benconnor1972/BODAQS/docs/analysis/contracts/BODAQS_Session_Filter_Contract_v0_draft.md

# BODAQS Session Filter Contract v0 Draft

**Status:** Draft  
**Scope:** Persisted reusable filters for selecting candidate sessions from a
BODAQS libraries root  
**Audience:** BODAQS web application, Library API service, notebook/library
adapter implementers

---

## 1. Purpose

A persisted session filter is a named reusable helper for finding candidate
sessions. It describes a predicate over session catalog fields, signal metadata,
and later derived summaries or API-backed indexes.

Persisted filters are **not** Study Set definitions. Applying a filter changes
which sessions are visible or selectable. Adding sessions to a Study Set still
writes explicit session references.

Persisted filters are also not `bodaqs.scenario` definitions. A Scenario finds
meaningful occurrences, called Episodes, within sessions using time- or
distance-domain criteria. A session filter may define the candidate scope for
a Scenario evaluation, but it does not carry Episode criteria or results.

Ad-hoc table filters are also outside this contract. They are transient UI state
owned by the Session Selector table headers. They may combine with persisted
filters during browsing, but they are not saved as `bodaqs.session_filter`
objects unless the user explicitly saves or copies them into a persisted filter.

---

## 2. Resource Scope

Persisted filters are root-level application objects.

Canonical location:

```text
<libraries_root>/
  session_filters/
    <filter_id>.json
```

Filters are scoped to the configured libraries root, not to an individual
processed library. A filter may optionally restrict its own applicability through
`scope`, but the file still lives at the root.

---

## 3. Filter Object

Example:

```json
{
  "schema": "bodaqs.session_filter",
  "version": 1,
  "filter_id": "ben-rides-with-usable-gps",
  "revision": 2,
  "display_name": "Ben rides with usable GPS",
  "description": "Reusable helper for GPS comparison sessions.",
  "category": "gps",
  "scope": {
    "library_ids": ["default-library"]
  },
  "predicate": {
    "op": "and",
    "children": [
      {
        "field": "rider",
        "op": "contains",
        "value": "ben"
      },
      {
        "field": "gps.quality",
        "op": "eq",
        "value": "usable"
      }
    ]
  },
  "provenance": {
    "created_at": "2026-06-02T00:00:00Z",
    "created_by": "user",
    "updated_at": "2026-06-02T00:12:00Z"
  },
  "display_state": {
    "bodaqs_web_v1": {}
  }
}
```

Validation notes:

- `schema` must be `bodaqs.session_filter`.
- `version` must be supported by the service.
- `filter_id` must be filename-safe and unique within the libraries root.
- `revision` is assigned by the service and must increment on successful write.
- `display_name` should be short enough for chips and filter-list rows.
- `category` is optional display grouping metadata for UIs. Missing category
  means `custom`.
- `predicate` is required.
- `scope` is optional. Missing scope means the filter can be evaluated against
  all libraries under the active libraries root.
- `display_state` is optional and non-authoritative.

---

## 4. Predicate Model

Predicates are recursive. Group predicates combine child predicates. Leaf
predicates compare one field against one value or set of values.

Group predicate:

```json
{
  "op": "and",
  "children": []
}
```

Recommended group operators:

```text
and | or
```

Leaf predicate:

```json
{
  "field": "gps.quality",
  "op": "eq",
  "value": "usable"
}
```

Recommended leaf operators:

```text
eq | in | contains | present
```

Operator semantics:

- `eq`: field value equals `value` after normalisation appropriate to the field.
- `in`: field value equals any item in `value`.
- `contains`: text or list field contains `value`.
- `present`: field has a non-empty value, or equals the boolean `value` if one
  is supplied.

The service and browser should treat unknown fields/operators as invalid for
saved objects. Future versions may add numeric comparison, date/time comparison,
trackpoint-match predicates, and signal-content predicates.

---

## 5. Initial Field Names

Initial catalog-backed fields:

```text
bike
event.schema
firmware
gps.present
gps.quality
gps.source
note.status
preprocessing.profile
qc.level
rider
signals
source.archive
```

Field notes:

- `note.status` uses `missing | draft | edited`.
- `qc.level` uses `ok | warning | alert`.
- `gps.quality` uses `absent | limited | usable | invalid`.
- `gps.source` may match the preferred GPS source, any source kind, or source
  stream names exposed by the catalog.
- `signals` evaluates over available signal names and semantic labels.

Signal-summary predicates that classify a whole session are not part of the
initial catalog-only implementation. Conditions intended to identify
occurrences within a session belong to the Scenario and Episode contract rather
than becoming session-filter predicates.

---

## 6. API-Backed Trackpoint Predicates

Trackpoint predicates are planned API-backed filter predicates. They should not
be evaluated directly from the session catalog because they depend on a track,
track revision, geospatial policy, tolerance, GPS source identity, and matching
algorithm version.

Recommended predicate shape:

```json
{
  "field": "trackpoint.crossing",
  "op": "matches",
  "value": {
    "track_id": "munda-biddi-test-loop",
    "trackpoint_ids": ["start-gate", "rock-garden-entry"],
    "match_mode": "all",
    "tolerance_m": 5.0,
    "policy_ref": {
      "policy_id": "default-geospatial-policy"
    }
  }
}
```

Recommended `match_mode` values:

```text
any | all | min_count
```

If `match_mode` is `min_count`, `value.min_count` is required.

The browser should evaluate this predicate by creating or resuming a
`TrackpointMatchQuery` through the Library API. The API may use the filter's
own `scope`, the active selected-library scope, and/or other already-applied
catalog-backed filters to reduce candidate sessions before starting broad
geospatial matching.

The result of a trackpoint predicate is a set of matched session references. It
then participates in the active filter stack like any other saved filter. A
Study Set created from the result still stores explicit session membership; the
trackpoint predicate may appear only in Study Set provenance unless a future
explicit refresh action is added.

---

## 7. Applying Filters

The default filter stack behavior is:

```text
selected libraries
-> persisted saved-filter stack
-> ad-hoc table filters
-> search text
-> sort
```

Multiple applied persisted filters are combined with `AND` by default. Each
persisted filter may contain its own internal `and`/`or` predicate tree.

Example active stack:

```json
{
  "applied_filters": [
    { "filter_id": "ben-rides" },
    { "filter_id": "has-accelerometer" },
    { "filter_id": "has-usable-gps" }
  ],
  "combine": "and"
}
```

The active stack is UI/session state. It is not a Study Set definition. If the
user creates a Study Set after applying filters, the Study Set stores explicit
session membership. The filter stack may be recorded in Study Set provenance,
but refreshing membership from filters must be an explicit user action.

---

## 7. API Endpoints

Root-scoped session-filter CRUD:

```text
GET    /api/v1/session-filters
POST   /api/v1/session-filters
GET    /api/v1/session-filters/{filter_id}
PUT    /api/v1/session-filters/{filter_id}
DELETE /api/v1/session-filters/{filter_id}
```

Filter writes should use revision checks:

```json
{
  "expected_revision": 2,
  "session_filter": {
    "schema": "bodaqs.session_filter",
    "version": 1,
    "filter_id": "ben-rides",
    "revision": 2,
    "display_name": "Ben's rides",
    "predicate": {
      "field": "rider",
      "op": "contains",
      "value": "ben"
    }
  }
}
```

The browser may evaluate catalog-backed filters locally after loading filter
objects. API-backed evaluation can be added later for predicates requiring data
that is not present in the session catalog.

---

## 8. Implementation Sequence For Trackpoint Filters

Recommended first implementation sequence:

1. Extend the frontend filter model to recognise `trackpoint.crossing` /
   `matches` predicates.
2. Add a simple filter-builder UI for choosing track, trackpoints, `match_mode`,
   and tolerance.
3. When a trackpoint filter is applied, ask the Library API to create or resume
   a `TrackpointMatchQuery`.
4. Poll query status and apply the paged matched session refs to the visible
   session set as results arrive.
5. Cache the query id and progress in browser state so the UI can show
   "building index", "partially available", and "complete" states.
6. Keep authoring/persistence of the filter separate from execution/progress of
   any particular query job.

---

## 9. Deferred Work

Deferred beyond the first persisted-filter contract:

- full visual predicate builder
- ad-hoc table-header filtering
- saving an ad-hoc table filter as a persisted filter
- API-backed whole-session signal-summary predicates
- richer API-backed geospatial-section predicates beyond trackpoint crossings
- importing/exporting filters across libraries roots
- hosted/shared filter permissions
