benconnor1972/BODAQS/docs/analysis/contracts/BODAQS_Minimum_Signal_Registry_Semantics_v0_1_1.md

# BODAQS — Minimum Signal Registry Semantics (v0.12 draft)

This document defines the **minimum required semantics** for `session["meta"]["signals"]` so that downstream code (event detection, segment extraction, metrics, and visualization) can resolve schema “signals/roles” (e.g. `disp`, `vel`, `acc`) to concrete dataframe columns **without relying on column-name string hacks**.

It is intentionally **minimal**: it does not require full provenance graphs or transform metadata, but it *does* require enough structure to make resolution deterministic and contract-valid.

---

## 1) Scope

Applies to any analysis `Session` object that carries a `pandas.DataFrame` in `session["df"]`.

Downstream components that assume this registry:

- `detect_events_from_schema(..., meta=session["meta"])`
- `extract_segments(..., meta=session["meta"])`
- metrics and viz tooling that use SegmentBundle outputs

---

## 2) Registry shape

`session["meta"]["signals"]` MUST be a mapping:

```text
{ <df_column_name: str> : <SignalInfo: dict> }
```

Where `<df_column_name>` **must be exactly the column name** present in `session["df"].columns`.

### 2.1 Stream scope

The primary registry above has an implicit stream scope of `"primary"`.
Each materialised secondary stream has an independent registry at
`session["meta"]["secondary_streams"][<stream_name>]["signals"]`, keyed by
columns in that stream's dataframe. A selectable signal reference is therefore
the pair:

```json
{ "stream_name": "inertial_frame_imu", "column": "yaw_enu_rad" }
```

`column` alone is not a session-global identity. Consumers that cross a stream
boundary MUST retain the stream name, and MUST resolve semantics only within
the referenced stream registry.

`stream_name` describes materialisation, timebase, and product boundary. It
does **not** express whether a signal is the preferred analysis candidate.
In particular, a `primary_analysis` signal may live in any stream, including a
fused or native-rate secondary stream. Conversely, a primary-stream signal is
not automatically a primary analysis signal.

---

## 3) Required coverage

### 3.1 One entry per numeric column

For every **numeric** column in `session["df"]` (excluding timebase columns like `time_s` and other explicitly non-signal fields), there MUST be a corresponding entry in `session["meta"]["signals"]`.

### 3.2 No extraneous entries (recommended)

It is strongly recommended that the registry does not include keys that are not present in `session["df"].columns`.

---

## 4) SignalInfo minimum fields

Each `SignalInfo` MUST contain the following keys:

- `kind`: `"" | "raw" | "qc"`
  - `""` means engineered/derived default signals.
  - `"raw"` means raw sensor/ADC domain.
  - `"qc"` means quality-control / flags.

- `unit`: `str | None`
  - For `kind == ""`, **unit MUST be non-empty** (e.g. `"mm"`, `"mm/s"`, `"V"`).
  - For `kind == "raw"`, unit SHOULD be `"counts"` (or another documented raw unit).
  - For `kind == "qc"`, unit SHOULD be `None`.
  - Dimensionless derived signals (e.g. normalised displacement) MUST use unit `"1"`.

- `domain`: `str | None`
  - Optional, but **highly recommended** when the same physical quantity can describe different physical or analysis subjects.
  - It identifies what part or system the signal characterises; it does **not** identify the coordinate basis of vector components.
  - Examples: `"suspension"`, `"wheel"`, `"unsprung"`, `"frame"`, `"steering"`, `"world"`.

- `end`: `"front" | "rear" | None`
  - Optional, but **highly recommended** for front/rear bike signals.
  - Use this to distinguish front and rear suspension or wheel signals without
    relying on logger-specific sensor identifiers.

- `op_chain`: `list[str]`
  - List of analysis-side operation tokens applied to produce this column (possibly empty).
  - Examples: `["zeroed"]`, `["zeroed", "norm"]`, `["zeroed", "Butterworth_3Hz_4Order"]`, `["zeroed", "diff"]`.
  - Primary analysis motion channels should keep full provenance here rather
    than in their dataframe column names.

Residual naming note:
- Columns ending with `_op_Butterworth_<x>Hz_<y>Order_resid` are interpreted as residual outputs.
- Their registry `op_chain` should include `diff` and should not include `Butterworth_<x>Hz_<y>Order`.

### Optional but recommended keys

- `source`: `list[str]`
  - Parent column name(s) this column derives from (especially for `_op_*` or derived velocity/acceleration channels).

- `source_columns`: `list[str]`
  - Alias used by some generators for parent column names. Consumers should
    prefer `source` when both are present, but may accept either.

- `processing_role`: `str`
  - Selection intent assigned by preprocessing; it is independent of
    `stream_name`, `sensor`, and `kind`.
  - Controlled values are defined in **4.1 Analysis role and inspection
    visibility** below.
  - Use this when a session contains multiple valid semantic matches for the
    same physical quantity, such as a forward estimate and a fixed-interval
    smoothed estimate of world yaw.

- `motion_source_id`: `str`
  - Identifier of the `motion_derivation.sources[]` entry that produced this
    signal.

- `motion_profile_id`: `str`
  - Identifier of the motion-derivation profile that produced this signal.
  - The primary profile should use `"primary"`; secondary profiles should use
    their configured `id`.

- `derivation`: `dict`
  - Structured provenance describing how the signal was generated. For
    motion-derived channels this should include the source column, displacement
    low-pass settings, S-G materialized window settings, and final derivative
    low-pass settings.

- `origin`: `str`
  - Broad producer of the signal metadata or values. Current values include
    `"logger"` for signals supplied by log metadata and `"analysis"` for
    analysis-generated signals.

- `semantic_selection_excluded`: `bool`
  - When true, semantic selectors should ignore this signal even though it
    remains in the dataframe and registry for inspection.
  - This is used when `prefer_postprocessing_transformations` allows an
    analysis-generated signal to supersede a logger-originated signal with
    equivalent semantics.

- `semantic_selection_exclusion_reason`: `str`
  - Human-readable/provenance reason explaining why a signal was excluded from
    semantic selector matching.

- `inspection_visibility`: `"standard" | "advanced" | "diagnostic"`
  - Controls default interactive discovery only; it MUST NOT change semantic
    resolution or the availability of a signal explicitly requested by its
    concrete `{stream_name, column}` reference.
  - `"standard"` is intended for an ordinary Signal Inspector signal set.
    `"advanced"` is an inspectable alternative or specialist product.
    `"diagnostic"` requires an explicit user opt-in, such as a raw-evidence or
    diagnostics signal set.
  - In the absence of an explicit value, consumers SHOULD derive the default
    tier as defined in 4.1.

- `analysis_variant`: `str | None`
  - Stable, machine-readable distinction between otherwise equivalent analysis
    products. Examples include `"forward_estimate"`,
    `"fixed_interval_smoothed"`, `"filtered"`, and
    `"bias_compensated"`.
  - When two inspectable signals share the same sensor and core semantic
    fields, they SHOULD supply a distinct `analysis_variant` and/or
    `display_name`.

- `display_name`: `str | None`
  - Human-readable name for discovery and visualisation. It should distinguish
    simultaneously inspectable variants; for example, `"World yaw — smoothed"`
    and `"World yaw — forward estimate"`.

  - A vector-component name SHOULD include a frame-appropriate direction while
    retaining `quantity` and `component` as separate machine semantics:
    `sensor_native` uses `Sensor X/Y/Z`; a main-frame `body_local` or
    `bike_body` vector uses `Forward/Left/Up`; and `world_enu` uses
    `East/North/Up`. An articulated assembly's `body_local` vector uses
    `Local X/Y/Z` unless a more specific frame convention is documented.

- `sensor`: `str | None`
  - Logger/source sensor identifier, if supplied by log metadata.
  - This is not an analysis selector field. For front/rear bike-location
    matching, use `end` plus `domain`, `quantity`, and `unit`.

- `component`: `str | None`
  - Vector component represented by the column, normally `"x"`, `"y"`, or `"z"`.
  - Vector consumers should use this field rather than infer axes from column names.

- `coordinate_frame`: `str | None`
  - Coordinate basis in which a vector component is currently expressed.
  - Canonical IMU values are `"sensor_native"`, `"body_local"`, `"bike_body"`, and `"world_enu"`.
  - This describes the stored or derived values; it does not instruct firmware to perform a transform.

- `vector_group`: `str | None`
  - Sensor-local identifier tying components of one vector quantity together, such as `"accel_raw"` or `"gyro_raw"`.
  - The complete group identity is `sensor` plus `vector_group`.

- `mount_point`: `str | None`
  - Optional descriptive sensor-installation detail such as `"brake_caliper"`.
  - It is not a primary semantic selector unless a future contract explicitly promotes a controlled vocabulary.

- `notes`: `str`
  - Free text diagnostics or hints.

### 4.1 Analysis role and inspection visibility

`processing_role` ranks otherwise valid semantic candidates. It does not
describe dataframe placement, sensor priority, or whether a signal is raw.
New writers SHOULD use one of these controlled values:

| processing_role | Meaning | Default inspection tier |
|---|---|---|
| `primary_analysis` | The recommended standard analysis series for its selector context. There SHOULD be no more than one preferred candidate for a deterministic selector context. | `standard` |
| `secondary_analysis` | A valid alternative analysis series: another method, smoothing treatment, source, or interpretation that is not the normal default. | `advanced` |
| `diagnostic` | An inspectable intermediate engineering product that is not intended for ordinary semantic binding. | `diagnostic` |
| `qc_metric` | Quality/status/evidence used to assess data or processing confidence, not an ordinary engineering input. | `diagnostic` |

`kind` retains its independent meaning:

- `kind="raw"` and `kind="qc"` MUST default to `inspection_visibility="diagnostic"`
  unless a future contract explicitly establishes a justified exception.
- Raw and QC signals remain available for explicit inspection. They are not
  deleted, and their diagnostic visibility does not imply
  `semantic_selection_excluded`.
- Engineered signals without a recognised `processing_role` SHOULD default to
  `advanced`, not `standard`, so that unclassified products do not silently
  expand the normal user-facing list.

`semantic_selection_excluded` is a semantic resolver safety flag, not a UI
visibility flag. An explicitly configured engineering or diagnostic view MAY
show such a signal; automatic semantic resolution MUST continue to exclude it
unless the requesting workflow explicitly requires it.

---

## 5) Compatibility with naming spec (v0.2)

This minimum registry is compatible with the column grammar in **Signal naming & units spec (v0.2)**:

- `kind`, `domain`, `unit`, and `op_chain` should be directly parseable from the column name when the name is canonical.
- Primary motion-derived column names may intentionally omit operation tokens,
  for example `rear_wheel_disp_dom_wheel [mm]`; the registry remains the source
  of filter provenance via `op_chain` and `derivation`.
- The registry is still required even if names are canonical, because the registry is the **API surface** used by resolution logic.

---

## 6) Resolution expectations (for Option 1)

When resolving schema roles (e.g. `disp`, `vel`, `acc`) to columns, downstream code SHOULD use the registry to:

1. Filter candidates by `kind` (usually engineered `""`),
2. Filter by `unit`, `domain`, and `end` as required by the schema,
3. For vector roles, filter by `coordinate_frame`, `vector_group`, and `component` rather than parsing column names,
4. Prefer a requested `processing_role` when supplied, especially
   `"primary_analysis"` for standard metrics/event detection,
5. Prefer “cleaner” stages using `op_chain` when no explicit role is supplied
   (policy-defined ranking),
6. Fall back deterministically and emit actionable diagnostics if no match exists.

Stream scope MUST NOT be used as an implicit preference in this process. A
workflow that needs a particular stream must request it explicitly; otherwise
candidate preference comes from semantic fields, `processing_role`, and its
declared resolution policy. `inspection_visibility` affects discovery UI only
and MUST NOT alter semantic resolution.

### IMU mounting-domain convention

For bike-mounted IMUs, use these signal-level `domain` and `end` combinations:

| domain | permitted end | meaning |
|---|---|---|
| `unsprung` | `front`, `rear` | Assembly moving predominantly with the corresponding axle |
| `frame` | `front`, `rear`, `None` | Main sprung frame; end is a coarse mounting region |
| `steering` | `front` | Sprung assembly rotating about the steering axis |

Firmware raw accelerometer and gyroscope columns use `coordinate_frame=sensor_native`. The static installation transform is recorded separately as `sensor_native -> body_local`. Post-processing may materialise `body_local`, `bike_body`, or `world_enu` signals and must record that derivation without replacing the raw evidence.

This document does **not** define the ranking policy; it defines the minimum metadata required for any reasonable policy to operate.

---

## 7) Logger GPS semantics

Logger GPS route construction resolves `meta["signals"]` only. It must not
infer signal meaning from dataframe column names: `speed` and
`speed_accuracy`, or `course_over_ground` and `course_accuracy`, are distinct
registry quantities even when their logger labels are similar.

For one coherent logger GPS source, register at least:

- `position_latitude` and `position_longitude` with `domain="world"`;
- `speed` with `unit="m/s"`;
- `course_over_ground` with `unit="deg"`; and
- when yaw correction is required, QC `speed_accuracy` and `course_accuracy`
  fields with their respective units.

Use `sensor` plus a stable source-group identifier when available to keep the
position, motion, and QC fields from one receiver together. `source` remains
parent/provenance metadata and must not be used as the source-group identity.
GPS QC fields may be marked `semantic_selection_excluded` for generic signal
selection, but route construction may explicitly resolve them as required QC
evidence. Earlier BODAQS registries using `quantity="heading"` for a logger
GPS course are accepted as a migration alias only; new firmware emits
`course_over_ground`.

---

## 8) Validation checklist

A session is compliant with this minimum registry if:

- `session["meta"]["signals"]` exists and is a dict
- Every numeric df column has a registry entry keyed by the exact column name
- Every entry has keys: `kind`, `unit`, `domain`, `op_chain`
- `kind == ""` entries have a non-empty `unit`
- `op_chain` is a list (possibly empty)
- where present, `processing_role` uses a controlled value from 4.1 or a
  documented extension
- `kind="raw"` and `kind="qc"` default to diagnostic inspection visibility
  when no explicit policy is recorded
- every selectable secondary stream has a stream-local registry keyed by its
  exact dataframe columns; and
- cross-stream consumers identify a selected signal by `stream_name` and
  `column`.

---

## 9) Implementation notes

- If you have both (a) a canonical naming parser and (b) legacy “best effort” heuristics, you may build the registry in **permissive mode** early, then run a later **standardization** pass that renames legacy columns and rebuilds/validates the registry in strict mode.
- Avoid overwriting a high-fidelity registry with a “minimal” one late in the pipeline; that can silently discard semantics needed by event/segment resolution.
