benconnor1972/BODAQS/bodocs/src/assets/pics/buy-pcb-or-kit/coming-soon.png

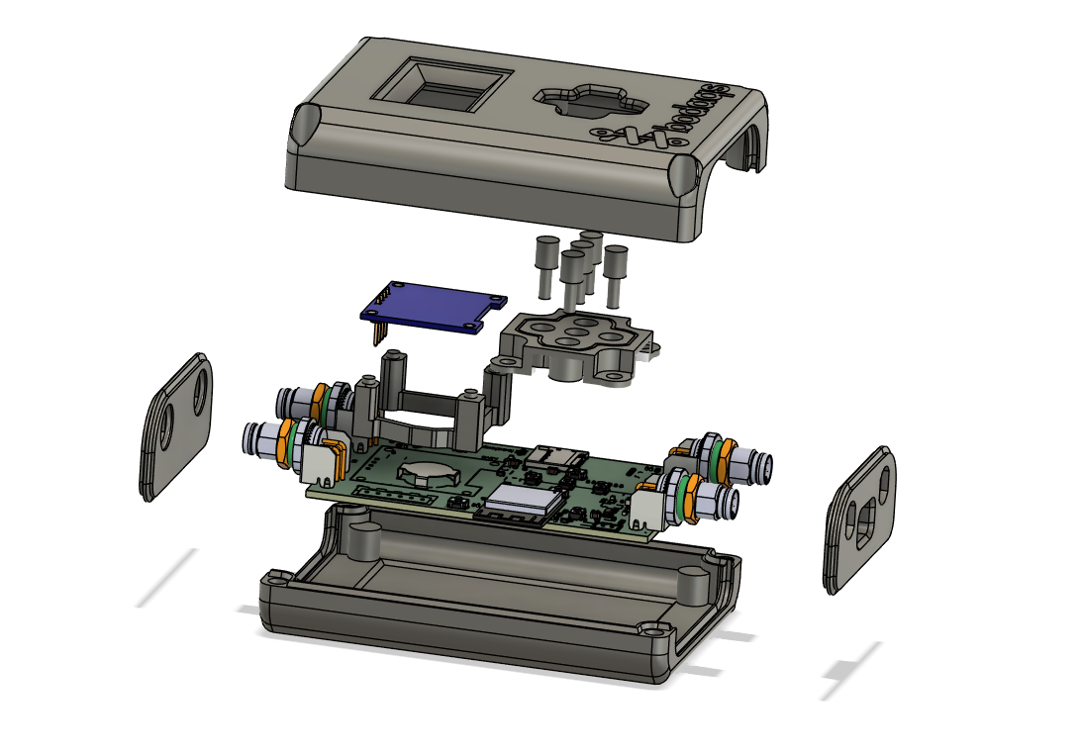
bodocs/src/assets/pics/buy-pcb-or-kit/coming-soon.png
