benconnor1972/BODAQS/bodocs/src/assets/pics/buy-pcb-or-kit/full-kit.png

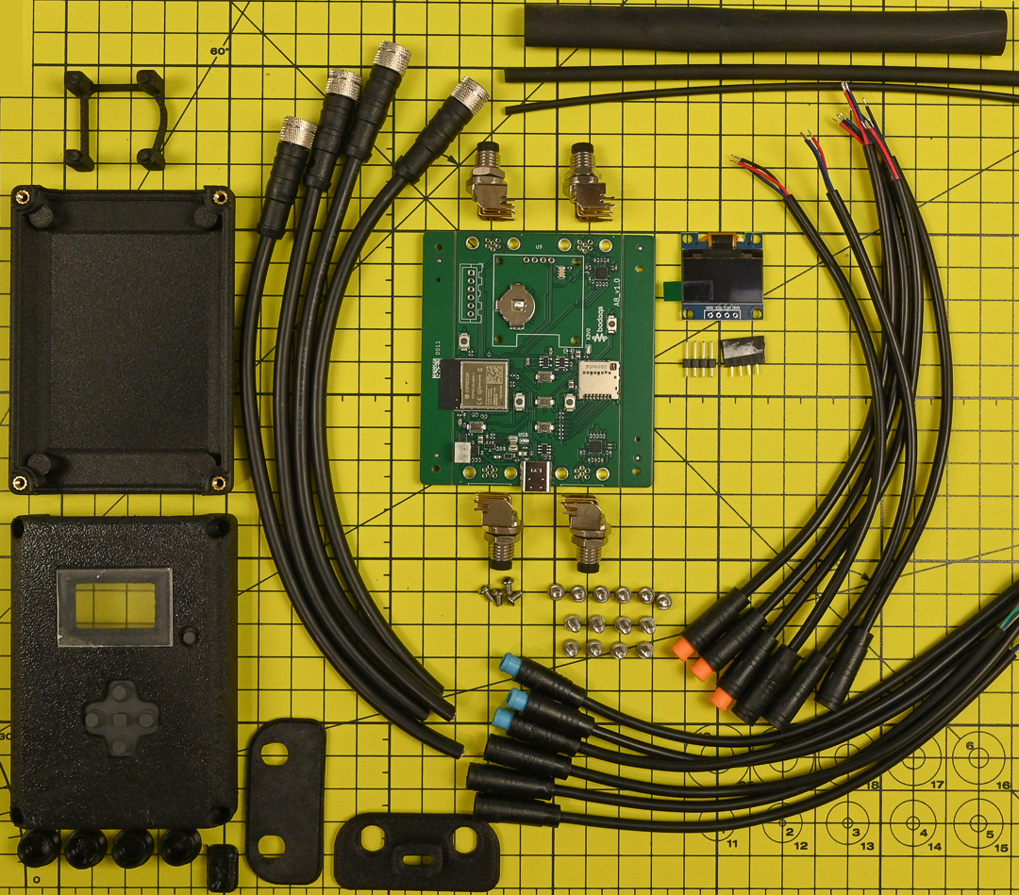
bodocs/src/assets/pics/buy-pcb-or-kit/full-kit.png
