benconnor1972/BODAQS/bodocs/src/assets/pics/Connector-overview.png

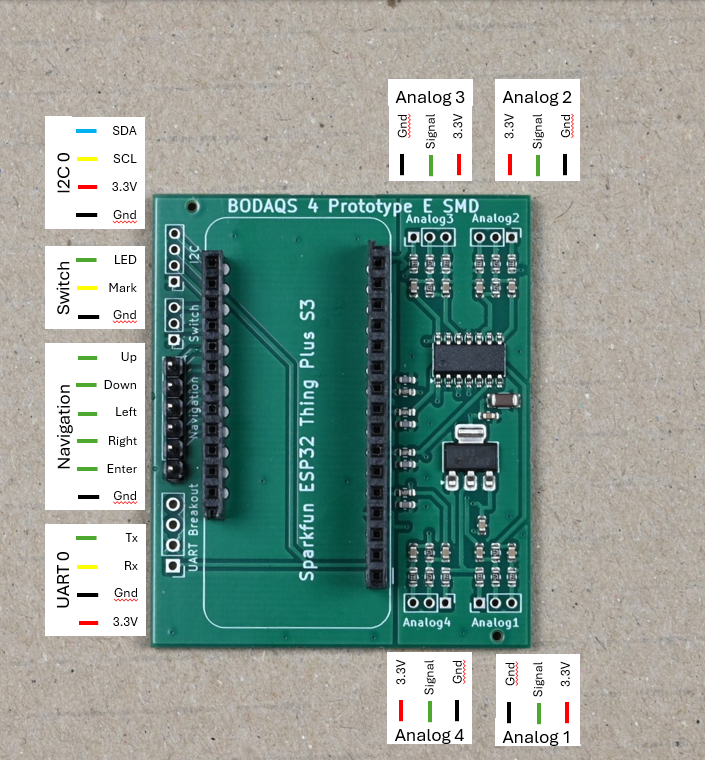
bodocs/src/assets/pics/Connector-overview.png
