benconnor1972/BODAQS/bodocs/src/assets/pics/Idle.png

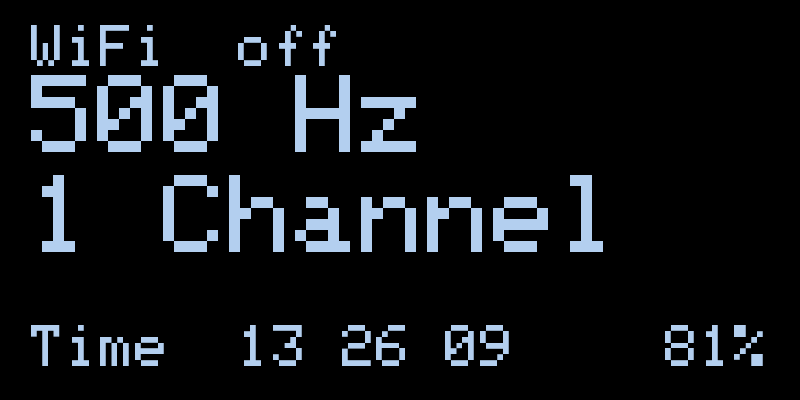
bodocs/src/assets/pics/Idle.png
