benconnor1972/BODAQS/bodocs/src/assets/pics/logger-build-guide/connector-overview-F.png

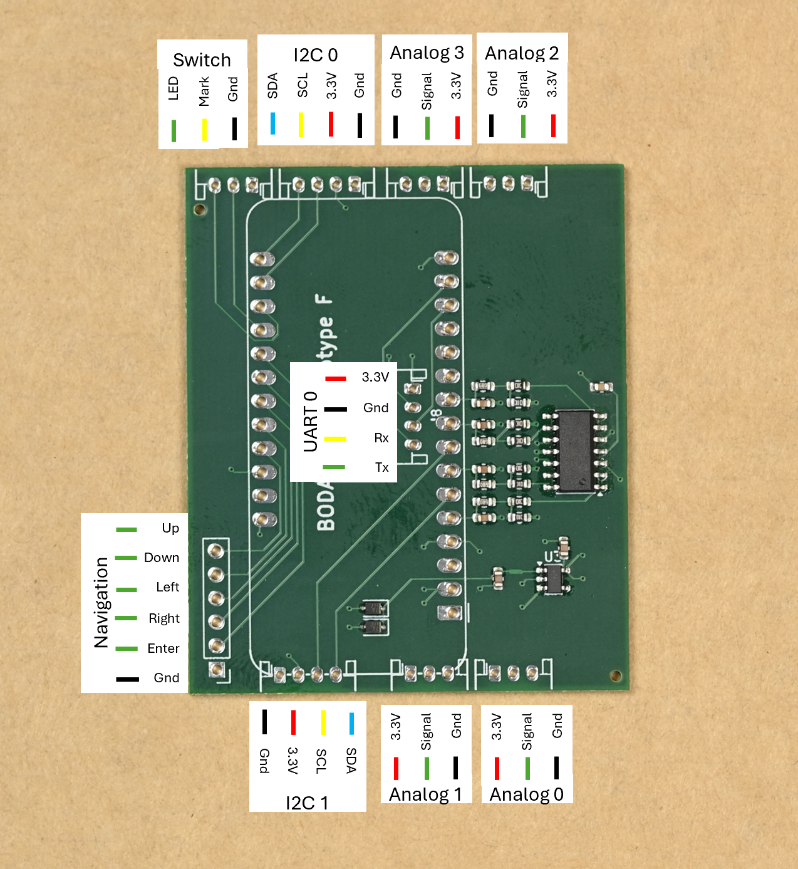
bodocs/src/assets/pics/logger-build-guide/connector-overview-F.png
