benconnor1972/BODAQS/bodocs/src/assets/pics/logger-build-guide/hardware_2a_a8.png

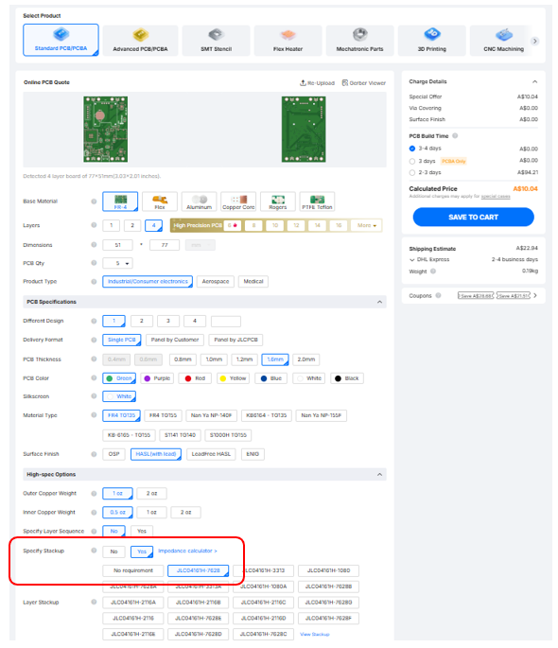
bodocs/src/assets/pics/logger-build-guide/hardware_2a_a8.png
