benconnor1972/BODAQS/bodocs/src/assets/pics/logger-build-guide/hardware_5.png

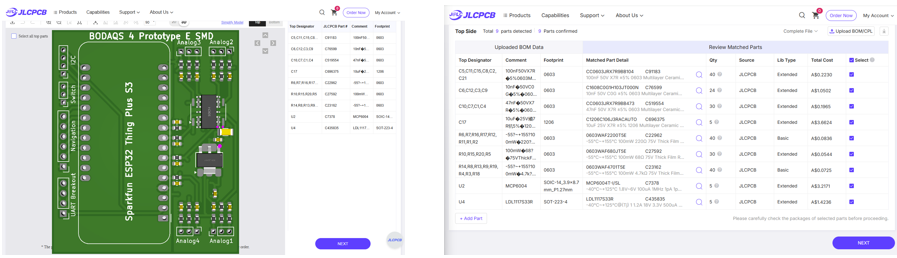
bodocs/src/assets/pics/logger-build-guide/hardware_5.png
