benconnor1972/BODAQS/bodocs/src/assets/pics/meet-the-logger/a8-logger-specs.png

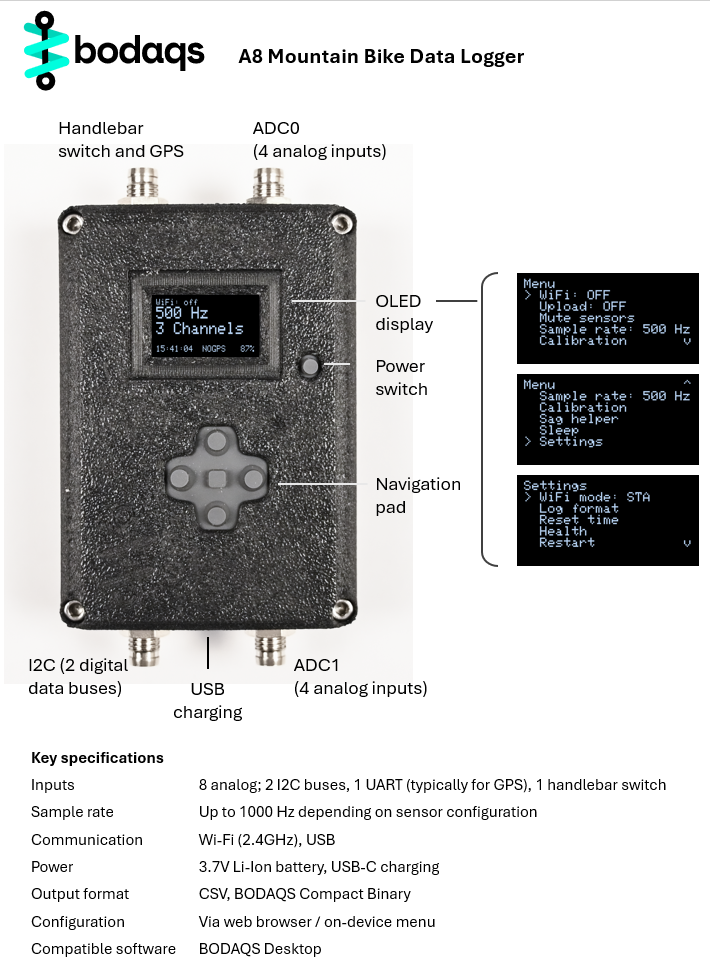
bodocs/src/assets/pics/meet-the-logger/a8-logger-specs.png
