benconnor1972/BODAQS/bodocs/src/assets/pics/mute.png

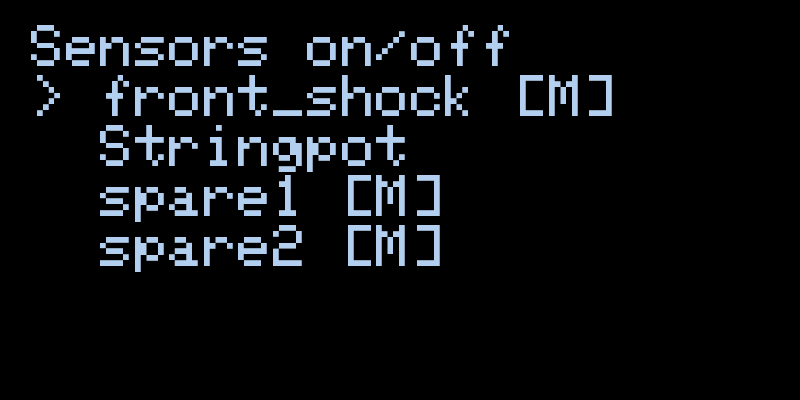
bodocs/src/assets/pics/mute.png
