benconnor1972/BODAQS/bodocs/src/assets/pics/OLED-1.jpg

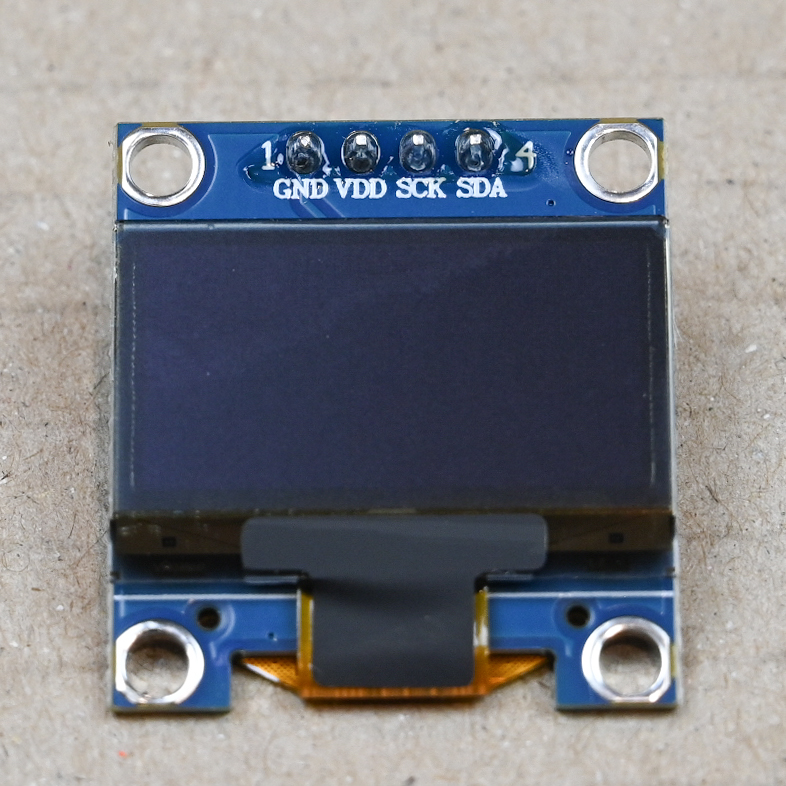
bodocs/src/assets/pics/OLED-1.jpg
