benconnor1972/BODAQS/bodocs/src/assets/pics/OLED-3.jpg

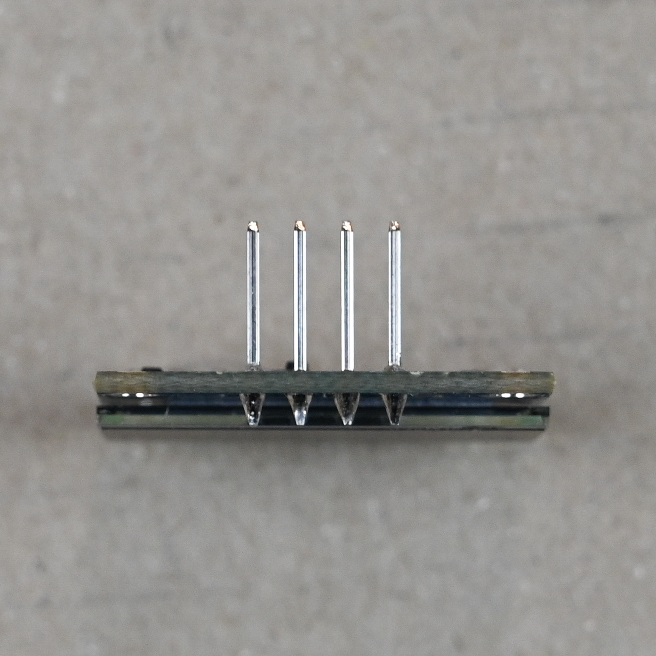
bodocs/src/assets/pics/OLED-3.jpg
