benconnor1972/BODAQS/bodocs/src/assets/pics/wifiip.png

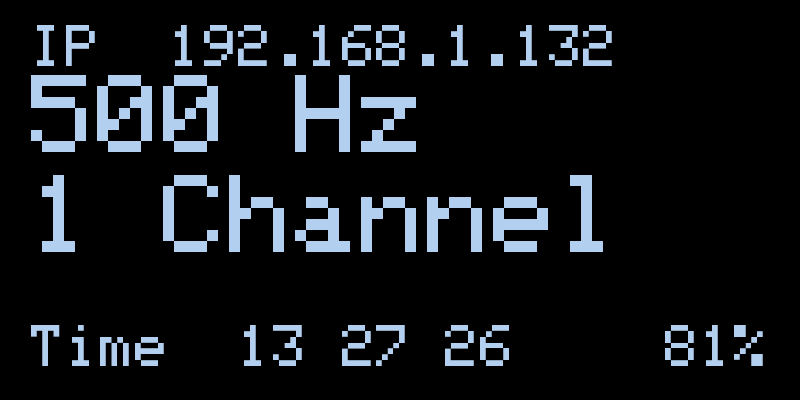
bodocs/src/assets/pics/wifiip.png
