benconnor1972/BODAQS/bodocs/src/content/docs/logger-build-guide/bodaqs-a8/sourcing-hardware.mdx

---
title: Sourcing hardware
description: Full parts list for building the BODAQS A8 v1.0 logger.
sidebar:
  order: 1
---

import {Aside, Badge} from '@astrojs/starlight/components';
import Lede from '@components/Lede.astro';
import Lightbox from '@components/Lightbox.astro';
import Flag from '@components/Flag.astro';

<Lede>
You will need to source a range of parts to build your BODAQS data logger.
A small selection of common tools is also required.
</Lede>

<Aside type={"caution"} title="These materials are for the BODAQS A8 logger"  icon="seti:config">
    The following materials work for the BODAQS A8 logger, currently version 1.0. If you are building the Prototype F logger, start [here](/logger-build-guide/prototype-f/sourcing-hardware/)
</Aside>

A complete Bill of Materials, including links, is at the [end of this section](/logger-build-guide/bodaqs-a8/sourcing-hardware/#bill-of-materials). If you prefer, you can get the Bill of Materials as an [Excel spreadsheet](https://github.com/benconnor1972/BODAQS/tree/main/Bill%20of%20Materials/bodaqs-a8)

You can buy a PCB or kit directly from [BODAQS.net](/buy-pcb-or-kit/) 

## Printed circuit board
The printed circuit board (PCB) is custom-designed for this project. It is obtained by ordering it from a PCB fabricator. You can also get it from me.

#### Obtaining the PCB fabrication files

Go to the 'releases' page in the BODAQS github repository [here](https://github.com/benconnor1972/BODAQS/tree/main/hardware/bodaqs-a8/v1_0/fab) and download the latest PCB fabrication package. The package contains all the files you need to order an assembled PCB from JLCPCB.

#### Ordering PCBs on JLCPCB

<Flag src="/src/assets/pics/logger-build-guide/hardware_1.png" alt="hardware_1">
First, [create an account](https://passport.jlcpcb.com/#/login) at JLCPCB (or log in if you already have an account). Then Select 'order now' from the top right of the [home screen](https://jlcpcb.com).
</Flag>

<Flag src="/src/assets/pics/logger-build-guide/hardware_2.png" alt="hardware_2">
Select "Add gerber file" and navigate to the *.zip file in the fabrication files package. When the file has uploaded, a picture of the PCB should appear in the box.
</Flag>

<Flag src="/src/assets/pics/logger-build-guide/hardware_2a_a8.png" alt="hardware_2a">
In the 'High-spec Options' section below the PCB picture, set 'Specify Stackup' to 'Yes' and then select 'JLC04161H-7628' from the list of available layer stackups.
</Flag>

<Flag src="/src/assets/pics/logger-build-guide/hardware_3_a8.png" alt="hardware_3">
Scroll down to the bottom of the page, leaving the other settings unchanged. Click the 'PCB Assembly' slider ON. A set of new options should appear below. Set 'PCBA Type' to 'Standard' and leave the other options unchanged. Click 'next'.

A picture of the PCB should appear. Click 'next'.
</Flag>

<Flag src="/src/assets/pics/logger-build-guide/hardware_4_a8.png" alt="hardware_4">
Select "Add BOM file" and navigate to the *-BOM.csv file in the fabrication files package. Select "Add CPL file" and navigate to the *-all-pos.csv file in the fabrication files package. Click 'process BOM and CPL'.
</Flag>

<Flag src="/src/assets/pics/logger-build-guide/hardware_5_a8.png" alt="hardware_5">
You will be presented with the Bill of Materials and Component Placements. **Make sure that all the checkboxes in the Bill of Materials 'Select' column are checked before proceeding.** Click 'next', and again on the placements page.
</Flag>

<Aside type={"note"} title="Out of stock parts"  icon="seti:config">
If a component's checkbox is not selected in the Bill of Materials, it is usually because the part is out of stock. If the part is a resistor or capacitor (designators beginning 'C' or 'R'), you can search for alternative parts and accept any in-stick parts JLCPCB offers. For other parts, don't make substitutions unless (1) you are completely sure you know what you are doing, or (2) you talk to me first.
</Aside> 

<Flag src="/src/assets/pics/logger-build-guide/hardware_6_a8.png" alt="hardware_6">
Review the quote and select an appropriate product description (this is needed for shipping paperwork). Research/Education/DIY/Entertainment => DIY hobby circuit board is a good option. Select 'save to cart'.

Select 'secure checkout' and complete checkout details.

</Flag>

<Aside type="tip" title="Minimum order quantities">
Minimum order quantity for custom PCBs (from JLCPCB) is 5, which is more data loggers than most people need. With the A8 design, all the hardware is baked into the design *unlike the Prototype F, which uses a plug-in development board). That makes ordering 5 a little pricy.

If you dont want the cost of 5 PCBs, consider pooling with your friend or buying a PCB or kit from me. Buying stuff from me is going to be more expensive on a per-unit basis, because my time is valuable too, but it could make getting the parts you need a lot simpler. 
</Aside>

## Electronic parts

#### 0.96” OLED display
<Flag  src="/src/assets/pics/logger-build-guide/OLED.png" alt="OLED pic">
  These displays, based on an SSD1306 driver chip, are a commodity item and many vendors sell functionally equivalent versions. They do vary slightly in the physical dimensions of the board however, and some versions may require minor case modifications to install. The case is designed around a HS96L03W2C03 module, like [this one](https://www.aliexpress.com/item/1005007228213109.html) but if the description says HS96L03W2C03, you should be good to go. Lots of other similar modules can work too - if you buy something different, don’t worry – it can probably be installed with only minor modifications.
</Flag>

#### Nintendo 2DS replacement button pads
<Flag src="/src/assets/pics/logger-build-guide/2ds-keypad.png" alt="keypad ">
  This is another commodity item available from many vendors on AliExpress, Amazon and Ebay, like [this one](https://www.aliexpress.com/item/1005009646292735.html). Note that the case design **specifically requires 2DS parts** - other controller parts won't fit. Search for “button pad 2ds”.
</Flag>

#### Li-ion battery
<Flag src={"/src/assets/pics/logger-build-guide/battery-a8.png"} alt="battery">
  The BODAQS A8 uses a 3.7V Li-ion polymer battery pack with JST-PH 2 pin connector. Li-ion polymer batteries are widely available from a variety of sources. For our purposes, all are equally good. However, make sure that:
    - The battery's maximum dimensions are 65mm x 55mm x 7mm
    - The battery’s capacity exceeds about 1000mAh
    - The battery comes with a 2-wire JST-PH connector. Some batteries are sold with JST-XH or SM-2P connectors, which are not the same and will not fit.
	
Some sources for suitable batteries:
- In Australia, [Altronics](https://www.altronics.com.au/p/s4725-3.7v-2000mah-polymer-lithium-ion-battery-lipo/) have the exact battery I use.
- In the US, [Sparkfun](https://www.sparkfun.com/lithium-ion-battery-2ah.html) has one that looks the same.
- In the EU, [Kiwi Electronics](https://www.kiwi-electronics.com/en/lithium-polymer-li-po-battery-3-7v-1200mah-1045) looks like it should work. 
- And of course, AliExpress has numerous options, like this [model 524261](https://www.aliexpress.com/item/1005004841334328.html)
</Flag>

<Aside type={"caution"} title="Always check polarity before connecting">

  Not all battery connectors are wired with the same polarity. Check and double check that the positive and negative leads from your battery are correctly oriented. If they are not oriented as shown, gently lift the tabs on the plastic connector housing with a needle or the edge of a craft knife, withdraw the leads and re-install them in the correct positions. If the leads are not color-coded, then test the cell with a multi-meter to determine positive and negative.

  <Lightbox thumbnailWidth={400} src={"/src/assets/pics/logger-build-guide/correct_polarity.png"} alt="battery polarity example showing correct and incorrect polarity"/>

  **Do not connect a battery with the incorrect or unknown polarity as it will probably damage the development board.**
</Aside>

#### Header socket
<Flag src="/src/assets/pics/logger-build-guide/header-socket.png" alt="header socket ">
  Header sockets are standard electronic parts for making plug-in connections to a PCB. This one connects the OLED display and needs 4 sockets in 1 row, 8.5mm high and 2.54mm pitch. Longer sockets can be cut to size. You should just add these to the order from wherever you get your battery or other electronic parts (links in the table above).
</Flag>

#### CR1220 button cell
<Flag src="/src/assets/pics/logger-build-guide/button-cell.png" alt="button cell ">
A button cell that powers the logger's real-time clock (RTC) when the battery is disconnected, allowing it to retain the time. These are available in hardware stores, pharmacies and supermarkets.
</Flag>

#### MicroSD card
<Flag src="/src/assets/pics/logger-build-guide/microsd.png" alt="microsd ">
You will need a MicroSD card to record log files and store the logger's configuration file. 16GB is sufficient - even a large log file is only a few tens of MB. Likewise, super high performance is not essential. Any modern name-brand MicroSD card should perform adequately.
</Flag>

### Connectors

The BODAQS A8 logger has 4 external connectors: two for analog inputs, one for I2C and one connector for a handlebar-mounted switch and GPS connection. All the connectors are identical 6-pin metal M8 circular connectors, Amphenol part number 
M8AS-06PMMR-SF8001. 

You can get original Amphenol connectors from [Digikey](https://www.digikey.com.au/en/products/detail/amphenol-ltw/M8AS-06PMMR-SF8001/7618863) or other major online electronics suppliers. 
You can get copies on AliExpress from various vendors, like [this one](https://www.aliexpress.com/item/1005008002251461.html)

<Lightbox src="/src/assets/pics/logger-build-guide/male_6_pin.png" alt="male 6 pin " />

<Aside type="tip" title="Name brand or generic?">
One of the advantages of M8 circular connectors is the availability of low-priced clones on AliExpress and similar marketplaces. These are generally fine, with one caveat: buy both the connector and the matching wire tail from the same vendor. There is some variation in pin diameter and the dimensions of the plastic inserts between the originals and the clones, and between different clones.
</Aside>

#### Plugs for the connectors.

<Flag src="/src/assets/pics/logger-build-guide/plugs_a8.png" alt="plugs">
It goes without saying that these need to match the connectors. It is easiest to buy plug assemblies with sealed wire tails and join you sensors on. The Amphenol plug assemblies I recommend are Amphenol 8A-06AFFM-SL7A01, available from [Digikey](https://www.digikey.com.au/en/products/detail/amphenol-ltw/8A-06AFFM-SL7A01/7616809). If you're going the AliExpress route, get them from whoever is supplying your connectors, and to match - or go elsewhere.
</Flag>

<Flag src="/src/assets/pics/logger-build-guide/plugs_ebike.png" alt="plugs">
For intermediate connections, I favour generic plastic M6 or M8 push-in connectors, sold on AliExpress (for example, [here](https://www.aliexpress.com/item/1005005939808200.html). They are low cost, compact, waterproof, and convenient when you want removable sensor sections or Y-connection branches.

Their weakness is that they do not lock by themselves. You should be careful that cable movement (from turning the handlebars, say) cannot pull them apart, and either duct tape them together or [use this 3d-printed lock].

Read the section on [Wiring and connector tips](/sensor-connection-and-wiring-guide/wiring-and-connector-tips/) before purchasing your plug assemblies. 
</Flag>

#### Shrink sleeve
<Flag src="/src/assets/pics/logger-build-guide/shrink.png" alt="shrink">
You will need shrink sleeve for covering soldered joints. Read the [wiring and connector tips section](/sensor-connection-and-wiring-guide/wiring-and-connector-tips/) to decide what you need - at a minimum, you will probably require some 2.5mm shrink sleeve for covering soldered joints where you connect your sensors to the plug assembly. If you are [making y-connections](/sensor-connection-and-wiring-guide/wiring-and-connector-tips/#making-y-connections) you will also need 10mm adhesive lined shrink sleeve. You can buy this at good hardware stores and electronics suppliers.
</Flag>

#### Caulking silicone
<Flag src="/src/assets/pics/logger-build-guide/silicone.png" alt="silicone">
You will need caulking silicone for fitting the acrylic cover to the logger case. It is also useful for waterproofing [ y-connections](/sensor-connection-and-wiring-guide/wiring-and-connector-tips/#making-y-connections). **Use neutral-cure silicone only** if you are using it for waterproofing wiring. You can buy this at most hardware stores.
</Flag>

##  3D printed parts
The logger case can be printed on any modern 3D printer. You can: 
- Print it yourself (or have a  friend do it) 
- Have it printed by a local business
- Buy one from me as part of a parts kit
- Order one from JLC3DP (the 3D printing sibling of JLCPCB).

All the print files are available [here](https://github.com/benconnor1972/BODAQS/tree/main/mechanical/Case/a8_v1_0) and [here](https://github.com/benconnor1972/BODAQS/tree/main/mechanical/Case/Common). (The Fusion CAD model of the case is in the 'f3z' directory). 

### Parts required

There are two variants of the case design. The main, and recommended, design uses brass heat-set inserts in the case wherever parts need to be connected. This is mechanically superior, but requires you to have the inserts. 

The alternative is to use bt2.5 self-tapping screws. You probably don't want to use these if you're anticipating disassembling your logger 100 times, but they don't need you to buy heat-set inserts. If you choose this option, then pick the parts with the `bt2_5` suffix.

**The fasteners needed are listed in the [Bill of Materials](/logger-build-guide/bodaqs-a8/sourcing-hardware/#bill-of-materials) at the end of this section.**

You will need the following printed parts:

<Flag src="/src/assets/pics/logger-build-guide/base.png" alt="base">
 - A **base** (the lower half of the case). `Base.stl` or `Base bt2_5.stl`. 
</Flag>

<Flag src="/src/assets/pics/logger-build-guide/lid.png" alt="lid">
 - A **lid** (the upper half of the case). `lid.stl` or `Lid bt2_5.stl`.
</Flag>

<Flag src="/src/assets/pics/logger-build-guide/top_end.png" alt="top end">
 - A **top end piece** (the end of the box that faces forward). This piece mounts two M8 connectors.`Top end.stl`. 
</Flag>

<Flag src="/src/assets/pics/logger-build-guide/bottom_end.png" alt="bottom end">
 - A **bottom end piece** (the end of the box that faces backward). This piece mounts two M8 connectors and the  USB-C connector. `Bottom end.stl`.
</Flag>

<Flag src="/src/assets/pics/logger-build-guide/nav_plate.png" alt="nav plate">
 - A **nav plate** to retain the navigation button assembly. `Nav plate.stl` or `Nav plate bt2_5.stl`.
</Flag>

<Flag src="/src/assets/pics/logger-build-guide/power_plate.png" alt="power button plate">
 - A **power button plate** to retain the power button assembly. `Power button plate.stl` or `Power button plate bt2_5.stl`
</Flag>

<Flag src="/src/assets/pics/logger-build-guide/oled_spacer.png" alt="oled spacer">
 - An **OLED spacer** to keep the OLED display in the correct position. `OLED spacer.stl`.
</Flag>

<Flag src="/src/assets/pics/logger-build-guide/pin.png" alt="pin">
 - 6 **pins** that actuate the buttons on the PCB. `Pin.stl`
</Flag>

<Flag src="/src/assets/pics/logger-build-guide/plug.png" alt="plug">
 - A **plug** to go in the USB connection hole. `plug.stl`. If you don't wish to use this, tape also works. It **must** be printed in TPU.
</Flag>

<Flag src="/src/assets/pics/logger-build-guide/cap.png" alt="cap">
 - **Caps** to go over any unused connectors. These are optional but recommended. They **must** be printed in TPU.
</Flag>

<Flag src="/src/assets/pics/logger-build-guide/downtube_mount.png" alt="downtube-mount">
 - A **downtube mount** (assuming you will mount your logger on your bike's downtube). It **should** be printed in TPU but other materials also work.
</Flag>

<Flag src="/src/assets/pics/logger-build-guide/acrylic.png" alt="acrylic">
 - A **small piece of acrylic** or other clear plastic (22mm x 33mm) to go over the screen of your logger. I cut up old goggle lenses to make these but you can also buy 1 mm acrylic sheet on [AliExpress](https://www.aliexpress.com/item/1005012216508583.html)
</Flag>

### Notes on 3d printing the parts:
#### Recommended material 
Except for the parts noted above that have to be, or should be, printed in TPU, almost any material will suffice. Some however are better than others:

- Carbon-reinforced nylon is the gold standard for this application in my opinion: it is strong, tough and temperature-resistant. I use [BambuLab PAHT-CF](https://au.store.bambulab.com/products/paht-cf) for most case parts.

- ABS, ASA, PETG and PCTG are all good choices, with or without fiber reinforcing. Even when printing in carbon-reinforced nylon, I use unreinforced ABS for the button assembly parts (pins and plates) because a smooth finish is desirable for those parts.

- PLA works, and carbon-reinforced PLA looks amazing with colored logos printed into it. But I'd consider it a third-tier choice as it doesn't have much temperature resistance or impact strength.

**Bottom line: use the best thing you have, and don't stress too much about it**.

#### Print orientation and settings 
for the case top and bottom, flat on their largest faces, with supports enabled. The print lid requires support for the cutouts in the front face, and for the screw holes. The nav and power plates should be printed in the opposite orientation to the pictures above, with supports enabled. The bottom end piece should be printed on the large flat face with supports enabled. Everything else prints well without supports.

Tree-style supports work well. If you are a more advanced 3D printer user and have access to a machine capable of printing multiple materials, the cutout areas benefit from using an interface layer of dissimilar material (PLA for PETG and vice versa), along with the following support settings: 
 - Top z distance: 0
 - Top interface layers: 2
 - Top interface spacing: 0
 - Interface pattern: rectilinearOption 

<Flag src="/src/assets/pics/logger-build-guide/print-case.png" alt="print-case">
**Printing cases with inlaid logo:** If you have access to a multi-color 3D printer and your slicer software supports it, the easiest way to do so is to import the parts as [STEP files](https://github.com/benconnor1972/BODAQS/tree/main/mechanical/Case/a8_v1_0/step) directly into your slicer. Once the files are imported, assign the logo inlays with the colors of your choice. The official BODAQS colors are teal for the spring and either white or black for the bar, depending on the background.
</Flag>

<Flag src="/src/assets/pics/logger-build-guide/print-plate.png" alt="print-plate">
**BambuLab-format project files** are also available in [the 3mf directory](https://github.com/benconnor1972/BODAQS/tree/main/mechanical/Case/a8_v1_0/3mf). `a8_all_parts_one_material.3mf` has all the parts on a single plate. Each project file has two build plates - one for the base variant that uses brass inserts, and another for the one that uses self-tapping screws.

`a8_all_parts_three_colors.3mf` is actually set up to use *four* filments - three colors plus an interface material. It has the same items as the single-color project file but has alternate filament colors assigned to the logo inlays, interface material applied to support-interface surfaces, and the revised support settings described above. 
 
</Flag>
<Aside type="tip" title="Interface materials">
Bambulab and other vendors sell dedicated support-interface materials, but all you really need is two materials that don't stick well to each other. If you are printing in PLA, you can use PETG as am interface material, and vice versa. If you are printing in nylon, ASA makes a great interface material.
</Aside>

### Sensors
<Flag src="/src/assets/pics/logger-build-guide/linear_pots.png" alt="Linear Potentiometers">
The best starting set of sensors is two linear potentiometers (pots).
These sensors change their resistance according to how far they are compressed or extended, which makes them useful for measuring suspension movement.
Linear pots are available from a range of suppliers including major international electronics distributors, specialist suppliers of instrumentation, motorsport suppliers and manufacturers.
</Flag>

The most economical way to buy linear pots is on AliExpress. There are numerous options, but I personally use [these items](https://www.aliexpress.com/item/1005008810289538.html).

When buying your linear pots, pay attention to:

- **Travel:**  Your pots must have more travel than what you are measuring. If in doubt go a size up, but no more than needed as longer pots can be harder to mount.
- **Physical dimensions:** Especially diameter. Around 12mm is ideal. Larger diameter pots get harder to mount.
- **Mountings:** Ideally the pot has spherical bearings (rose joints) at both ends
- **Resistance:** You want pots with 2-10 k-ohm full-range resistance.

### Tools
The following tools are <Badge variant="danger" text="Required" /> or <Badge text="Recommended" variant="caution"/>

#### Soldering iron
<Badge variant="danger" text="Required" /> You will be soldering pin headers and connectors into the PCB and sensors to plug assemblies, so you will need a soldering iron suitable for electronics use and some solder around 0.8mm diameter.
<Lightbox src="/src/assets/pics/logger-build-guide/soldering_iron_1.png" alt="A generic soldering iron" />
<Lightbox src="/src/assets/pics/logger-build-guide/soldering_iron_2.png" alt="sThe TS101 premium iron" />

<Aside type="tip" title="Optional">
 The premium soldering iron option is a TS101 or Pinecil USB smart soldering iron. These feature a high power output, rapid heatup, and can be run with a lightweight cable, which makes them excellent for fine work. However, budget options can do the job just fine.
</Aside>

#### Side cutters
<Badge variant="danger" text="Required" /> You should get a small flush-cut set intended for electronics rather than a larger set intended for more general electrical work.
<Lightbox src="/src/assets/pics/logger-build-guide/sidecutters.png" alt="side cutter " />

#### 2.5mm allen key
<Badge variant="danger" text="Required" /> For fitting the case together. If you don't have a decent set of allen keys, you can pick a set up from almost any hardware store

#### Wire strippers
<Badge text="Recommended" variant="caution"/> You can strip wire with side cutters if you are careful, or your teeth if you are a maniac, but these make it much easier. You will need to strip wire to wire sensors to plug assemblies.
<Lightbox src="/src/assets/pics/logger-build-guide/wire_strippers.png" alt="wire stripper " />

#### Multi-meter
<Badge text="Recommended" variant="caution"/> For polarity & continuity testing and fault finding. Even a basic model is sufficient for the needs of this project. Not needed if everything goes perfectly but indispensible if it doesn't.
<Lightbox src="/src/assets/pics/logger-build-guide/multimeter.png" alt="multimeter " />

#### Miniature hot air gun
<Badge text="Recommended" variant="caution"/> For heating shrink-sleeve. A match, cigarette lighter, or glossy print of the author (price on request) can be used instead if necessary.
<Lightbox src="/src/assets/pics/logger-build-guide/hot_air.png" alt="hot air gun" />

## Bill of Materials

| Qty | Item | Link | Note |
|---:|---|---|---|
| 1 | BODAQS A8 printed circuit board | [JLCPCB](https://jlcpcb.com/) | Direct from fabricator |
|  |  | [BODAQS.net](/buy-pcb-or-kit/) | Buy from bodaqs.net |
| 1 | 0.96" OLED display HS96L03W2C03 | [AliExpress](https://www.aliexpress.com/item/1005007228213109.html) | Multiple vendors — search "HS96L03W2C03" |
| 1 | Nintendo 2DS replacement button pad | [AliExpress](https://www.aliexpress.com/item/1005009646292735.html) | Multiple vendors — search "button pad 2DS" |
| 1 | Li-Ion Polymer battery pack 3.7V, JST-PH 2-pin connector | [SparkFun](https://www.sparkfun.com/lithium-ion-battery-2ah.html) | Recommended if purchasing from the US |
|  |  | [Kiwi Electronics](https://www.kiwi-electronics.com/en/lithium-polymer-li-po-battery-3-7v-1200mah-1045) | Recommended if purchasing from the EU |
|  |  | [Altronics](https://www.altronics.com.au/p/s4725-3.7v-2000mah-polymer-lithium-ion-battery-lipo/) | Recommended if purchasing from Australia |
|  |  | [AliExpress](https://www.aliexpress.com/item/1005004841334328.html) | Check dimensions — model 524261 from this vendor |
| 1 | Header socket, 8.5mm high, 2.54mm pitch, single row, 4+ sockets | [SparkFun](https://www.sparkfun.com/arduino-header-kit.html) | Recommended if purchasing from the US |
|  |  | [Kiwi Electronics](https://www.kiwi-electronics.com/en/teensy-header-kit-2706) | Recommended if purchasing from the EU |
|  |  | [Altronics](https://www.altronics.com.au/p/p5390-oupiin-40-pin-header-socket/) | Recommended if purchasing from Australia |
|  |  | [AliExpress](https://www.aliexpress.com/item/1005003610333849.html) | Multiple vendors — search "Socket header 8.5mm" |
| 4 | Amphenol M8 circular connector M8AS-06PMMR-SF8001 | [DigiKey](https://www.digikey.com.au/en/products/detail/amphenol-ltw/M8AS-06PMMR-SF8001/7618863) |  |
|  |  | [AliExpress](https://www.aliexpress.com/item/1005008002251461.html) | Purchase plug assemblies from the same vendor — read the guide |
| 4 | M8 plug assemblies Amphenol 8A-06AFFM-SL7A01 | [DigiKey](https://www.digikey.com.au/en/products/detail/amphenol-ltw/8A-06AFFM-SL7A01/7616809) | DigiKey |
| 5 max | M6 plastic circular connectors — 3 pin | [AliExpress](https://www.aliexpress.com/item/1005005939808200.html) | Multiple vendors — search "M6 connector". Read the guide to decide how many you need. |
| 3 max | M6 plastic circular connectors — 4 pin | [AliExpress](https://www.aliexpress.com/item/1005005939808200.html) | Multiple vendors — search "M6 connector". Read the guide to decide how many you need. |
| 1 | 22mm × 33mm × 1mm acrylic panel | [AliExpress](https://www.aliexpress.com/item/1005012216508583.html) | You can make this from a clear lens from a set of goggles. |
| 1 | CR1220 button cell battery |  | For the real-time clock. Available almost anywhere. |
| 1 | 16GB (or larger) MicroSD card |  | Available almost anywhere. |
|  | 2.5mm shrink sleeve |  | Available from most hardware shops and electronics suppliers. |
|  | 10mm shrink sleeve(if making y connections) |  | Available from most hardware shops and electronics suppliers. |
|  | Neutral-cure caulking silicone |  | Available from most hardware shops. |

### Fasteners (option 1 - using brass inserts)

| Qty | Item | Link | Note |
|---:|---|---|---|
| 14 | M3 × 5 × 4.2 heat-set brass inserts | [AliExpress](https://www.aliexpress.com/item/1005008666672949.html) | Multiple vendors — search "M3 brass insert" |
| 4 | M3 × 12 stainless-steel socket-head cap screws | [AliExpress](https://www.aliexpress.com/item/1005003318923561.html) | Multiple vendors — search "M3 stainless steel hex" |
| 4 | M3 × 8 stainless-steel socket-head cap screws | [AliExpress](https://www.aliexpress.com/item/1005003318923561.html) | Multiple vendors — search "M3 stainless steel hex" |
| 6 | M3 × 6 stainless-steel socket-head cap screws | [AliExpress](https://www.aliexpress.com/item/1005003318923561.html) | Multiple vendors — search "M3 stainless steel hex" |
| 4 | M2 × 5 stainless-steel button-head cap screws | [AliExpress](https://www.aliexpress.com/item/32966917947.html) | Multiple vendors — search "M2 stainless steel buttonhead" |

### Fasteners (option 2 - using self tapping screws)

| Qty | Item | Link | Note |
|---:|---|---|---|
| 8 | BT2.5 × 8 self-tapping screws for plastic | [Bambu Lab](https://au.store.bambulab.com/products/bt2-5-socket-head-cap-self-tapping-screws-shcs-new) | Also available on AliExpress |
| 10 | BT2.5 × 5 self-tapping screws for plastic | [Bambu Lab](https://au.store.bambulab.com/products/bt2-5-socket-head-cap-self-tapping-screws-shcs-new) | Also available on AliExpress |

### 3D-printed parts

| Qty | Part |
|---:|---|
| 1 | Logger case — base |
| 1 | Logger case — lid |
| 1 | Logger case — top end |
| 1 | Logger case — bottom end |
| 1 | Logger case — nav plate |
| 1 | Logger case — power-button plate |
| 1 | Logger case — OLED spacer |
| 6 | Logger case — pin |
| 1 | Plug |
| 4 | Caps |
| 1 | Downtube mount |
