benconnor1972/BODAQS/mechanical/Case/a8_v1_0/stl/Bottom end.stl

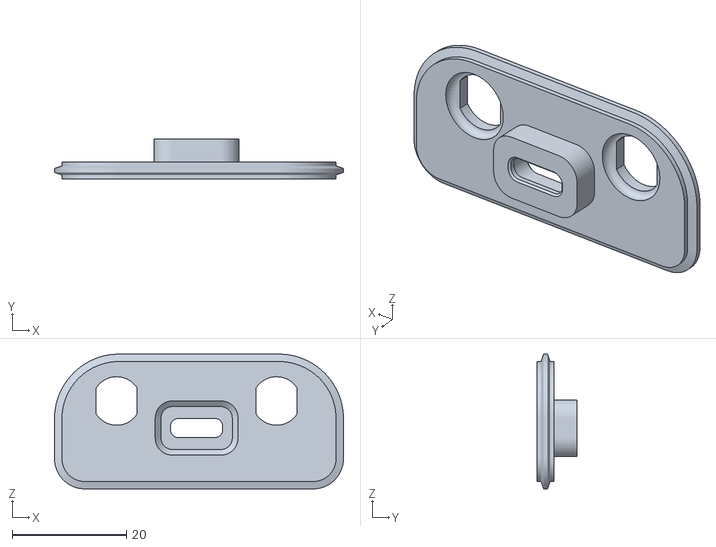
[picture p41: CAD file, 2026-07-28]
mechanical/Case/a8_v1_0/stl/Bottom end.stl
50.6 x 7.00 x 23.6
