benconnor1972/BODAQS/mechanical/Case/Common/Amphenol M8 cap.stl

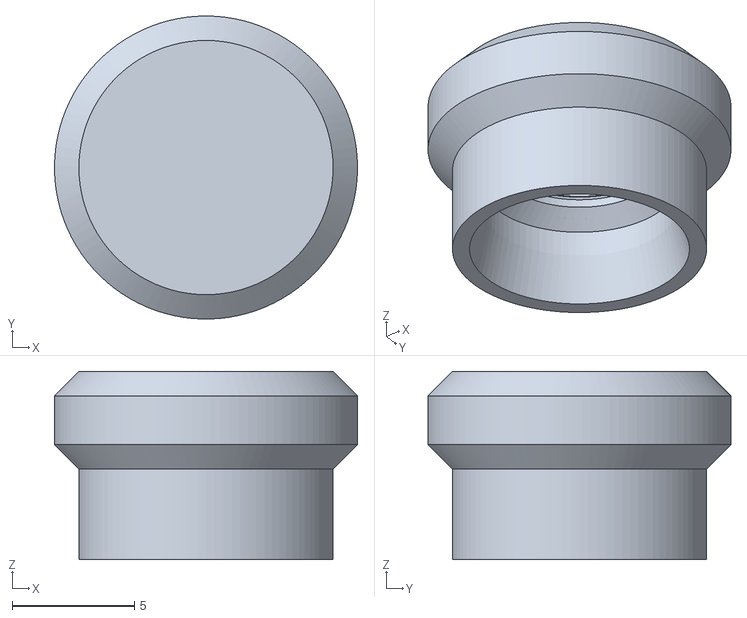
[picture p42: CAD file, 2026-07-28]
mechanical/Case/Common/Amphenol M8 cap.stl
12.4 x 12.4 x 7.70
