benconnor1972/BODAQS/mechanical/Case/Prototype E-F/STEP/Base_nuts.step

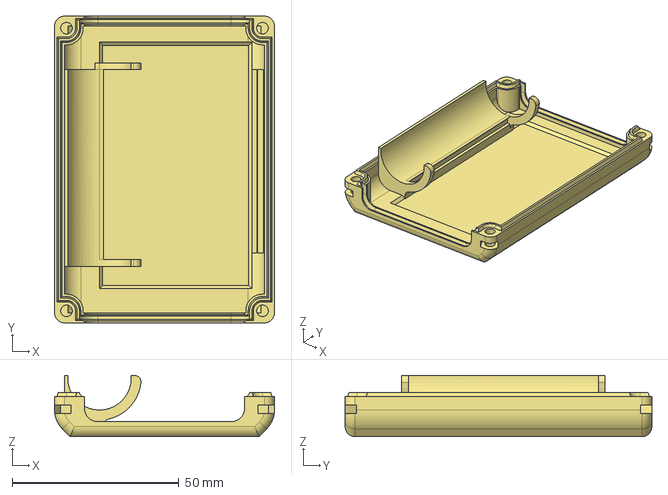
[picture p43: CAD file, 2026-05-07]
mechanical/Case/Prototype E-F/STEP/Base_nuts.step
66.0 x 92.0 x 18.4 mm
