benconnor1972/BODAQS/mechanical/Case/Prototype E-F/Top end_2_connectors.stl

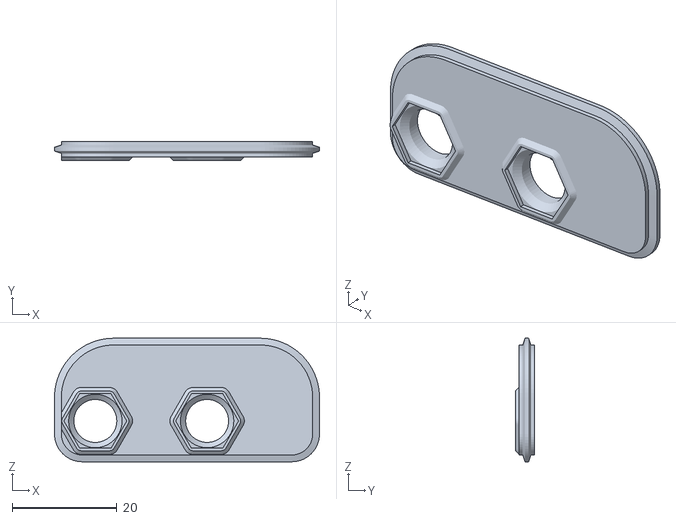
[picture p44: CAD file, 2026-04-24]
mechanical/Case/Prototype E-F/Top end_2_connectors.stl
50.6 x 3.70 x 23.6
