benconnor1972/BODAQS/mechanical/linear-potentiometer-mounts/Fork/Fox 36/fork-lower-band30-type-od44_5-af7mm-fox36-lyrik-miran.stl

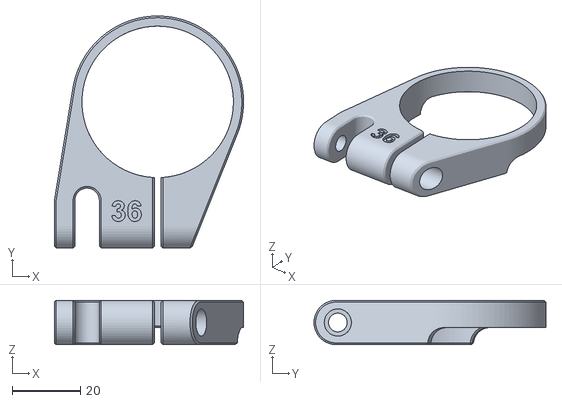
[picture p45: CAD file, 2026-09-02]
mechanical/linear-potentiometer-mounts/Fork/Fox 36/fork-lower-band30-type-od44_5-af7mm-fox36-lyrik-miran.stl
55.6 x 68.2 x 13.0
