benconnor1972/BODAQS/mechanical/linear-potentiometer-mounts/Fork/Fox 38/fork-upper-crown30-type-af7mm-fox38-miran.stl

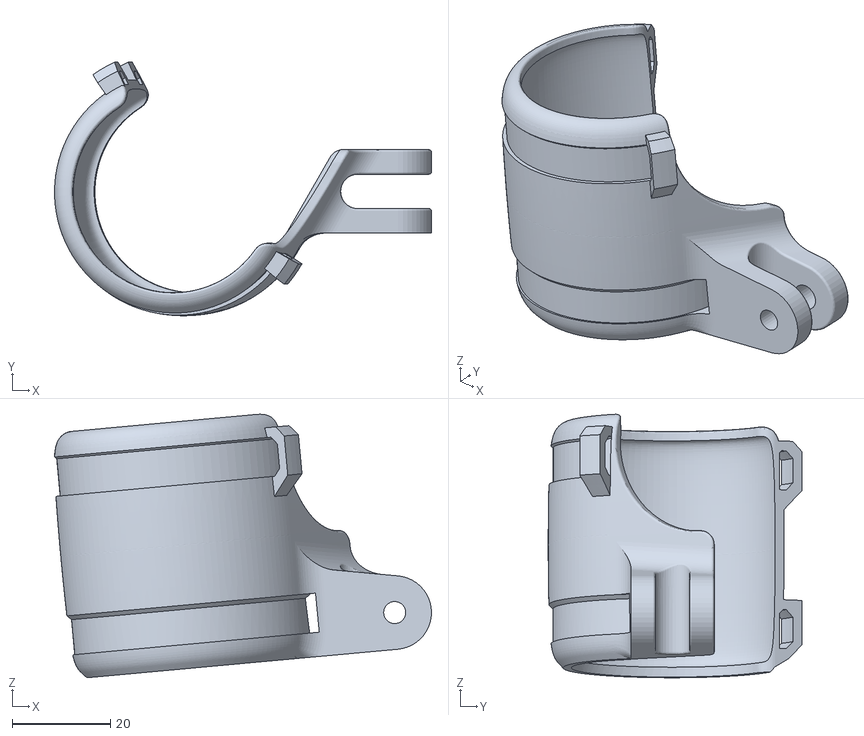
[picture p46: CAD file, 2026-09-02]
mechanical/linear-potentiometer-mounts/Fork/Fox 38/fork-upper-crown30-type-af7mm-fox38-miran.stl
76.8 x 51.7 x 53.7
