benconnor1972/BODAQS/mechanical/linear-potentiometer-mounts/Fork/Fox 40/fork-upper-ziptie-type-od40-af7mm-fox40-miran.stl

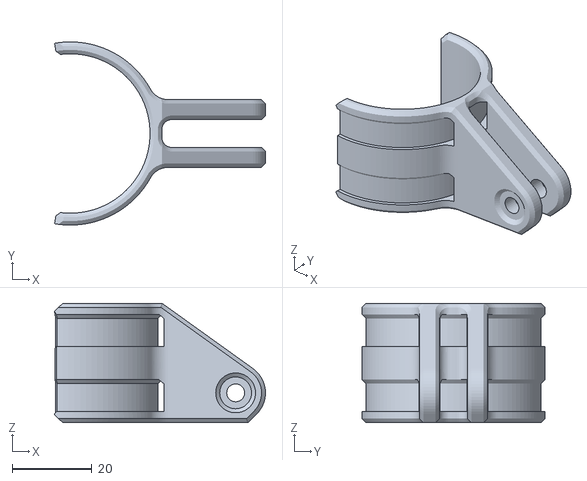
[picture p47: CAD file, 2026-09-02]
mechanical/linear-potentiometer-mounts/Fork/Fox 40/fork-upper-ziptie-type-od40-af7mm-fox40-miran.stl
53.0 x 46.0 x 30.0
