benconnor1972/BODAQS/mechanical/linear-potentiometer-mounts/Fork/SID/fork-lower-band0-type-od41_5-af7mm-sid-fox34-miran.stl

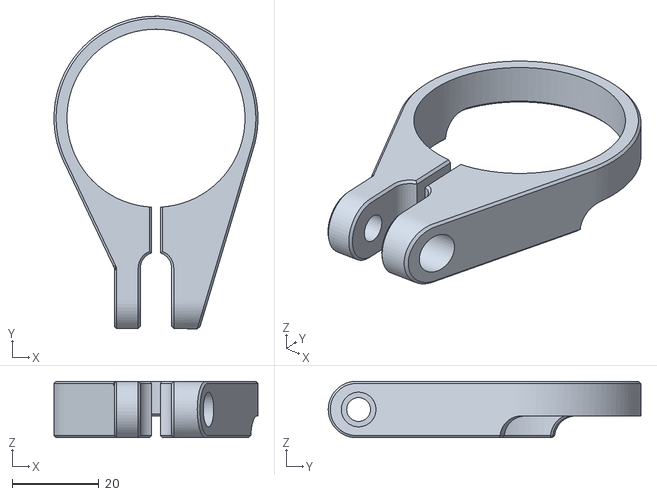
[picture p48: CAD file, 2026-09-08]
mechanical/linear-potentiometer-mounts/Fork/SID/fork-lower-band0-type-od41_5-af7mm-sid-fox34-miran.stl
47.0 x 72.0 x 13.0
