benconnor1972/BODAQS/mechanical/linear-potentiometer-mounts/Fork/Zeb/fork-upper-crown30-type-af7mm-zeb-miran.stl

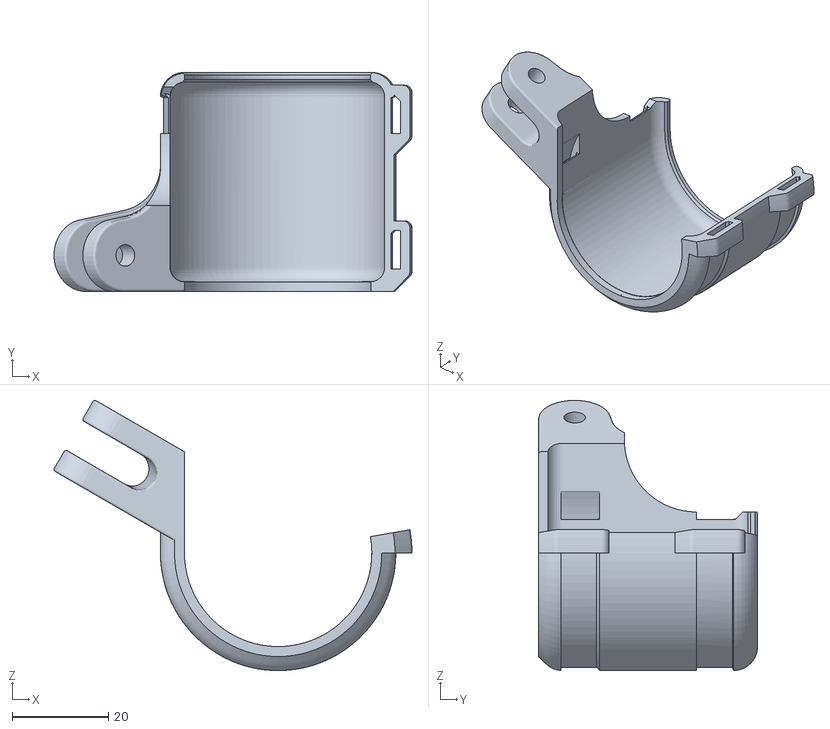
[picture p49: CAD file, 2026-09-02]
mechanical/linear-potentiometer-mounts/Fork/Zeb/fork-upper-crown30-type-af7mm-zeb-miran.stl
74.3 x 45.5 x 56.1
