benconnor1972/BODAQS/mechanical/linear-potentiometer-mounts/Shock/Coil shock body mount/Spherical bearing.stl

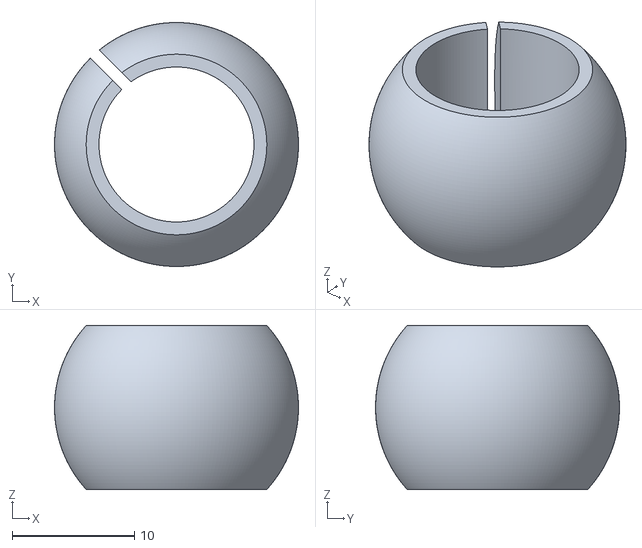
[picture p50: CAD file, 2026-02-25]
mechanical/linear-potentiometer-mounts/Shock/Coil shock body mount/Spherical bearing.stl
20.0 x 20.0 x 13.5
