benconnor1972/BODAQS/mechanical/linear-potentiometer-mounts/Shock/STEVO yoke mount/Rear pot back mount part 2.stl

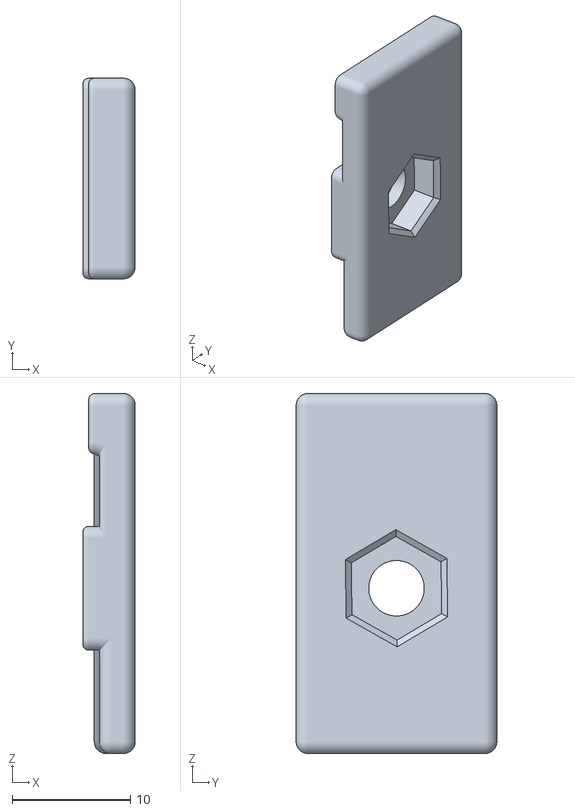
[picture p51: CAD file, 2026-02-25]
mechanical/linear-potentiometer-mounts/Shock/STEVO yoke mount/Rear pot back mount part 2.stl
4.44 x 17.0 x 30.5
