benconnor1972/BODAQS/mechanical/Case/a8_v1_0/step/Lid.step

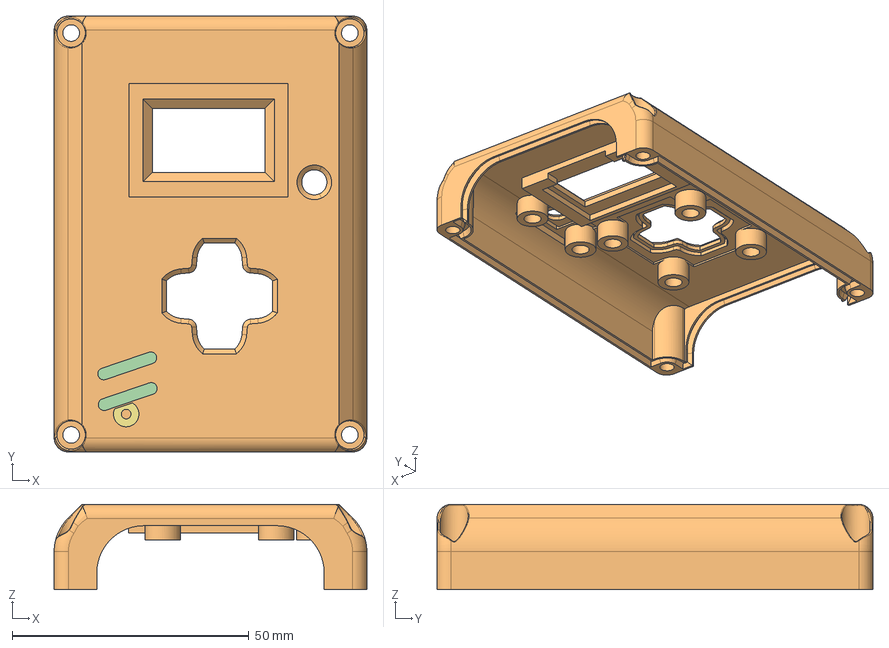
[picture p52: CAD file, 2026-07-28]
mechanical/Case/a8_v1_0/step/Lid.step
66.0 x 92.0 x 18.0 mm
