benconnor1972/BODAQS/mechanical/Case/Common/Plug.stl

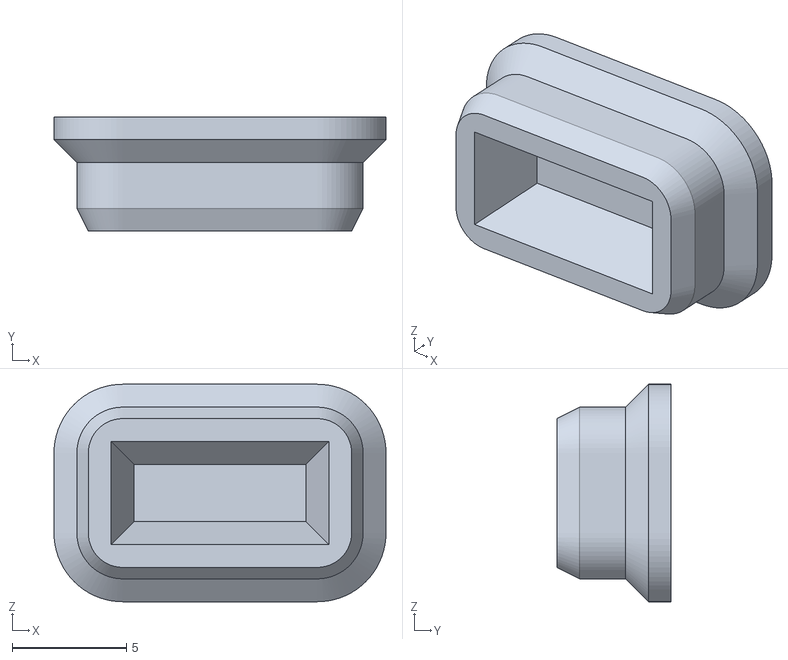
[picture p53: CAD file, 2026-04-24]
mechanical/Case/Common/Plug.stl
14.5 x 5.00 x 9.50
