benconnor1972/BODAQS/mechanical/linear-potentiometer-mounts/Fork/Fox 36/fork-upper-crown30-type-af7mm-fox36-miran.stl

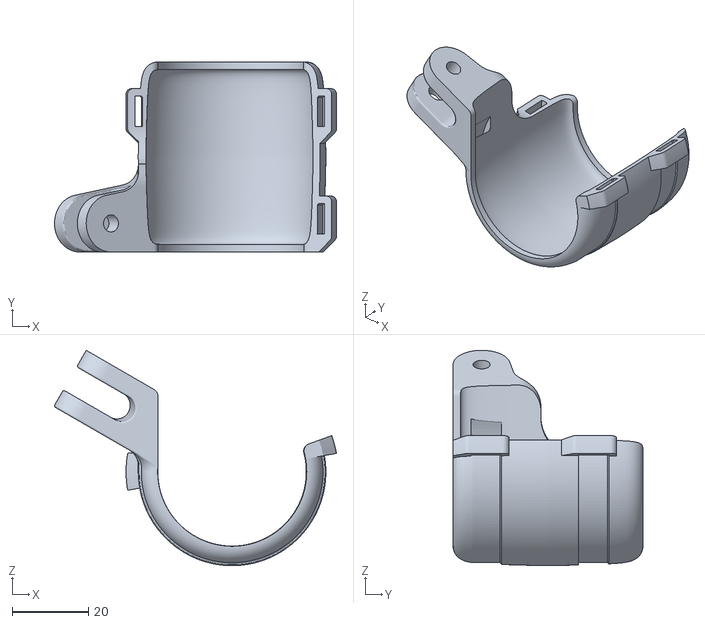
[picture p54: CAD file, 2026-09-01]
mechanical/linear-potentiometer-mounts/Fork/Fox 36/fork-upper-crown30-type-af7mm-fox36-miran.stl
73.9 x 49.8 x 56.5
