benconnor1972/BODAQS/mechanical/linear-potentiometer-mounts/Fork/Fox 40/fork-lower-ziptie-type-od49_5-af7mm-fox40-miran.stl

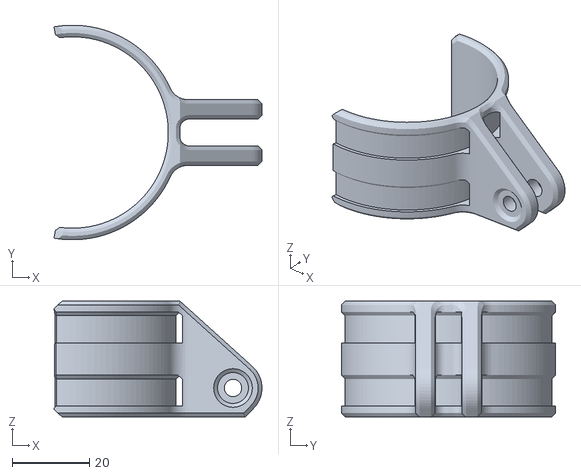
[picture p55: CAD file, 2026-09-02]
mechanical/linear-potentiometer-mounts/Fork/Fox 40/fork-lower-ziptie-type-od49_5-af7mm-fox40-miran.stl
53.8 x 55.5 x 30.0
