benconnor1972/BODAQS/mechanical/linear-potentiometer-mounts/Fork/Lyrik/wedge-fork-upper-steerer-type-od31_7mm-lyrik.stl

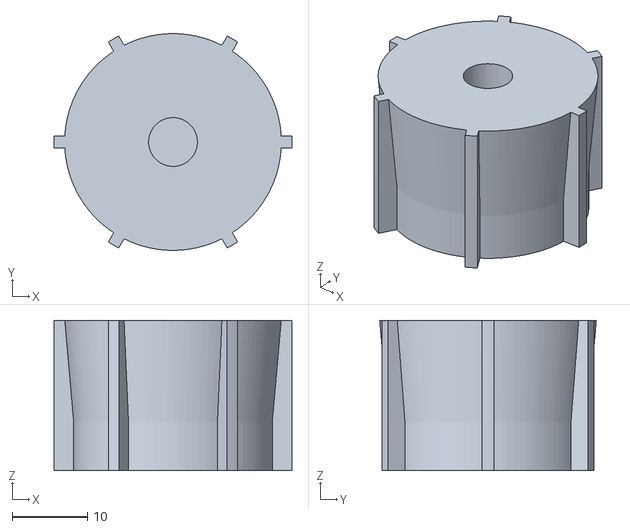
[picture p56: CAD file, 2026-09-02]
mechanical/linear-potentiometer-mounts/Fork/Lyrik/wedge-fork-upper-steerer-type-od31_7mm-lyrik.stl
31.7 x 28.9 x 20.0
