benconnor1972/BODAQS/mechanical/linear-potentiometer-mounts/Fork/SID/wedge-fork-upper-steerer-type-od33_5mm-sid.stl

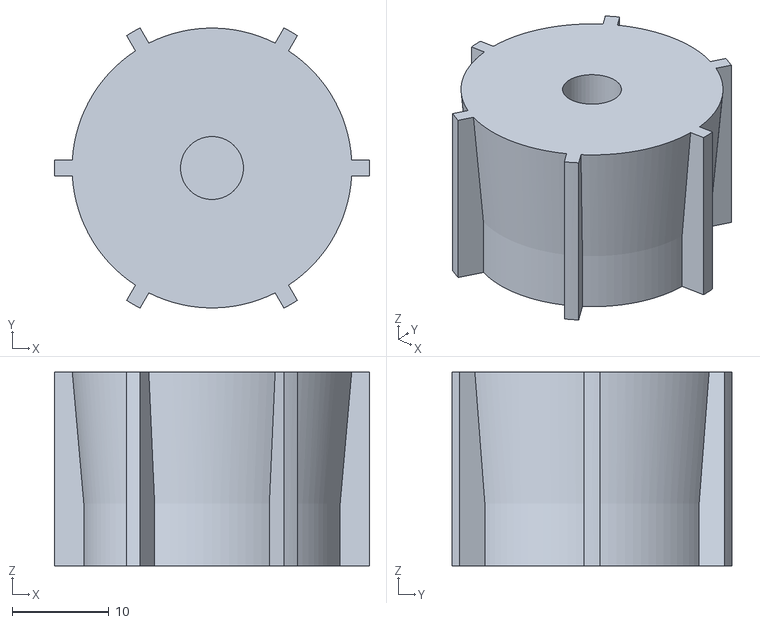
[picture p57: CAD file, 2026-09-02]
mechanical/linear-potentiometer-mounts/Fork/SID/wedge-fork-upper-steerer-type-od33_5mm-sid.stl
32.5 x 28.9 x 20.0
