benconnor1972/BODAQS/mechanical/linear-potentiometer-mounts/Fork/Zeb/fork-lower-ziptie-type-od46-af7mm-fox38-zeb-miran.stl

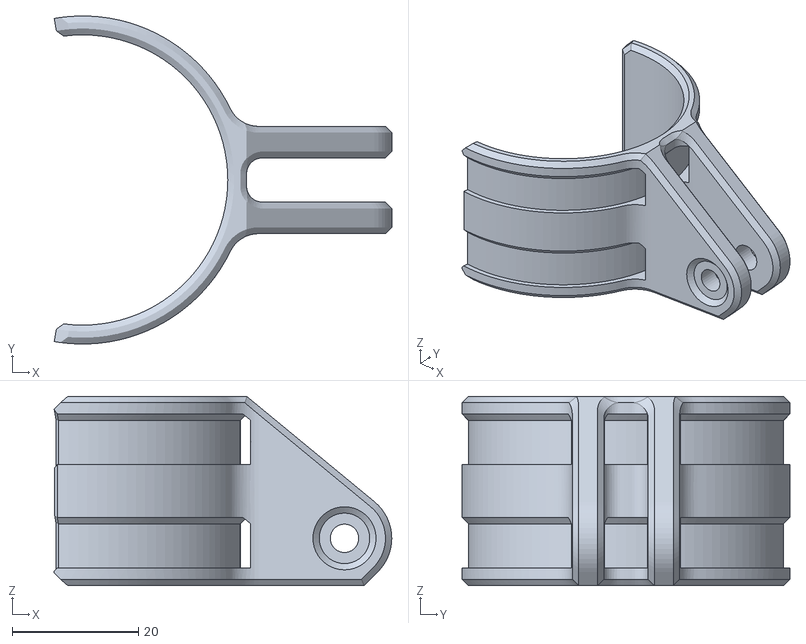
[picture p58: CAD file, 2026-09-02]
mechanical/linear-potentiometer-mounts/Fork/Zeb/fork-lower-ziptie-type-od46-af7mm-fox38-zeb-miran.stl
53.5 x 52.0 x 30.0
