benconnor1972/BODAQS/mechanical/linear-potentiometer-mounts/Shock/Coil shock body mount/Shock pot mount upper 33ID part 1.stl

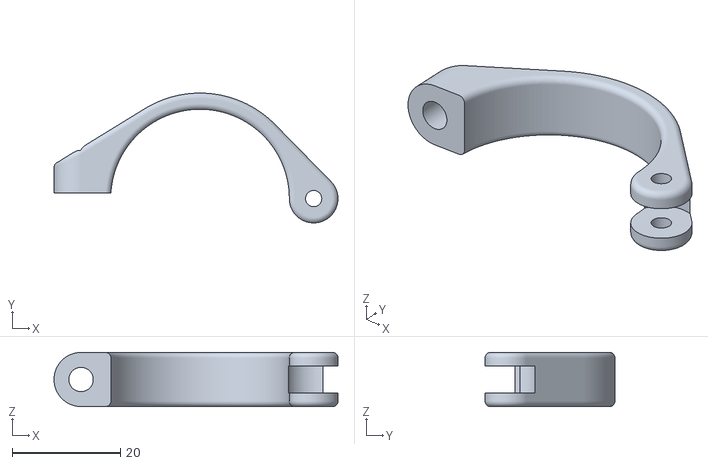
[picture p59: CAD file, 2026-02-25]
mechanical/linear-potentiometer-mounts/Shock/Coil shock body mount/Shock pot mount upper 33ID part 1.stl
52.5 x 24.0 x 10.0
