benconnor1972/BODAQS/mechanical/Case/a8_v1_0/stl/Power button plate bt2_5.stl

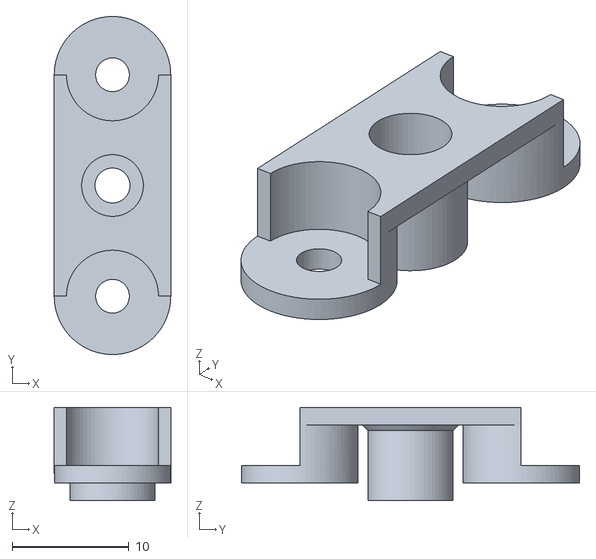
[picture p60: CAD file, 2026-07-28]
mechanical/Case/a8_v1_0/stl/Power button plate bt2_5.stl
10.0 x 29.0 x 8.00
