benconnor1972/BODAQS/mechanical/linear-potentiometer-mounts/Fork/Fox 36/fork-upper-steerer30-type-od32_5mm-af7mm-fox36-miran.stl

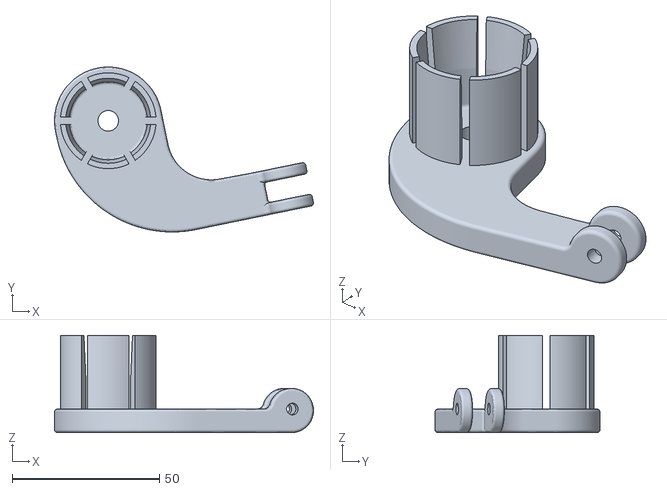
[picture p61: CAD file, 2026-02-25]
mechanical/linear-potentiometer-mounts/Fork/Fox 36/fork-upper-steerer30-type-od32_5mm-af7mm-fox36-miran.stl
87.9 x 56.0 x 33.0
