benconnor1972/BODAQS/mechanical/linear-potentiometer-mounts/Fork/Fox 38/Wedge - pot upper mount Fox 38 oval.stl

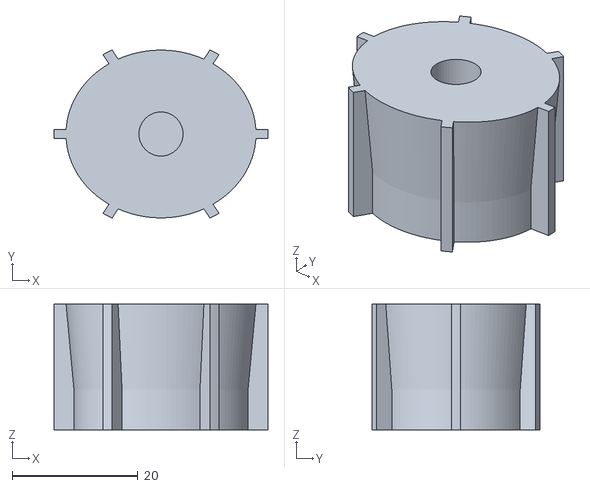
[picture p62: CAD file, 2026-09-02]
mechanical/linear-potentiometer-mounts/Fork/Fox 38/Wedge - pot upper mount Fox 38 oval.stl
34.0 x 26.7 x 20.0
