benconnor1972/BODAQS/mechanical/linear-potentiometer-mounts/Fork/Fox 40/fork-upper-band-type-od40-af7mm-fox40-miran.stl

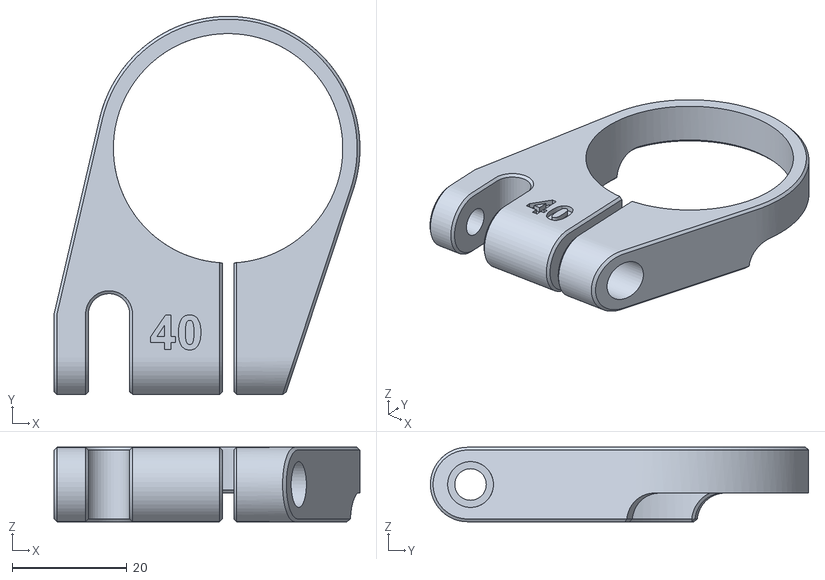
[picture p63: CAD file, 2026-09-02]
mechanical/linear-potentiometer-mounts/Fork/Fox 40/fork-upper-band-type-od40-af7mm-fox40-miran.stl
53.3 x 65.9 x 13.0
