benconnor1972/BODAQS/mechanical/linear-potentiometer-mounts/Fork/Lyrik/fork-upper-crown0-type-af7mm-lyrik-miran.stl

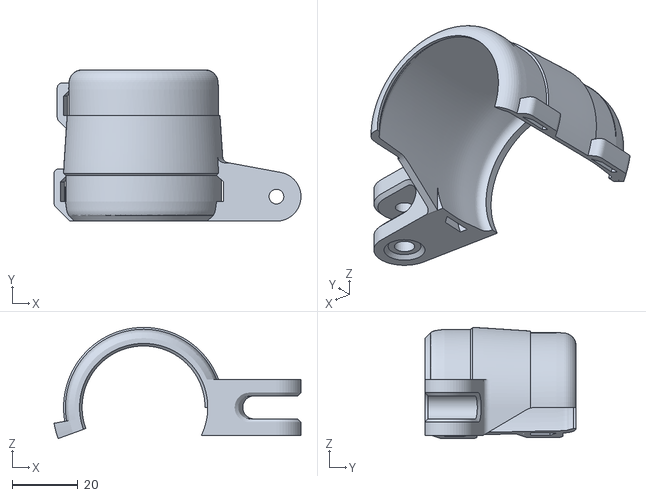
[picture p64: CAD file, 2026-09-02]
mechanical/linear-potentiometer-mounts/Fork/Lyrik/fork-upper-crown0-type-af7mm-lyrik-miran.stl
75.4 x 46.2 x 33.9
