benconnor1972/BODAQS/mechanical/linear-potentiometer-mounts/Fork/SID/fork-lower-band30-type-od41_5-af7mm-sid-fox34-miran.stl

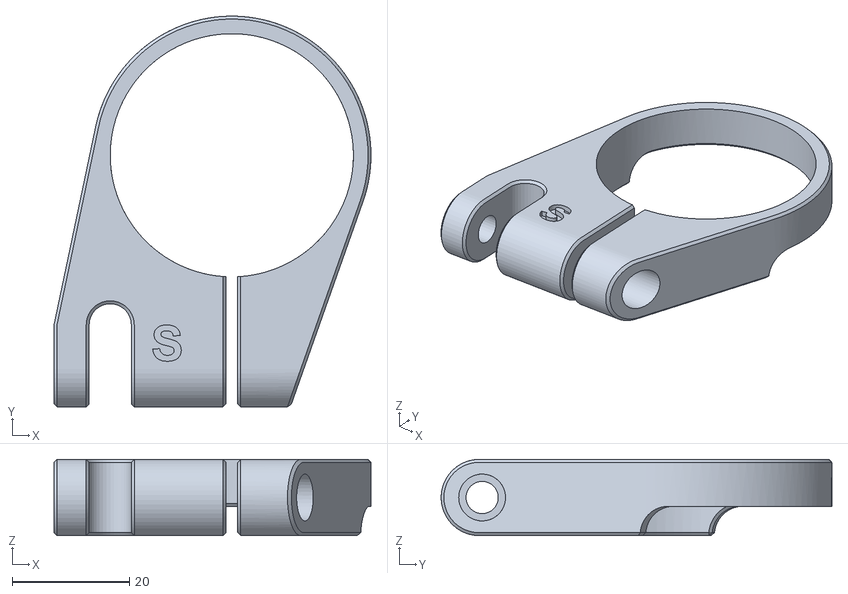
[picture p65: CAD file, 2026-09-02]
mechanical/linear-potentiometer-mounts/Fork/SID/fork-lower-band30-type-od41_5-af7mm-sid-fox34-miran.stl
54.1 x 66.7 x 13.0
