benconnor1972/BODAQS/mechanical/Case/a8_v1_0/stl/OLED spacer.stl

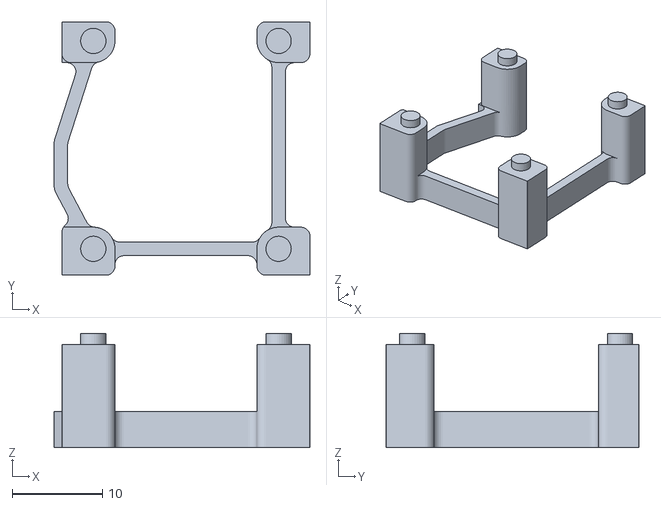
[picture p66: CAD file, 2026-07-28]
mechanical/Case/a8_v1_0/stl/OLED spacer.stl
28.3 x 28.0 x 12.7
