benconnor1972/BODAQS/mechanical/Case/a8_v1_0/stl/Pin.stl

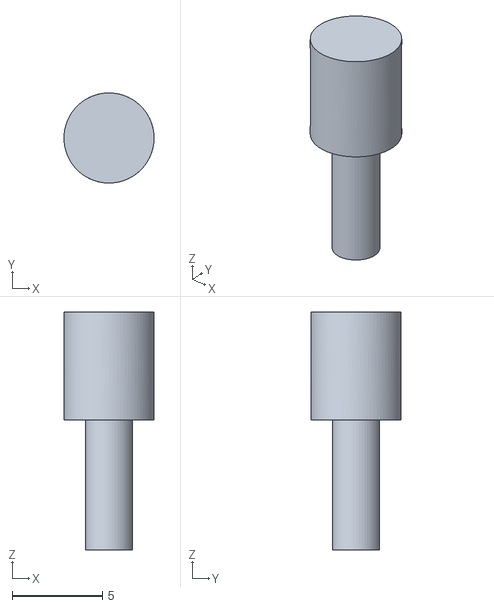
[picture p67: CAD file, 2026-07-28]
mechanical/Case/a8_v1_0/stl/Pin.stl
5.00 x 5.00 x 13.2
