benconnor1972/BODAQS/mechanical/Case/Prototype E-F/Top end_1_connector_plastic.stl

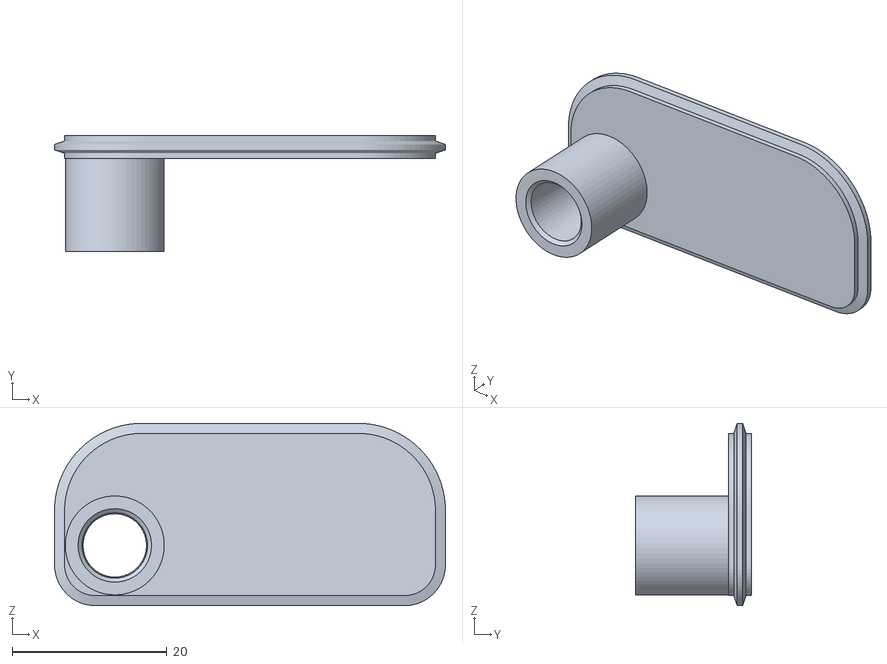
[picture p68: CAD file, 2026-04-13]
mechanical/Case/Prototype E-F/Top end_1_connector_plastic.stl
50.6 x 15.0 x 23.6
