benconnor1972/BODAQS/mechanical/Case/a8_v1_0/stl/Top end.stl

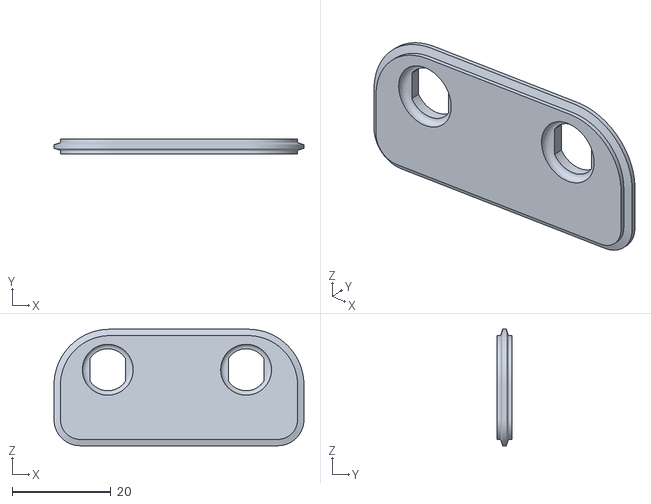
[picture p69: CAD file, 2026-07-28]
mechanical/Case/a8_v1_0/stl/Top end.stl
50.6 x 3.00 x 23.6
