benconnor1972/BODAQS/bodocs/src/content/docs/bike-installation-guide/determining-leverage-curves.mdx

---
title: Determining leverage curves
description: Placeholder guide for measuring or deriving bike suspension leverage curves.
sidebar:
  order: 3
---

import {Aside} from '@astrojs/starlight/components';

<Aside type="note" title="Content still needed">
  This page is a placeholder for leverage curve guidance.
</Aside>

This page will explain how to determine the relationship between wheel travel and measured sensor travel for suspension analysis.

## Content to add

- What a leverage curve is and why BODAQS needs it.
- Simple measurement workflow for common suspension layouts.
- How to record and validate travel points.
- How leverage curve data should be represented for analysis tools.
- Common mistakes and sanity checks.
