benconnor1972/BODAQS/bodocs/src/content/docs/bike-installation-guide/index.mdx

---
title: Mounting the logger
description: Placeholder for guidance on mounting the BODAQS logger to a bike.
sidebar:
  order: 1
---

import {Aside} from '@astrojs/starlight/components';

<Aside type="note" title="Content still needed">
  This page is a placeholder for the bike installation guide.
</Aside>

This page will cover practical logger mounting options, placement tradeoffs, cable routing from the logger, and pre-ride checks.

## Content to add

- Recommended logger locations for common frame layouts.
- Mounting hardware, straps, pads, and weather protection.
- USB access, screen visibility, button access, and serviceability.
- Cable strain relief and checks before riding.
