benconnor1972/BODAQS/bodocs/src/content/docs/user-guide/accessing logs and configuration.mdx

---
title: Configuring the data logger 
description: How to start the BODAQS web interface, download log files, and edit logger configuration from a browser.

sidebar:
  order: 2
---

import { Aside, Card, CardGrid, Steps } from '@astrojs/starlight/components';
import Lede from '@components/Lede.astro';
import Flag from '@components/Flag.astro';

<Lede>
  The BODAQS logger has a small web interface for downloading log files and editing configuration. You can connect through a normal Wi-Fi
  network, or put the logger into access-point mode and connect to it directly.
</Lede>

## Before You Start

The web interface is intended for setup, file transfer, and checking the logger
between runs. It is not used while the logger is actively recording.

<Aside type="caution" title="Logging has priority">
  The logger will not start the web server while logging is active. If the web
  server is running and you start a log, Wi-Fi and the web server are stopped so
  sampling has priority.
</Aside>

You will need one of:

- Station mode: a configured Wi-Fi network that the logger can join, plus a
  phone, tablet, or computer on the same network.
- Access-point mode: a phone, tablet, or computer that can connect directly to
  the logger's own Wi-Fi network.

The logger must be powered on and not logging.

## Connection Modes

The logger can run its web interface in two network modes.

| Mode | Use When | Notes |
| --- | --- | --- |
| `Station` | You have a local Wi-Fi network that both the logger and your computer/phone can join. | Supports normal network workflows and NTP time sync. |
| `Access point` | You want to connect directly to the logger without a router. | Useful in the field. Does not provide internet/NTP time sync. |

You can change the mode from the OLED menu under `Settings` -> `WiFi mode`, or
from the General configuration page in the web interface.

## Starting The Web Interface

<Flag src="/src/assets/pics/user-guide/oled-wifi-starting.png" alt="Wi-Fi starting">
<Steps>
  1. Open the logger main menu from the idle screen.
  2. Select the `WiFi` menu item.
  3. Wait while the menu shows `WiFi: STARTING`.
  4. When the web server is running, the menu shows `WiFi: ON`.
  5. Close the menu and note the `.local` address shown on the idle screen.
</Steps>
</Flag>

In station mode, open a browser on the same network and enter the logger's
`.local` address, for example:

```text
http://bodaqs-<logger-id>.local/
```

In access-point mode, first connect your phone, tablet, or computer to the
logger's AP SSID, then open the same `.local` address shown on the logger
display:

```text
http://bodaqs-<logger-id>.local/
```

The root page redirects to the file browser. You can also go directly to:

```text
http://bodaqs-<logger-id>.local/files
```

<Aside type="tip" title="Finding the logger">
  The idle screen alternates between the network/AP name and the `.local`
  address while Wi-Fi is running. The logger advertises itself via Bonjour/mDNS
  in both station and access-point mode, so the `.local` address works in either
  mode. If the page does not load, check that your computer or phone is on the
  same network or connected to the logger access point.
</Aside>

<Aside type="note" title="Windows requires Bonjour">
  The `.local` address works natively on macOS, iOS, Android, and Linux. On
  Windows, install [Bonjour Print Services for Windows](https://support.apple.com/downloads/bonjour_for_windows)
  (bundled with iTunes) for `.local` resolution. Without Bonjour installed, use
  the raw IP address shown on the logger display instead — in access-point mode
  this is typically `http://192.168.4.1/`.
</Aside>

Every web page shows navigation links for `Files`, `General`, and `Sensors`.

<Aside type="note" title="Web editing locks">
While logging is occurring or upload mode is active, configuration editing is disabled and manual file
  changes are blocked. The web page shows a warning when editing is disabled.
</Aside>

## Files Page

{/* TODO screenshot: replace files.png with a current Files page showing the Logger upload panel. Add variants for normal mode and upload mode. */}
<Flag src="/src/assets/pics/user-guide/files.png" alt="files">
The `Files` page is the home page of the web interface. It lets you browse the
SD card, download log files, upload files, create folders, and remove files or
folders when manual file changes are allowed.

The page also includes a `Logger upload` panel showing upload mode, network/IP,
hostname, and importable session counts.
</Flag>

Typical files produced by the logger are:

- `.CSV` log files containing time-series data.
- `.json` log metadata files with column semantics, run statistics, and other
  metadata.
- `.bdq` compact binary log files when BODAQS compact binary output is selected.

<CardGrid>
  <Card title="Download logs" icon="download">
    Select one or more files with the checkboxes, then choose `Download selected`
    or `Download ZIP`. ZIP downloads are for convenient packaging; the files are
    not intended to be compressed for analysis.
  </Card>
  <Card title="Manage the SD card" icon="folder">
    Use folder links and breadcrumbs to navigate. When allowed, you can create
    folders, upload files, delete selected files, or remove empty folders.
  </Card>
</CardGrid>

### Downloading One Or More Files

To download logs:

1. Open the `Files` page.
2. Browse to the folder containing the log files.
3. Tick the files you want.
4. Select `Download selected` to download each file individually, or
   `Download ZIP` to package them together.

<Aside type="tip" title="Keep metadata with logs">
  Keep each log file with its `.json` metadata file where one exists. The JSON
  metadata tells downstream software what the logged columns mean and whether
  the logger dropped samples.
</Aside>

### Upload Mode

{/* TODO screenshot: add Files page screenshot with upload mode active and session counts visible. */}
Upload mode is used by Import Manager and related session-transfer workflows.
Enter it from the Files page or from the OLED main menu.

When upload mode is active:

- The upload workflow can enumerate and transfer completed sessions.
- Manual upload/create/delete actions are disabled.
- Configuration editing is disabled.
- Logging cannot start until upload mode is exited.

### Uploading And Deleting Files Manually

The upload control is useful for restoring configuration files or putting
supporting files onto the SD card. Choose one or more local files, then select
`Upload`.

Tick one or more files and select `Delete selected` to remove files. For
folders, use the folder remove action shown on the file list.

<Aside type="caution" title="Deletion is permanent">
  Deleting from the web interface removes files from the logger SD card.
  Download anything you want to keep before deleting it.
</Aside>

## General Configuration

{/* TODO screenshot: replace config.png with a current General page screenshot showing compact binary and current locking/banner styling. */}
<Flag src="/src/assets/pics/user-guide/config.png" alt="general configuration">
Open `General` from the navigation bar to edit logger-wide settings. Changes are
written to the logger configuration file when you press `Save`.

If a page reports that restart is required, restart the logger before relying on
the changed live behavior.
</Flag>

The General section includes:

- `Logger name`: the human-readable logger alias.
- `Sample rate`: the logging sample rate in Hz.
- `Log format`: `BODAQS CSV` or `BODAQS compact binary`.
- `Omit log metadata JSON`: disables generation of the JSON metadata file.
- `Timestamp mode`: timestamp output policy.
- `Timezone`: timezone rule used when the logger sets its clock.
- `Auto-sleep idle`: idle time before sleep.
- `Wi-Fi idle timeout`: idle time before Wi-Fi is stopped.

<Aside type="tip" title="Metadata is recommended">
  Leave `Omit log metadata JSON` unchecked unless you have a specific reason to
  disable metadata. Metadata is the best way for downstream tools to understand
  logger columns and run quality.
</Aside>

### Network And Time Settings

{/* TODO screenshot: replace wifi.png with a current Network & NTP section showing Wi-Fi mode, AP SSID/password, and HTTP time check URL. */}
<Flag src="/src/assets/pics/user-guide/wifi.png" alt="network settings">
The General configuration page also includes network and time settings:

- Whether Wi-Fi should be enabled automatically when the logger is awake.
- Wi-Fi mode: `Station` or `Access point`.
- Access-point SSID and password.
- Whether Wi-Fi may be auto-enabled for NTP if the RTC is invalid.
- NTP servers.
- HTTP time check URL.
- Up to five station-mode Wi-Fi network slots.
- Optional minimum RSSI and BSSID pinning for each station network.
- Optional static IP settings.
</Flag>

Station mode tries configured networks in priority order, with preference for
the most recently connected suitable network.

Access-point credential changes are saved immediately, but they take effect the
next time Wi-Fi is restarted.

<Aside type="tip" title="Static IPs">
  Most users should use DHCP and leave static IP disabled. Static IP settings
  are useful only if you deliberately want the logger to use a fixed address on
  a known network.
</Aside>

## Sensor Configuration

Open `Sensors` from the navigation bar to edit the logger's configured sensors.

{/* TODO screenshot: add a current Sensors summary/list page screenshot. The old docs showed every sensor editor on one page, which is no longer accurate. */}
The Sensors page now shows:

- A summary table of configured sensors.
- Each sensor's name, type, default state, and output mode.
- An `Edit` link for each sensor.
- A `New sensor` block for adding a sensor.

Selecting `Edit` opens the sensor detail page for that one sensor.

<Aside type="caution" title="Restart after add/delete/type changes">
  If you add or delete a sensor, or change a sensor type, restart the logger
  before relying on the live logging output. The web page will remind you when a
  restart is needed.
</Aside>

### Supported Sensor Types

The current firmware supports these user-facing sensor types:

- `Analog Potentiometer`: the ubiquitous potentiometer - usually linear - used for measuring suspension displacement.
- `AS5600 String Pot (Analog)` and `AS5600 String Pot (I2C)`: multi-turn string potentiometer based on AS5600 12-bit encoder. Can be read as either an analog device or via I2C (recommended).
- `AS5600 Angle (I2C)`: A simple AS5600 single-turn sensor.
- `AS5048B Angle (I2C)`: Another single turn sensor, but using an AS5048B 14-bit encoder.
- `DAN-F10N GPS (UART)`: A modern GPS module with inbuilt patch antenna.

### Basic

<Flag src="/src/assets/pics/user-guide/sensorbasic.png" alt="sensor basic">
The Basic section contains:

- The sensor name.
- The sensor type.
- Connection fields for that sensor, such as analog input, I2C bus/address, or
  UART parameters.
- Whether the sensor is muted by default.
</Flag>

Analog input selection is board-aware. On RC3 hardware, analog inputs may map to
external ADC channels rather than ESP32 GPIO ADC pins.

<Flag src="/src/assets/pics/user-guide/sensorbasici2c.png" alt="I2C sensor basic">
Changing a sensor type reloads the available fields for that sensor. Adding,
deleting, or changing sensor type saves the configuration, but the live sensor
set is rebuilt on restart.
</Flag>

### Output

<Flag src="/src/assets/pics/user-guide/sensoroutput.png" alt="sensor output">
The Output section controls what the logger writes for that sensor.

- `Output mode`: `RAW` or `LINEAR`.
- `Include raw column`: adds a raw-count column alongside the primary output.
- `Sensor full travel`: full sensor travel used for linear scaling where
  applicable.
- `Installed range`: installed travel/range in the sensor's linear output units,
  used by the Sag Helper in percentage mode.
</Flag>

<Aside type="note" title="Transforms are downstream">
  Logger-side LUT and polynomial output modes are no longer supported. Complex transformations, such as shock-to-wheel lookup tables, are applied during import.
</Aside>

### Usage And Signal Semantics

<Flag src="/src/assets/pics/user-guide/sensorusage.png" alt="sensor usage">
The Usage section describes what the sensor is measuring. These fields are
written into metadata and help downstream software choose the correct data even
if sensor names change.

Usage is described using:

- `End`: for example `front` or `rear`.
- `Primary domain`: for example `wheel`, `suspension`, or `brake`.
- `Primary quantity`: for example displacement, angular displacement, pressure,
  voltage, or similar quantity metadata.
</Flag>

The Sag Helper uses usage metadata. A sensor must be active and have
`primary_domain=suspension` to appear in the Sag Helper screen.

### GPS Sensors
<Flag src="/src/assets/pics/user-guide/gpssensor.png" alt="gps sensor">

The DAN-F10N GPS sensor is logged differently from fixed-rate scalar sensors.
GPS data arrives asynchronously at the GPS update rate and may be invalid while
the receiver is acquiring a fix. The logger writes GPS signal age and quality data to assist downstream tools.

</Flag>

### Calibration

<Flag src="/src/assets/pics/user-guide/sensorcalibration.png" alt="sensor calibration">
The Calibration section contains values used to translate raw sensor readings
into physically meaningful units.

`Calibration methods` is read-only. It shows the effective calibration actions
available for this sensor type. Calibration values below it remain editable
where the sensor exposes them.
</Flag>

For linear displacement sensors, common fields include:

- Sensor count at zero travel.
- Sensor count at full travel.
- Installed zero count.

For rotary angle sensors, zero calibration may also set direction/polarity using
the on-device `Capture +move` step. The firmware uses `direction` for rotary
polarity and may still emit compatibility `invert` metadata for downstream
tools.

### Wrapping

<Flag src="/src/assets/pics/user-guide/sensorwrapping.png" alt="sensor wrapping">
Wrapping fields are shown only for sensors that can produce multi-turn or
wrapped magnetic encoder counts. These settings describe how wrapped counts are
unwrapped into continuous raw position.
</Flag>

### Other Fields

Some sensor types expose additional fields in an `Other` section. These are
type-specific advanced settings. Leave them at their defaults unless you have a
specific setup reason to change them.

### Removing A Sensor

The remove button is at the bottom of the sensor detail page. Removing a sensor
removes it from the logger configuration only.

<Aside type="note" title="Supporting files are left in place">
  Deleting a sensor from the web page does not delete supporting files or
  folders from the SD card. If you no longer need those files, remove them
  manually from the Files page when manual file changes are allowed.
</Aside>
