benconnor1972/BODAQS/bodocs/src/content/docs/user-guide/analyzing your data on bodaqs-workbench.mdx

---
title: Analyzing your data with BODAQS Workbench

sidebar:
  order: 4
---
## This section hasn't been written yet

In the meantime, check out these videos on our YouTube channel:

<iframe width="560" height="315" src="https://www.youtube.com/embed/V4gr8XfFBcc?si=bJAplxRh-kXe-Mrj" title="YouTube video player" frameborder="0" allow="accelerometer; autoplay; clipboard-write; encrypted-media; gyroscope; picture-in-picture; web-share" referrerpolicy="strict-origin-when-cross-origin" allowfullscreen></iframe>

<iframe width="560" height="315" src="https://www.youtube.com/embed/HjcBr6v1-Ec?si=BpmfVnZtHPK2Y7TU" title="YouTube video player" frameborder="0" allow="accelerometer; autoplay; clipboard-write; encrypted-media; gyroscope; picture-in-picture; web-share" referrerpolicy="strict-origin-when-cross-origin" allowfullscreen></iframe>

<iframe width="560" height="315" src="https://www.youtube.com/embed/atCJs7GTWmY?si=BZWaaoYzo8yTAWom" title="YouTube video player" frameborder="0" allow="accelerometer; autoplay; clipboard-write; encrypted-media; gyroscope; picture-in-picture; web-share" referrerpolicy="strict-origin-when-cross-origin" allowfullscreen></iframe>

<iframe width="560" height="315" src="https://www.youtube.com/embed/sTF4DZ6OQM8?si=j0DOe0Gtn2qYrP1K" title="YouTube video player" frameborder="0" allow="accelerometer; autoplay; clipboard-write; encrypted-media; gyroscope; picture-in-picture; web-share" referrerpolicy="strict-origin-when-cross-origin" allowfullscreen></iframe>

<iframe width="560" height="315" src="https://www.youtube.com/embed/duzMjf7pDFY?si=_tyenhGtSrXWV1Sq" title="YouTube video player" frameborder="0" allow="accelerometer; autoplay; clipboard-write; encrypted-media; gyroscope; picture-in-picture; web-share" referrerpolicy="strict-origin-when-cross-origin" allowfullscreen></iframe>
