benconnor1972/BODAQS/bodocs/src/content/docs/software-guide/setup-syn-bike.mdx

---
title: Setting up data.syn.bike

sidebar:
  order: 2
---
import { Aside, Card, CardGrid, Steps } from '@astrojs/starlight/components';
import Lede from '@components/Lede.astro';
import Flag from '@components/Flag.astro';
import Lightbox from '@components/Lightbox.astro';

<Lede>
**syn.bike** have a very nice [website](https://data.syn.bike) that can be used to visualize BODAQS data. If you don't have an appetite for Jupyter Lab notebooks, this is a great way to view your logs.
</Lede>

<Aside type="note" title="Don't change your log format">
<Flag src="/src/assets/pics/software-guide/logformat.JPG" alt="logformat">
On the logger menu, you may have noticed a `log format` item with the option to produce files in `syn.bike raw` (this can also be set via the logger's web UI). It is **not recommended** that you use this. While it is possible using this setting to produce files that can be read directly by data.syn.bike, we recommend you process your files with the BODAQS Import Manager with the 'syn.bike export' option checked. The BODAQS processing pipeline takes care of some minor issues that can prevent data from being scaled properly.
</Flag>
</Aside>

## Configuring data.syn.bike
<Flag src="/src/assets/pics/software-guide/synserver.png" alt="synserver">
[data.syn.bike](https://data.syn.bike/) uses a small local executable to process log files. Download it from the 'settings' tab and place it in a suitable directory.

Double-click the executable to run it - a terminal window should open and the website will give you a message to show that the processing server is connected. As you use data.syn.bike this terminal window will report what it is doing (if you're interested).

Whenever you use data.syn.bike you will need to have it running
</Flag>

<Flag src="/src/assets/pics/software-guide/synsetup1.png" alt="synsetup">
Go to the 'device' tab and ensure the fork travel and shock travel are correctly set. 
</Flag>

<Flag src="/src/assets/pics/software-guide/synsetup.png" alt="synsetup">
Next, go to the 'settings' tab and ensure the following settings are correct:
- Front and rear sensor travels: These should be the full-range travel figures for your sensors, *not* your bike's suspension travel.
- Log frequency: This should match the sample rate at which you collected your data.
- Analog resolution: leave this at 12 bits.
- Wheel diameter and number of speed sensor magnets: Not used. You can ignore these.
- Invert analog data: ordinarily leave set to 'off'. If you have wired your sensors so their output is inverted, switch it.
- Position lowpass filter and zero crossing noise threshold: Leave these at their default values.
- Processing server location: set to `http://127.0.0.1:5079`
</Flag>

Next, [upload and examine your files](/user-guide/analyzing-your-data-with-syn-bike/)
