benconnor1972/BODAQS/bodocs/src/content/docs/hardware-guide/3-Installation.mdx

---
title: Installation

sidebar:
  order: 3
---
## Mounting the logger
## Mounting the sensors
## Wiring tips
