benconnor1972/BODAQS/application/docs/library manager and study set builder UI sketch.jpg

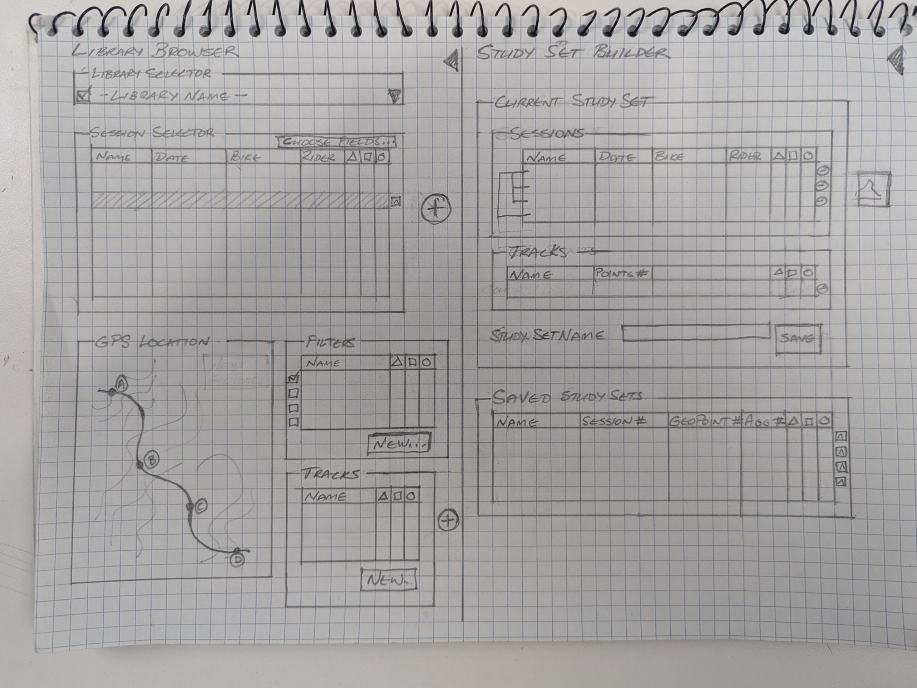
application/docs/library manager and study set builder UI sketch.jpg
