benconnor1972/BODAQS/bodocs/src/assets/pics/bike-installation-guide/DSC_8564.JPG

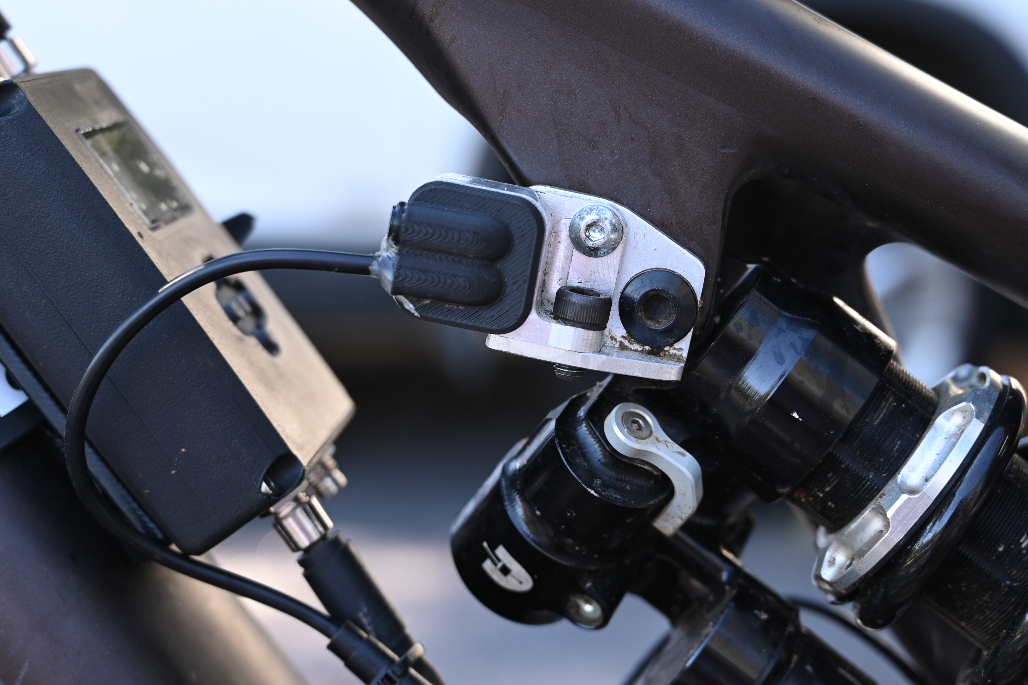
bodocs/src/assets/pics/bike-installation-guide/DSC_8564.JPG
