benconnor1972/BODAQS/bodocs/src/assets/pics/bike-installation-guide/pot-lower-band-twist.JPG

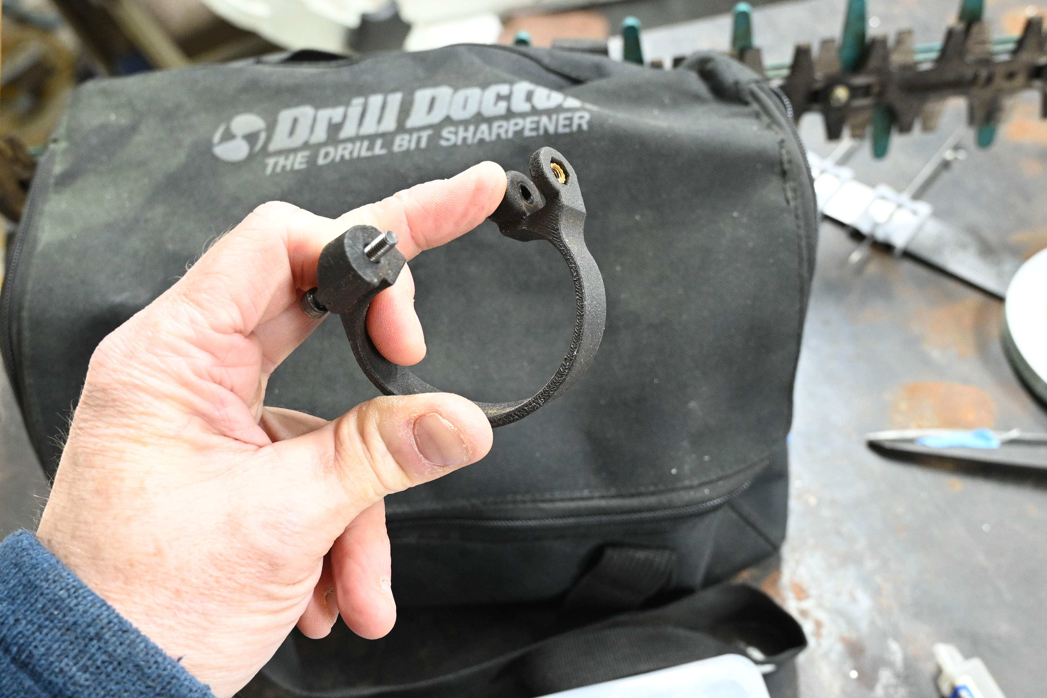
bodocs/src/assets/pics/bike-installation-guide/pot-lower-band-twist.JPG
