benconnor1972/BODAQS/bodocs/src/assets/pics/bike-installation-guide/pot-lower-band.png

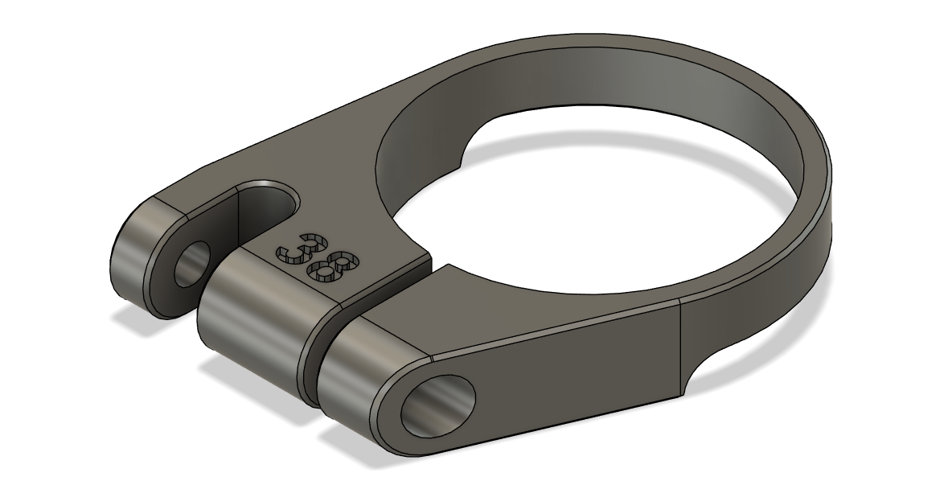
bodocs/src/assets/pics/bike-installation-guide/pot-lower-band.png
