benconnor1972/BODAQS/bodocs/src/assets/pics/bike-installation-guide/pot-upper-stanchion.png

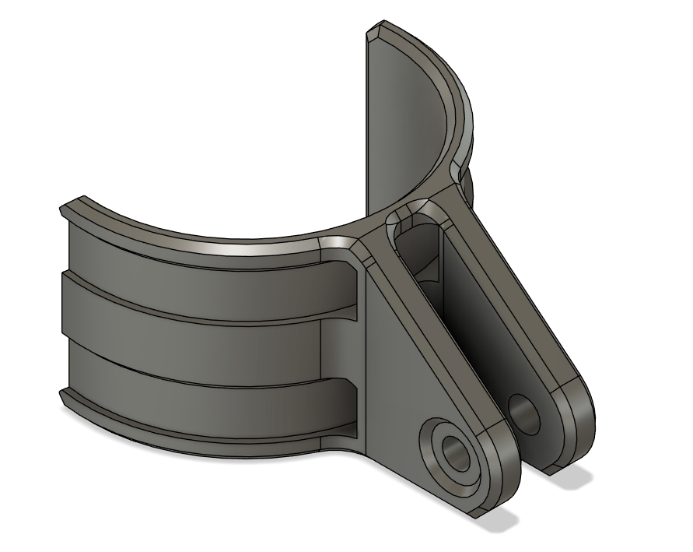
bodocs/src/assets/pics/bike-installation-guide/pot-upper-stanchion.png
