benconnor1972/BODAQS/bodocs/src/assets/pics/bike-installation-guide/pot-upper-steerer-install.JPG

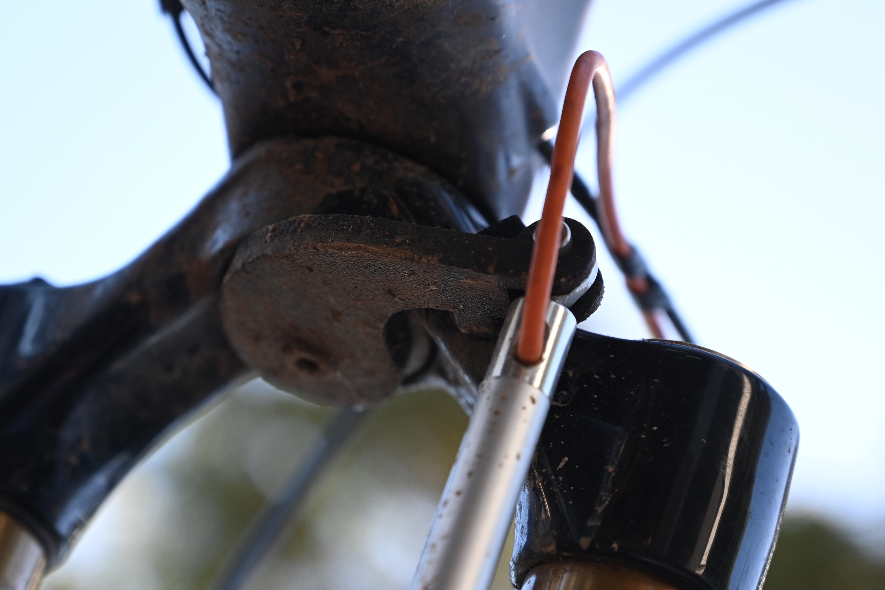
bodocs/src/assets/pics/bike-installation-guide/pot-upper-steerer-install.JPG
