benconnor1972/BODAQS/bodocs/src/assets/pics/bike-installation-guide/pot-upper-steerer.png

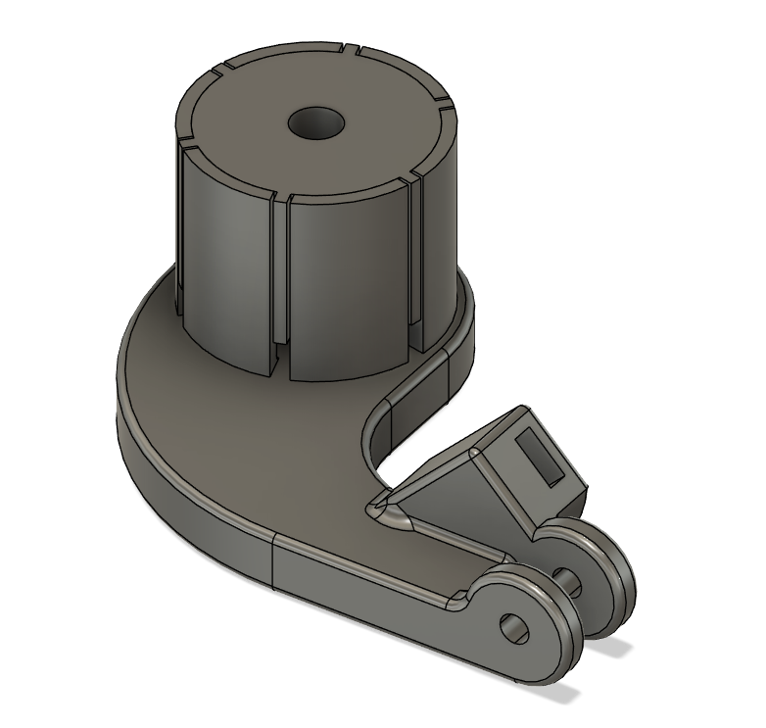
bodocs/src/assets/pics/bike-installation-guide/pot-upper-steerer.png
