benconnor1972/BODAQS/bodocs/src/assets/pics/Build-2.jpg

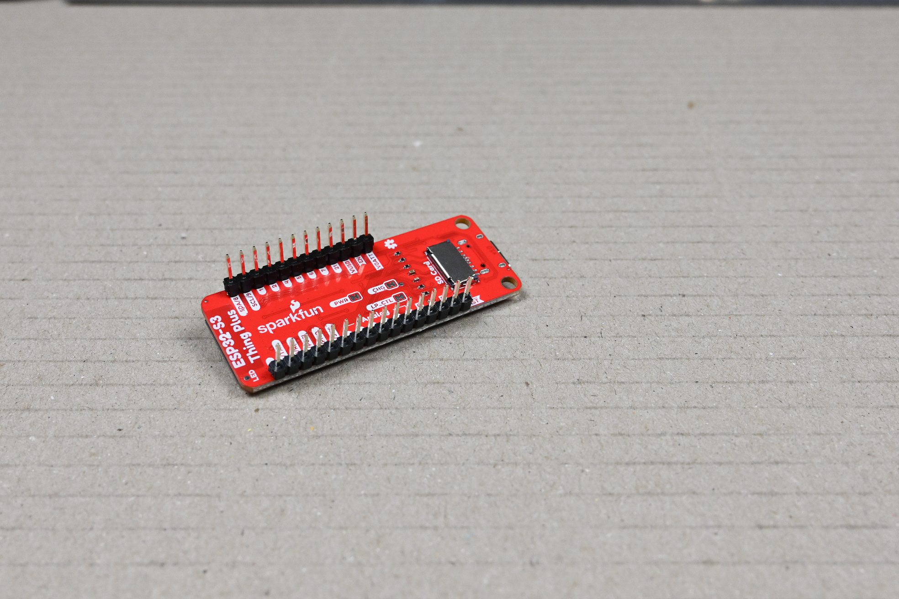
bodocs/src/assets/pics/Build-2.jpg
