benconnor1972/BODAQS/bodocs/src/assets/pics/Build-4E.JPG

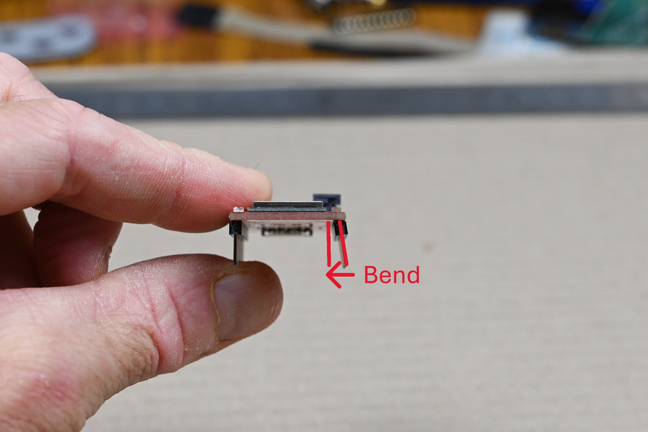
bodocs/src/assets/pics/Build-4E.JPG
