benconnor1972/BODAQS/bodocs/src/assets/pics/Build-5.jpg

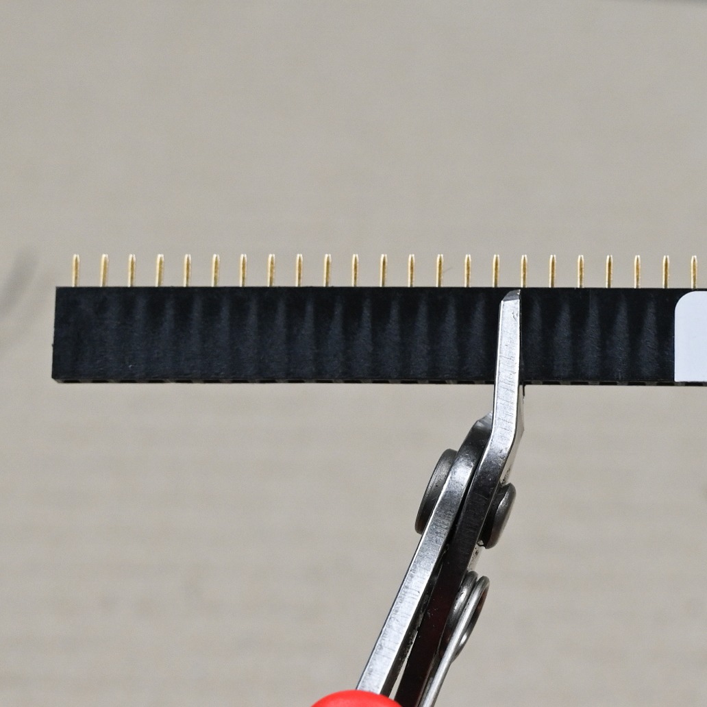
bodocs/src/assets/pics/Build-5.jpg
