benconnor1972/BODAQS/bodocs/src/assets/pics/Build-7A.jpg

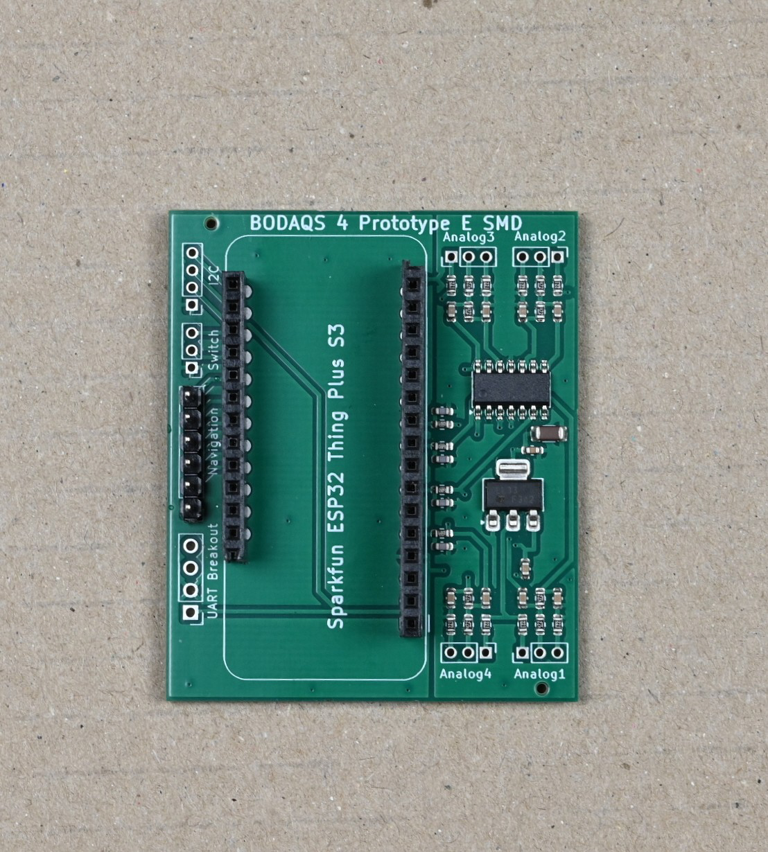
bodocs/src/assets/pics/Build-7A.jpg
