benconnor1972/BODAQS/bodocs/src/assets/pics/Build-7B.jpg

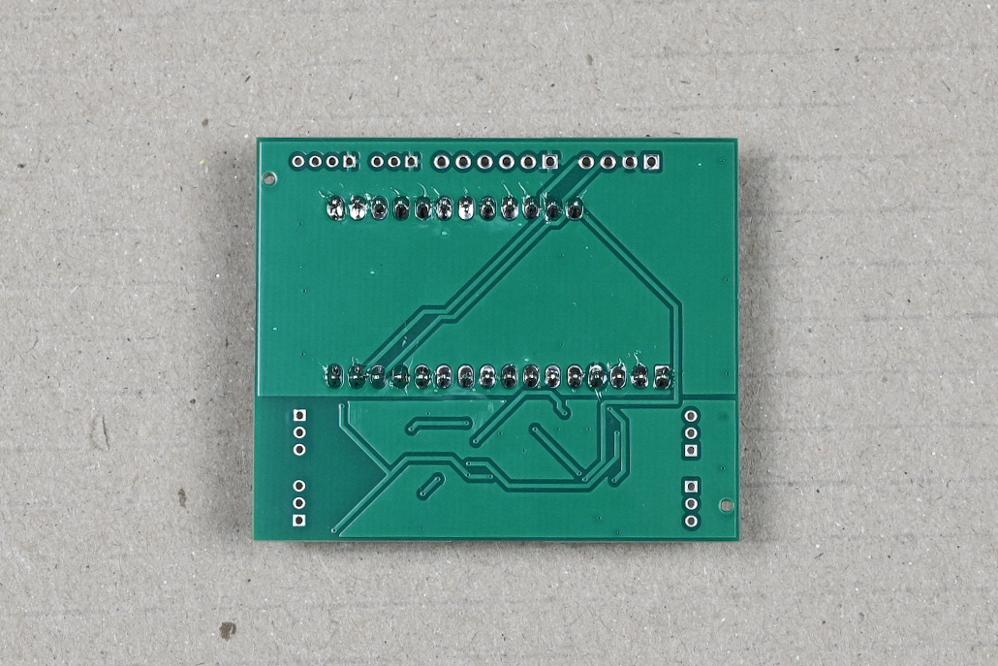
bodocs/src/assets/pics/Build-7B.jpg
