benconnor1972/BODAQS/bodocs/src/assets/pics/Build-8.jpg

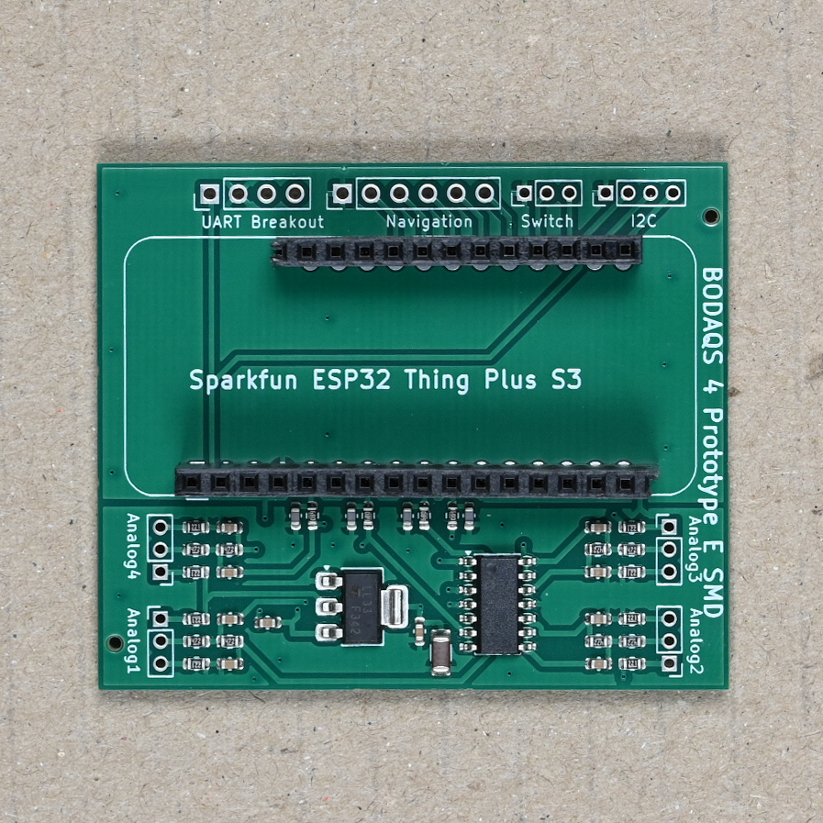
bodocs/src/assets/pics/Build-8.jpg
