benconnor1972/BODAQS/bodocs/src/assets/pics/Build-12AE.png

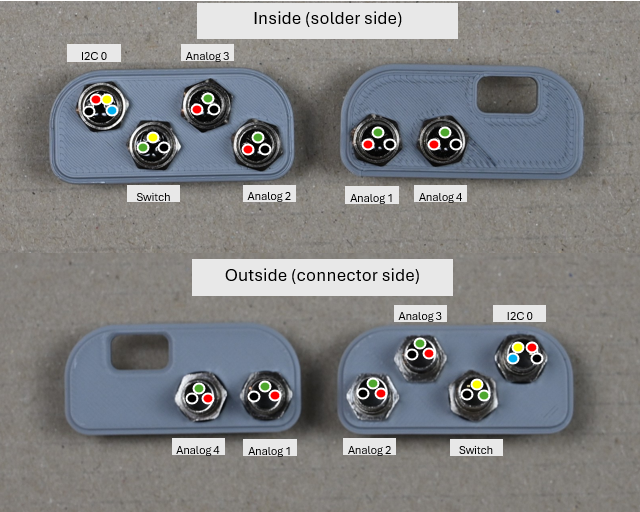
bodocs/src/assets/pics/Build-12AE.png
