benconnor1972/BODAQS/bodocs/src/assets/pics/Build-12E.png

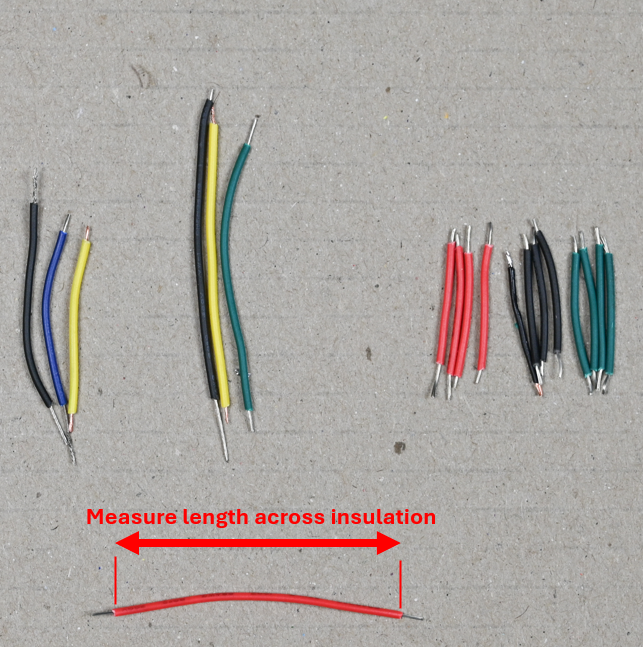
bodocs/src/assets/pics/Build-12E.png
