benconnor1972/BODAQS/bodocs/src/assets/pics/Build-15.jpg

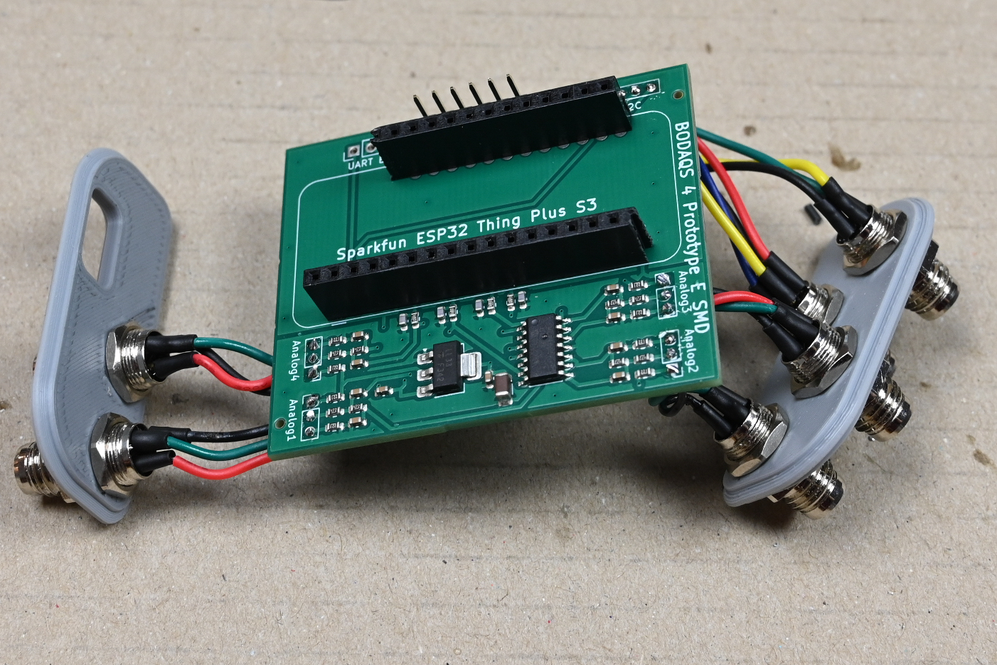
bodocs/src/assets/pics/Build-15.jpg
