benconnor1972/BODAQS/bodocs/src/assets/pics/Build-16.jpg

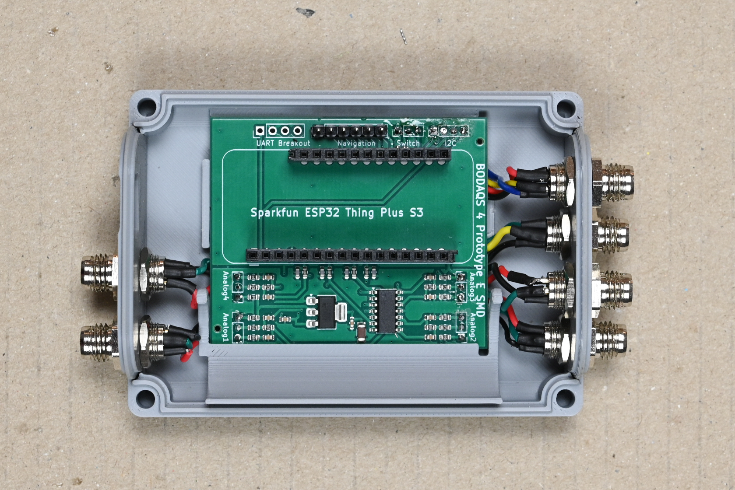
bodocs/src/assets/pics/Build-16.jpg
