benconnor1972/BODAQS/bodocs/src/assets/pics/Build-18.jpg

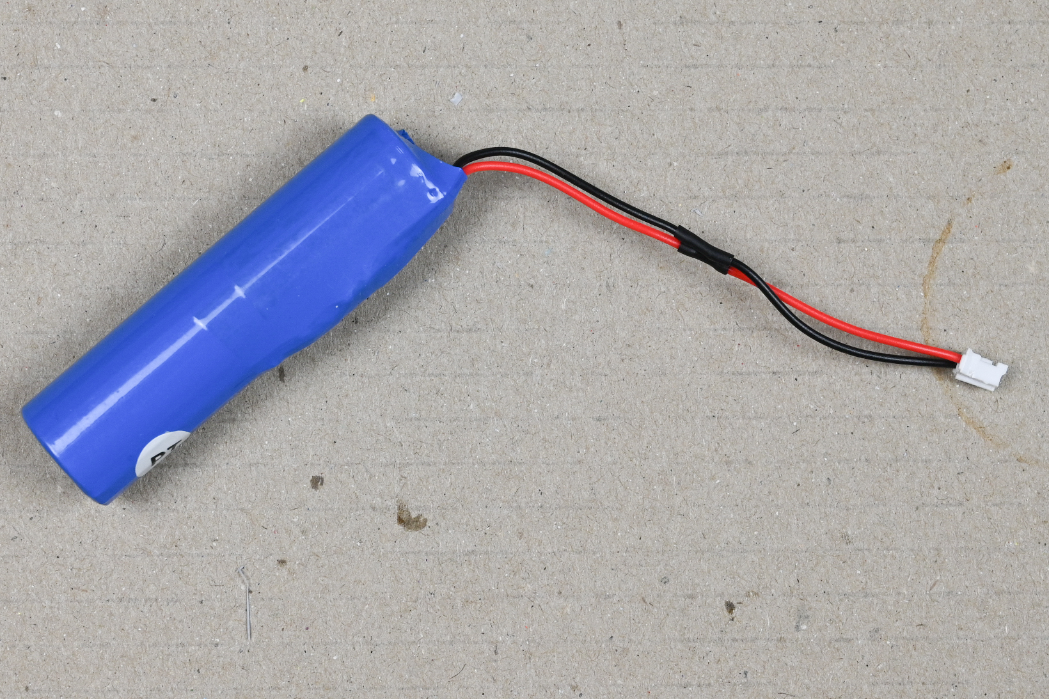
bodocs/src/assets/pics/Build-18.jpg
