benconnor1972/BODAQS/bodocs/src/assets/pics/Build-20.jpg

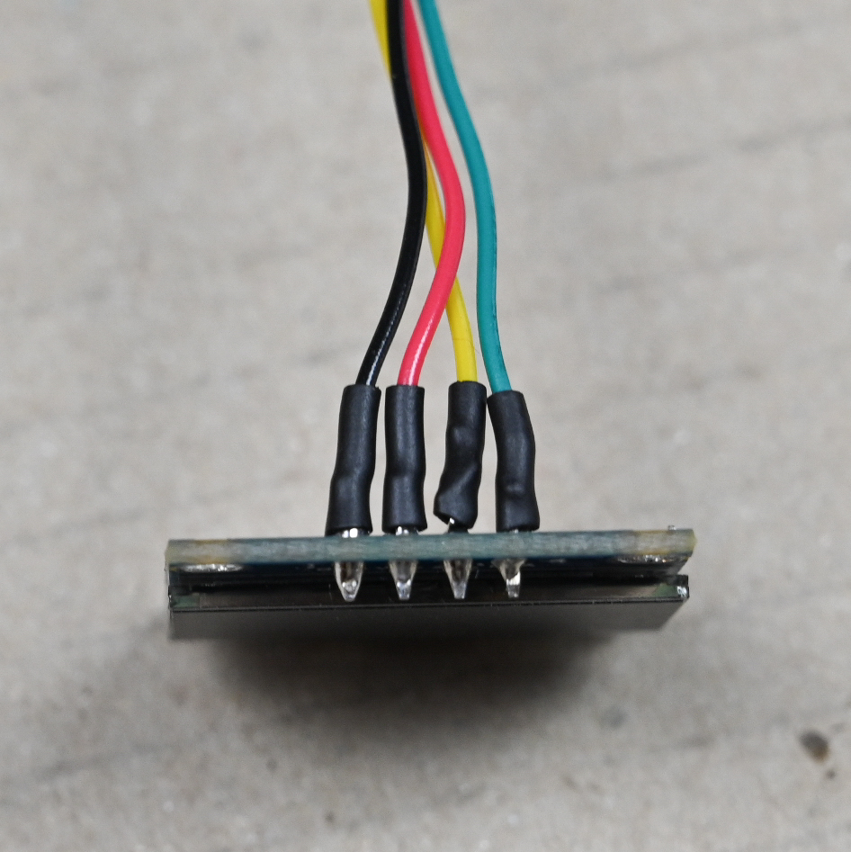
bodocs/src/assets/pics/Build-20.jpg
