benconnor1972/BODAQS/bodocs/src/assets/pics/Build-20E.png

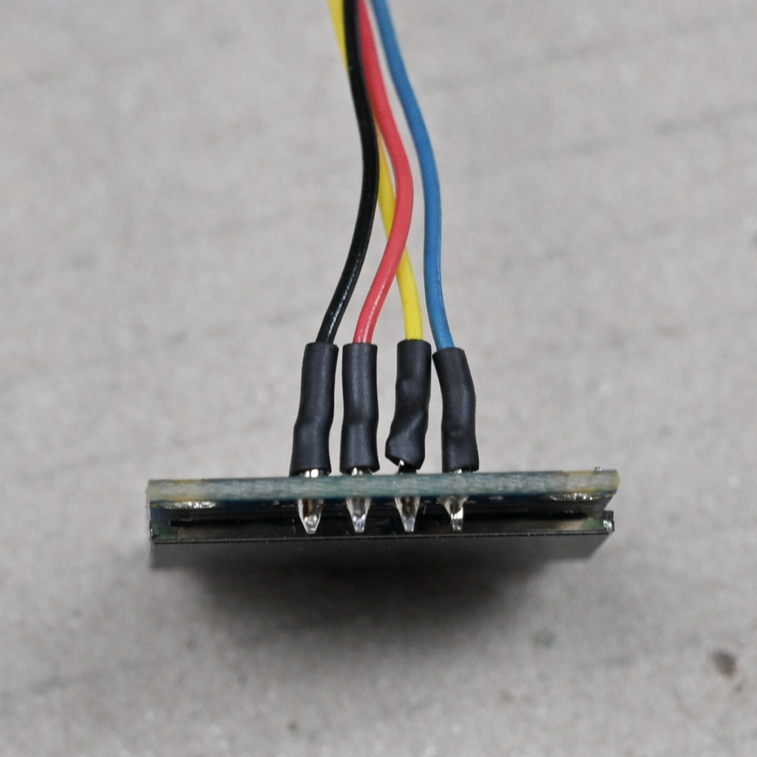
bodocs/src/assets/pics/Build-20E.png
