benconnor1972/BODAQS/bodocs/src/assets/pics/logger-build-guide/2ds-keypad.png

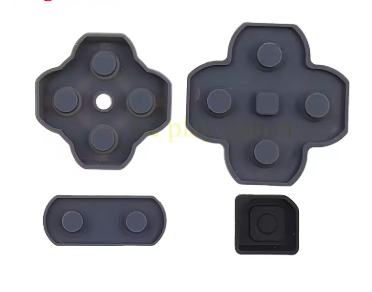
bodocs/src/assets/pics/logger-build-guide/2ds-keypad.png
