benconnor1972/BODAQS/bodocs/src/assets/pics/logger-build-guide/acrylic.png

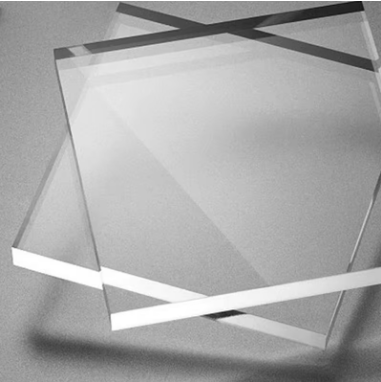
bodocs/src/assets/pics/logger-build-guide/acrylic.png
