benconnor1972/BODAQS/bodocs/src/assets/pics/logger-build-guide/base.png

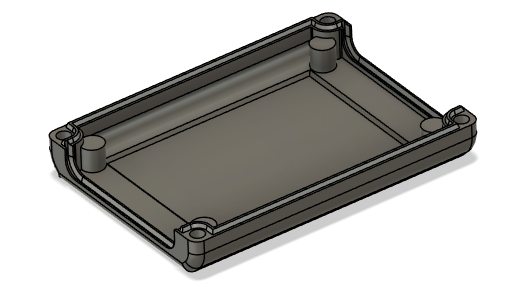
bodocs/src/assets/pics/logger-build-guide/base.png
