benconnor1972/BODAQS/bodocs/src/assets/pics/logger-build-guide/battery-a8.png

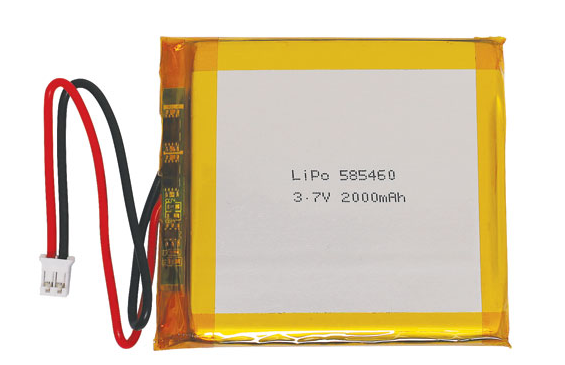
bodocs/src/assets/pics/logger-build-guide/battery-a8.png
