benconnor1972/BODAQS/bodocs/src/assets/pics/logger-build-guide/battery.png

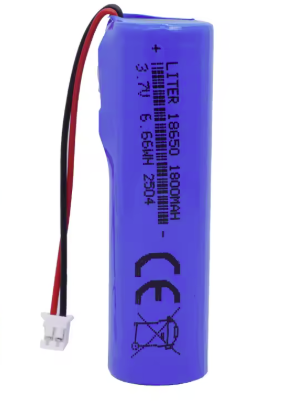
bodocs/src/assets/pics/logger-build-guide/battery.png
