benconnor1972/BODAQS/bodocs/src/assets/pics/logger-build-guide/bottom_end.png

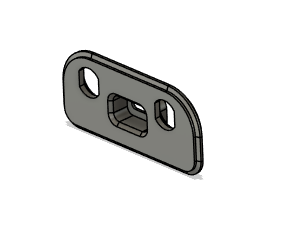
bodocs/src/assets/pics/logger-build-guide/bottom_end.png
