benconnor1972/BODAQS/bodocs/src/assets/pics/logger-build-guide/Build-5E.png

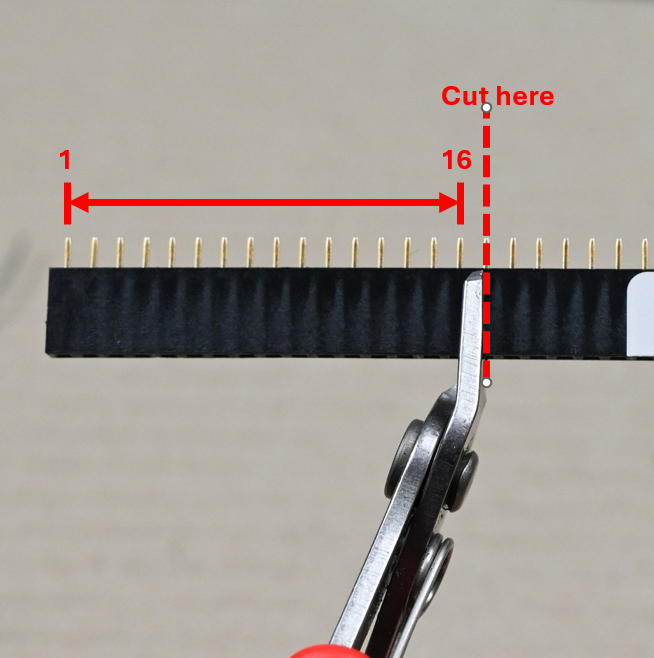
bodocs/src/assets/pics/logger-build-guide/Build-5E.png
