benconnor1972/BODAQS/bodocs/src/assets/pics/logger-build-guide/Build-7BE.png

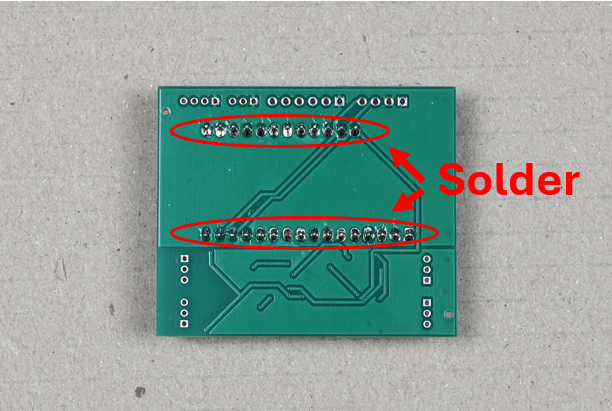
bodocs/src/assets/pics/logger-build-guide/Build-7BE.png
