benconnor1972/BODAQS/bodocs/src/assets/pics/logger-build-guide/Build-10.jpg

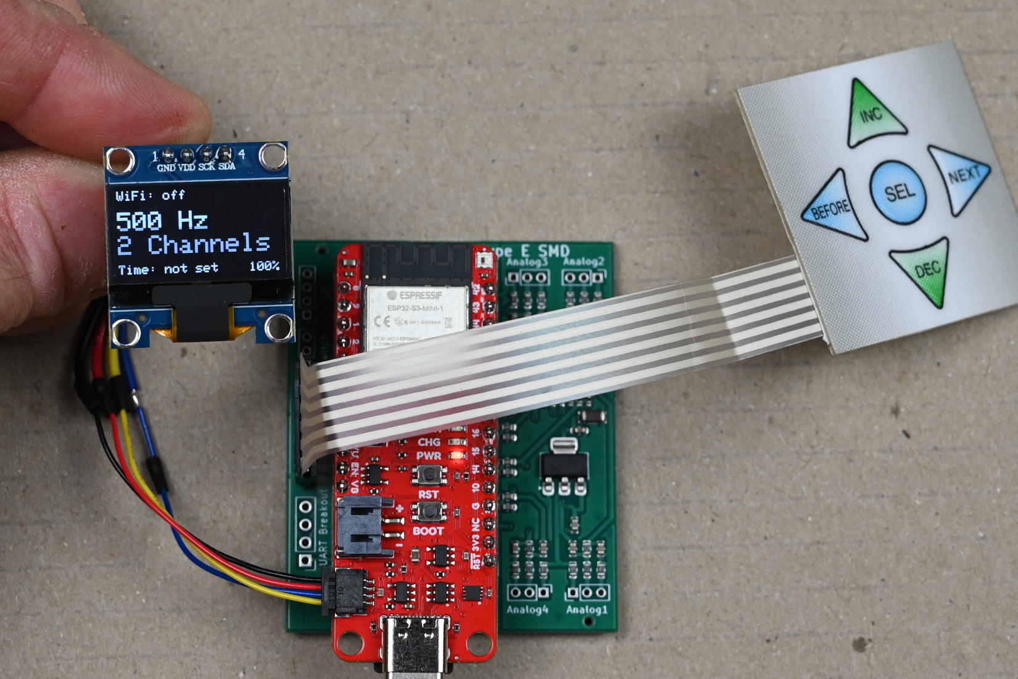
bodocs/src/assets/pics/logger-build-guide/Build-10.jpg
