benconnor1972/BODAQS/bodocs/src/assets/pics/logger-build-guide/Build-11.jpg

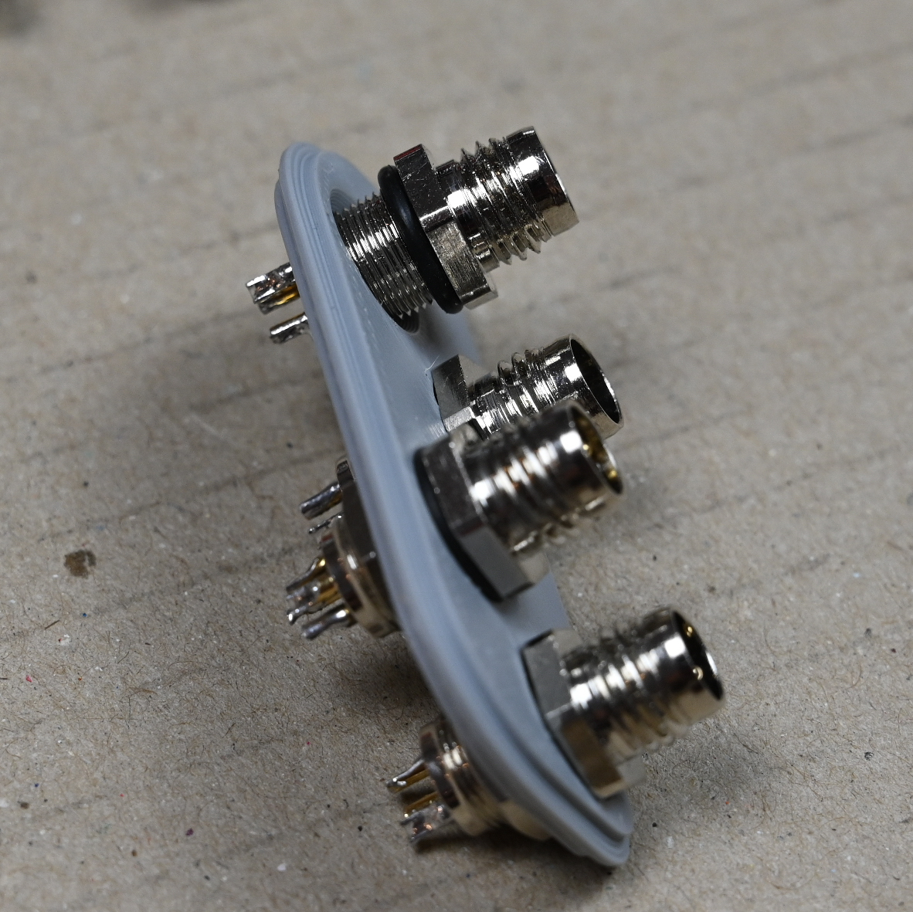
bodocs/src/assets/pics/logger-build-guide/Build-11.jpg
