benconnor1972/BODAQS/bodocs/src/assets/pics/logger-build-guide/Build-12AF.png

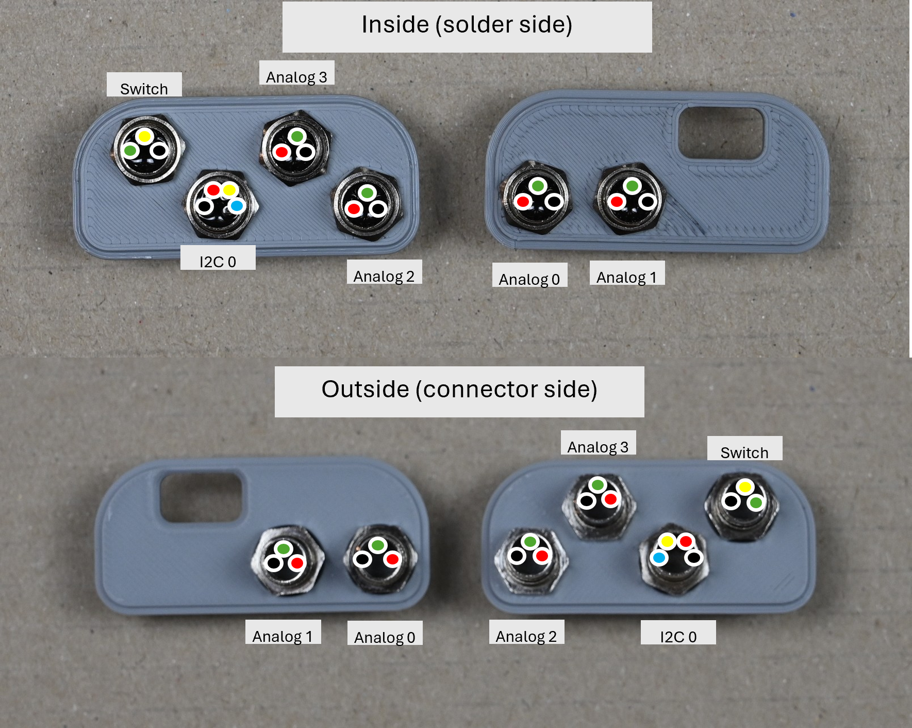
bodocs/src/assets/pics/logger-build-guide/Build-12AF.png
