benconnor1972/BODAQS/bodocs/src/assets/pics/logger-build-guide/Build-14.jpg

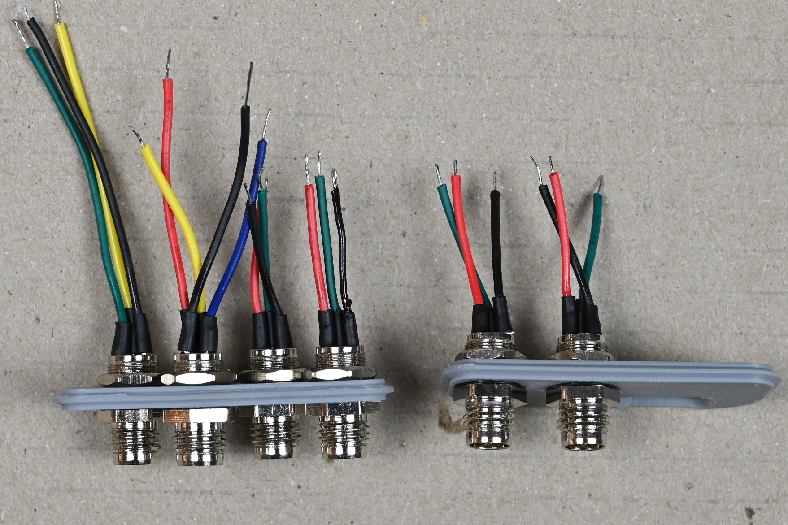
bodocs/src/assets/pics/logger-build-guide/Build-14.jpg
