benconnor1972/BODAQS/bodocs/src/assets/pics/logger-build-guide/Build-16F.jpg

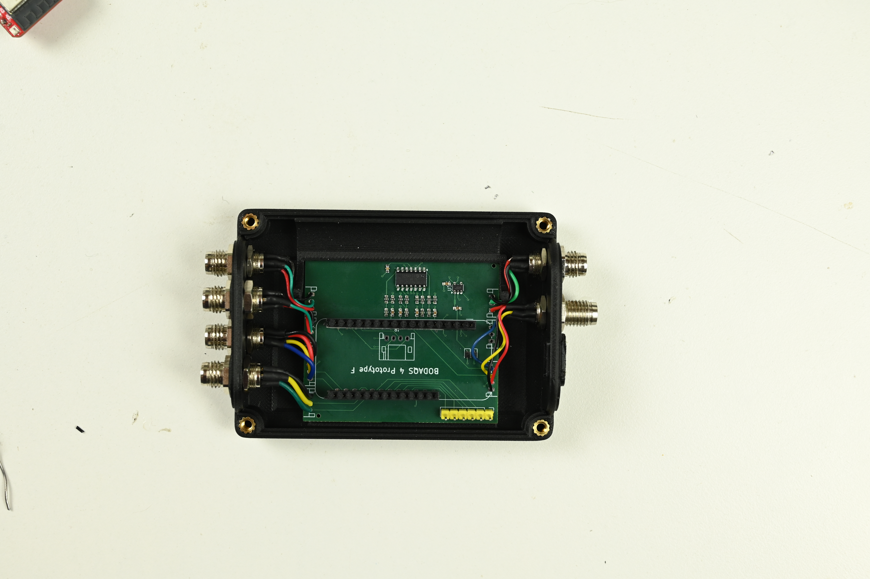
bodocs/src/assets/pics/logger-build-guide/Build-16F.jpg
