benconnor1972/BODAQS/bodocs/src/assets/pics/logger-build-guide/Build-18A.png

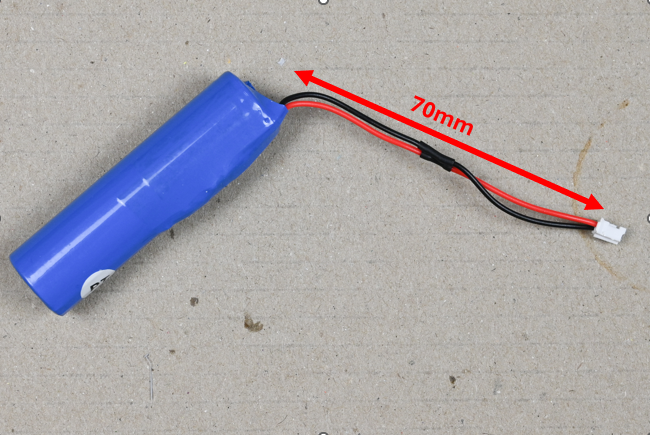
bodocs/src/assets/pics/logger-build-guide/Build-18A.png
