benconnor1972/BODAQS/bodocs/src/assets/pics/logger-build-guide/Build-20E2.png

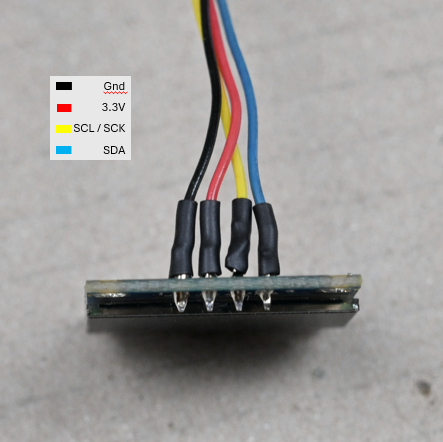
bodocs/src/assets/pics/logger-build-guide/Build-20E2.png
