benconnor1972/BODAQS/bodocs/src/assets/pics/logger-build-guide/build-a8-14.png

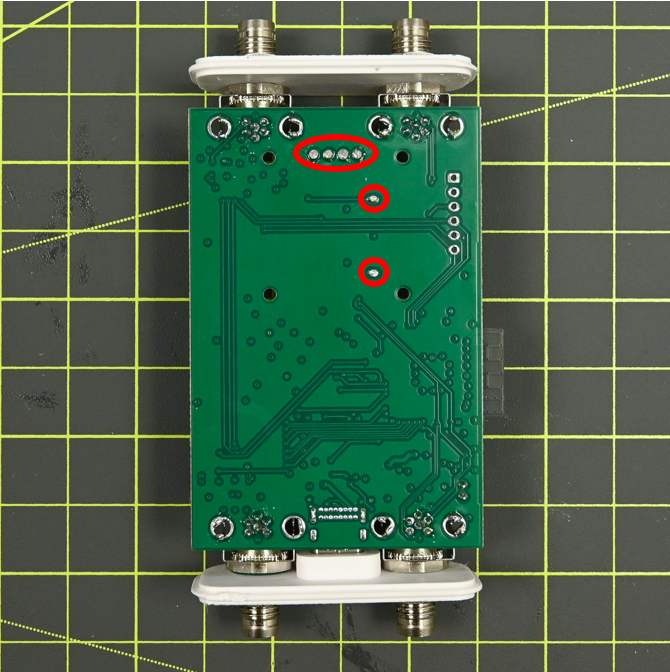
bodocs/src/assets/pics/logger-build-guide/build-a8-14.png
