benconnor1972/BODAQS/bodocs/src/assets/pics/logger-build-guide/Build-overview.png

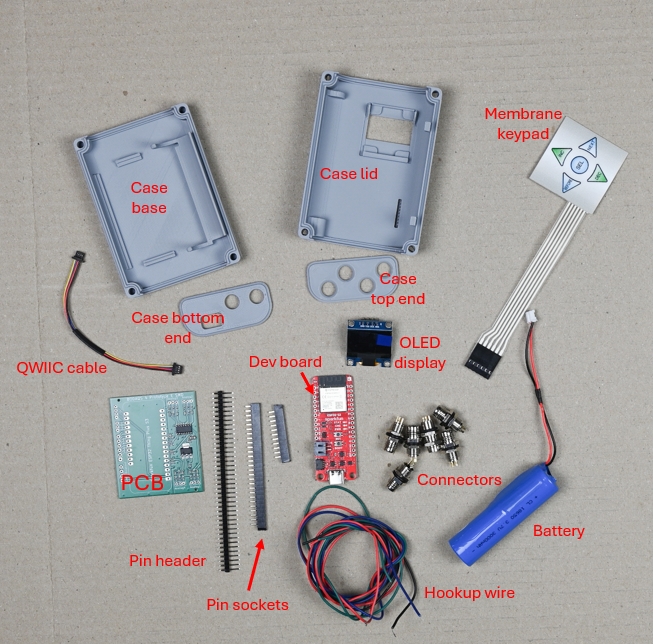
bodocs/src/assets/pics/logger-build-guide/Build-overview.png
