benconnor1972/BODAQS/bodocs/src/assets/pics/logger-build-guide/cap.png

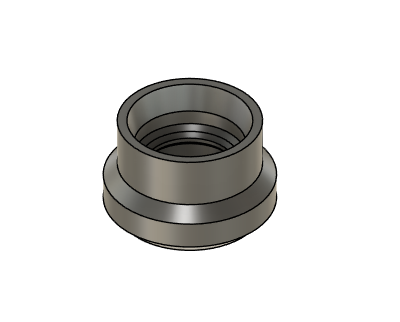
bodocs/src/assets/pics/logger-build-guide/cap.png
