benconnor1972/BODAQS/bodocs/src/assets/pics/logger-build-guide/config-2.png

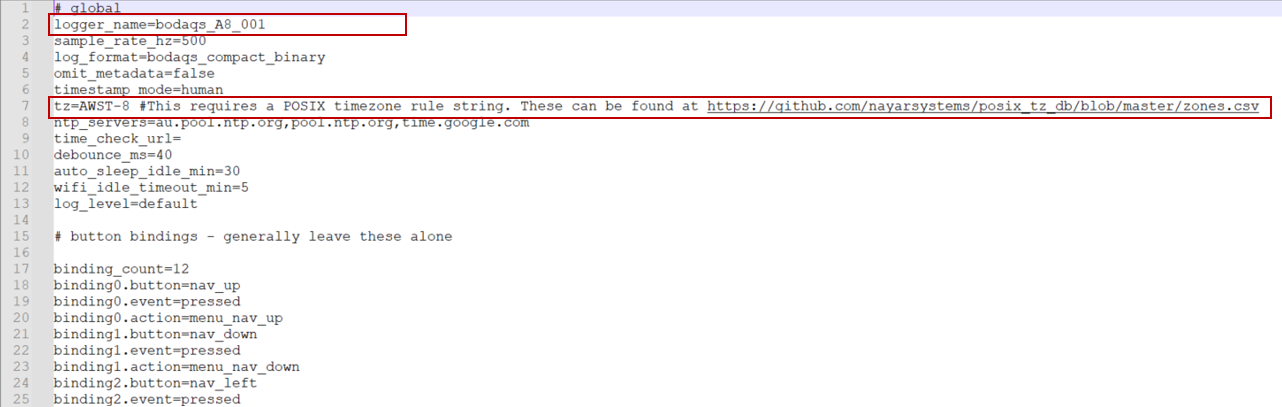
bodocs/src/assets/pics/logger-build-guide/config-2.png
