benconnor1972/BODAQS/bodocs/src/assets/pics/logger-build-guide/config-3.png

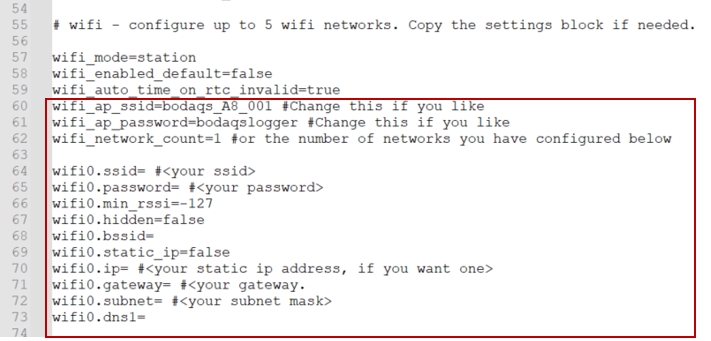
bodocs/src/assets/pics/logger-build-guide/config-3.png
