benconnor1972/BODAQS/bodocs/src/assets/pics/logger-build-guide/correct_polarity.png

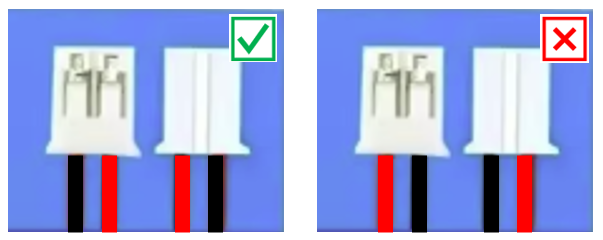
bodocs/src/assets/pics/logger-build-guide/correct_polarity.png
