benconnor1972/BODAQS/bodocs/src/assets/pics/logger-build-guide/downtube_mount.png

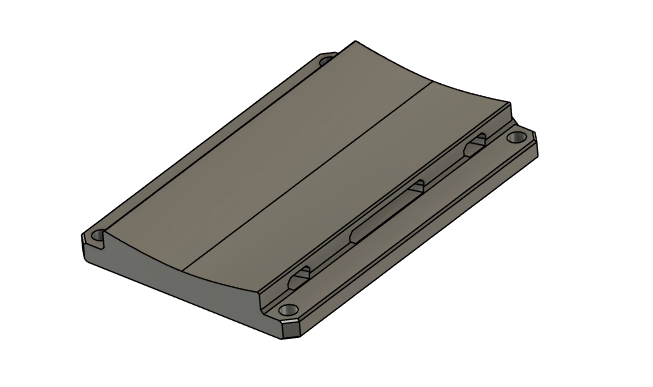
bodocs/src/assets/pics/logger-build-guide/downtube_mount.png
