benconnor1972/BODAQS/bodocs/src/assets/pics/logger-build-guide/DSC_8509.png

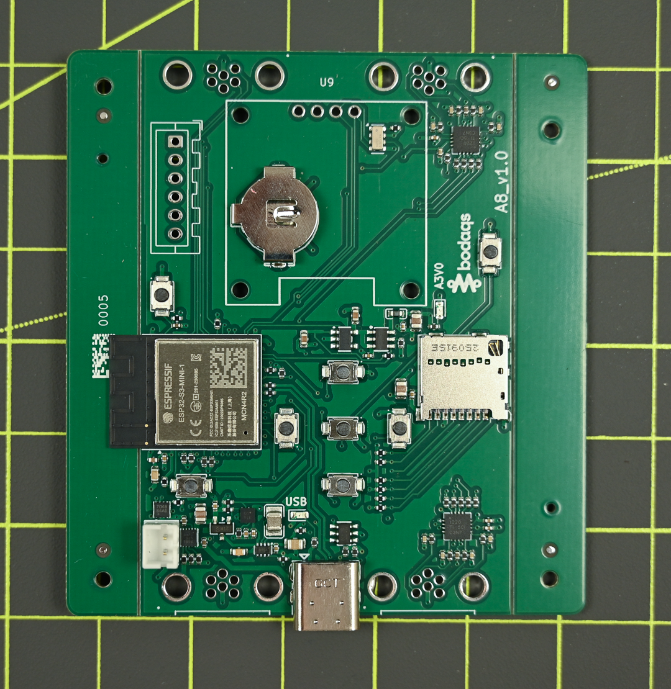
bodocs/src/assets/pics/logger-build-guide/DSC_8509.png
