benconnor1972/BODAQS/bodocs/src/assets/pics/logger-build-guide/DSC_8511.png

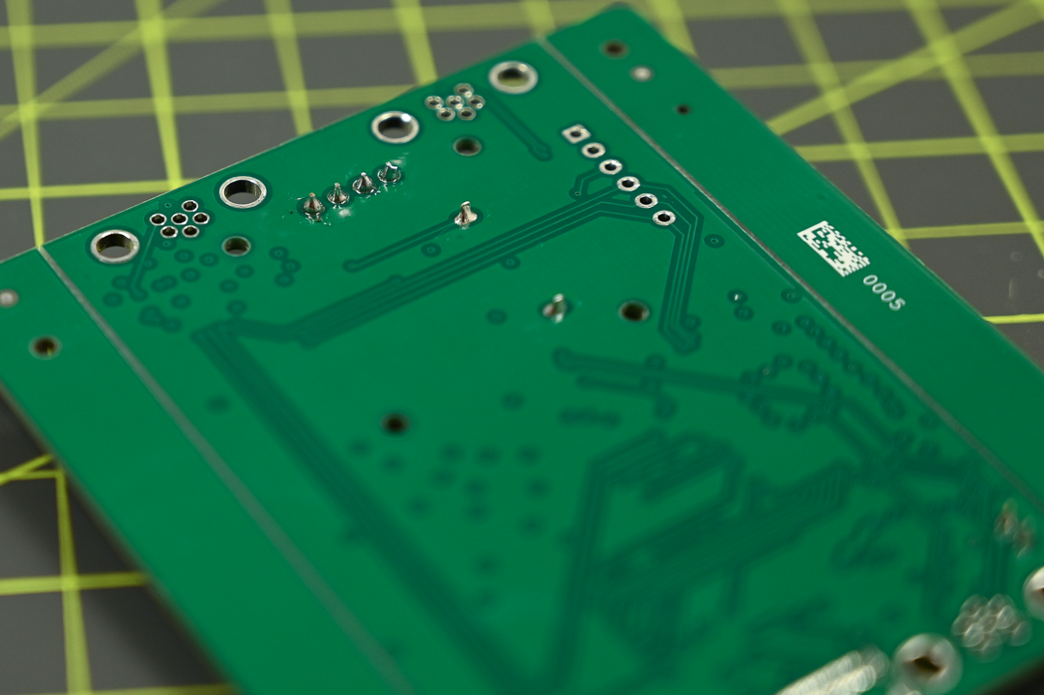
bodocs/src/assets/pics/logger-build-guide/DSC_8511.png
