benconnor1972/BODAQS/bodocs/src/assets/pics/logger-build-guide/DSC_8533.png

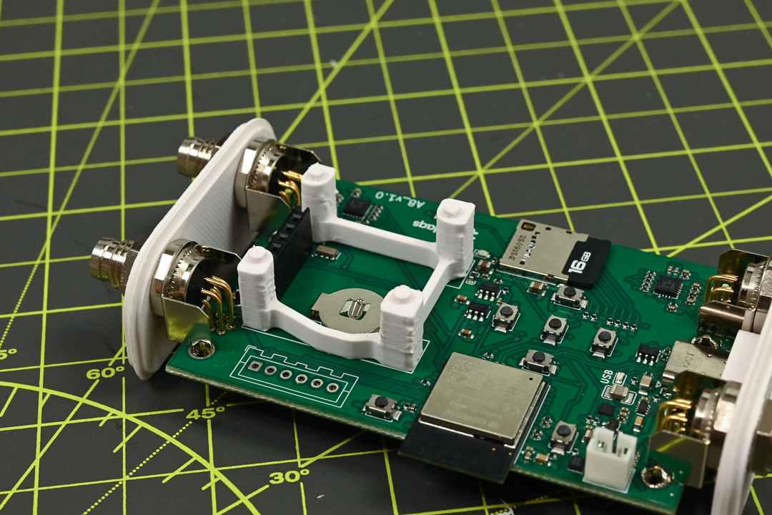
bodocs/src/assets/pics/logger-build-guide/DSC_8533.png
