benconnor1972/BODAQS/bodocs/src/assets/pics/logger-build-guide/f_vs_a8_outside.jpg

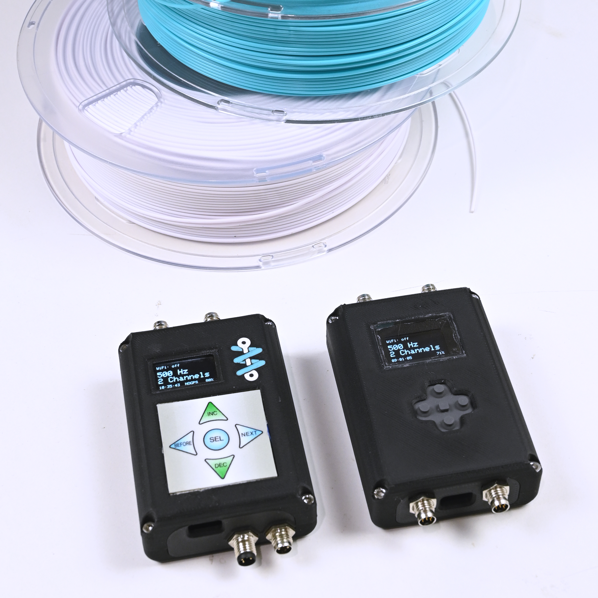
bodocs/src/assets/pics/logger-build-guide/f_vs_a8_outside.jpg
