benconnor1972/BODAQS/bodocs/src/assets/pics/logger-build-guide/flash-2_proto_f.png

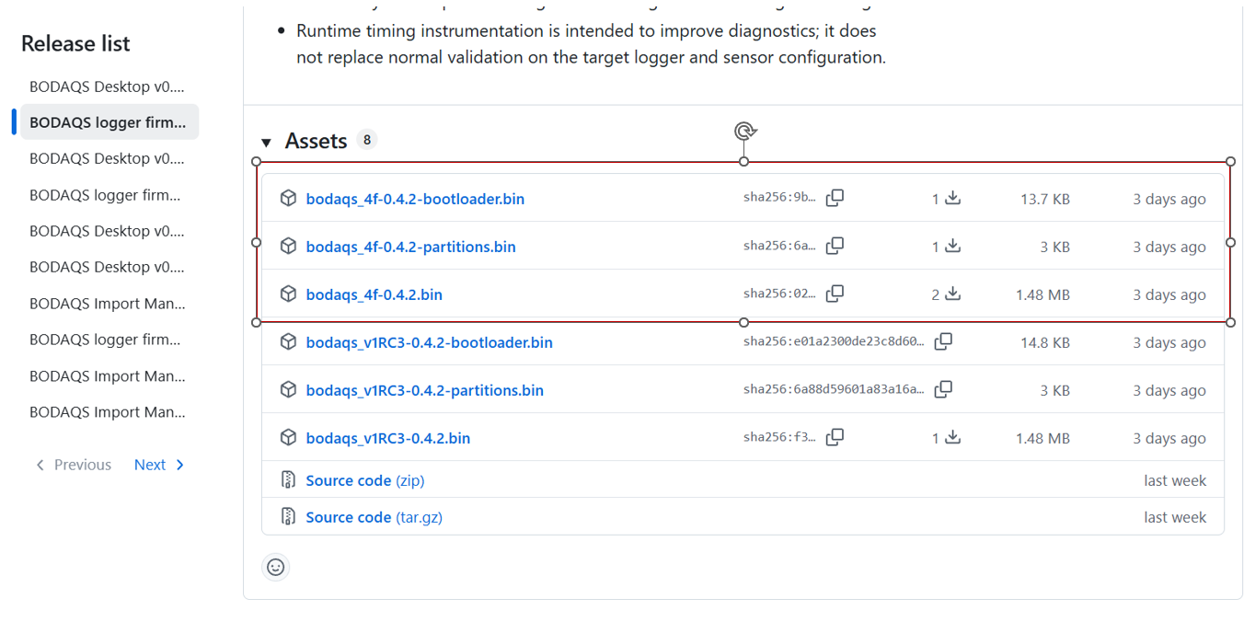
bodocs/src/assets/pics/logger-build-guide/flash-2_proto_f.png
