benconnor1972/BODAQS/bodocs/src/assets/pics/logger-build-guide/flash-4a.png

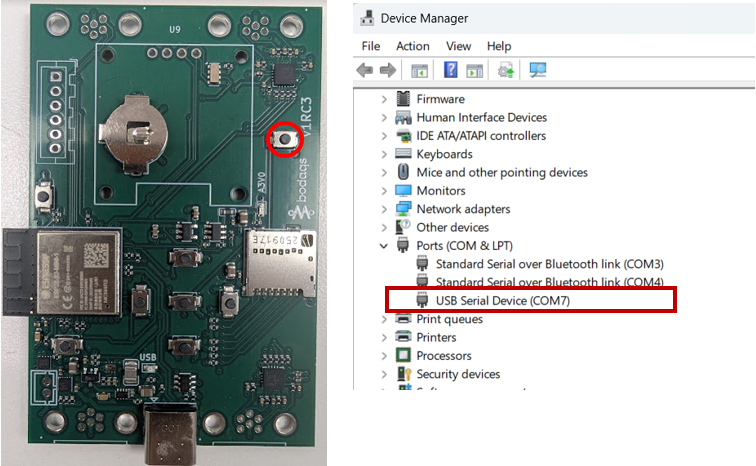
bodocs/src/assets/pics/logger-build-guide/flash-4a.png
