benconnor1972/BODAQS/bodocs/src/assets/pics/logger-build-guide/flash-6.png

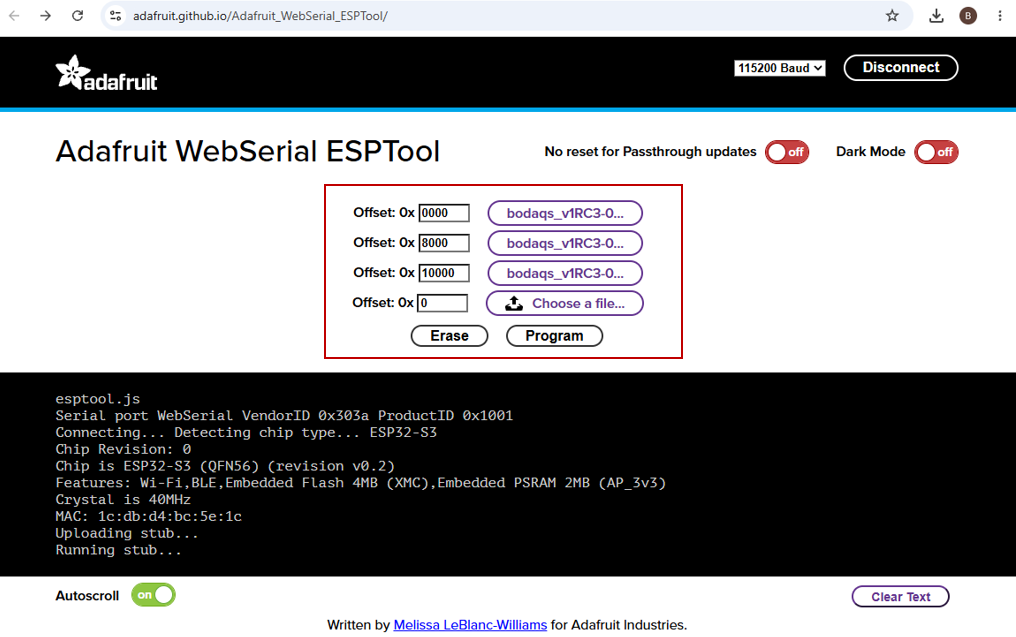
bodocs/src/assets/pics/logger-build-guide/flash-6.png
