benconnor1972/BODAQS/bodocs/src/assets/pics/logger-build-guide/flash-8_a8.png

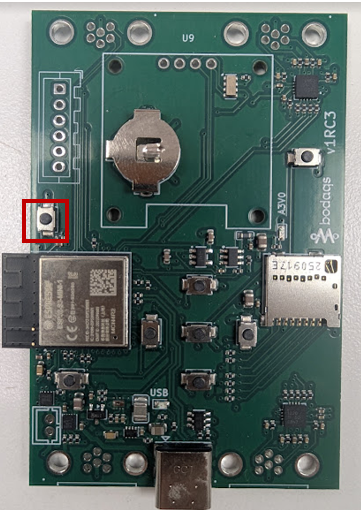
bodocs/src/assets/pics/logger-build-guide/flash-8_a8.png
