benconnor1972/BODAQS/bodocs/src/assets/pics/logger-build-guide/format.png

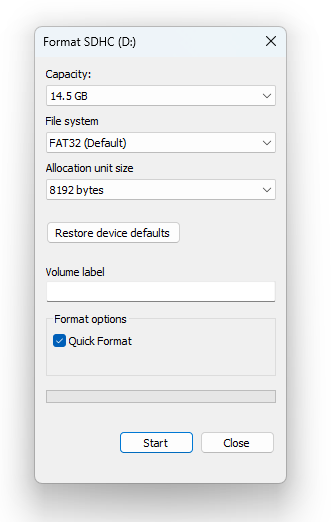
bodocs/src/assets/pics/logger-build-guide/format.png
