benconnor1972/BODAQS/bodocs/src/assets/pics/logger-build-guide/header-socket.png

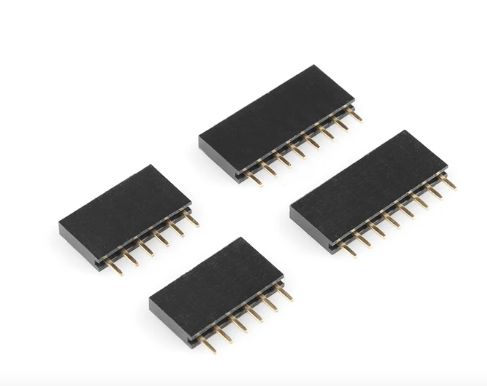
bodocs/src/assets/pics/logger-build-guide/header-socket.png
