benconnor1972/BODAQS/bodocs/src/assets/pics/logger-build-guide/hot_air.png

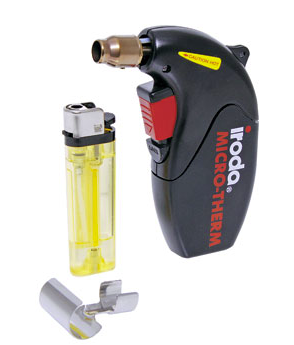
bodocs/src/assets/pics/logger-build-guide/hot_air.png
