benconnor1972/BODAQS/bodocs/src/assets/pics/logger-build-guide/keypad.png

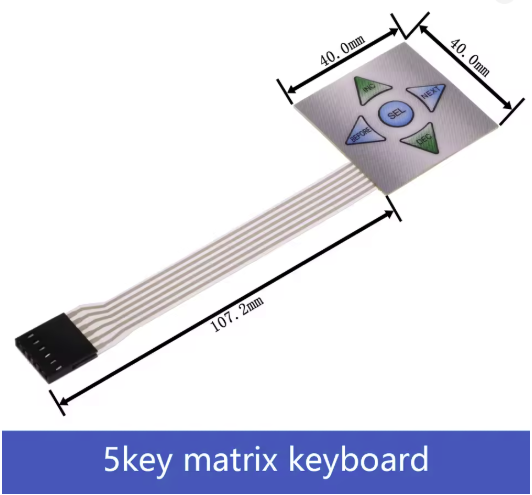
bodocs/src/assets/pics/logger-build-guide/keypad.png
