benconnor1972/BODAQS/bodocs/src/assets/pics/logger-build-guide/lid.png

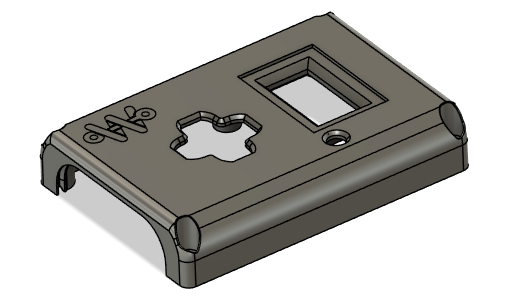
bodocs/src/assets/pics/logger-build-guide/lid.png
