benconnor1972/BODAQS/bodocs/src/assets/pics/logger-build-guide/linear_pots.png

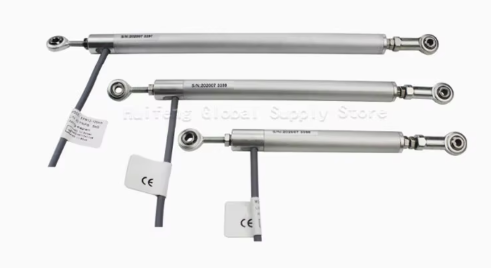
bodocs/src/assets/pics/logger-build-guide/linear_pots.png
