benconnor1972/BODAQS/bodocs/src/assets/pics/logger-build-guide/male_4_pin.png

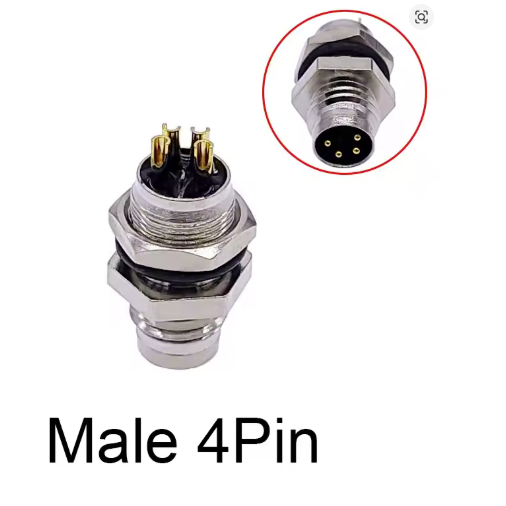
bodocs/src/assets/pics/logger-build-guide/male_4_pin.png
