benconnor1972/BODAQS/bodocs/src/assets/pics/logger-build-guide/male_6_pin.png

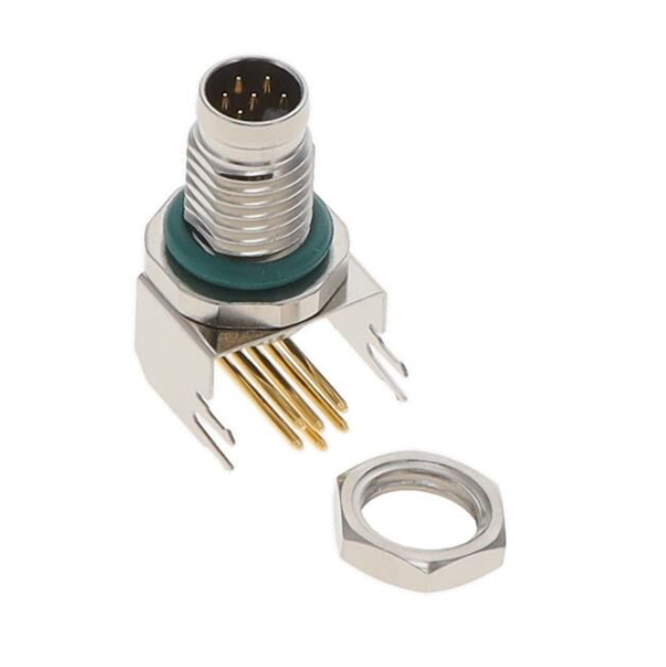
bodocs/src/assets/pics/logger-build-guide/male_6_pin.png
