benconnor1972/BODAQS/bodocs/src/assets/pics/logger-build-guide/microsd.png

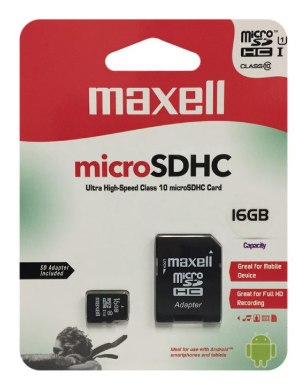
bodocs/src/assets/pics/logger-build-guide/microsd.png
