benconnor1972/BODAQS/bodocs/src/assets/pics/logger-build-guide/multimeter.png

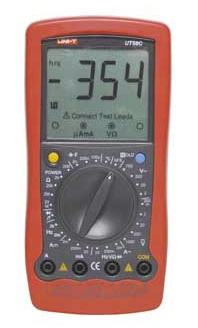
bodocs/src/assets/pics/logger-build-guide/multimeter.png
