benconnor1972/BODAQS/bodocs/src/assets/pics/logger-build-guide/nav_plate.png

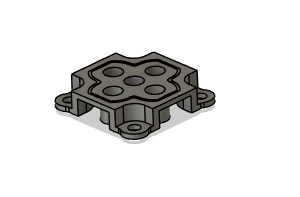
bodocs/src/assets/pics/logger-build-guide/nav_plate.png
