benconnor1972/BODAQS/bodocs/src/assets/pics/logger-build-guide/OLED-1E.png

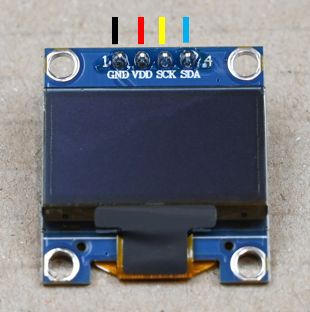
bodocs/src/assets/pics/logger-build-guide/OLED-1E.png
