benconnor1972/BODAQS/bodocs/src/assets/pics/logger-build-guide/OLED-5.png

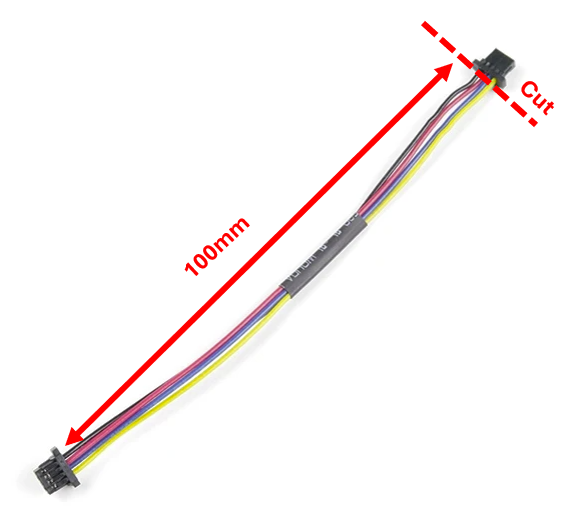
bodocs/src/assets/pics/logger-build-guide/OLED-5.png
