benconnor1972/BODAQS/bodocs/src/assets/pics/logger-build-guide/OLED.png

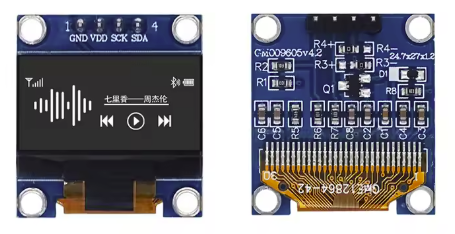
bodocs/src/assets/pics/logger-build-guide/OLED.png
