benconnor1972/BODAQS/bodocs/src/assets/pics/logger-build-guide/OLED_dims.png

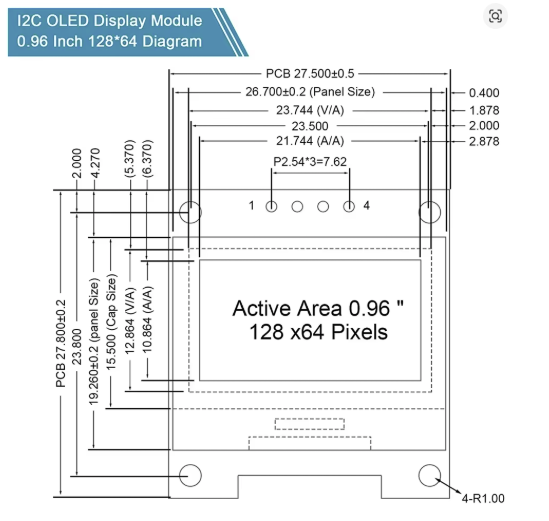
bodocs/src/assets/pics/logger-build-guide/OLED_dims.png
