benconnor1972/BODAQS/bodocs/src/assets/pics/logger-build-guide/oled_spacer.png

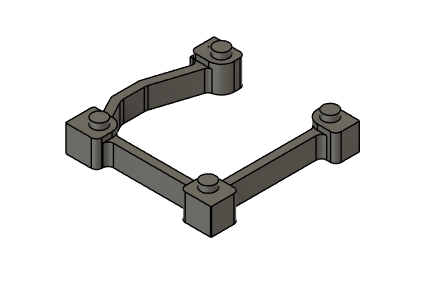
bodocs/src/assets/pics/logger-build-guide/oled_spacer.png
