benconnor1972/BODAQS/bodocs/src/assets/pics/logger-build-guide/pin.png

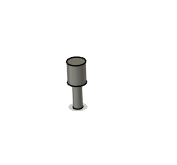
bodocs/src/assets/pics/logger-build-guide/pin.png
