benconnor1972/BODAQS/bodocs/src/assets/pics/logger-build-guide/Pins_1.jpg

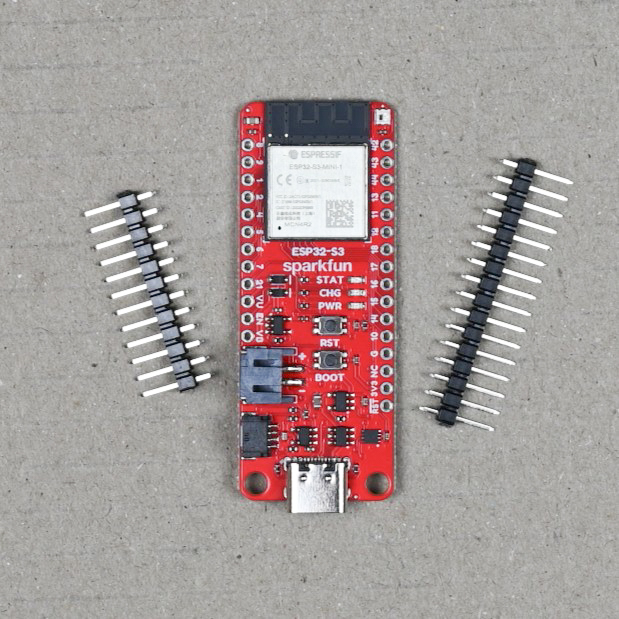
bodocs/src/assets/pics/logger-build-guide/Pins_1.jpg
