benconnor1972/BODAQS/bodocs/src/assets/pics/logger-build-guide/plug.png

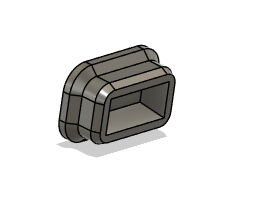
bodocs/src/assets/pics/logger-build-guide/plug.png
