benconnor1972/BODAQS/bodocs/src/assets/pics/logger-build-guide/plugs.png

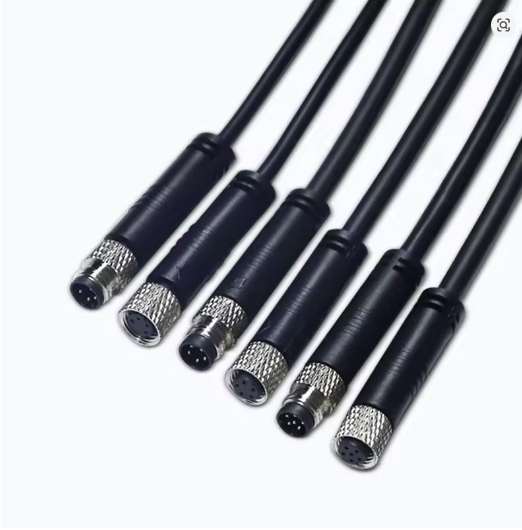
bodocs/src/assets/pics/logger-build-guide/plugs.png
