benconnor1972/BODAQS/bodocs/src/assets/pics/logger-build-guide/plugs_a8.png

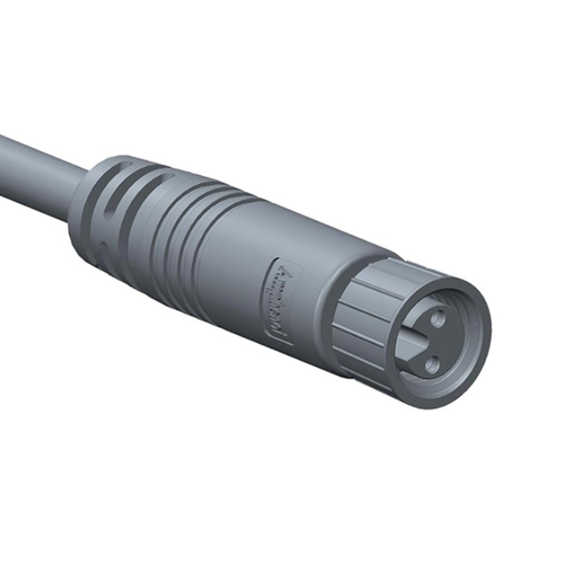
bodocs/src/assets/pics/logger-build-guide/plugs_a8.png
