benconnor1972/BODAQS/bodocs/src/assets/pics/logger-build-guide/plugs_ebike.png

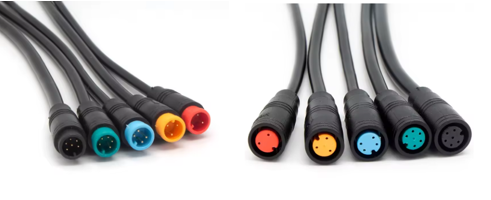
bodocs/src/assets/pics/logger-build-guide/plugs_ebike.png
