benconnor1972/BODAQS/bodocs/src/assets/pics/logger-build-guide/power_plate.png

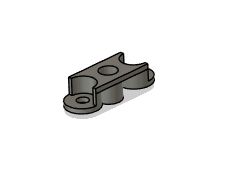
bodocs/src/assets/pics/logger-build-guide/power_plate.png
