benconnor1972/BODAQS/bodocs/src/assets/pics/logger-build-guide/print-case.png

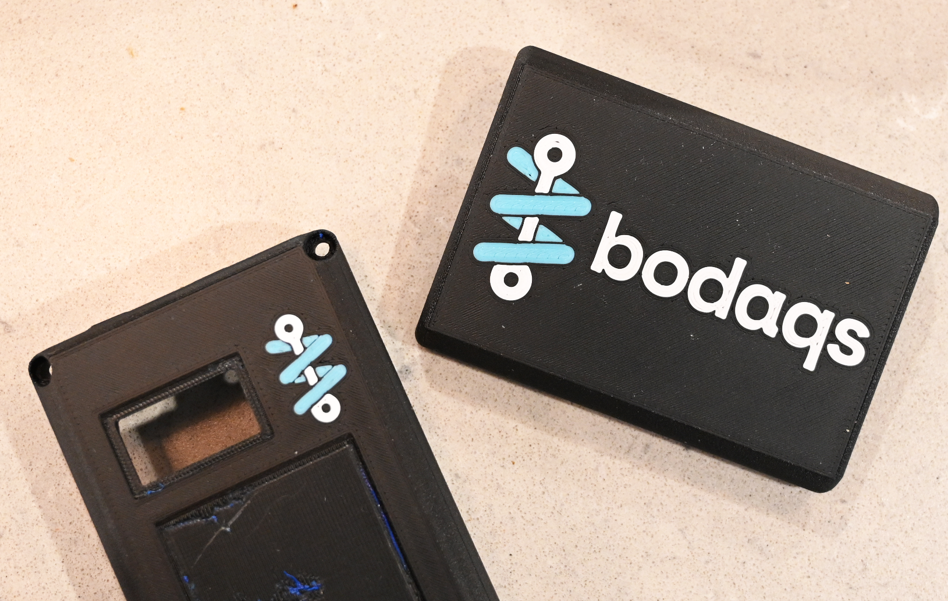
bodocs/src/assets/pics/logger-build-guide/print-case.png
