benconnor1972/BODAQS/bodocs/src/assets/pics/logger-build-guide/print-plate.png

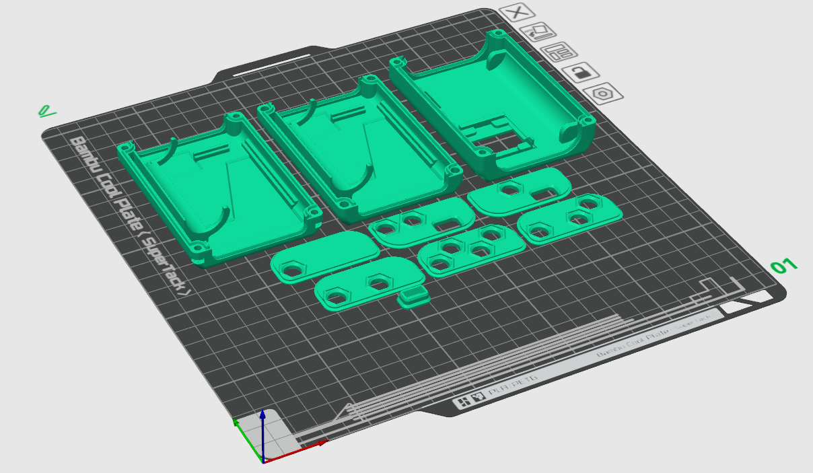
bodocs/src/assets/pics/logger-build-guide/print-plate.png
