benconnor1972/BODAQS/bodocs/src/assets/pics/logger-build-guide/qwiic.png

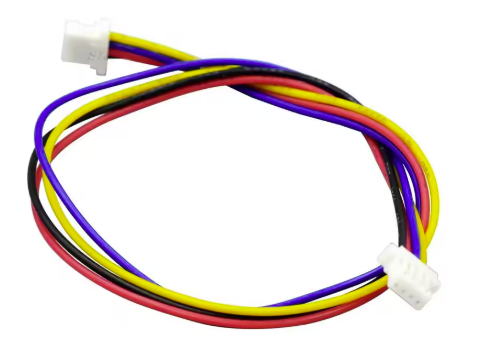
bodocs/src/assets/pics/logger-build-guide/qwiic.png
