benconnor1972/BODAQS/bodocs/src/assets/pics/logger-build-guide/sd-slot_proto_f.png

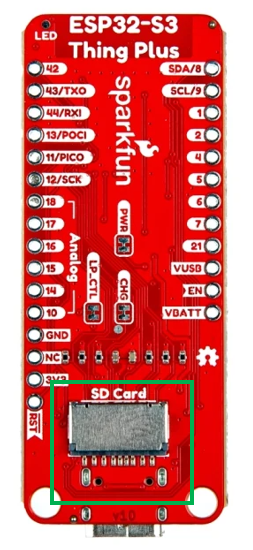
bodocs/src/assets/pics/logger-build-guide/sd-slot_proto_f.png
