benconnor1972/BODAQS/bodocs/src/assets/pics/logger-build-guide/shrink.png

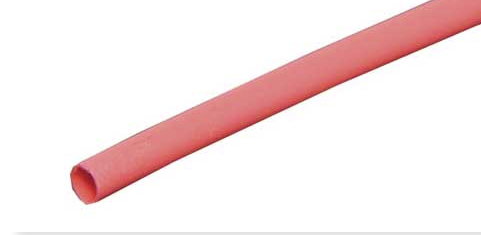
bodocs/src/assets/pics/logger-build-guide/shrink.png
