benconnor1972/BODAQS/bodocs/src/assets/pics/logger-build-guide/sidecutters.png

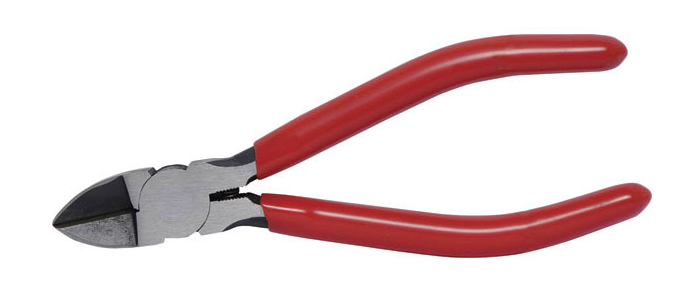
bodocs/src/assets/pics/logger-build-guide/sidecutters.png
