benconnor1972/BODAQS/bodocs/src/assets/pics/logger-build-guide/soldering_iron_1.png

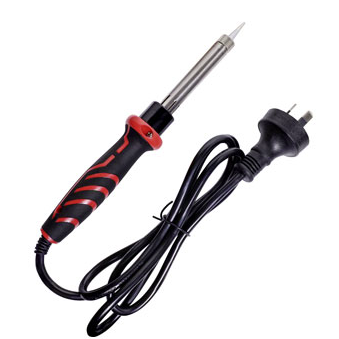
bodocs/src/assets/pics/logger-build-guide/soldering_iron_1.png
