benconnor1972/BODAQS/bodocs/src/assets/pics/logger-build-guide/soldering_iron_2.png

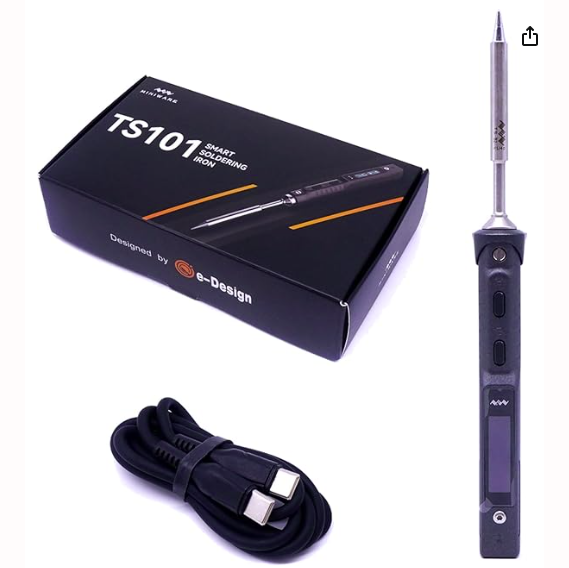
bodocs/src/assets/pics/logger-build-guide/soldering_iron_2.png
