benconnor1972/BODAQS/bodocs/src/assets/pics/logger-build-guide/thing_plus_s3.png

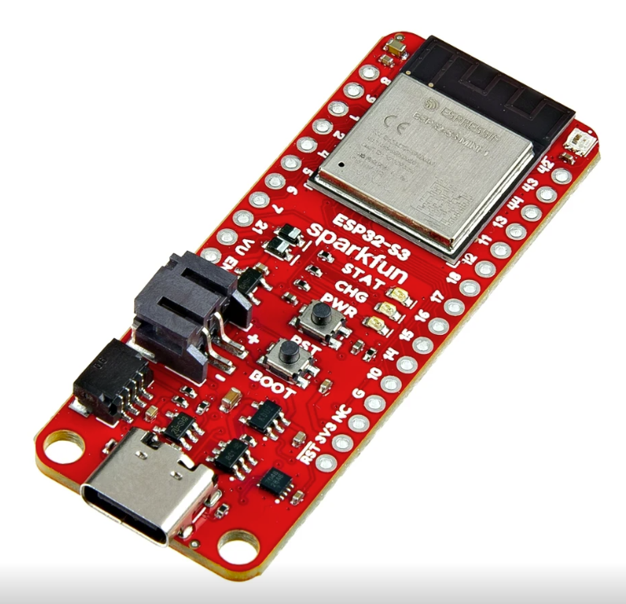
bodocs/src/assets/pics/logger-build-guide/thing_plus_s3.png
