benconnor1972/BODAQS/bodocs/src/assets/pics/logger-build-guide/top_end.png

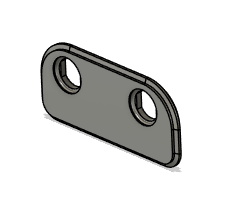
bodocs/src/assets/pics/logger-build-guide/top_end.png
