benconnor1972/BODAQS/bodocs/src/assets/pics/logger-build-guide/wire.png

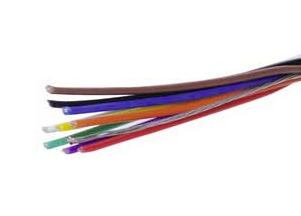
bodocs/src/assets/pics/logger-build-guide/wire.png
