benconnor1972/BODAQS/bodocs/src/assets/pics/logger-build-guide/wire_strippers.png

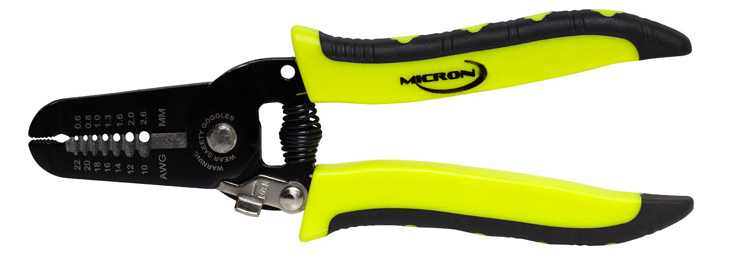
bodocs/src/assets/pics/logger-build-guide/wire_strippers.png
