benconnor1972/BODAQS/bodocs/src/assets/pics/logger-build-guide/work-in-progress.png

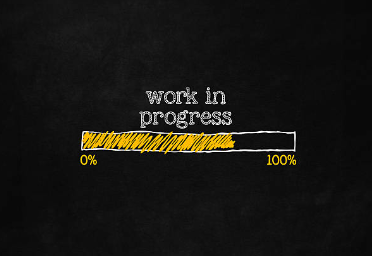
bodocs/src/assets/pics/logger-build-guide/work-in-progress.png
