benconnor1972/BODAQS/bodocs/src/assets/pics/sensor-connection-and-wiring-guide/a8-uart.png

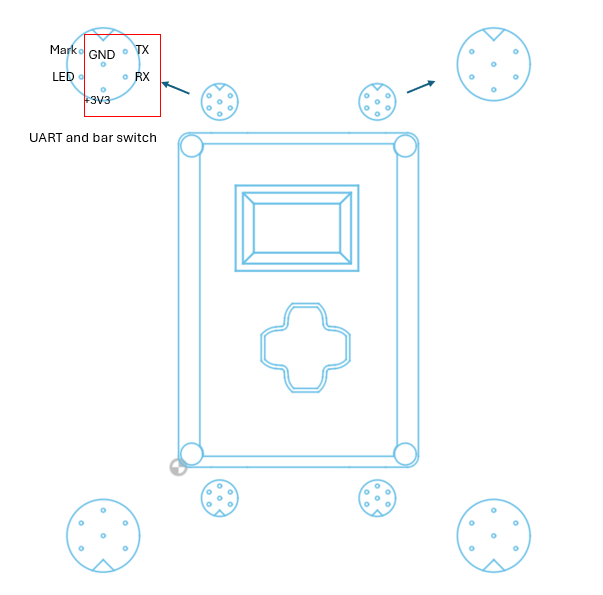
bodocs/src/assets/pics/sensor-connection-and-wiring-guide/a8-uart.png
