benconnor1972/BODAQS/bodocs/src/assets/pics/sensor-connection-and-wiring-guide/config-analog-pot.png

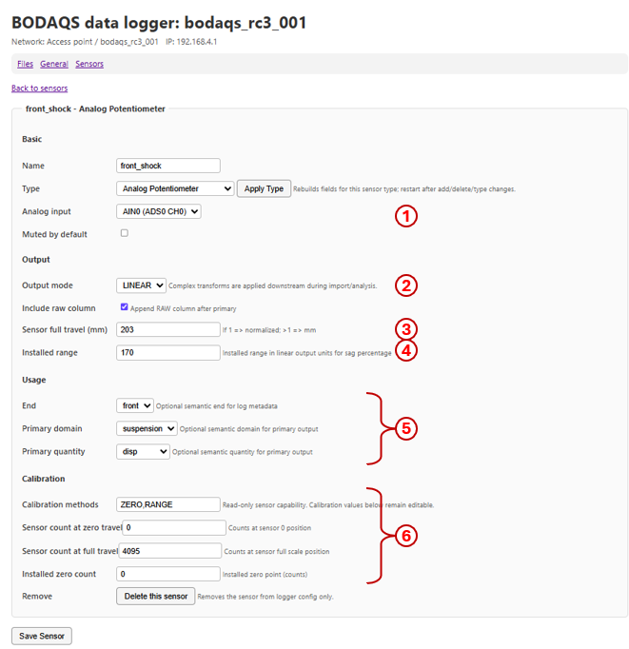
bodocs/src/assets/pics/sensor-connection-and-wiring-guide/config-analog-pot.png
