benconnor1972/BODAQS/bodocs/src/assets/pics/sensor-connection-and-wiring-guide/config-as5600-analog-wiring.png

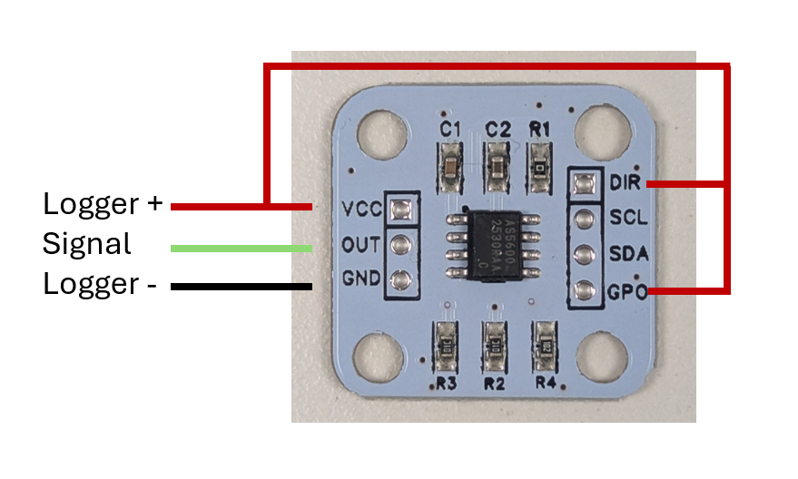
bodocs/src/assets/pics/sensor-connection-and-wiring-guide/config-as5600-analog-wiring.png
