benconnor1972/BODAQS/bodocs/src/assets/pics/sensor-connection-and-wiring-guide/config-as5600-digital-wiring.png

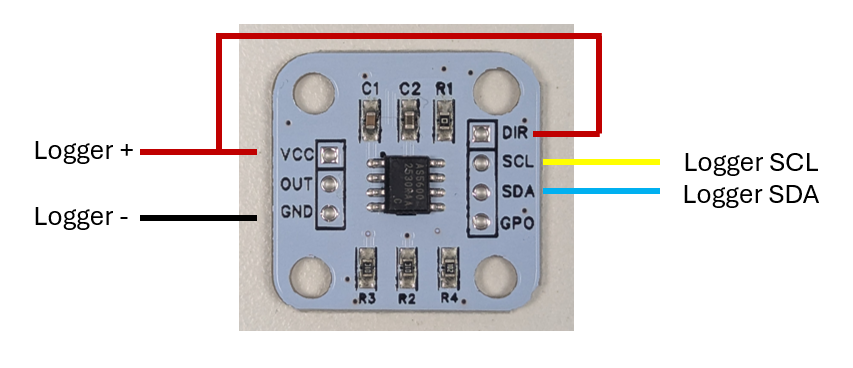
bodocs/src/assets/pics/sensor-connection-and-wiring-guide/config-as5600-digital-wiring.png
