benconnor1972/BODAQS/bodocs/src/assets/pics/sensor-connection-and-wiring-guide/config-gps.png

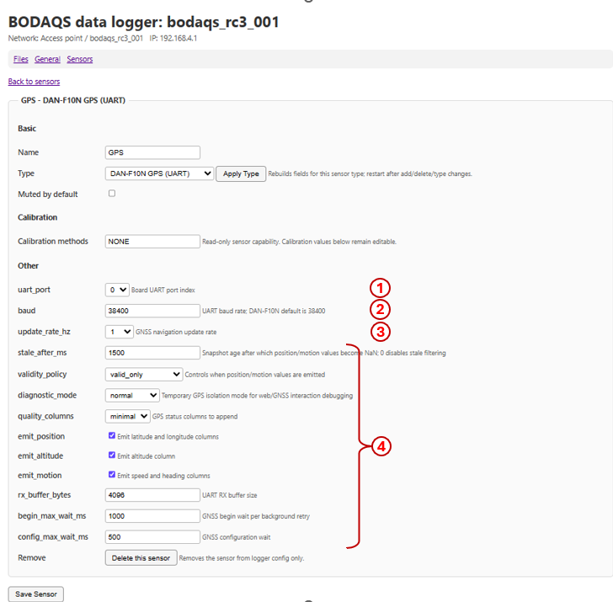
bodocs/src/assets/pics/sensor-connection-and-wiring-guide/config-gps.png
