benconnor1972/BODAQS/bodocs/src/assets/pics/sensor-connection-and-wiring-guide/config-i2c-stringpot.png

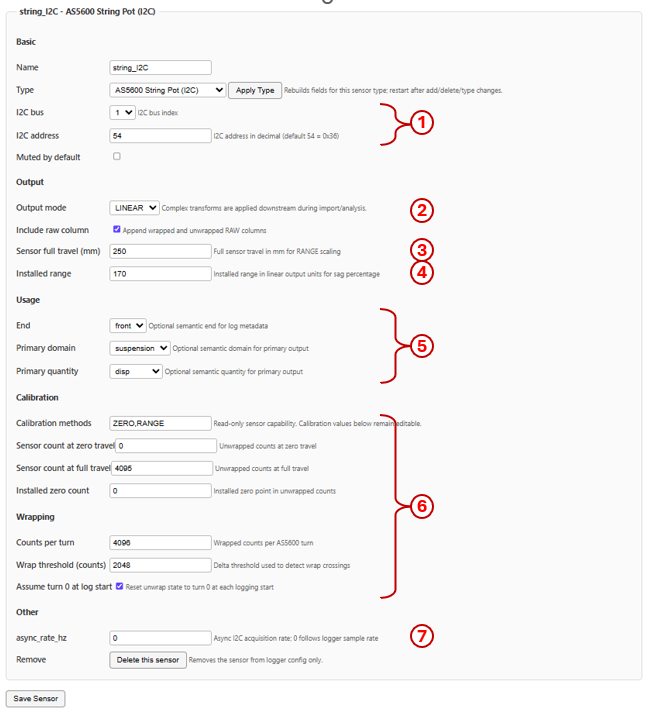
bodocs/src/assets/pics/sensor-connection-and-wiring-guide/config-i2c-stringpot.png
