benconnor1972/BODAQS/bodocs/src/assets/pics/sensor-connection-and-wiring-guide/proto-f-analog.png

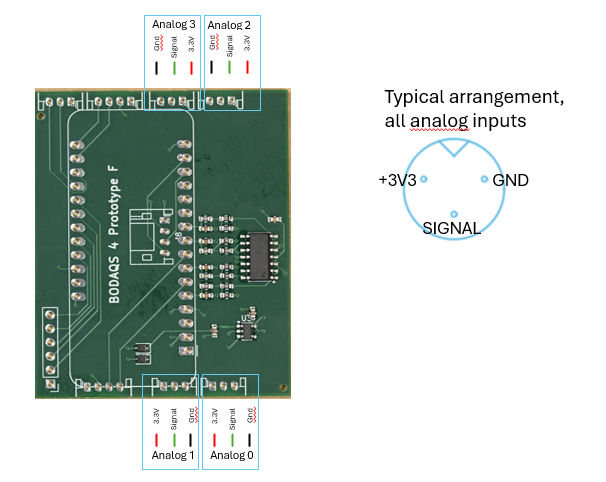
bodocs/src/assets/pics/sensor-connection-and-wiring-guide/proto-f-analog.png
