benconnor1972/BODAQS/bodocs/src/assets/pics/sensor-connection-and-wiring-guide/proto-f-uart.png

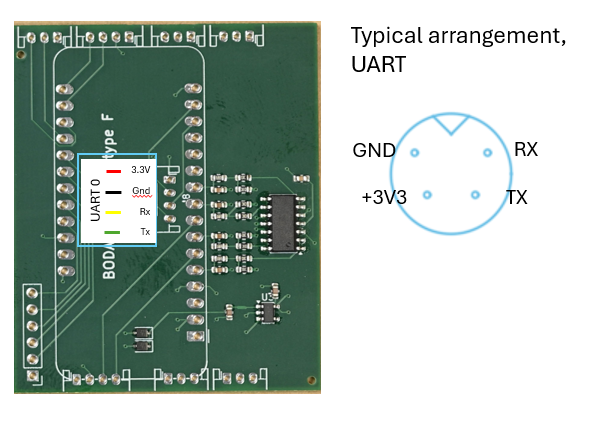
bodocs/src/assets/pics/sensor-connection-and-wiring-guide/proto-f-uart.png
