benconnor1972/BODAQS/bodocs/src/assets/pics/sensor-connection-and-wiring-guide/sensor-config-add.png

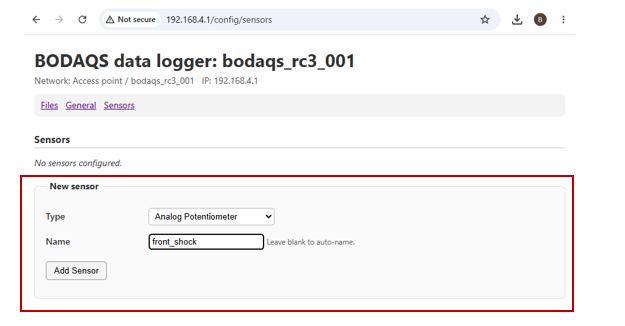
bodocs/src/assets/pics/sensor-connection-and-wiring-guide/sensor-config-add.png
