benconnor1972/BODAQS/bodocs/src/assets/pics/sensor-connection-and-wiring-guide/wire-cut-heatshrink.png

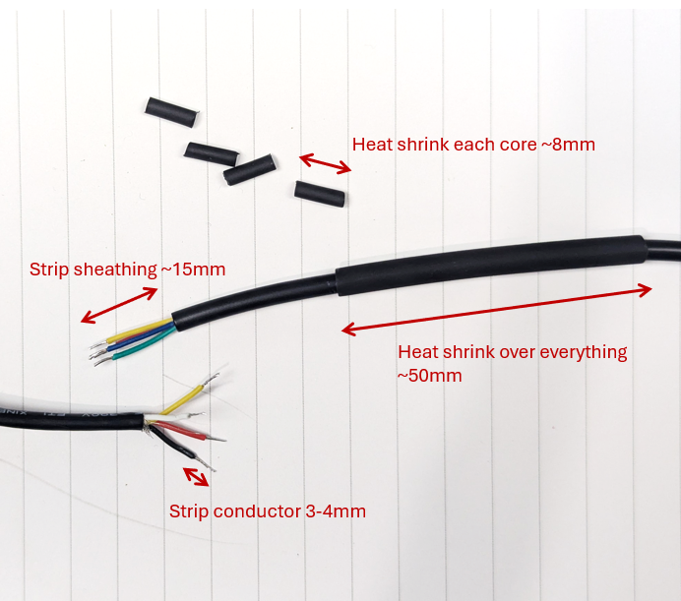
bodocs/src/assets/pics/sensor-connection-and-wiring-guide/wire-cut-heatshrink.png
