benconnor1972/BODAQS/bodocs/src/assets/pics/sensor-connection-and-wiring-guide/wire-finish.jpg

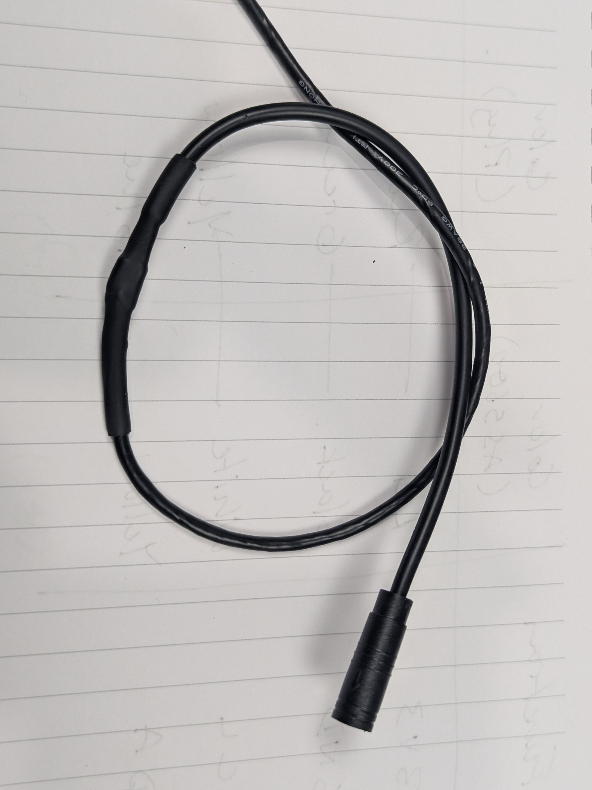
bodocs/src/assets/pics/sensor-connection-and-wiring-guide/wire-finish.jpg
