benconnor1972/BODAQS/bodocs/src/assets/pics/sensor-connection-and-wiring-guide/wiring-a8-direct.png

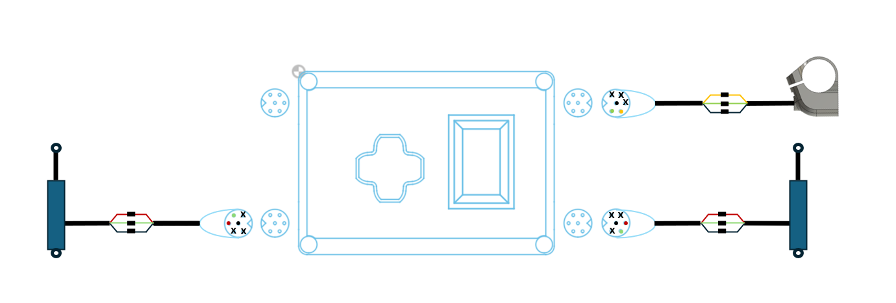
bodocs/src/assets/pics/sensor-connection-and-wiring-guide/wiring-a8-direct.png
