benconnor1972/BODAQS/bodocs/src/assets/pics/sensor-connection-and-wiring-guide/wiring-a8-flexible-example.jpeg

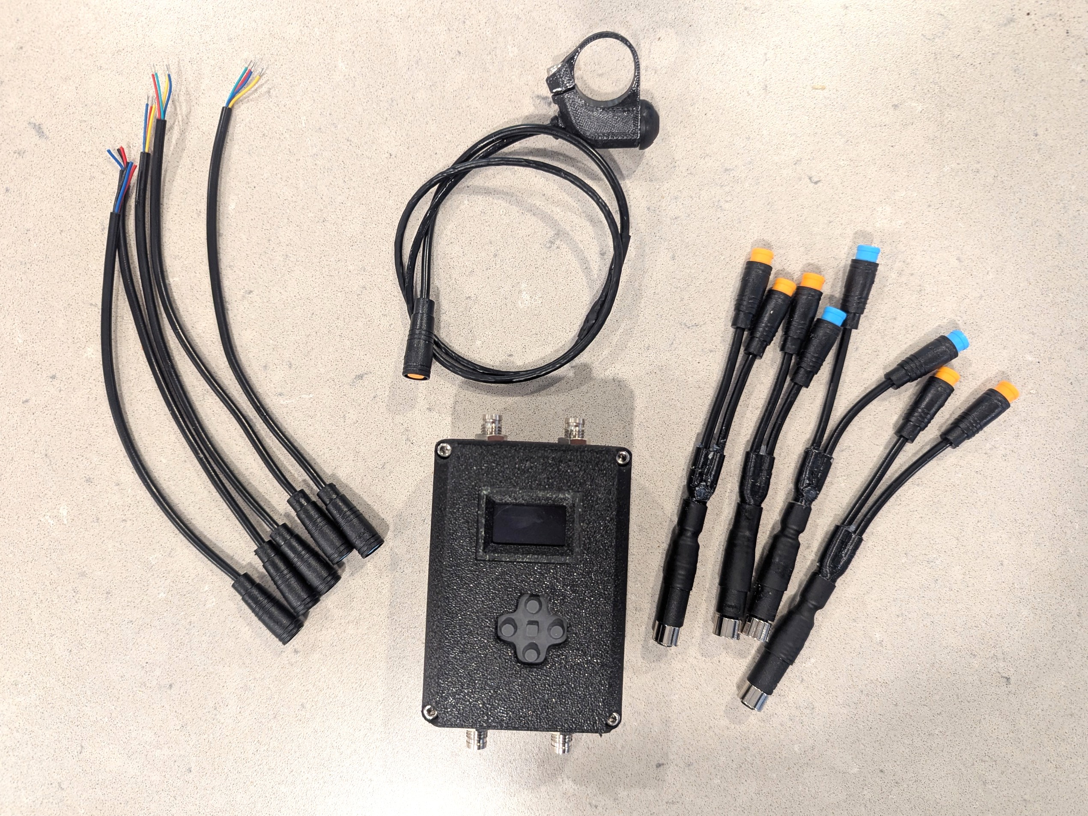
bodocs/src/assets/pics/sensor-connection-and-wiring-guide/wiring-a8-flexible-example.jpeg
