benconnor1972/BODAQS/bodocs/src/assets/pics/software-guide/bike-profile-bare.png

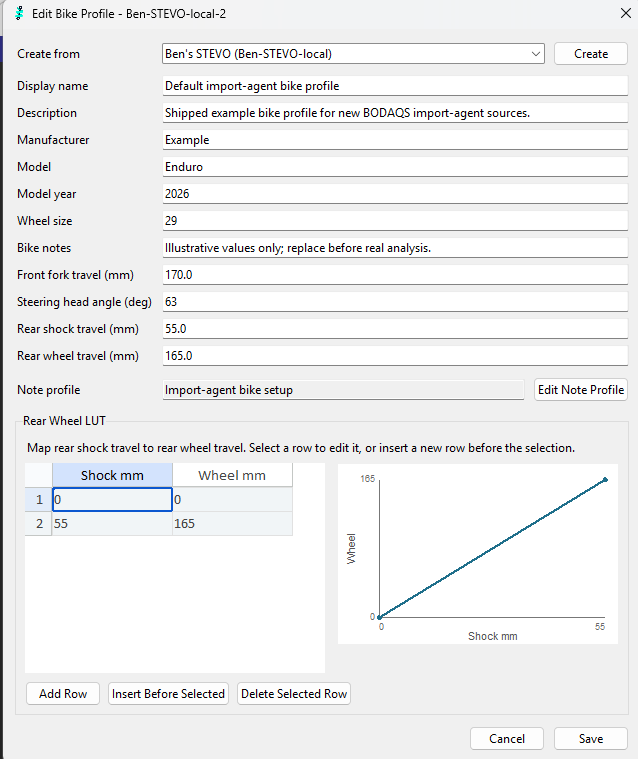
bodocs/src/assets/pics/software-guide/bike-profile-bare.png
