benconnor1972/BODAQS/bodocs/src/assets/pics/software-guide/bike-profile-bike-details.png

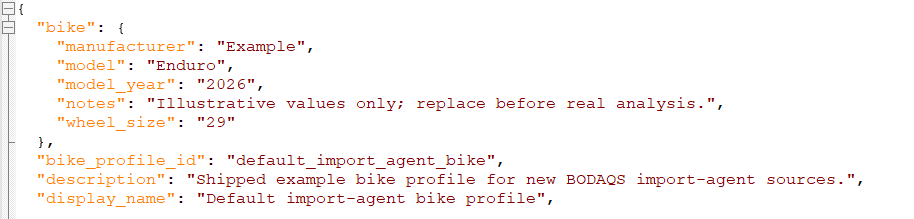
bodocs/src/assets/pics/software-guide/bike-profile-bike-details.png
