benconnor1972/BODAQS/bodocs/src/assets/pics/software-guide/bike-profile-norm-ranges.png

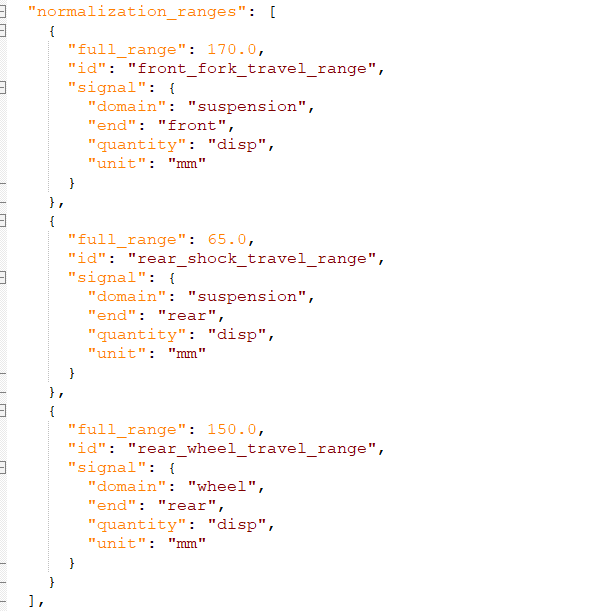
bodocs/src/assets/pics/software-guide/bike-profile-norm-ranges.png
