benconnor1972/BODAQS/bodocs/src/assets/pics/software-guide/edit-note-profile.png

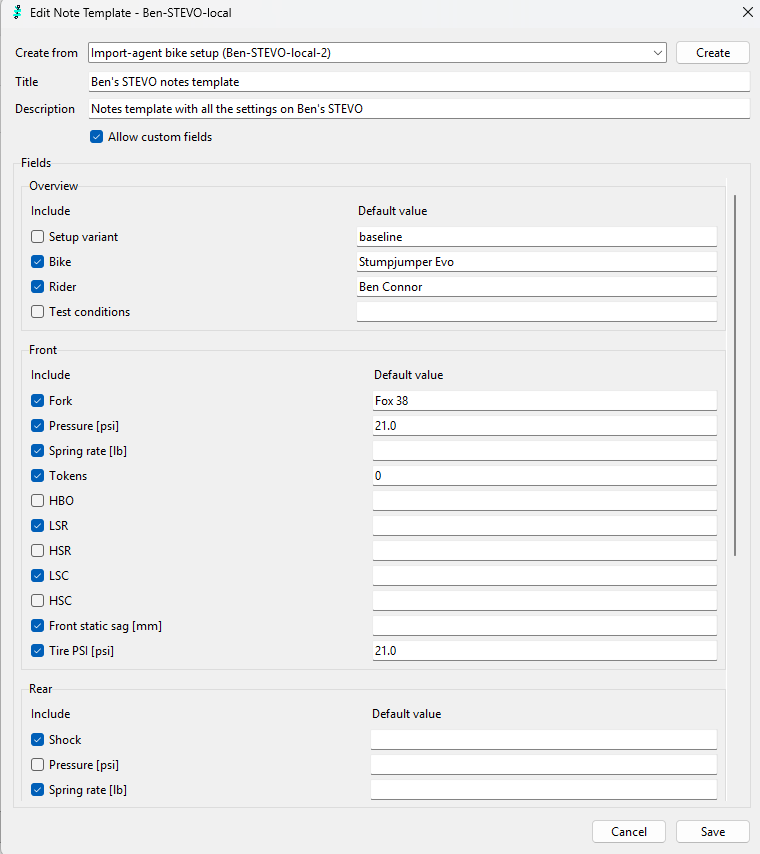
bodocs/src/assets/pics/software-guide/edit-note-profile.png
