benconnor1972/BODAQS/bodocs/src/assets/pics/software-guide/import-manager-2.png

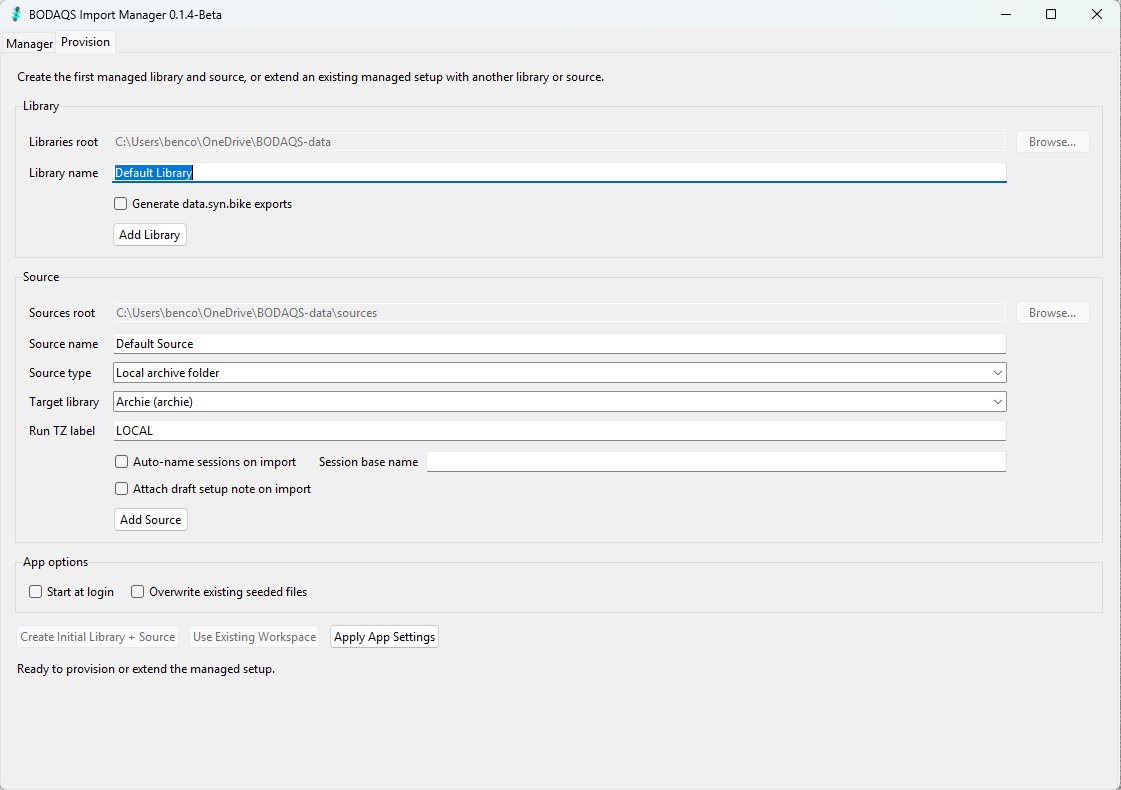
bodocs/src/assets/pics/software-guide/import-manager-2.png
