benconnor1972/BODAQS/bodocs/src/assets/pics/software-guide/import-manager.png

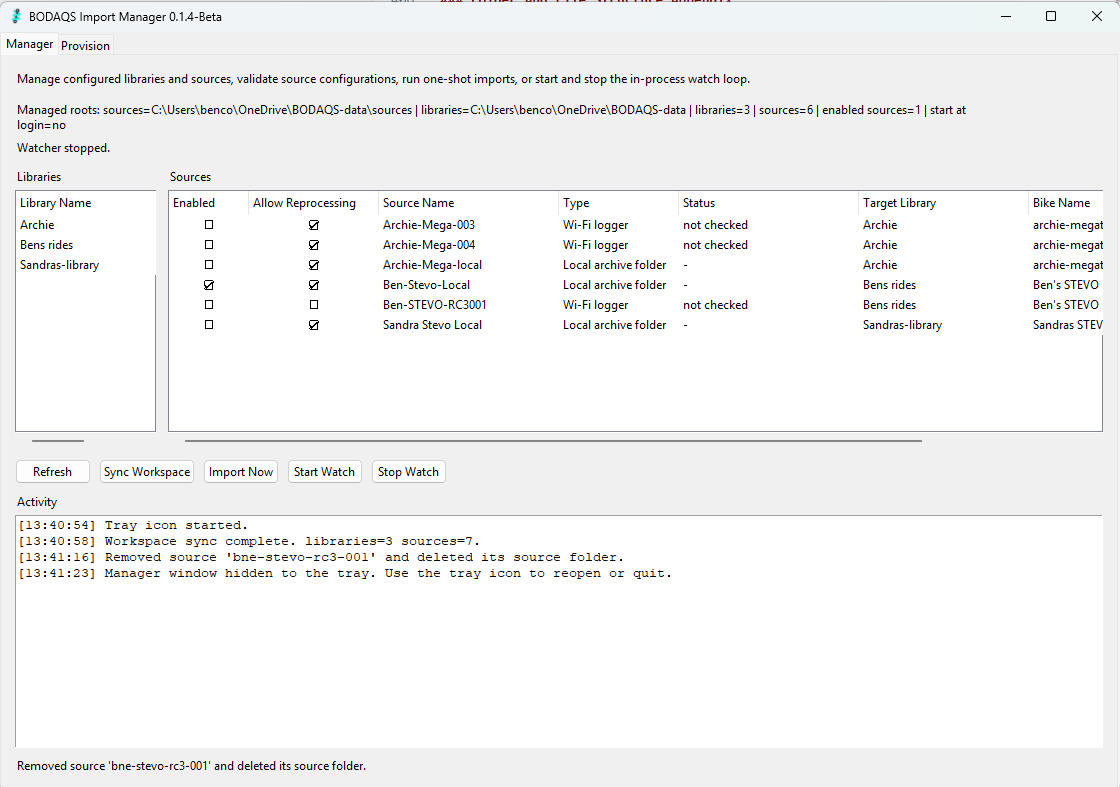
bodocs/src/assets/pics/software-guide/import-manager.png
