benconnor1972/BODAQS/bodocs/src/assets/pics/software-guide/import-mgr-install.png

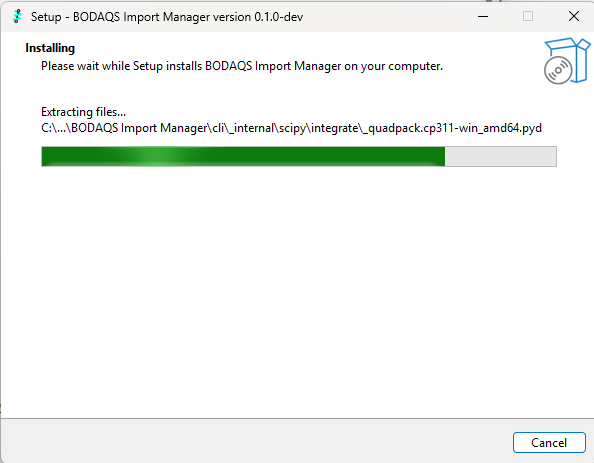
bodocs/src/assets/pics/software-guide/import-mgr-install.png
