benconnor1972/BODAQS/bodocs/src/assets/pics/software-guide/just-say-yes.png

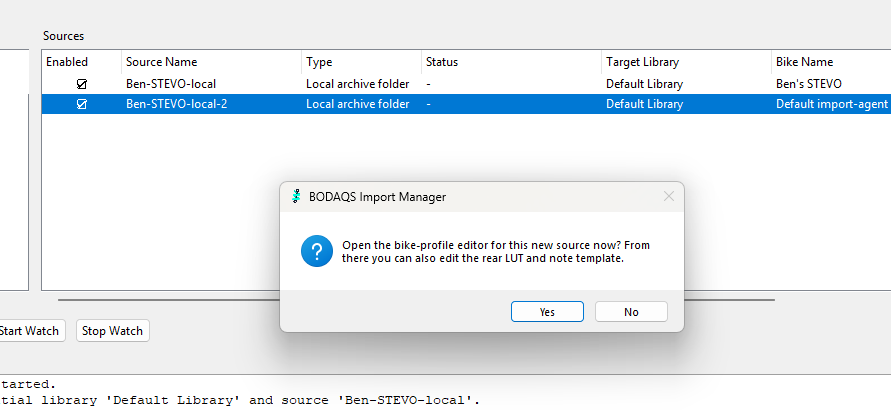
bodocs/src/assets/pics/software-guide/just-say-yes.png
