benconnor1972/BODAQS/bodocs/src/assets/pics/software-guide/library-service.png

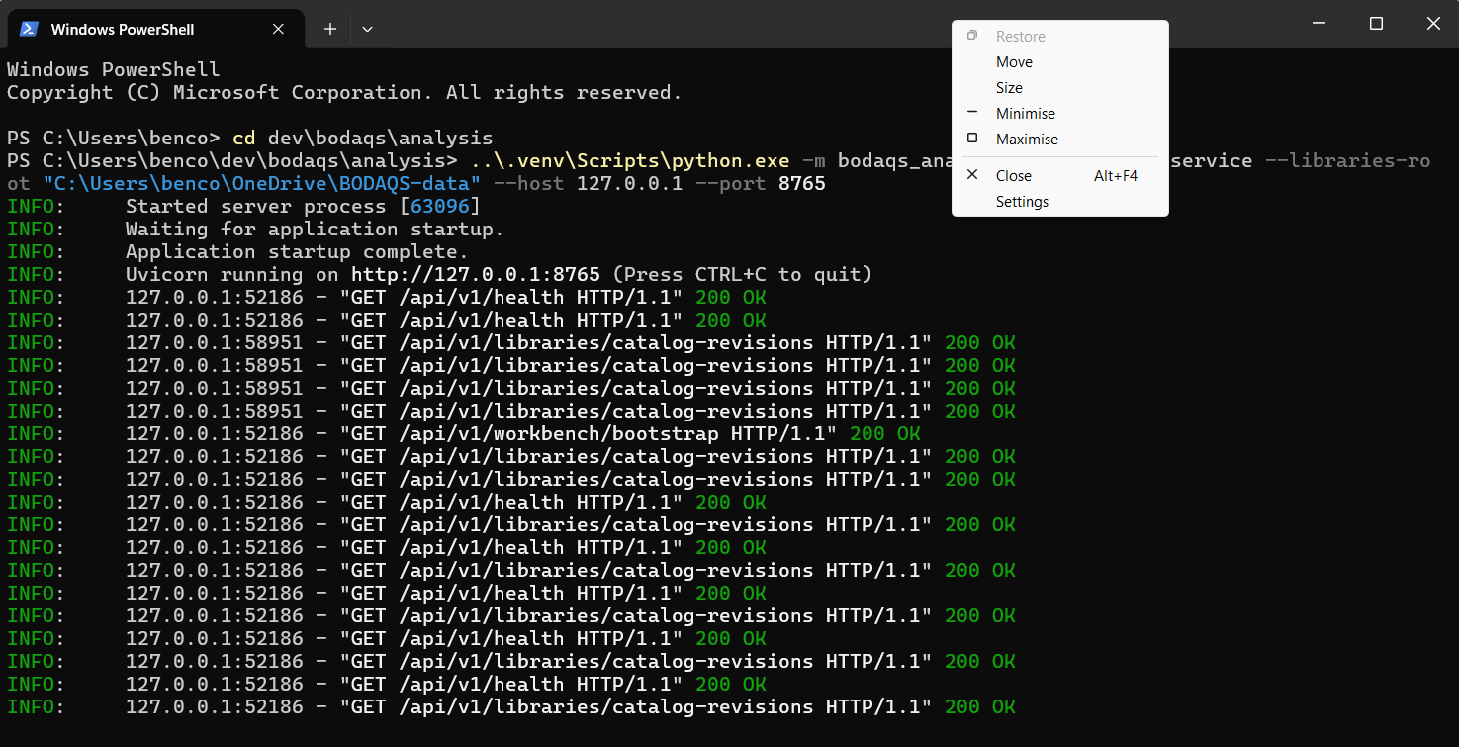
bodocs/src/assets/pics/software-guide/library-service.png
