benconnor1972/BODAQS/bodocs/src/assets/pics/software-guide/logformat.JPG

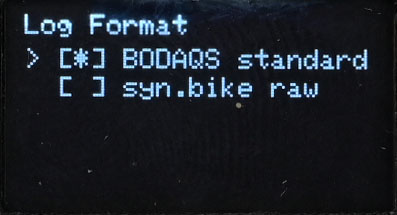
bodocs/src/assets/pics/software-guide/logformat.JPG
