benconnor1972/BODAQS/bodocs/src/assets/pics/software-guide/synserver.png

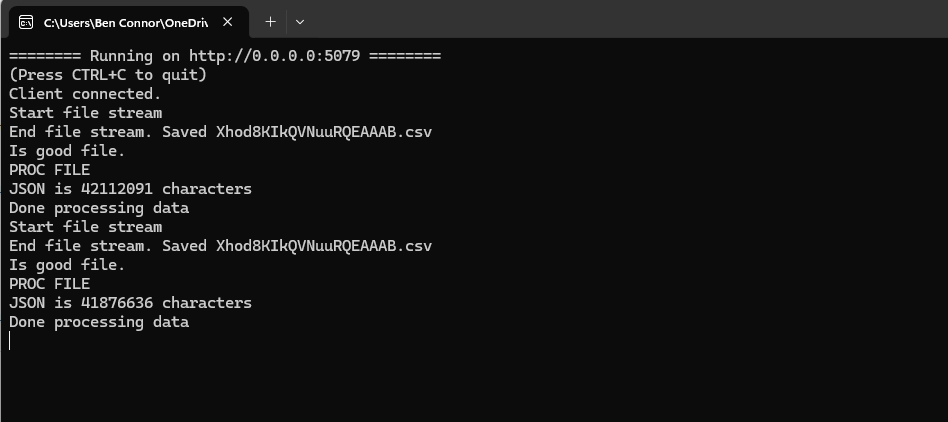
bodocs/src/assets/pics/software-guide/synserver.png
