benconnor1972/BODAQS/bodocs/src/assets/pics/software-guide/synsetup1.png

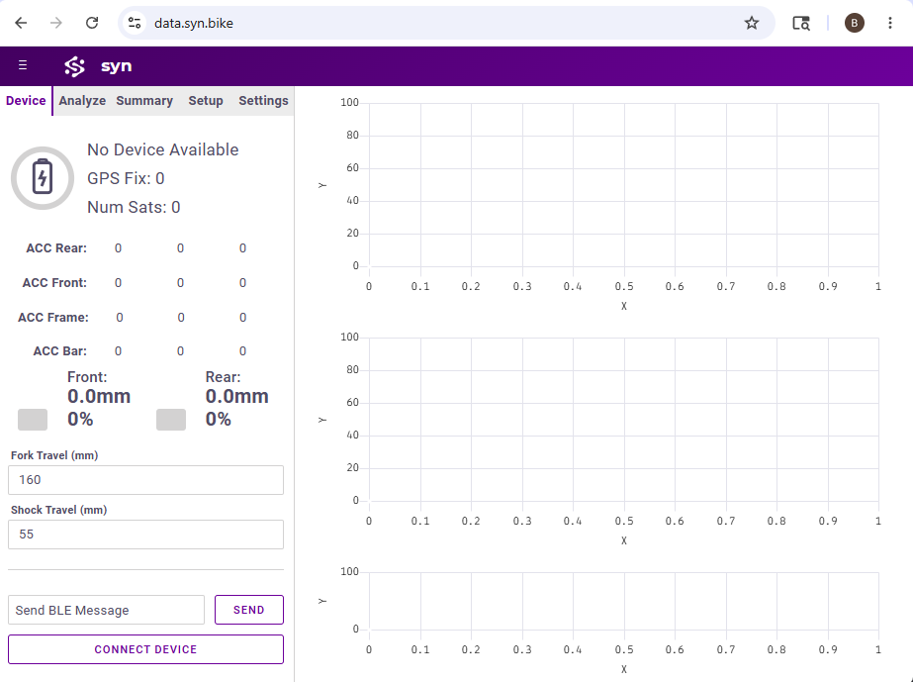
bodocs/src/assets/pics/software-guide/synsetup1.png
