benconnor1972/BODAQS/bodocs/src/assets/pics/software-guide/synsetup.png

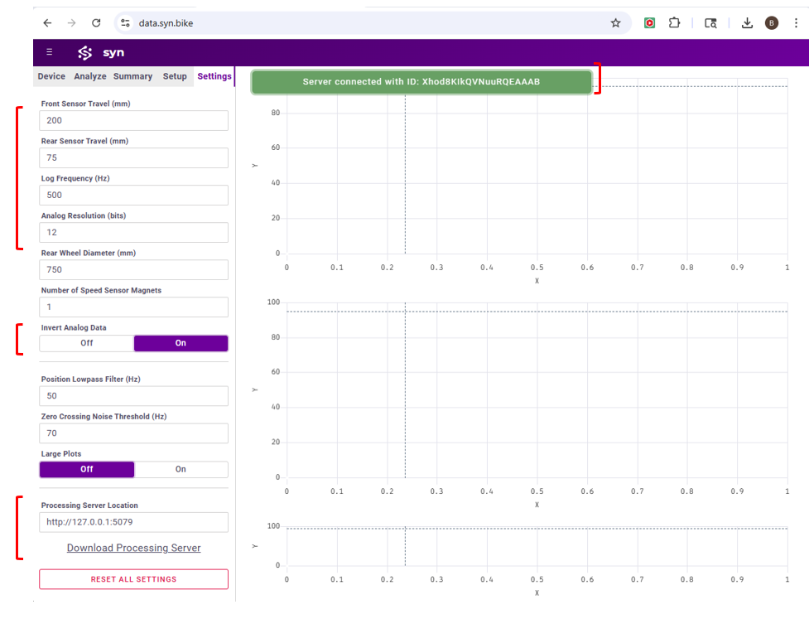
bodocs/src/assets/pics/software-guide/synsetup.png
