benconnor1972/BODAQS/bodocs/src/assets/pics/user-guide/caloptions.png

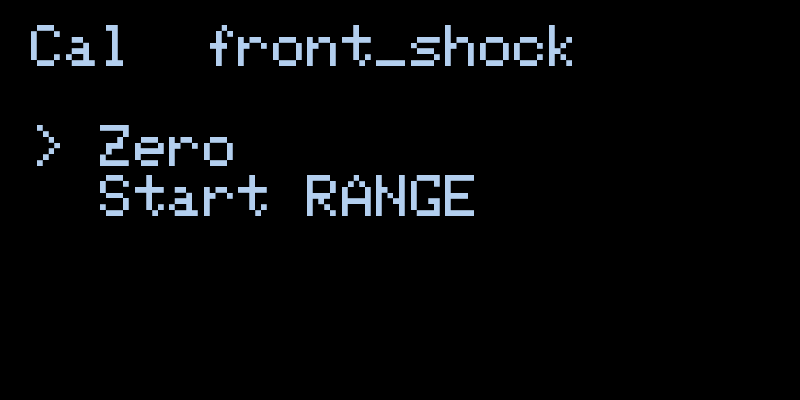
bodocs/src/assets/pics/user-guide/caloptions.png
