benconnor1972/BODAQS/bodocs/src/assets/pics/user-guide/config.png

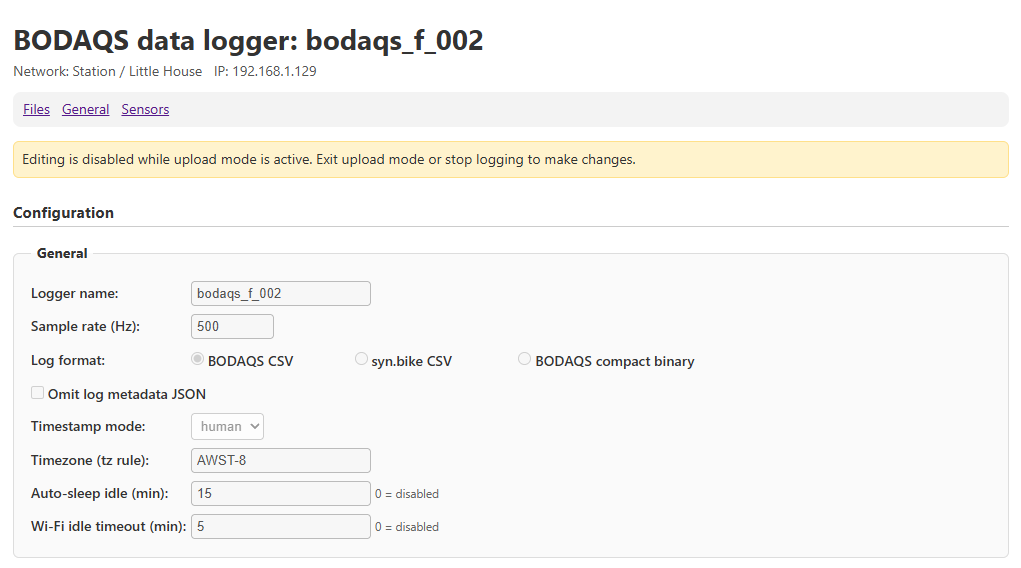
bodocs/src/assets/pics/user-guide/config.png
