benconnor1972/BODAQS/bodocs/src/assets/pics/user-guide/files.png

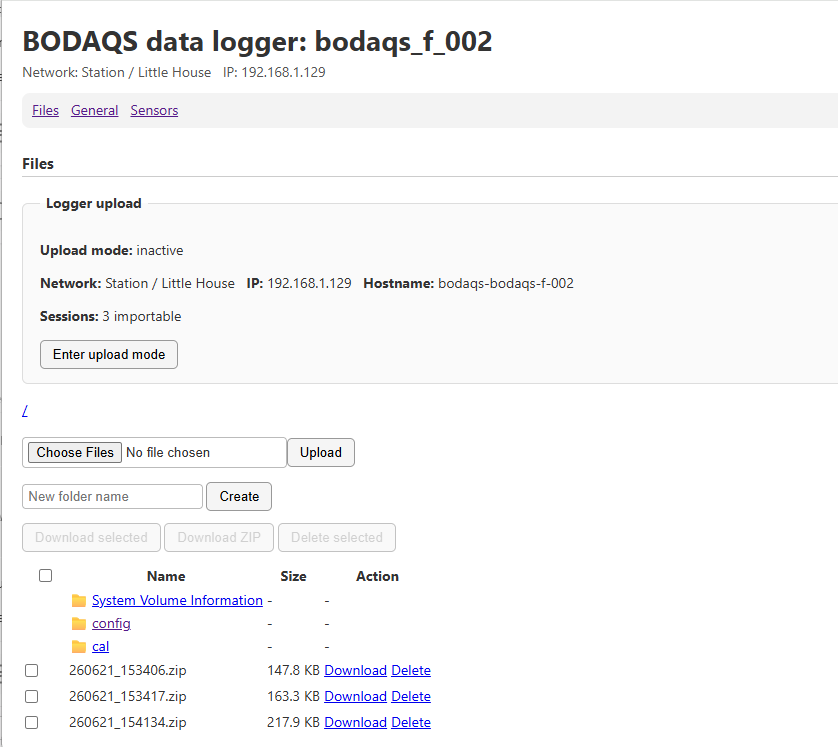
bodocs/src/assets/pics/user-guide/files.png
