benconnor1972/BODAQS/bodocs/src/assets/pics/user-guide/gpssensor.png

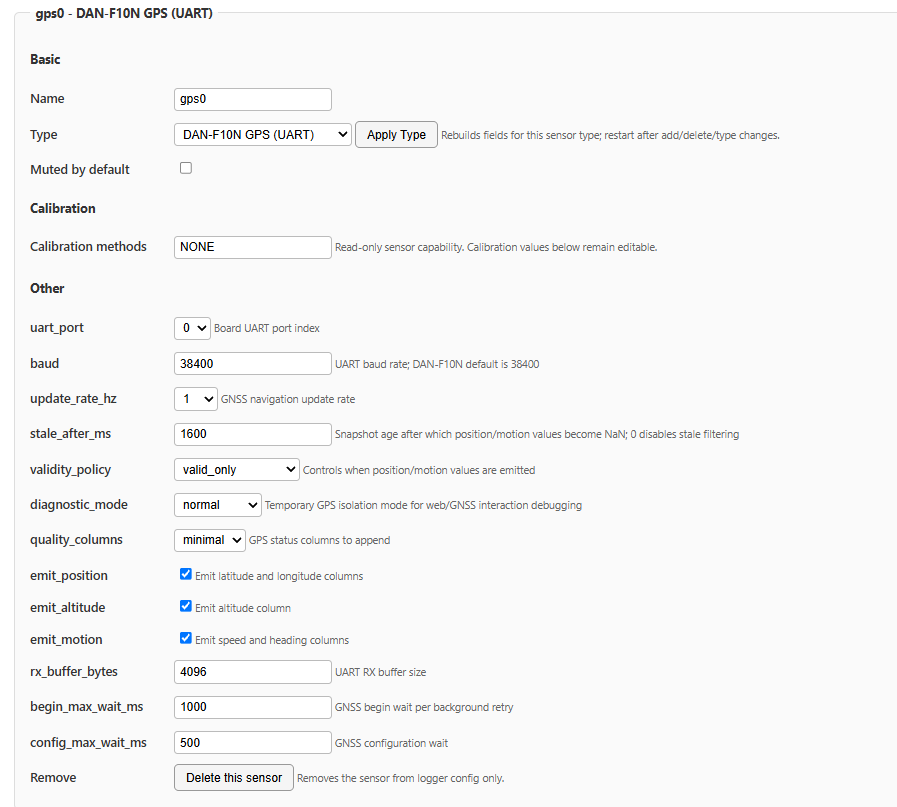
bodocs/src/assets/pics/user-guide/gpssensor.png
