benconnor1972/BODAQS/bodocs/src/assets/pics/user-guide/import-run-naming.png

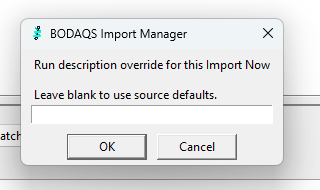
bodocs/src/assets/pics/user-guide/import-run-naming.png
