benconnor1972/BODAQS/bodocs/src/assets/pics/user-guide/import-session-naming.png

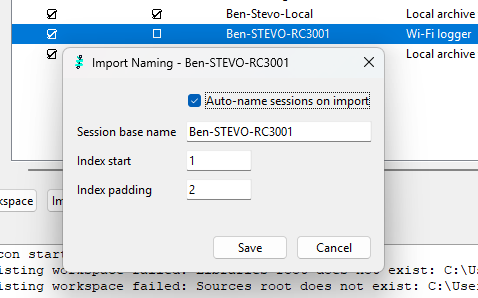
bodocs/src/assets/pics/user-guide/import-session-naming.png
