benconnor1972/BODAQS/bodocs/src/assets/pics/user-guide/logformatmenu.JPG

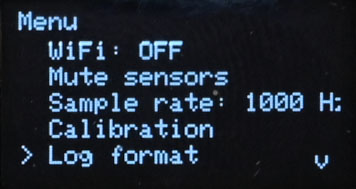
bodocs/src/assets/pics/user-guide/logformatmenu.JPG
