benconnor1972/BODAQS/bodocs/src/assets/pics/user-guide/manager-tab.png

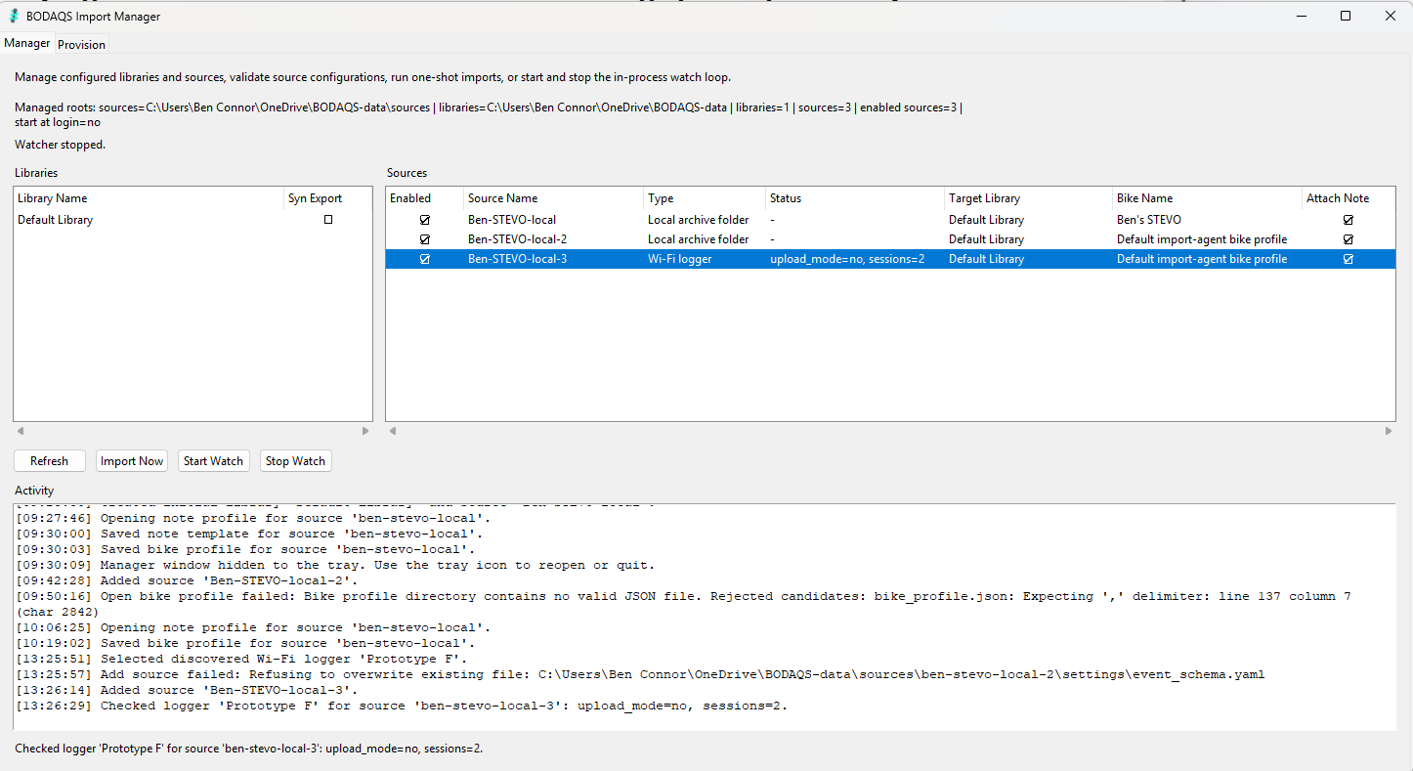
bodocs/src/assets/pics/user-guide/manager-tab.png
