benconnor1972/BODAQS/bodocs/src/assets/pics/user-guide/new-oled/DSC_8409.JPG

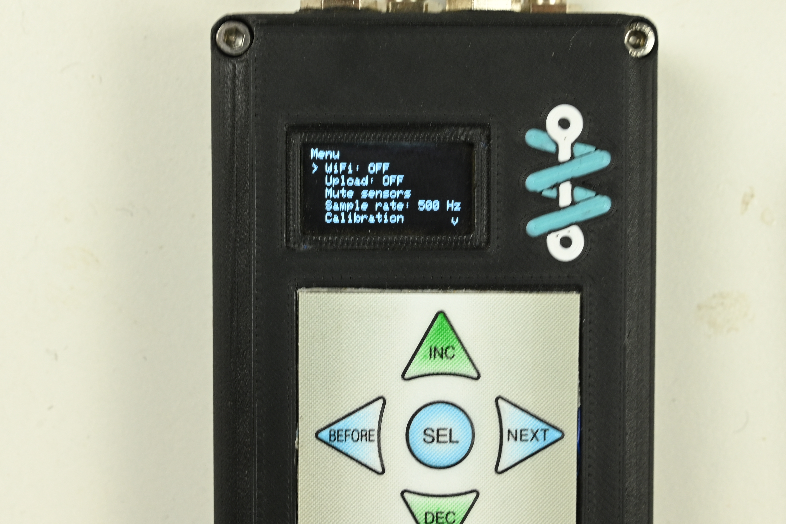
bodocs/src/assets/pics/user-guide/new-oled/DSC_8409.JPG
