benconnor1972/BODAQS/bodocs/src/assets/pics/user-guide/new-oled/PXL_20260620_080607246.jpg

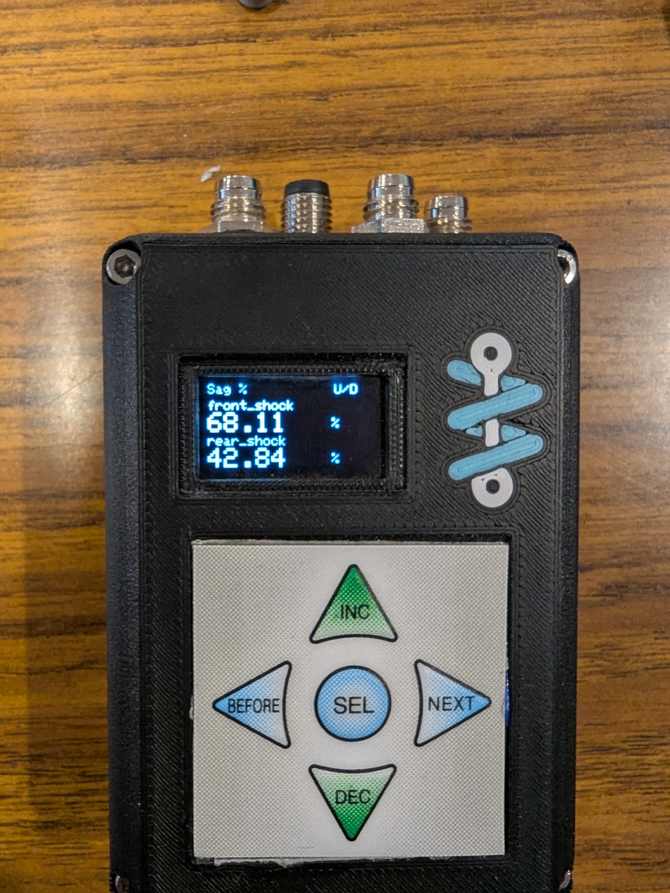
bodocs/src/assets/pics/user-guide/new-oled/PXL_20260620_080607246.jpg
