benconnor1972/BODAQS/bodocs/src/assets/pics/user-guide/new-oled/PXL_20260621_071950635.jpg

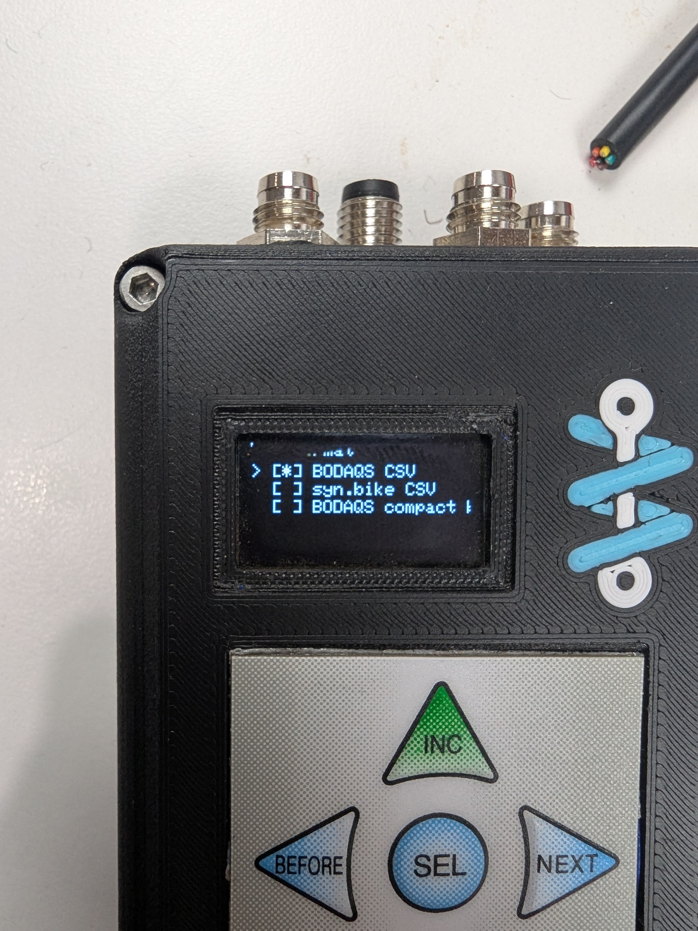
bodocs/src/assets/pics/user-guide/new-oled/PXL_20260621_071950635.jpg
