benconnor1972/BODAQS/bodocs/src/assets/pics/user-guide/new-oled/PXL_20260621_072121356.jpg

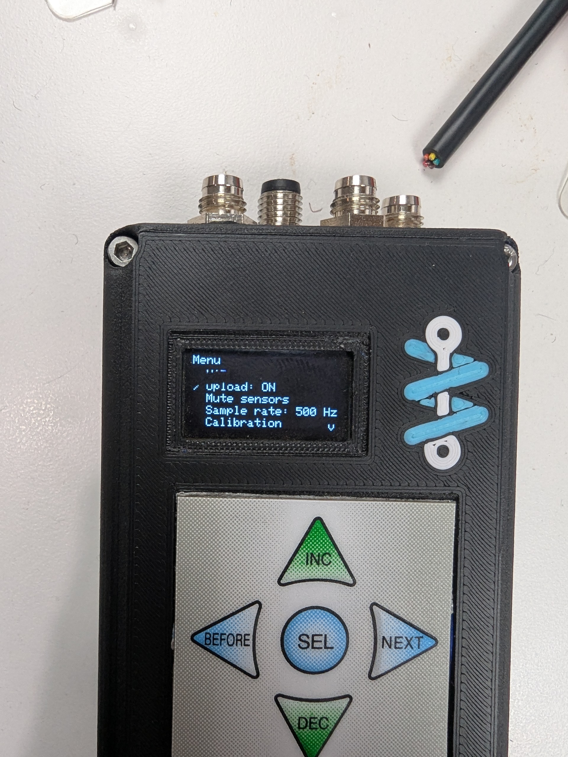
bodocs/src/assets/pics/user-guide/new-oled/PXL_20260621_072121356.jpg
