benconnor1972/BODAQS/bodocs/src/assets/pics/user-guide/new-oled/PXL_20260621_072125822.jpg

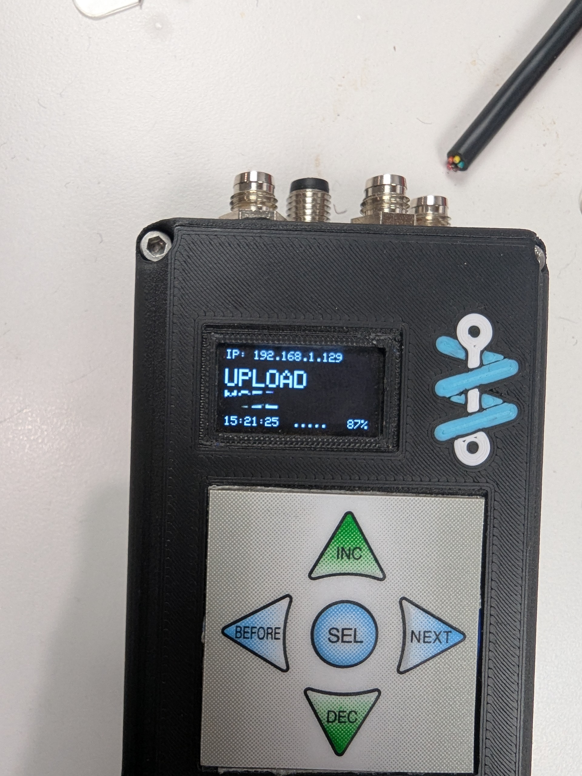
bodocs/src/assets/pics/user-guide/new-oled/PXL_20260621_072125822.jpg
