benconnor1972/BODAQS/bodocs/src/assets/pics/user-guide/oled-ap-idle.png

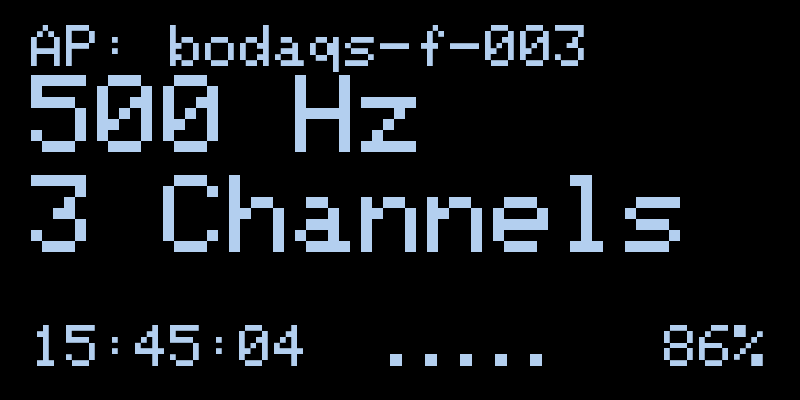
bodocs/src/assets/pics/user-guide/oled-ap-idle.png
