benconnor1972/BODAQS/bodocs/src/assets/pics/user-guide/oled-health.png

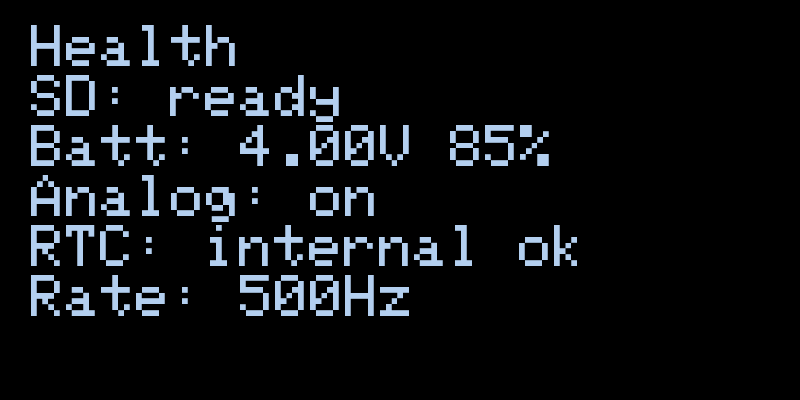
bodocs/src/assets/pics/user-guide/oled-health.png
