benconnor1972/BODAQS/bodocs/src/assets/pics/user-guide/oled-idle-status.png

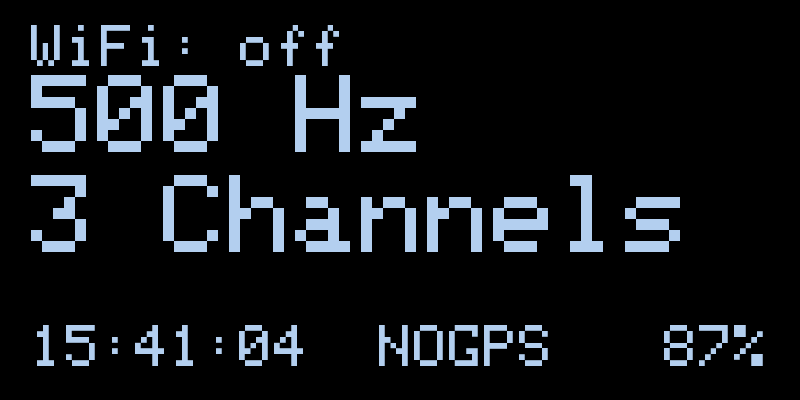
bodocs/src/assets/pics/user-guide/oled-idle-status.png
