benconnor1972/BODAQS/bodocs/src/assets/pics/user-guide/oled-log-format-picker.png

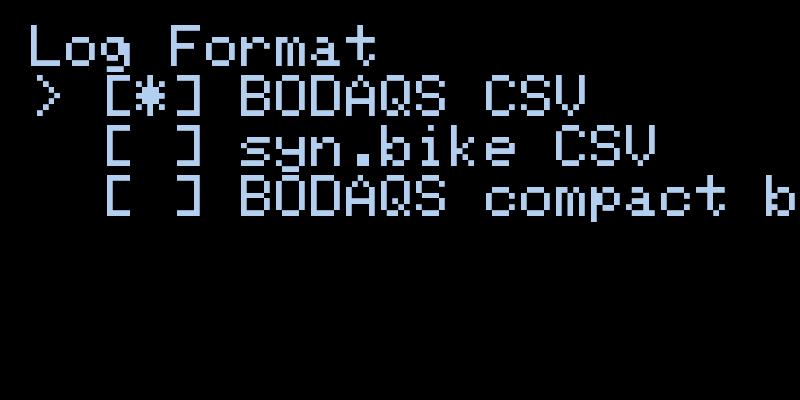
bodocs/src/assets/pics/user-guide/oled-log-format-picker.png
