benconnor1972/BODAQS/bodocs/src/assets/pics/user-guide/oled-log-start.png

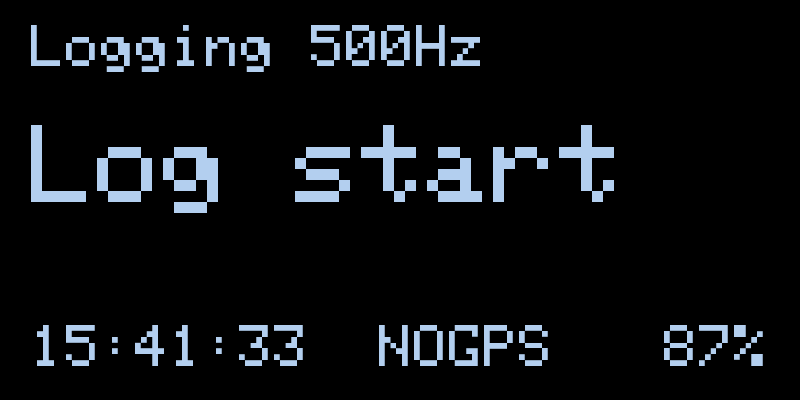
bodocs/src/assets/pics/user-guide/oled-log-start.png
