benconnor1972/BODAQS/bodocs/src/assets/pics/user-guide/oled-main-menu-bottom.png

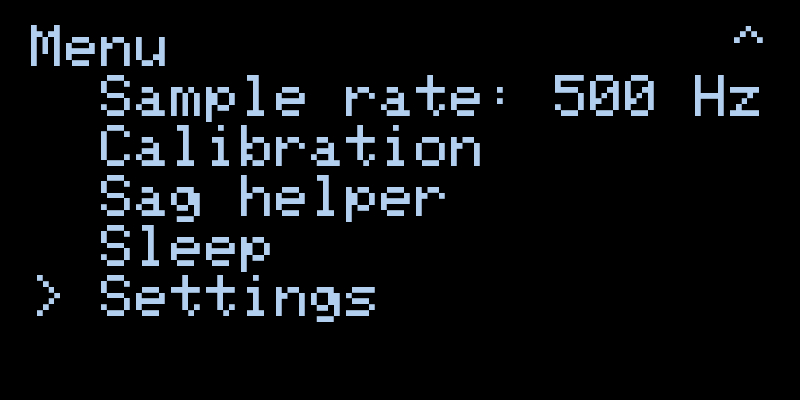
bodocs/src/assets/pics/user-guide/oled-main-menu-bottom.png
