benconnor1972/BODAQS/bodocs/src/assets/pics/user-guide/oled-main-menu-top.png

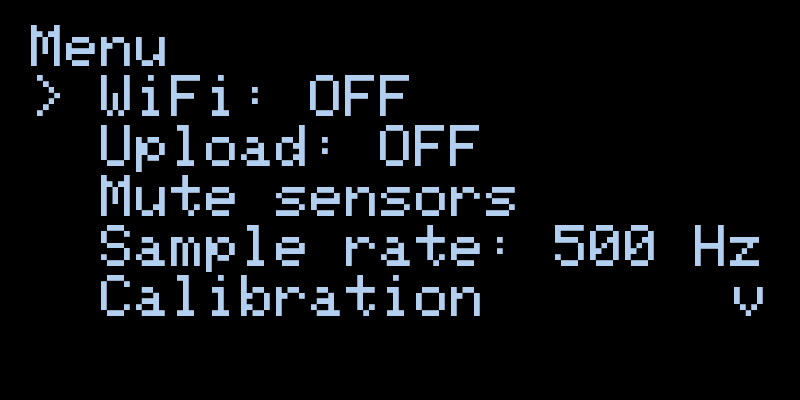
bodocs/src/assets/pics/user-guide/oled-main-menu-top.png
