benconnor1972/BODAQS/bodocs/src/assets/pics/user-guide/oled-sag-helper-percent.png

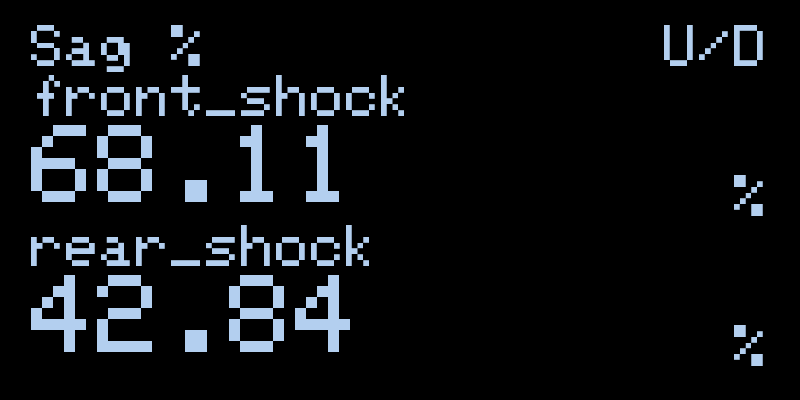
bodocs/src/assets/pics/user-guide/oled-sag-helper-percent.png
