benconnor1972/BODAQS/bodocs/src/assets/pics/user-guide/oled-sensor-mute.png

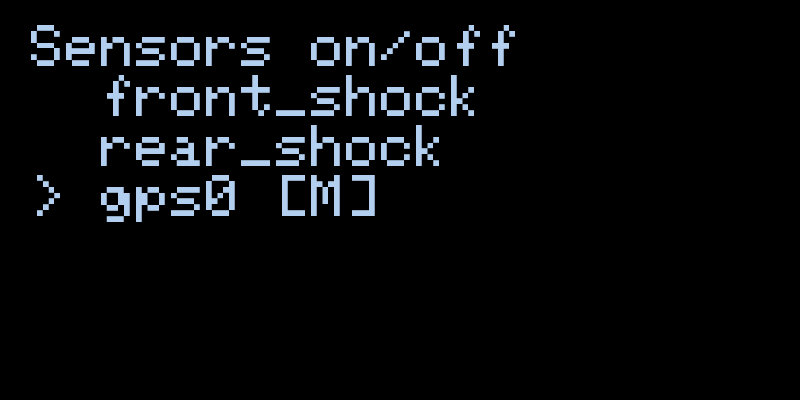
bodocs/src/assets/pics/user-guide/oled-sensor-mute.png
