benconnor1972/BODAQS/bodocs/src/assets/pics/user-guide/oled-settings-menu.png

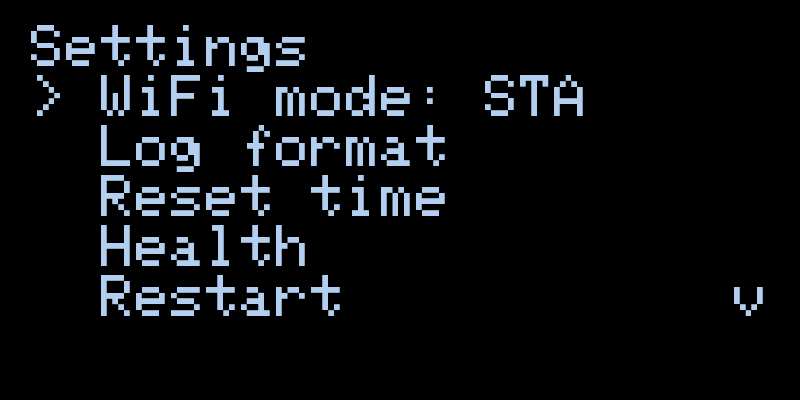
bodocs/src/assets/pics/user-guide/oled-settings-menu.png
