benconnor1972/BODAQS/bodocs/src/assets/pics/user-guide/oled-upload-idle.png

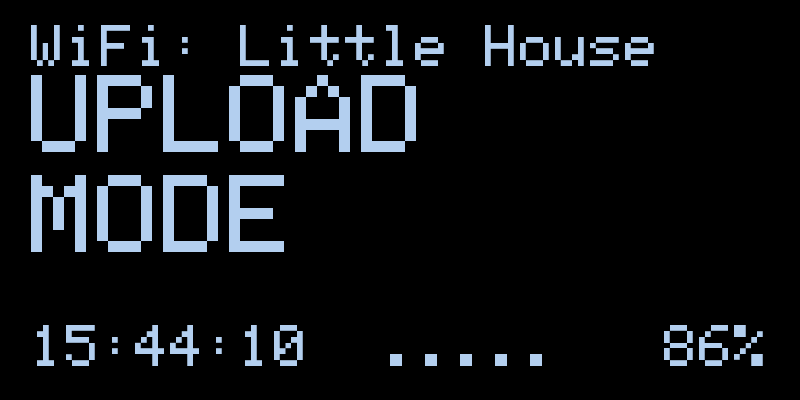
bodocs/src/assets/pics/user-guide/oled-upload-idle.png
