benconnor1972/BODAQS/bodocs/src/assets/pics/user-guide/oled-upload-mode-status.png

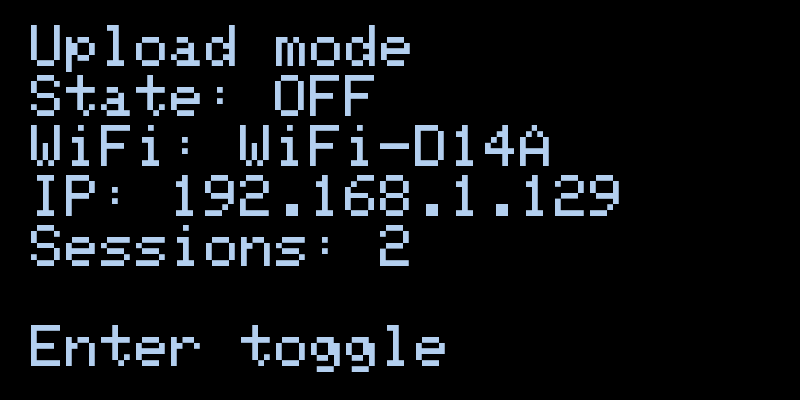
bodocs/src/assets/pics/user-guide/oled-upload-mode-status.png
