benconnor1972/BODAQS/bodocs/src/assets/pics/user-guide/oled-wifi-mode-picker.png

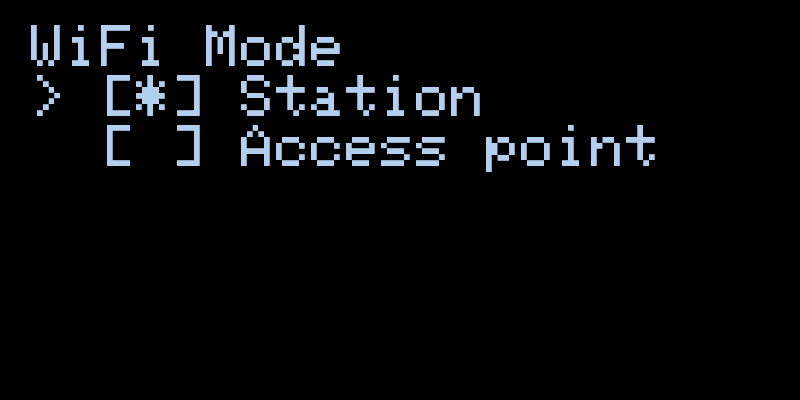
bodocs/src/assets/pics/user-guide/oled-wifi-mode-picker.png
