benconnor1972/BODAQS/bodocs/src/assets/pics/user-guide/provision-tab.png

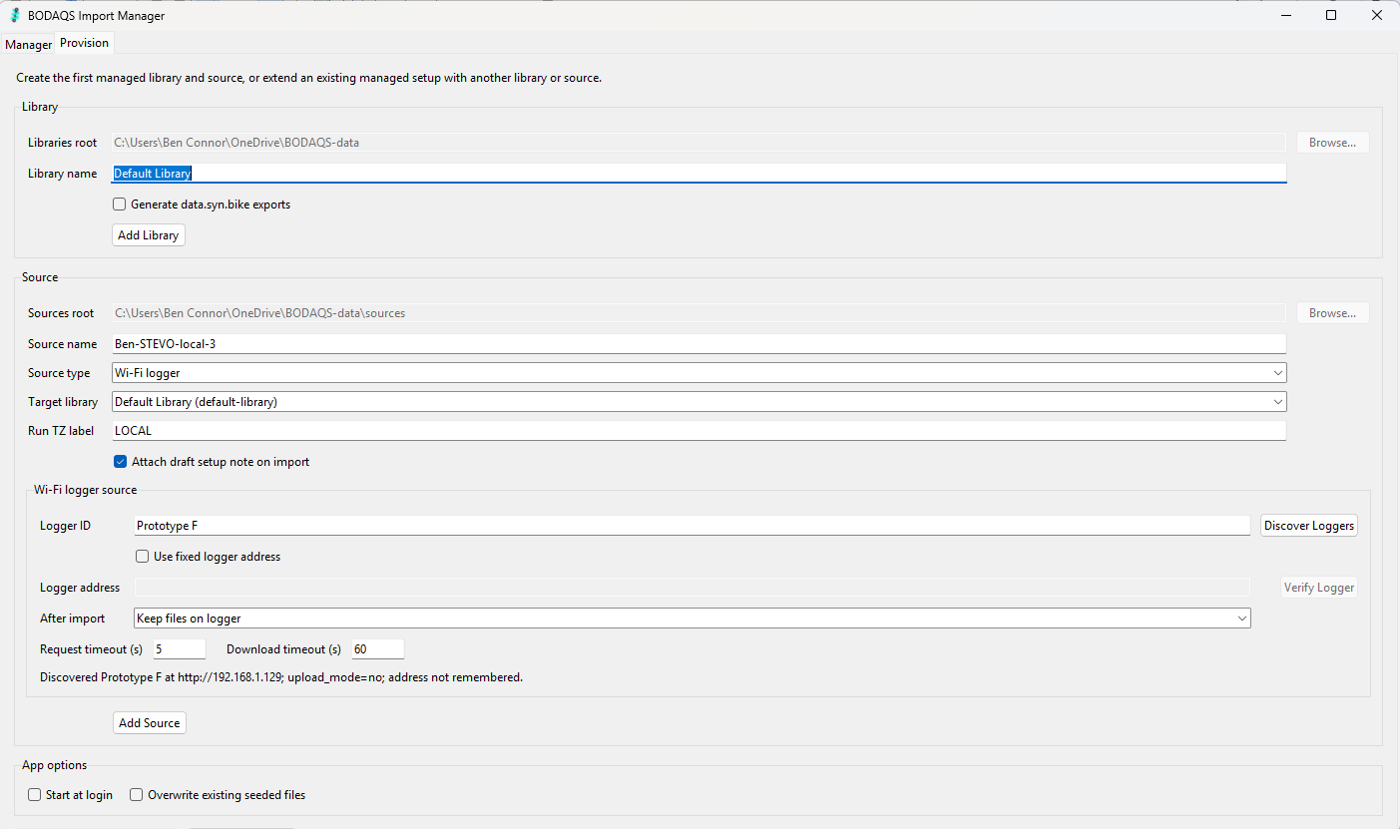
bodocs/src/assets/pics/user-guide/provision-tab.png
