benconnor1972/BODAQS/bodocs/src/assets/pics/user-guide/rangefinish.png

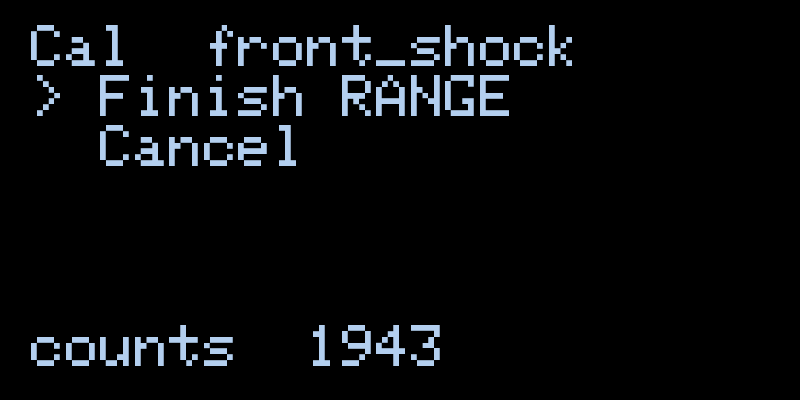
bodocs/src/assets/pics/user-guide/rangefinish.png
