benconnor1972/BODAQS/bodocs/src/assets/pics/user-guide/rangestart.png

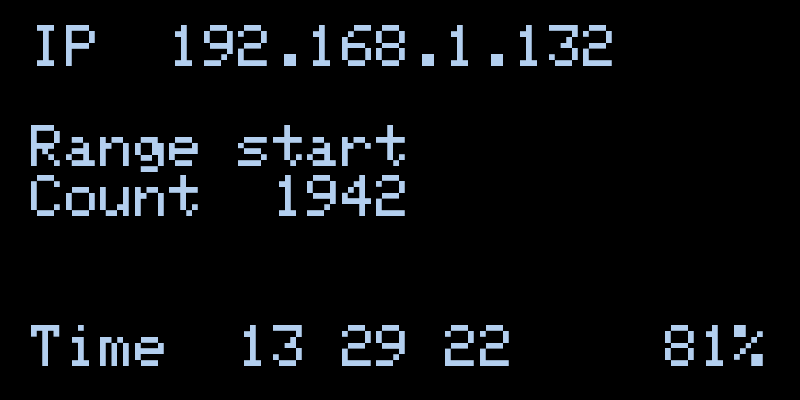
bodocs/src/assets/pics/user-guide/rangestart.png
