benconnor1972/BODAQS/bodocs/src/assets/pics/user-guide/remove-source.png

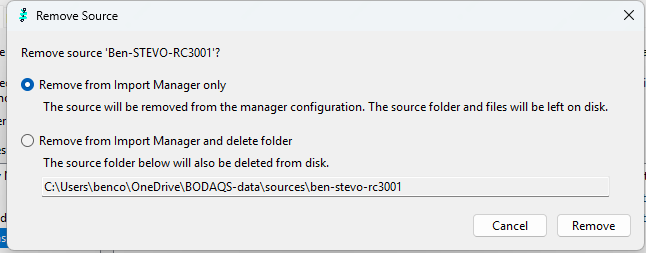
bodocs/src/assets/pics/user-guide/remove-source.png
