benconnor1972/BODAQS/bodocs/src/assets/pics/user-guide/resettime.png

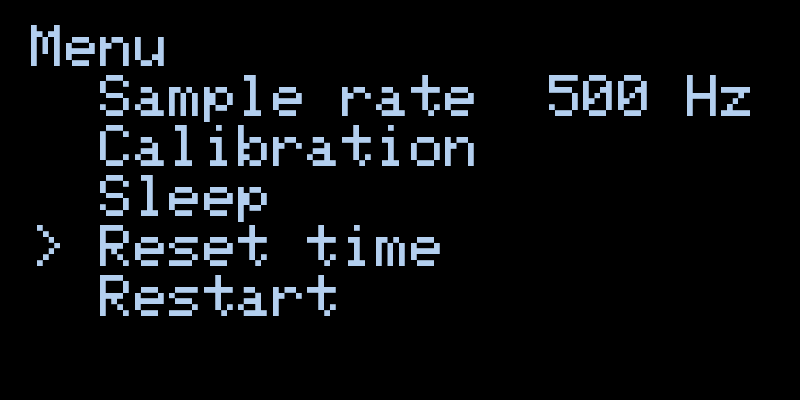
bodocs/src/assets/pics/user-guide/resettime.png
