benconnor1972/BODAQS/bodocs/src/assets/pics/user-guide/samplerate.png

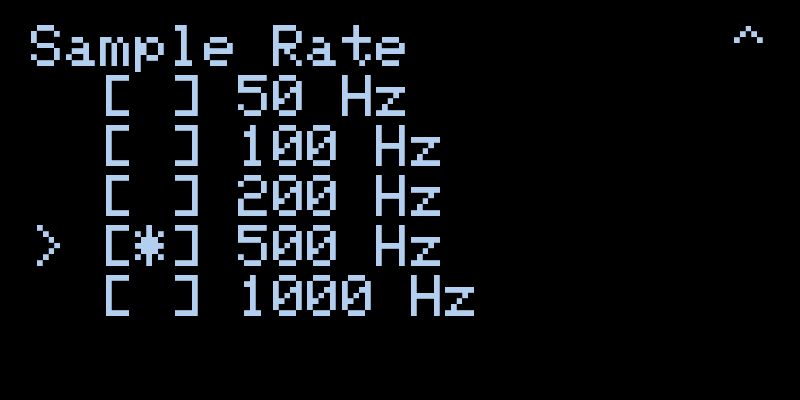
bodocs/src/assets/pics/user-guide/samplerate.png
