benconnor1972/BODAQS/bodocs/src/assets/pics/user-guide/sensor_list.png

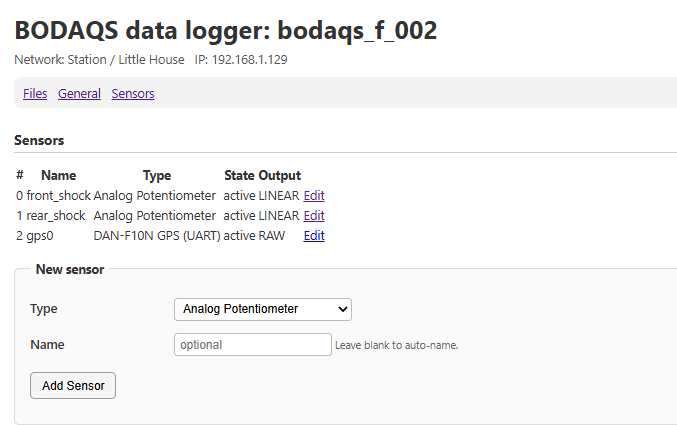
bodocs/src/assets/pics/user-guide/sensor_list.png
