benconnor1972/BODAQS/bodocs/src/assets/pics/user-guide/sensorbasic.png

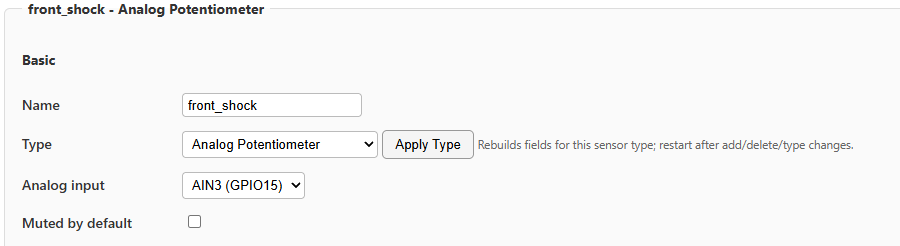
bodocs/src/assets/pics/user-guide/sensorbasic.png
