benconnor1972/BODAQS/bodocs/src/assets/pics/user-guide/sensorbasici2c.png

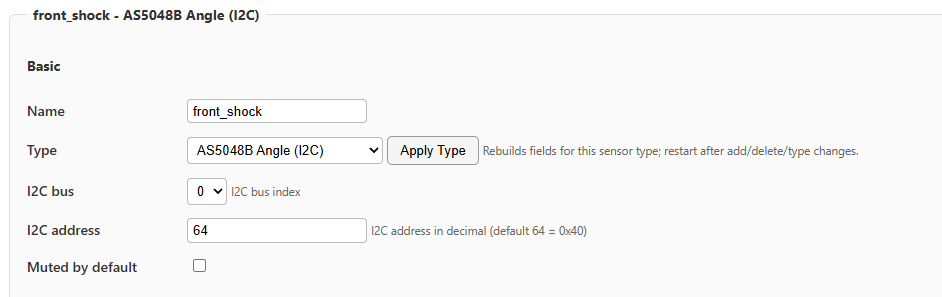
bodocs/src/assets/pics/user-guide/sensorbasici2c.png
