benconnor1972/BODAQS/bodocs/src/assets/pics/user-guide/sensoroutput.png

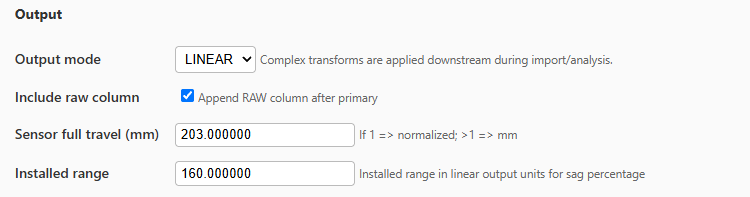
bodocs/src/assets/pics/user-guide/sensoroutput.png
