benconnor1972/BODAQS/bodocs/src/assets/pics/user-guide/sensorusage.png

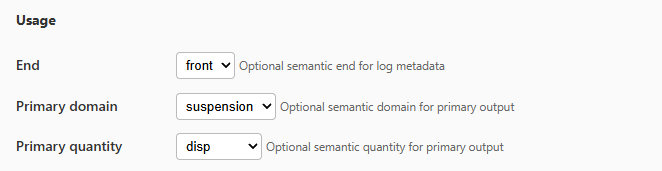
bodocs/src/assets/pics/user-guide/sensorusage.png
