benconnor1972/BODAQS/bodocs/src/assets/pics/user-guide/source-context-menu.png

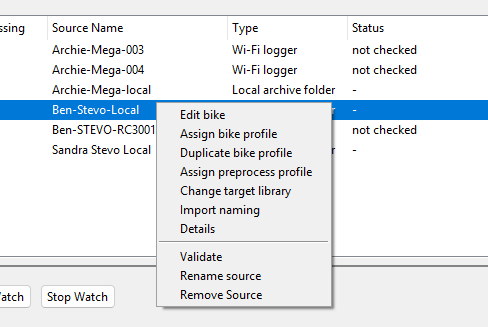
bodocs/src/assets/pics/user-guide/source-context-menu.png
