benconnor1972/BODAQS/bodocs/src/assets/pics/user-guide/synoutputs.png

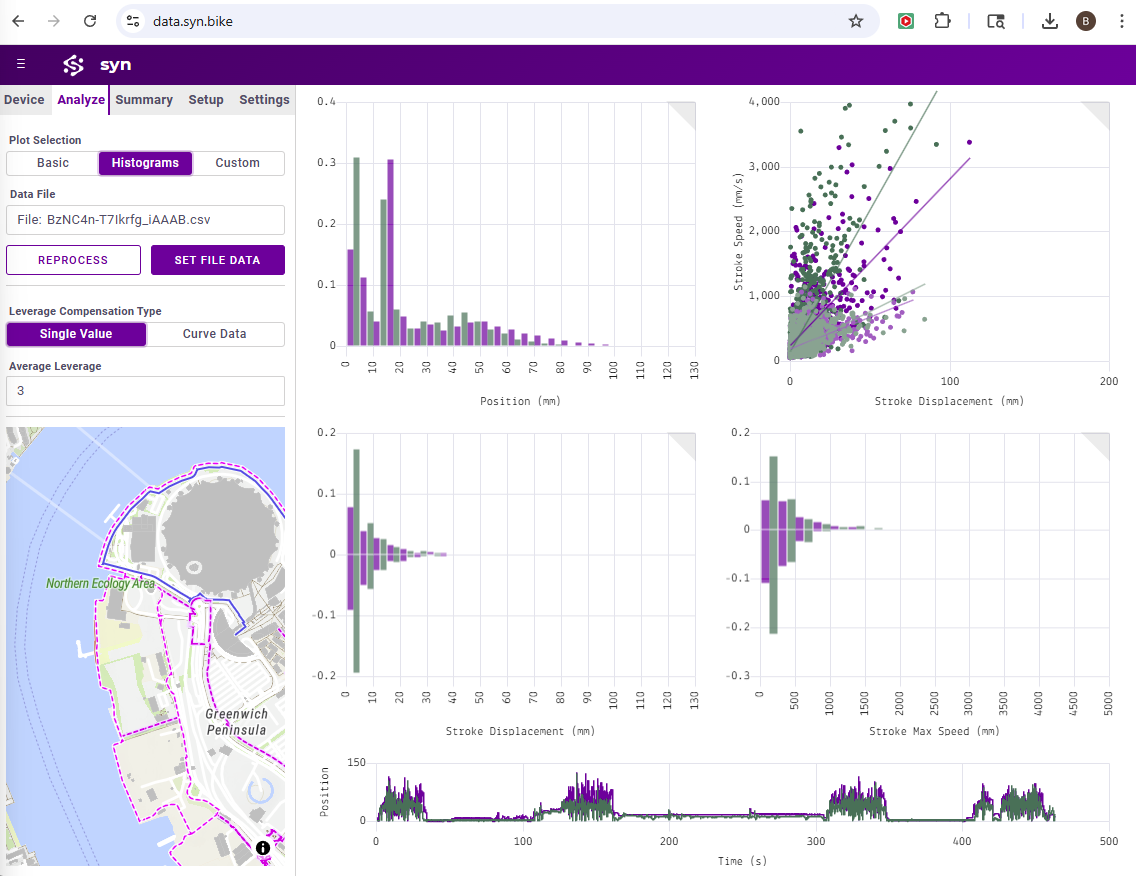
bodocs/src/assets/pics/user-guide/synoutputs.png
