benconnor1972/BODAQS/bodocs/src/assets/pics/user-guide/upload_active.png

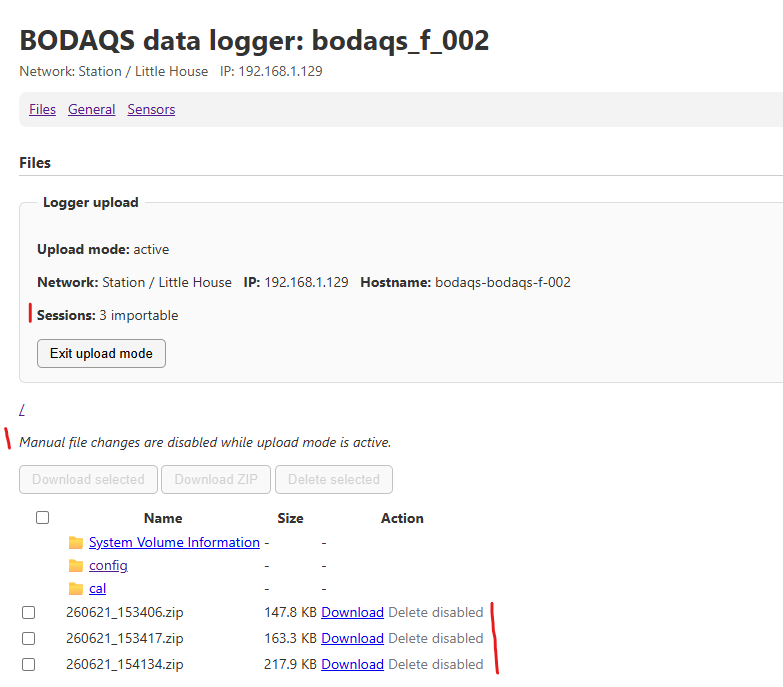
bodocs/src/assets/pics/user-guide/upload_active.png
