benconnor1972/BODAQS/bodocs/src/assets/pics/user-guide/use-import-manager.png

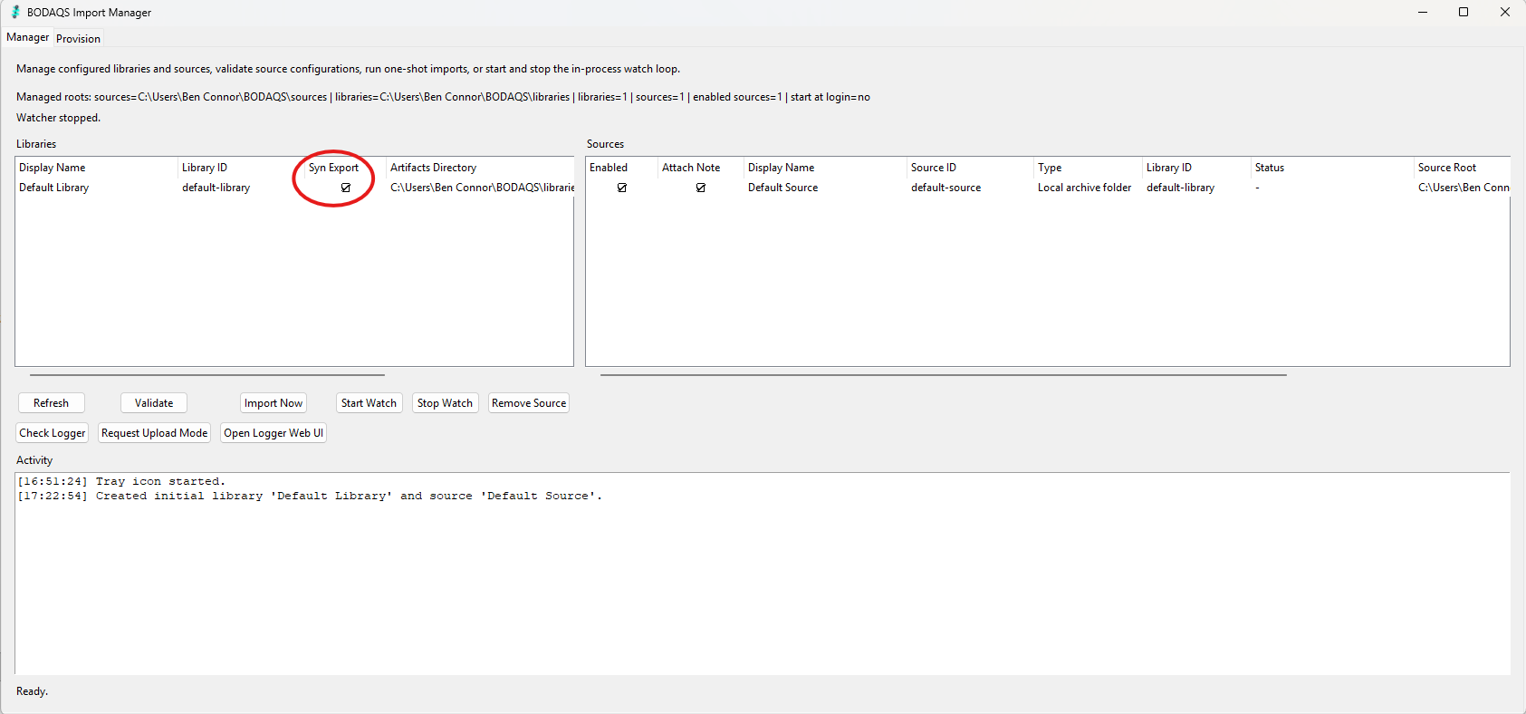
bodocs/src/assets/pics/user-guide/use-import-manager.png
