benconnor1972/BODAQS/bodocs/src/assets/pics/user-guide/wifi-discover-loggers.png

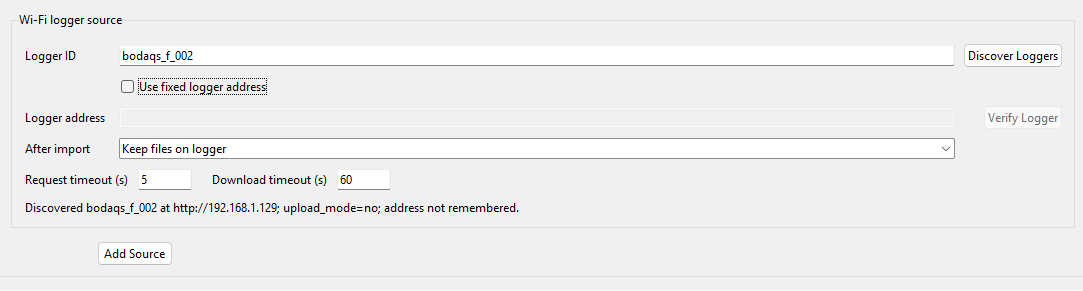
bodocs/src/assets/pics/user-guide/wifi-discover-loggers.png
