benconnor1972/BODAQS/bodocs/src/assets/pics/user-guide/wifi.png

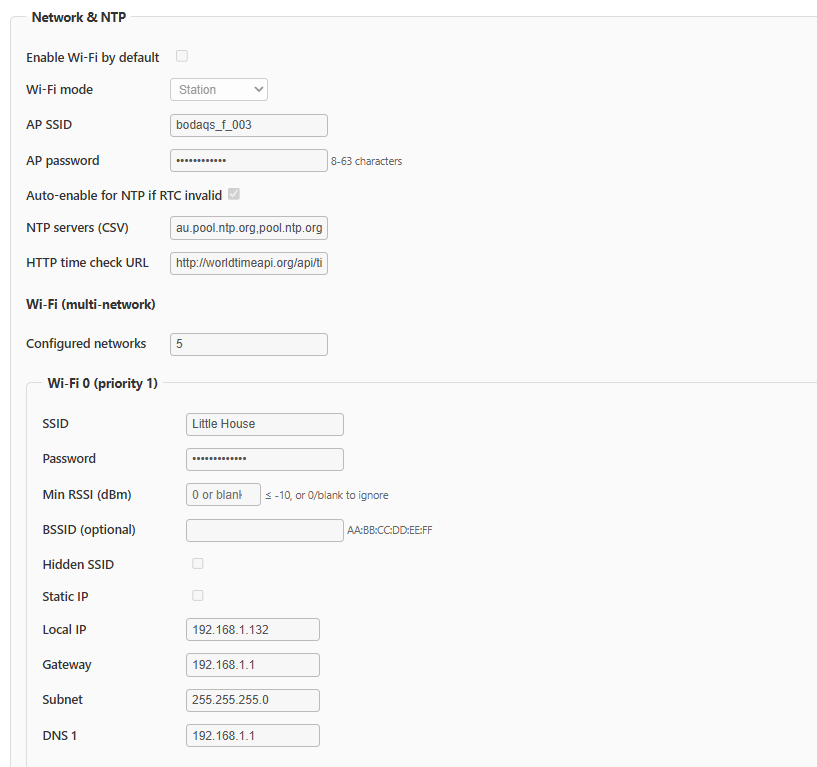
bodocs/src/assets/pics/user-guide/wifi.png
