benconnor1972/BODAQS/bodocs/src/assets/pics/user-guide/wifion.png

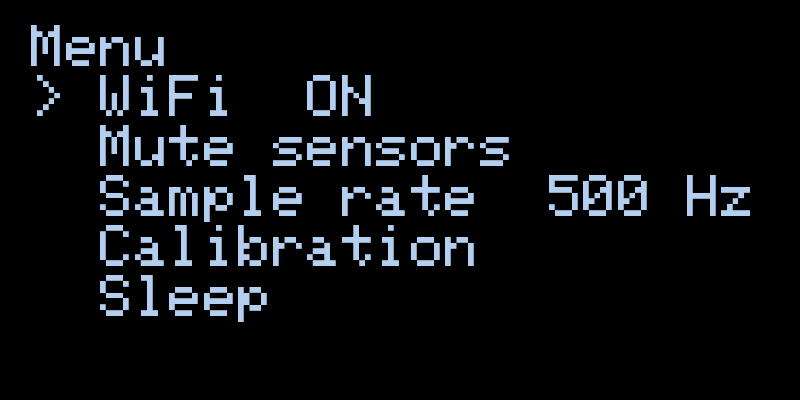
bodocs/src/assets/pics/user-guide/wifion.png
