benconnor1972/BODAQS/bodocs/src/assets/pics/user-guide/calibration.png

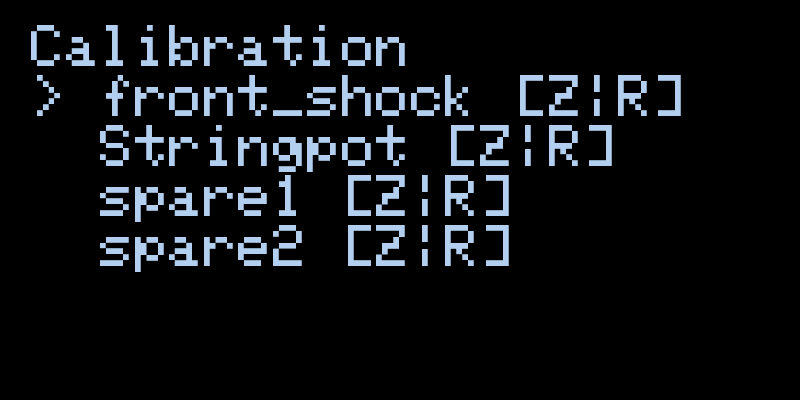
bodocs/src/assets/pics/user-guide/calibration.png
