benconnor1972/BODAQS/bodocs/src/assets/pics/user-guide/oled-zero-calibration.png

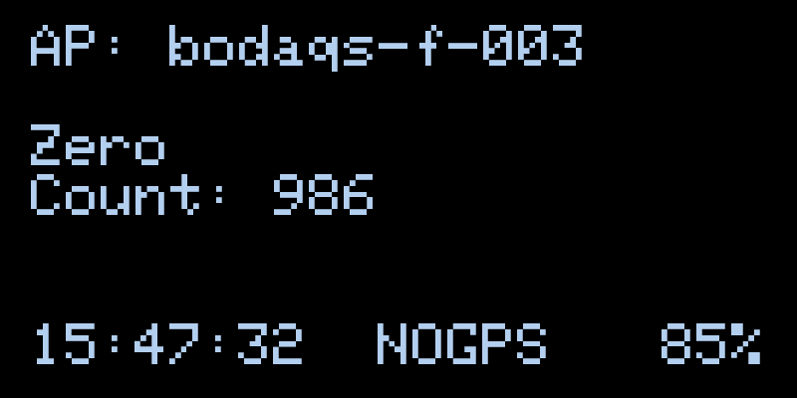
bodocs/src/assets/pics/user-guide/oled-zero-calibration.png
