benconnor1972/BODAQS/bodocs/src/assets/pics/user-guide/sensorcalibration.png

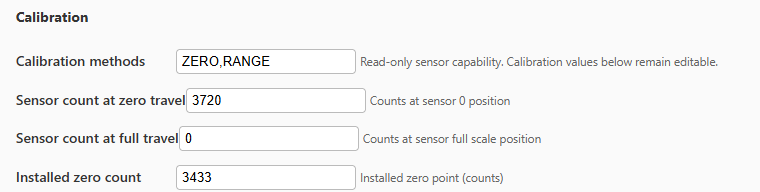
bodocs/src/assets/pics/user-guide/sensorcalibration.png
