benconnor1972/BODAQS/analysis/bodaqs_analysis/import_agent.py

from __future__ import annotations

import argparse
import hashlib
import json
import logging
import os
import re
import shutil
import socket
import tempfile
import time
import urllib.error
import urllib.parse
import urllib.request
from dataclasses import dataclass, field
from datetime import datetime, timezone
from pathlib import Path
from queue import Empty, Queue
from threading import RLock, Thread
from typing import Any, Callable, Dict, Iterable, Mapping, Optional, Sequence

import pandas as pd

from .artifacts import (
    ArtifactStore,
    copy_session_aux_sources,
    copy_raw_input_to_source,
    ensure_run_is_new,
    ensure_session_is_new,
    save_session_artifacts,
    write_events_partitioned_by_schema_id,
    write_metrics_partitioned_by_schema_id,
    write_run_manifest,
    write_session_manifest,
)
from .bike_profile import load_bike_profile
from .exporters.data_syn_bike import (
    bike_profile_travel_ranges,
    data_syn_bike_manual_settings,
    default_data_syn_bike_export_config,
    export_data_syn_bike_resolved,
    render_data_syn_bike_manual_settings_text,
    write_data_syn_bike_exports,
)
from .import_agent_logger_wifi import LoggerWifiApiClient
from .import_agent_logger_wifi_discovery import (
    LoggerWifiDiscoveryError,
    LoggerWifiDiscoveryUnavailable,
    discover_single_logger_wifi_source,
)
from .io_bdq import is_bdq_path, read_bdq, validate_bdq_importable
from .io_fit import refresh_fit_inspection_index
from .pipeline import preprocess_session
from .preprocess_profile import load_preprocess_config, resolve_preprocess_config_paths
from .raw_signal_dropouts import RAW_SIGNAL_DROPOUT_BEHAVIOR_VERSION
from .session_note_presets import BikeSetupPreset, load_bike_setup_preset
from .session_notes import (
    SessionNoteStore,
    SessionNoteTemplate,
    SessionNoteTemplateStore,
    library_session_note_template_root,
)
from .session_archive import (
    SessionArchiveContract,
    bdq_session_identity as make_bdq_session_identity,
    extract_session_archive,
    raw_session_identity as make_raw_session_identity,
    read_session_archive_contract,
)
from .import_agent_sources import (
    LOGGER_WIFI_CLEANUP_NONE,
    LoggerWifiSourceConfig,
    SOURCE_TYPE_FILESYSTEM_ARCHIVE,
    SOURCE_TYPE_LOGGER_WIFI,
    normalize_import_source_type,
    parse_logger_wifi_source_config,
)
from .library_api.catalog_revision import touch_catalog_revision


IMPORT_SOURCE_SCHEMA = "bodaqs.import_source"
IMPORT_SOURCE_VERSION = 1
IMPORT_AGENT_STATE_SCHEMA = "bodaqs.import_agent_state"
IMPORT_AGENT_STATE_VERSION = 1
DEFAULT_ARCHIVE_PATTERNS = ("*.zip", "*.ZIP", "*.bdq", "*.BDQ")
DEFAULT_DATA_SYN_BIKE_EXPORT_FILENAME_TEMPLATE = "{run_id}__{session_id}__{export_id}__data_syn_bike.csv"
DEFAULT_DATA_SYN_BIKE_SETTINGS_FILENAME_TEMPLATE = "{run_id}__{session_id}__data_syn_bike_settings.txt"
DATA_SYN_BIKE_LIBRARY_MANIFEST_FILENAME = "data_syn_bike_export_manifest.json"
DEFAULT_SESSION_NOTE_DIRNAME = "notes"
SESSION_NAMING_MODE_DEFAULT = "default"
SESSION_NAMING_MODE_BASE_INDEX = "base_index"
DEFAULT_LIBRARY_API_BASE_URL = "http://127.0.0.1:8765"
LIBRARY_API_NOTIFICATION_TIMEOUT_S = 0.75

logger = logging.getLogger(__name__)

ImportProgressCallback = Callable[[Mapping[str, Any]], None]


def _normalize_archive_patterns(patterns: Sequence[str]) -> tuple[str, ...]:
    normalized: list[str] = []
    seen: set[str] = set()
    for pattern in patterns:
        text = str(pattern).strip()
        if not text:
            continue
        key = text.lower()
        if key in seen:
            continue
        seen.add(key)
        normalized.append(text)

    lower = {item.lower() for item in normalized}
    if "*.zip" in lower and "*.bdq" not in lower:
        normalized.extend(["*.bdq", "*.BDQ"])
    return tuple(normalized)


def _utcnow_iso() -> str:
    return datetime.now(timezone.utc).isoformat(timespec="seconds")


def _emit_import_progress(
    progress_callback: Optional[ImportProgressCallback],
    event: str,
    **payload: Any,
) -> None:
    if progress_callback is None:
        return
    message = {
        "event": event,
        "updated_at": _utcnow_iso(),
        **payload,
    }
    try:
        progress_callback(message)
    except Exception:
        logger.warning("Import progress callback failed for event %s", event, exc_info=True)


def _optional_text(value: Any) -> Optional[str]:
    text = "" if value is None else str(value).strip()
    return text or None


def _safe_float(value: Any, *, field_name: str) -> float:
    try:
        number = float(value)
    except (TypeError, ValueError):
        raise ValueError(f"{field_name} must be numeric") from None
    if number < 0:
        raise ValueError(f"{field_name} must be >= 0")
    return number


def _sha256_file(path: Path, *, chunk_size: int = 1024 * 1024) -> str:
    h = hashlib.sha256()
    with path.open("rb") as f:
        for chunk in iter(lambda: f.read(chunk_size), b""):
            h.update(chunk)
    return h.hexdigest()


def _sha256_jsonable(value: Any) -> str:
    payload = json.dumps(value, sort_keys=True, separators=(",", ":")).encode("utf-8")
    return hashlib.sha256(payload).hexdigest()


def _ensure_dir(path: Path) -> None:
    path.mkdir(parents=True, exist_ok=True)


def _read_json(path: Path, default: Any) -> Any:
    try:
        if path.exists():
            return json.loads(path.read_text(encoding="utf-8"))
    except Exception:
        pass
    return default


def _write_json_atomic(path: Path, obj: Mapping[str, Any]) -> None:
    _ensure_dir(path.parent)
    tmp = path.with_suffix(path.suffix + ".tmp")
    tmp.write_text(json.dumps(obj, indent=2, sort_keys=True), encoding="utf-8")
    os.replace(tmp, path)


def _library_api_base_url() -> str:
    configured = (
        _optional_text(os.environ.get("BODAQS_LIBRARY_API_BASE_URL"))
        or _optional_text(os.environ.get("BODAQS_LIBRARY_API_URL"))
        or DEFAULT_LIBRARY_API_BASE_URL
    )
    return configured.rstrip("/")


def _library_id_for_api_notification(source: "ImportSourceConfig") -> Optional[str]:
    if source.library_id:
        return source.library_id
    definition = _read_json(source.artifacts_dir / "library_definition.json", {})
    if isinstance(definition, Mapping):
        return _optional_text(definition.get("library_id"))
    return None


def _notify_library_api_catalog_changed(
    source: "ImportSourceConfig",
    *,
    changed_sessions: Sequence[Mapping[str, Any]] | None = None,
) -> Dict[str, Any]:
    library_id = _library_id_for_api_notification(source)
    if library_id is None:
        return {
            "attempted": False,
            "reason": "missing_library_id",
        }

    base_url = _library_api_base_url()
    quoted_library_id = urllib.parse.quote(library_id, safe="")
    url = f"{base_url}/api/v1/libraries/{quoted_library_id}/catalog/invalidate"
    payload = json.dumps(
        {
            "warm": True,
            "changed_sessions": [dict(item) for item in changed_sessions or []],
        }
    ).encode("utf-8")
    request = urllib.request.Request(
        url,
        data=payload,
        method="POST",
        headers={"Content-Type": "application/json"},
    )
    try:
        with urllib.request.urlopen(request, timeout=LIBRARY_API_NOTIFICATION_TIMEOUT_S) as response:
            status_code = int(getattr(response, "status", 0) or response.getcode())
            return {
                "attempted": True,
                "notified": 200 <= status_code < 300,
                "library_id": library_id,
                "url": url,
                "status_code": status_code,
            }
    except (OSError, urllib.error.URLError, TimeoutError) as exc:
        logger.debug(
            "Library API catalog invalidation notification failed for library %s via %s: %s",
            library_id,
            url,
            exc,
        )
        return {
            "attempted": True,
            "notified": False,
            "library_id": library_id,
            "url": url,
            "error": f"{type(exc).__name__}: {exc}",
        }


def _imported_session_revision_records(
    source: "ImportSourceConfig",
    imported: Sequence[Mapping[str, Any]],
) -> list[dict[str, Any]]:
    library_id = _library_id_for_api_notification(source)
    records: list[dict[str, Any]] = []
    for item in imported:
        run_id = _optional_text(item.get("run_id"))
        session_id = _optional_text(item.get("session_id"))
        session_key = _optional_text(item.get("session_key"))
        record: dict[str, Any] = {}
        if library_id is not None:
            record["library_id"] = library_id
        if run_id is not None:
            record["run_id"] = run_id
        if session_id is not None:
            record["session_id"] = session_id
        if session_key is not None:
            record["session_key"] = session_key
        elif run_id is not None and session_id is not None:
            record["session_key"] = f"{run_id}::{session_id}"
        if record:
            records.append(record)
    return records


def _library_data_syn_bike_export_config(artifacts_dir: Path) -> Optional[Dict[str, Any]]:
    metadata = _read_json(artifacts_dir / "library_definition.json", {})
    if not isinstance(metadata, Mapping):
        return None
    exports = metadata.get("exports")
    data_syn_bike = exports.get("data_syn_bike") if isinstance(exports, Mapping) else None
    if data_syn_bike is None:
        data_syn_bike = metadata.get("data_syn_bike_export")
    if not isinstance(data_syn_bike, Mapping) or not bool(data_syn_bike.get("enabled", False)):
        return None

    cfg = {
        "adc_bit_count": 12,
        "raw_scale_mode": "processed_wheel_travel",
        "clip_raw_to_adc_range": True,
        "drop_inactive": True,
        "split_by_activity": False,
        "sample_count_origin": "session",
        "filename_template": DEFAULT_DATA_SYN_BIKE_EXPORT_FILENAME_TEMPLATE,
    }
    cfg.update({k: v for k, v in data_syn_bike.items() if k != "enabled"})
    if cfg.get("raw_scale_mode") == "calibrated_full_scale":
        # Earlier alpha library metadata used this mode by default. The manager
        # now exports synthetic wheel-travel raw so syn.bike matches JLab views.
        cfg["raw_scale_mode"] = "processed_wheel_travel"
    return cfg


def _bike_profile_syn_raw_full_scale_by_end(bike_profile: Mapping[str, Any]) -> dict[str, float]:
    ranges = bike_profile_travel_ranges(bike_profile)
    out: dict[str, float] = {}
    front_wheel = ranges.get("front_wheel")
    rear_wheel = ranges.get("rear_wheel")
    if front_wheel is not None and front_wheel > 0:
        out["front"] = float(front_wheel)
    if rear_wheel is not None and rear_wheel > 0:
        out["rear"] = float(rear_wheel)
    return out


def _render_data_syn_bike_settings_filename(run_id: str, session_id: str) -> str:
    return DEFAULT_DATA_SYN_BIKE_SETTINGS_FILENAME_TEMPLATE.format(
        run_id=_safe_filename_component(run_id),
        session_id=_safe_filename_component(session_id),
    )


def _safe_filename_component(value: str) -> str:
    text = str(value or "").strip() or "session"
    return re.sub(r"[^A-Za-z0-9_.-]+", "_", text)


def _compact_import_run_id(source_id: str) -> str:
    source_part = _safe_filename_component(source_id).strip("._-") or "source"
    compact_ts = datetime.now().strftime("%y%m%d_%H%M%S")
    return f"{source_part}_{compact_ts}"


def _path_key(path: Path) -> str:
    try:
        return str(path.resolve()).lower()
    except Exception:
        return str(path).replace("\\", "/").lower()


def _resolve_source_path(path_or_dir: str | Path) -> Path:
    p = Path(path_or_dir).expanduser()
    if p.is_dir():
        return (p / "import_source.json").resolve()
    return p.resolve()


def _resolve_relative_path(value: str | Path, *, base_dir: Path) -> Path:
    path = Path(value)
    return path.resolve() if path.is_absolute() else (base_dir / path).resolve()


def _summarize_candidates(paths: Sequence[Path], *, limit: int = 5) -> str:
    shown = [path.name for path in paths[:limit]]
    summary = ", ".join(shown)
    if len(paths) > limit:
        summary += f", +{len(paths) - limit} more"
    return summary


def _resolve_single_valid_json_file(
    path_or_dir: Path,
    *,
    label: str,
    loader: Any,
) -> Path:
    if not path_or_dir.exists():
        raise FileNotFoundError(f"{label} path not found: {path_or_dir}")

    if path_or_dir.is_file():
        loader(path_or_dir)
        return path_or_dir.resolve()

    if not path_or_dir.is_dir():
        raise ValueError(f"{label} path must be a file or directory: {path_or_dir}")

    valid_paths: list[Path] = []
    invalid_records: list[tuple[Path, Exception]] = []

    for candidate in sorted(path_or_dir.iterdir()):
        if not candidate.is_file() or candidate.suffix.lower() != ".json":
            continue
        try:
            loader(candidate)
        except Exception as exc:
            invalid_records.append((candidate, exc))
            continue
        valid_paths.append(candidate.resolve())

    if len(valid_paths) == 1:
        return valid_paths[0]

    if len(valid_paths) > 1:
        raise ValueError(
            f"{label} directory must contain exactly one valid JSON file: {path_or_dir} "
            f"(found {len(valid_paths)} valid files: {_summarize_candidates(valid_paths)})"
        )

    if invalid_records:
        invalid_details = "; ".join(
            f"{path.name} ({type(exc).__name__}: {exc})"
            for path, exc in invalid_records[:3]
        )
        if len(invalid_records) > 3:
            invalid_details += f"; +{len(invalid_records) - 3} more"
        raise ValueError(
            f"{label} directory must contain exactly one valid JSON file: {path_or_dir} "
            f"(found 0 valid files; invalid candidates: {invalid_details})"
        )

    raise FileNotFoundError(
        f"{label} directory must contain exactly one valid JSON file, but none were found: {path_or_dir}"
    )


def _move_to_dir_unique(src: Path, dst_dir: Path, *, touch_mtime: bool = False) -> Path:
    _ensure_dir(dst_dir)
    candidate = dst_dir / src.name
    if not candidate.exists():
        src.replace(candidate)
        if touch_mtime:
            os.utime(candidate, None)
        return candidate

    stem = candidate.stem
    suffix = candidate.suffix
    for idx in range(1, 10000):
        alt = dst_dir / f"{stem}_{idx:02d}{suffix}"
        if alt.exists():
            continue
        src.replace(alt)
        if touch_mtime:
            os.utime(alt, None)
        return alt
    raise FileExistsError(f"Could not find a unique destination for {src} in {dst_dir}")


class ImportAgentLock:
    """
    Best-effort single-writer lock per artifact library.
    """

    def __init__(self, path: Path, *, stale_after_s: float = 12 * 60 * 60) -> None:
        self.path = path
        self.stale_after_s = float(stale_after_s)
        self._held = False

    def acquire(self) -> None:
        _ensure_dir(self.path.parent)
        payload = {
            "schema": "bodaqs.import_agent.lock",
            "created_at": _utcnow_iso(),
            "host": socket.gethostname(),
            "pid": os.getpid(),
        }

        while True:
            try:
                fd = os.open(str(self.path), os.O_CREAT | os.O_EXCL | os.O_WRONLY)
                with os.fdopen(fd, "w", encoding="utf-8") as f:
                    json.dump(payload, f, indent=2, sort_keys=True)
                self._held = True
                return
            except FileExistsError:
                if not self._clear_if_stale():
                    existing = _read_json(self.path, {})
                    raise FileExistsError(
                        "Import agent output library is locked by another process: "
                        f"{self.path} ({existing})"
                    ) from None

    def _clear_if_stale(self) -> bool:
        if self.stale_after_s <= 0 or not self.path.exists():
            return False
        try:
            age_s = time.time() - self.path.stat().st_mtime
        except OSError:
            return False
        if age_s < self.stale_after_s:
            return False
        try:
            self.path.unlink()
            logger.warning("Removed stale import-agent lock: %s", self.path)
            return True
        except OSError:
            return False

    def release(self) -> None:
        if not self._held:
            return
        try:
            if self.path.exists():
                self.path.unlink()
        finally:
            self._held = False

    def __enter__(self) -> "ImportAgentLock":
        self.acquire()
        return self

    def __exit__(self, _exc_type, _exc, _tb) -> None:
        self.release()


class ImportAgentState:
    def __init__(self, path: Path) -> None:
        self.path = path
        self._lock = RLock()
        self.data: dict[str, Any] = {
            "schema": IMPORT_AGENT_STATE_SCHEMA,
            "version": IMPORT_AGENT_STATE_VERSION,
            "updated_at": _utcnow_iso(),
            "records": {},
        }
        self.load()

    def load(self) -> None:
        with self._lock:
            obj = _read_json(self.path, self.data)
            if not isinstance(obj, dict):
                return
            if obj.get("schema") != IMPORT_AGENT_STATE_SCHEMA:
                return
            if int(obj.get("version", -1)) != IMPORT_AGENT_STATE_VERSION:
                return
            records = obj.get("records")
            self.data = {
                "schema": IMPORT_AGENT_STATE_SCHEMA,
                "version": IMPORT_AGENT_STATE_VERSION,
                "updated_at": str(obj.get("updated_at") or _utcnow_iso()),
                "records": records if isinstance(records, dict) else {},
            }

    def save(self) -> None:
        with self._lock:
            self.data["updated_at"] = _utcnow_iso()
            _write_json_atomic(self.path, self.data)

    def get(self, key: str) -> Optional[Dict[str, Any]]:
        with self._lock:
            records = self.data.get("records")
            if not isinstance(records, dict):
                return None
            record = records.get(key)
            return dict(record) if isinstance(record, dict) else None

    def records(self) -> dict[str, Dict[str, Any]]:
        with self._lock:
            records = self.data.get("records")
            if not isinstance(records, dict):
                return {}
            return {
                str(key): dict(value)
                for key, value in records.items()
                if isinstance(value, dict)
            }

    def upsert(self, key: str, record: Mapping[str, Any]) -> None:
        with self._lock:
            records = self.data.setdefault("records", {})
            if not isinstance(records, dict):
                raise ValueError("Import agent state records store is corrupted")
            records[key] = dict(record)
            self.save()


@dataclass(frozen=True)
class ImportSourceSessionNoteConfig:
    attach_on_import: bool = False
    template_path: Optional[Path] = None
    setup_preset_path: Optional[Path] = None


@dataclass(frozen=True)
class ImportSourceSessionNamingConfig:
    enabled: bool = False
    mode: str = SESSION_NAMING_MODE_DEFAULT
    base: Optional[str] = None
    index_start: int = 1
    index_padding: int = 2

    def __post_init__(self) -> None:
        if self.mode not in {SESSION_NAMING_MODE_DEFAULT, SESSION_NAMING_MODE_BASE_INDEX}:
            raise ValueError(f"Unsupported session naming mode: {self.mode!r}")
        if int(self.index_start) < 0:
            raise ValueError("session naming index_start must be >= 0")
        if int(self.index_padding) < 0:
            raise ValueError("session naming index_padding must be >= 0")
        if self.enabled and self.mode == SESSION_NAMING_MODE_BASE_INDEX and _optional_text(self.base) is None:
            raise ValueError("session naming base is required when base-index naming is enabled")


@dataclass(frozen=True)
class ImportSourceNamingConfig:
    session_description: ImportSourceSessionNamingConfig = field(
        default_factory=ImportSourceSessionNamingConfig
    )


def _parse_session_naming_config(raw: Any) -> ImportSourceSessionNamingConfig:
    if raw is None:
        return ImportSourceSessionNamingConfig()
    if not isinstance(raw, Mapping):
        raise ValueError("Import source naming.session_description must be an object when provided")

    enabled = bool(raw.get("enabled", False))
    mode = _optional_text(raw.get("mode"))
    if mode is None:
        mode = SESSION_NAMING_MODE_BASE_INDEX if enabled else SESSION_NAMING_MODE_DEFAULT

    try:
        index_start = int(raw.get("index_start", 1))
    except (TypeError, ValueError):
        raise ValueError("session naming index_start must be an integer") from None
    try:
        index_padding = int(raw.get("index_padding", 2))
    except (TypeError, ValueError):
        raise ValueError("session naming index_padding must be an integer") from None

    return ImportSourceSessionNamingConfig(
        enabled=enabled,
        mode=mode,
        base=_optional_text(raw.get("base")),
        index_start=index_start,
        index_padding=index_padding,
    )


def _parse_import_source_naming_config(raw: Any) -> ImportSourceNamingConfig:
    if raw is None:
        return ImportSourceNamingConfig()
    if not isinstance(raw, Mapping):
        raise ValueError("Import source naming must be an object when provided")
    return ImportSourceNamingConfig(
        session_description=_parse_session_naming_config(raw.get("session_description")),
    )


@dataclass(frozen=True)
class ImportSourceConfig:
    config_path: Path
    source_root: Path
    source_id: str
    source_type: str
    artifacts_dir: Path
    preprocess_profile_path: Path
    bike_profile_path: Path
    fit_dir: Path
    inbox_dir: Path
    done_dir: Path
    failed_dir: Path
    staging_dir: Path
    archive_patterns: tuple[str, ...] = DEFAULT_ARCHIVE_PATTERNS
    logger_timezone: Optional[str] = None
    run_tz_label: str = "AWST"
    poll_interval_s: float = 5.0
    settle_time_s: float = 15.0
    include_events: bool = True
    include_metrics: bool = True
    description: Optional[str] = None
    force_reprocess: bool = False
    max_archives_per_scan: Optional[int] = None
    processed_archive_retention_days: Optional[int] = 30
    library_id: Optional[str] = None
    logger_wifi: Optional[LoggerWifiSourceConfig] = None
    session_note: ImportSourceSessionNoteConfig = field(default_factory=ImportSourceSessionNoteConfig)
    naming: ImportSourceNamingConfig = field(default_factory=ImportSourceNamingConfig)

    def __post_init__(self) -> None:
        if not self.source_id.strip():
            raise ValueError("Import source config must include a non-empty source_id")
        if self.source_type != normalize_import_source_type(self.source_type):
            raise ValueError(f"Import source config has unsupported source_type: {self.source_type!r}")
        if self.source_type == SOURCE_TYPE_LOGGER_WIFI and self.logger_wifi is None:
            raise ValueError("logger_wifi import sources must include a logger_wifi config block")
        if not self.archive_patterns:
            raise ValueError("Import source config must include at least one archive pattern")
        if self.max_archives_per_scan is not None and int(self.max_archives_per_scan) <= 0:
            raise ValueError("max_archives_per_scan must be > 0 when provided")
        if self.processed_archive_retention_days is not None and int(self.processed_archive_retention_days) <= 0:
            raise ValueError("processed_archive_retention_days must be > 0 or null to retain forever")
        if self.session_note.attach_on_import and (
            self.session_note.template_path is None or self.session_note.setup_preset_path is None
        ):
            raise ValueError("session_note attach_on_import requires template_path and setup_preset_path")


@dataclass(frozen=True)
class ImportArchiveCandidate:
    source: ImportSourceConfig
    inbox_archive_path: Path
    claimed_archive_path: Path
    archive_name: str
    archive_sha256: str
    archive_size_bytes: int
    archive_mtime_ns: int
    contract: Optional[SessionArchiveContract]
    input_kind: str
    source_identity_kind: str
    raw_session_identity: str
    processing_key: str


@dataclass
class ImportRunBatch:
    run_id: Optional[str] = None
    run_description_override: Optional[str] = None
    session_ids: list[str] = field(default_factory=list)
    archive_import_by_session: Dict[str, Dict[str, Any]] = field(default_factory=dict)
    fit_candidates: Optional[list[Dict[str, Any]]] = None
    fit_parsed_cache: Dict[str, tuple[pd.DataFrame, Dict[str, Any]]] = field(default_factory=dict)
    fit_index_stats: Optional[Dict[str, Any]] = None

    def add_session(self, session_id: str, archive_import_config: Mapping[str, Any]) -> None:
        if session_id not in self.session_ids:
            self.session_ids.append(session_id)
        self.archive_import_by_session[session_id] = dict(archive_import_config)

    def remove_session(self, session_id: str) -> None:
        self.session_ids = [item for item in self.session_ids if item != session_id]
        self.archive_import_by_session.pop(session_id, None)


@dataclass(frozen=True)
class LoggerWifiArchiveAcquisition:
    remote_state_key: str
    remote_session_id: str
    logger_id: str
    base_url: str
    local_archive_path: Path
    data_format: str = "csv_zip"
    remote_already_acknowledged: bool = False


@dataclass
class ImportSourceSupervisorState:
    runner: "ImportSourceRunner"
    paused: bool = False
    next_due_s: float = 0.0
    last_scan_started_at: Optional[str] = None
    last_scan_completed_at: Optional[str] = None
    last_report: Optional[Dict[str, Any]] = None


def load_import_source_config(path_or_dir: str | Path) -> ImportSourceConfig:
    config_path = _resolve_source_path(path_or_dir)
    if not config_path.exists():
        raise FileNotFoundError(f"Import source config not found: {config_path}")

    obj = json.loads(config_path.read_text(encoding="utf-8"))
    if not isinstance(obj, dict):
        raise ValueError("Import source config must be a JSON object")
    if obj.get("schema") != IMPORT_SOURCE_SCHEMA:
        raise ValueError(
            f"Unexpected import source schema: {obj.get('schema')!r} "
            f"(expected {IMPORT_SOURCE_SCHEMA!r})"
        )
    if int(obj.get("version", -1)) != IMPORT_SOURCE_VERSION:
        raise ValueError(
            f"Unexpected import source version: {obj.get('version')!r} "
            f"(expected {IMPORT_SOURCE_VERSION})"
        )

    base_dir = config_path.parent.resolve()
    source_id = _optional_text(obj.get("source_id"))
    if source_id is None:
        raise ValueError("Import source config missing non-empty 'source_id'")
    source_type = normalize_import_source_type(obj.get("source_type"))

    logger_wifi: Optional[LoggerWifiSourceConfig] = None
    if source_type == SOURCE_TYPE_LOGGER_WIFI:
        logger_wifi = parse_logger_wifi_source_config(obj.get("logger_wifi"))

    archive_patterns_raw = obj.get("archive_patterns")
    if archive_patterns_raw is None:
        archive_patterns = DEFAULT_ARCHIVE_PATTERNS
    elif isinstance(archive_patterns_raw, list) and archive_patterns_raw:
        archive_patterns = _normalize_archive_patterns(
            str(x).strip()
            for x in archive_patterns_raw
            if _optional_text(x) is not None
        )
        if not archive_patterns:
            raise ValueError("Import source archive_patterns list is empty")
    else:
        raise ValueError("Import source archive_patterns must be a non-empty list when provided")

    max_archives_per_scan_raw = obj.get("max_archives_per_scan")
    max_archives_per_scan: Optional[int] = None
    if max_archives_per_scan_raw is not None:
        try:
            max_archives_per_scan = int(max_archives_per_scan_raw)
        except (TypeError, ValueError):
            raise ValueError("max_archives_per_scan must be an integer when provided") from None

    processed_archive_retention_days_raw = obj.get("processed_archive_retention_days", 30)
    processed_archive_retention_days: Optional[int]
    if processed_archive_retention_days_raw is None:
        processed_archive_retention_days = None
    elif isinstance(processed_archive_retention_days_raw, bool):
        raise ValueError("processed_archive_retention_days must be a positive integer or null")
    else:
        try:
            processed_archive_retention_days = int(processed_archive_retention_days_raw)
        except (TypeError, ValueError):
            raise ValueError("processed_archive_retention_days must be a positive integer or null") from None

    session_note_raw = obj.get("session_note")
    if session_note_raw is None:
        session_note = ImportSourceSessionNoteConfig()
    elif not isinstance(session_note_raw, Mapping):
        raise ValueError("Import source session_note must be an object when provided")
    else:
        attach_on_import = bool(session_note_raw.get("attach_on_import", False))
        session_note = ImportSourceSessionNoteConfig(
            attach_on_import=attach_on_import,
            template_path=_resolve_relative_path(
                _optional_text(session_note_raw.get("template_path")) or DEFAULT_SESSION_NOTE_DIRNAME,
                base_dir=base_dir,
            ),
            setup_preset_path=_resolve_relative_path(
                _optional_text(session_note_raw.get("setup_preset_path")) or DEFAULT_SESSION_NOTE_DIRNAME,
                base_dir=base_dir,
            ),
        )

    naming = _parse_import_source_naming_config(obj.get("naming"))

    return ImportSourceConfig(
        config_path=config_path,
        source_root=base_dir,
        source_id=source_id,
        source_type=source_type,
        artifacts_dir=_resolve_relative_path(
            _optional_text(obj.get("artifacts_dir")) or "artifacts",
            base_dir=base_dir,
        ),
        preprocess_profile_path=_resolve_relative_path(
            _optional_text(obj.get("preprocess_profile_path")) or "preprocess_profile.json",
            base_dir=base_dir,
        ),
        bike_profile_path=_resolve_relative_path(
            _optional_text(obj.get("bike_profile_path")) or "bike_profile.json",
            base_dir=base_dir,
        ),
        fit_dir=_resolve_relative_path(
            _optional_text(obj.get("fit_dir")) or "fit",
            base_dir=base_dir,
        ),
        inbox_dir=_resolve_relative_path(
            _optional_text(obj.get("inbox_dir")) or "inbox",
            base_dir=base_dir,
        ),
        done_dir=_resolve_relative_path(
            _optional_text(obj.get("done_dir")) or "done",
            base_dir=base_dir,
        ),
        failed_dir=_resolve_relative_path(
            _optional_text(obj.get("failed_dir")) or "failed",
            base_dir=base_dir,
        ),
        staging_dir=_resolve_relative_path(
            _optional_text(obj.get("staging_dir")) or "staging",
            base_dir=base_dir,
        ),
        archive_patterns=archive_patterns,
        logger_timezone=_optional_text(obj.get("logger_timezone")),
        run_tz_label=_optional_text(obj.get("run_tz_label")) or "AWST",
        poll_interval_s=_safe_float(obj.get("poll_interval_s", 5.0), field_name="poll_interval_s"),
        settle_time_s=_safe_float(obj.get("settle_time_s", 15.0), field_name="settle_time_s"),
        include_events=True,
        include_metrics=True,
        description=_optional_text(obj.get("description")),
        force_reprocess=bool(obj.get("force_reprocess", False)),
        max_archives_per_scan=max_archives_per_scan,
        processed_archive_retention_days=processed_archive_retention_days,
        library_id=_optional_text(obj.get("library_id")),
        logger_wifi=logger_wifi,
        session_note=session_note,
        naming=naming,
    )


class ImportSourceRunner:
    def __init__(
        self,
        source: ImportSourceConfig,
        *,
        store: Optional[ArtifactStore] = None,
        state_path: Optional[Path] = None,
    ) -> None:
        self.source = source
        self.store = store or ArtifactStore(source.artifacts_dir)
        self.state = ImportAgentState(
            state_path or (self.store.path_library_dir() / "import_agent_state_v1.json")
        )
        self.lock = ImportAgentLock(self.store.path_library_dir() / "import_agent.lock")
        self.preprocess_profile_sha256: Optional[str] = None
        self.effective_preprocess_config_sha256: Optional[str] = None
        self.bike_profile_sha256: Optional[str] = None
        self.preprocess_config: Optional[Dict[str, Any]] = None
        self.resolved_preprocess_profile_path: Optional[Path] = None
        self.resolved_bike_profile_path: Optional[Path] = None

    def _resolve_preprocess_profile_path(self) -> Path:
        if self.resolved_preprocess_profile_path is None:
            self.resolved_preprocess_profile_path = _resolve_single_valid_json_file(
                self.source.preprocess_profile_path,
                label="Preprocess profile",
                loader=load_preprocess_config,
            )
        return self.resolved_preprocess_profile_path

    def _resolve_bike_profile_path(self) -> Path:
        if self.resolved_bike_profile_path is None:
            self.resolved_bike_profile_path = _resolve_single_valid_json_file(
                self.source.bike_profile_path,
                label="Bike profile",
                loader=load_bike_profile,
            )
        return self.resolved_bike_profile_path

    def _ensure_runtime_config_loaded(self) -> None:
        if self.preprocess_config is None:
            preprocess_profile_path = self._resolve_preprocess_profile_path()
            bike_profile_path = self._resolve_bike_profile_path()
            self.preprocess_profile_sha256 = _sha256_file(preprocess_profile_path)
            self.bike_profile_sha256 = _sha256_file(bike_profile_path)
            normalized_preprocess_config = load_preprocess_config(preprocess_profile_path)
            self.effective_preprocess_config_sha256 = _sha256_jsonable(normalized_preprocess_config)
            self.preprocess_config = resolve_preprocess_config_paths(
                normalized_preprocess_config,
                base_dir=preprocess_profile_path.parent,
            )

    def validate(self) -> tuple[list[str], list[str]]:
        errors: list[str] = []
        warnings: list[str] = []

        try:
            self.resolved_preprocess_profile_path = _resolve_single_valid_json_file(
                self.source.preprocess_profile_path,
                label="Preprocess profile",
                loader=load_preprocess_config,
            )
        except Exception as exc:
            errors.append(str(exc))

        try:
            self.resolved_bike_profile_path = _resolve_single_valid_json_file(
                self.source.bike_profile_path,
                label="Bike profile",
                loader=load_bike_profile,
            )
        except Exception as exc:
            errors.append(str(exc))

        if self.source.session_note.attach_on_import:
            template_store = SessionNoteTemplateStore(self.source.session_note.template_path)
            try:
                _resolve_single_valid_json_file(
                    self.source.session_note.template_path,
                    label="Session note template",
                    loader=template_store.load_template_file,
                )
            except Exception as exc:
                errors.append(str(exc))
            try:
                _resolve_single_valid_json_file(
                    self.source.session_note.setup_preset_path,
                    label="Bike setup preset",
                    loader=load_bike_setup_preset,
                )
            except Exception as exc:
                errors.append(str(exc))

        for path in (
            self.source.inbox_dir,
            self.source.done_dir,
            self.source.failed_dir,
            self.source.staging_dir,
            self.source.fit_dir,
        ):
            if not path.exists():
                warnings.append(f"Directory will be created when needed: {path}")

        if self.source.source_type == SOURCE_TYPE_LOGGER_WIFI:
            if self.source.logger_wifi is not None and self.source.logger_wifi.base_url is None:
                warnings.append(
                    "Wi-Fi logger source has no remembered base_url; mDNS discovery will be used before acquisition."
                )

        return errors, warnings

    def ensure_runtime_dirs(self) -> None:
        for path in (
            self.source.inbox_dir,
            self.source.done_dir,
            self.source.failed_dir,
            self.source.staging_dir,
            self.source.fit_dir,
        ):
            _ensure_dir(path)

    def _import_agent_fit_import_config(self) -> Optional[Dict[str, Any]]:
        if not isinstance(self.preprocess_config, Mapping):
            return None
        raw = self.preprocess_config.get("fit_import")
        if not isinstance(raw, Mapping):
            return None
        if not bool(raw.get("enabled", False)):
            return dict(raw)

        cfg = dict(raw)
        cfg["fit_dir"] = str(self.source.fit_dir)
        cfg["ambiguity_policy"] = "largest_overlap"
        cfg["failure_policy"] = "warn"
        return cfg

    def _prepare_fit_batch(self, batch: ImportRunBatch) -> None:
        fit_import = self._import_agent_fit_import_config()
        if not isinstance(fit_import, Mapping) or not bool(fit_import.get("enabled")):
            return

        try:
            index_result = refresh_fit_inspection_index(self.source.fit_dir)
        except Exception:
            # Indexing is an optimization. Preserve the direct inspection path
            # if the cache cannot be read or refreshed.
            logger.warning(
                "FIT inspection index refresh failed for source %s",
                self.source.source_id,
                exc_info=True,
            )
            return

        candidates = index_result.get("candidates")
        if isinstance(candidates, list):
            batch.fit_candidates = [
                dict(candidate)
                for candidate in candidates
                if isinstance(candidate, Mapping)
            ]
        stats = index_result.get("stats")
        if isinstance(stats, Mapping):
            batch.fit_index_stats = dict(stats)

    def _write_data_syn_bike_outputs_if_enabled(
        self,
        *,
        session: Mapping[str, Any],
        run_id: str,
        session_id: str,
        bike_profile_path: Path,
    ) -> Optional[Dict[str, Any]]:
        library_export_config = _library_data_syn_bike_export_config(self.store.root)
        if library_export_config is None:
            return None

        record: Dict[str, Any] = {
            "format": "data_syn_bike",
            "status": "not_started",
            "run_id": run_id,
            "session_id": session_id,
            "updated_at": _utcnow_iso(),
        }
        try:
            bike_profile = load_bike_profile(bike_profile_path)
            raw_full_scale_by_end = _bike_profile_syn_raw_full_scale_by_end(bike_profile)
            export_config = dict(library_export_config)
            if raw_full_scale_by_end:
                existing = export_config.get("raw_full_scale_by_end")
                merged_full_scales = dict(existing) if isinstance(existing, Mapping) else {}
                merged_full_scales.update(raw_full_scale_by_end)
                export_config["raw_full_scale_by_end"] = merged_full_scales

            session_for_export = dict(session)
            session_for_export["run_id"] = run_id
            session_for_export["session_id"] = session_id
            export_config = default_data_syn_bike_export_config(**export_config)
            export_result = export_data_syn_bike_resolved(session_for_export, export_config=export_config)

            output_dir = self.store.root / "syn"
            write_result = write_data_syn_bike_exports(export_result, output_dir)
            settings = data_syn_bike_manual_settings(
                bike_profile=bike_profile,
                export_config=export_config,
                session=session_for_export,
            )
            settings_name = _render_data_syn_bike_settings_filename(run_id, session_id)
            settings_path = output_dir / settings_name
            _ensure_dir(settings_path.parent)
            settings_path.write_text(
                render_data_syn_bike_manual_settings_text(settings, export_result=export_result),
                encoding="utf-8",
            )

            record.update(
                {
                    "status": "succeeded",
                    "output_dir": str(output_dir),
                    "n_files": int(write_result.get("n_files", 0)),
                    "files": [
                        {
                            "path": str(item.get("path")),
                            "export_id": item.get("export_id"),
                            "rows": item.get("rows"),
                        }
                        for item in write_result.get("written", [])
                        if isinstance(item, Mapping)
                    ],
                    "settings_path": str(settings_path),
                    "settings": settings,
                    "summary": export_result.get("summary", {}),
                }
            )
        except Exception as exc:
            record.update(
                {
                    "status": "failed",
                    "error": f"{type(exc).__name__}: {exc}",
                }
            )
            logger.exception("data.syn.bike export failed for run=%s session=%s", run_id, session_id)

        self._upsert_data_syn_bike_manifest(record)
        return record

    def _upsert_data_syn_bike_manifest(self, record: Mapping[str, Any]) -> None:
        syn_dir = self.store.root / "syn"
        manifest_path = syn_dir / DATA_SYN_BIKE_LIBRARY_MANIFEST_FILENAME
        manifest = _read_json(
            manifest_path,
            {
                "schema": "bodaqs.data_syn_bike_export_manifest",
                "version": 1,
                "records": {},
            },
        )
        if not isinstance(manifest, dict):
            manifest = {"schema": "bodaqs.data_syn_bike_export_manifest", "version": 1, "records": {}}
        records = manifest.setdefault("records", {})
        if not isinstance(records, dict):
            records = {}
            manifest["records"] = records
        key = f"{record.get('run_id')}/{record.get('session_id')}"
        records[key] = dict(record)
        manifest["updated_at"] = _utcnow_iso()
        _write_json_atomic(manifest_path, manifest)

    def _resolve_session_note_template_path(self) -> Path:
        if not self.source.session_note.attach_on_import:
            raise ValueError("Session-note auto-attach is not enabled for this source")
        if self.source.session_note.template_path is None:
            raise ValueError("Session-note template path is not configured")
        return _resolve_single_valid_json_file(
            self.source.session_note.template_path,
            label="Session note template",
            loader=SessionNoteTemplateStore().load_template_file,
        )

    def _resolve_bike_setup_preset_path(self) -> Path:
        if not self.source.session_note.attach_on_import:
            raise ValueError("Session-note auto-attach is not enabled for this source")
        if self.source.session_note.setup_preset_path is None:
            raise ValueError("Bike setup preset path is not configured")
        return _resolve_single_valid_json_file(
            self.source.session_note.setup_preset_path,
            label="Bike setup preset",
            loader=load_bike_setup_preset,
        )

    def _copy_template_to_library(self, template: SessionNoteTemplate, template_path: Path) -> Path:
        target = library_session_note_template_root(self.store.root) / template.template_id / f"{template.template_version}.json"
        _ensure_dir(target.parent)
        source_sha256 = _sha256_file(template_path)
        if target.exists():
            target_sha256 = _sha256_file(target)
            if target_sha256 != source_sha256:
                raise ValueError(
                    "Library already contains a different session note template for "
                    f"{template.template_id}@{template.template_version}: {target}"
                )
            return target
        shutil.copy2(template_path, target)
        return target

    def _write_draft_session_note_if_enabled(
        self,
        *,
        run_id: str,
        session_id: str,
        bike_profile_path: Path,
    ) -> Optional[Dict[str, Any]]:
        if not self.source.session_note.attach_on_import:
            return None

        template_path = self._resolve_session_note_template_path()
        preset_path = self._resolve_bike_setup_preset_path()
        source_template_store = SessionNoteTemplateStore(template_path.parent)
        template = source_template_store.load_template_file(template_path)
        preset: BikeSetupPreset = load_bike_setup_preset(preset_path)
        if preset.template_id != template.template_id:
            raise ValueError(
                f"Bike setup preset template_id {preset.template_id!r} does not match "
                f"session note template {template.template_id!r}"
            )
        if preset.template_version is not None and preset.template_version != template.template_version:
            raise ValueError(
                f"Bike setup preset template_version {preset.template_version!r} does not match "
                f"session note template {template.template_version!r}"
            )

        library_template_path = self._copy_template_to_library(template, template_path)
        bike_profile = load_bike_profile(bike_profile_path)
        bike_profile_id = _optional_text(bike_profile.get("bike_profile_id"))
        source_context: Dict[str, Any] = {
            "origin": "import_agent",
            "import_source_id": self.source.source_id,
            "import_source_type": self.source.source_type,
            "import_source_config_path": str(self.source.config_path),
            "bike_profile_id": bike_profile_id,
            "bike_profile_path": str(bike_profile_path),
            "bike_profile_sha256": _sha256_file(bike_profile_path),
            "setup_preset_id": preset.preset_id,
            "setup_preset_path": str(preset_path),
            "setup_preset_sha256": _sha256_file(preset_path),
            "template_id": template.template_id,
            "template_version": template.template_version,
            "template_path": str(template_path),
            "template_sha256": _sha256_file(template_path),
            "library_template_path": str(library_template_path),
        }
        if preset.bike_profile_id is not None:
            source_context["preset_bike_profile_id"] = preset.bike_profile_id
            source_context["preset_bike_profile_id_matches"] = preset.bike_profile_id == bike_profile_id

        note_store = SessionNoteStore(
            store=self.store,
            template_store=SessionNoteTemplateStore(library_session_note_template_root(self.store.root)),
        )
        note = note_store.create_note_from_template(
            run_id=run_id,
            session_id=session_id,
            template_id=template.template_id,
            template_version=template.template_version,
            title=preset.title,
            draft=True,
            source_context=source_context,
        )
        note = note_store.update_note(
            note,
            values=preset.values,
            custom_values=preset.custom_values,
            free_text_notes=preset.free_text_notes,
        )
        saved = note_store.save_note(note)
        return {
            "status": "succeeded",
            "path": str(note_store.note_path(run_id=run_id, session_id=session_id)),
            "draft": bool(saved.draft),
            "template_id": saved.template_id,
            "template_version": saved.template_version,
            "setup_preset_id": preset.preset_id,
            "setup_preset_path": str(preset_path),
            "template_path": str(template_path),
            "library_template_path": str(library_template_path),
        }

    def _logger_wifi_remote_state_key(self, remote_session_id: str) -> str:
        if self.source.logger_wifi is None:
            raise ValueError("Cannot build Wi-Fi remote state key without logger_wifi config")
        return "logger_wifi:" + _sha256_jsonable(
            {
                "source_id": self.source.source_id,
                "logger_id": self.source.logger_wifi.logger_id,
                "remote_session_id": remote_session_id,
            }
        )

    def _logger_wifi_archive_filename(self, session: Mapping[str, Any]) -> str:
        remote_session_id = _optional_text(session.get("session_id"))
        if remote_session_id is None:
            raise ValueError("Wi-Fi logger session entry is missing session_id")

        data_format = self._logger_wifi_data_format(session)
        suffix = ".bdq" if data_format == "bdq" else ".zip"
        name_hint = _optional_text(session.get("session_stem")) or remote_session_id
        if data_format == "bdq":
            data_path = _optional_text(session.get("data_path"))
            if data_path is not None:
                data_stem = Path(data_path.replace("\\", "/")).stem
                if data_stem:
                    name_hint = data_stem
        safe_hint = re.sub(r"[^A-Za-z0-9._-]+", "_", name_hint).strip("._-")
        if not safe_hint:
            safe_hint = "logger_session"
        digest = hashlib.sha256(remote_session_id.encode("utf-8")).hexdigest()[:12]
        return f"{safe_hint[:80]}_{digest}{suffix}"

    def _logger_wifi_data_format(self, session: Mapping[str, Any]) -> str:
        data_format = str(session.get("data_format") or "").strip().lower()
        if data_format in {"bdq", "csv_zip"}:
            return data_format
        return "csv_zip"

    def _logger_wifi_data_ready(self, session: Mapping[str, Any], *, data_format: str) -> bool:
        if data_format == "bdq":
            return bool(session.get("data_ready", False))
        return session.get("archive_ready") is not False

    def _logger_wifi_client(self) -> Optional[LoggerWifiApiClient]:
        config = self.source.logger_wifi
        if self.source.source_type != SOURCE_TYPE_LOGGER_WIFI or config is None:
            return None
        if config.base_url is None:
            return None
        return self._logger_wifi_client_for_base_url(config.base_url)

    def _logger_wifi_client_for_base_url(self, base_url: str) -> LoggerWifiApiClient:
        config = self.source.logger_wifi
        if config is None:
            raise ValueError("Cannot build Wi-Fi logger client without logger_wifi config")
        return LoggerWifiApiClient(
            base_url,
            request_timeout_s=config.request_timeout_s,
            download_timeout_s=config.download_timeout_s,
        )

    def _discover_logger_wifi_client(self, remote_summary: Dict[str, Any]) -> Optional[LoggerWifiApiClient]:
        config = self.source.logger_wifi
        if self.source.source_type != SOURCE_TYPE_LOGGER_WIFI or config is None:
            return None

        timeout_s = max(1.0, min(float(config.request_timeout_s), 5.0))
        try:
            result = discover_single_logger_wifi_source(
                logger_id=config.logger_id,
                timeout_s=timeout_s,
                include_default_ap=True,
                default_ap_timeout_s=1.0,
            )
        except LoggerWifiDiscoveryUnavailable as exc:
            remote_summary["discovery"] = {
                "state": "unavailable",
                "message": str(exc),
            }
            return None
        except LoggerWifiDiscoveryError as exc:
            remote_summary["discovery"] = {
                "state": "error",
                "error": str(exc),
            }
            return None
        except Exception as exc:
            remote_summary["discovery"] = {
                "state": "error",
                "error": f"{type(exc).__name__}: {exc}",
            }
            return None

        if result is None:
            remote_summary["discovery"] = {
                "state": "not_found",
                "logger_id": config.logger_id,
            }
            return None

        remote_summary["discovery"] = {
            "state": "found",
            "logger_id": result.logger_id,
            "base_url": result.base_url,
            "hostname": result.hostname,
            "upload_mode": result.upload_mode,
            "api_version": result.api_version,
            "addresses": list(result.addresses),
            "method": "default_ap" if result.service_name == "default-ap" else "mdns",
        }
        return self._logger_wifi_client_for_base_url(result.base_url)

    def _logger_wifi_client_from_acquisition(
        self,
        acquisition: LoggerWifiArchiveAcquisition,
    ) -> Optional[LoggerWifiApiClient]:
        base_url = _optional_text(acquisition.base_url)
        if base_url is not None:
            return self._logger_wifi_client_for_base_url(base_url)
        return self._logger_wifi_client()

    def _pending_logger_wifi_acquisitions_from_state(self) -> dict[str, LoggerWifiArchiveAcquisition]:
        if self.source.source_type != SOURCE_TYPE_LOGGER_WIFI or self.source.logger_wifi is None:
            return {}

        out: dict[str, LoggerWifiArchiveAcquisition] = {}
        for state_key, record in self.state.records().items():
            if not state_key.startswith("logger_wifi:"):
                continue
            if str(record.get("source_id") or "") != self.source.source_id:
                continue
            if str(record.get("status") or "") != "downloaded":
                continue
            remote_session_id = _optional_text(record.get("remote_session_id"))
            local_archive_path_raw = _optional_text(record.get("local_archive_path"))
            if remote_session_id is None or local_archive_path_raw is None:
                continue
            local_archive_path = Path(local_archive_path_raw)
            if not local_archive_path.exists():
                continue
            acquisition = LoggerWifiArchiveAcquisition(
                remote_state_key=state_key,
                remote_session_id=remote_session_id,
                logger_id=_optional_text(record.get("logger_id")) or self.source.logger_wifi.logger_id,
                base_url=_optional_text(record.get("base_url")) or self.source.logger_wifi.base_url or "",
                local_archive_path=local_archive_path.resolve(),
                data_format=_optional_text(record.get("data_format")) or "csv_zip",
                remote_already_acknowledged=bool(
                    record.get("remote_already_acknowledged", record.get("acknowledged", False))
                ),
            )
            out[_path_key(local_archive_path)] = acquisition
        return out

    def _record_logger_wifi_downloaded(
        self,
        *,
        acquisition: LoggerWifiArchiveAcquisition,
        archive_sha256: str,
    ) -> None:
        self.state.upsert(
            acquisition.remote_state_key,
            {
                "status": "downloaded",
                "source_id": self.source.source_id,
                "source_type": SOURCE_TYPE_LOGGER_WIFI,
                "remote_session_id": acquisition.remote_session_id,
                "logger_id": acquisition.logger_id,
                "base_url": acquisition.base_url,
                "local_archive_path": str(acquisition.local_archive_path),
                "archive_sha256": archive_sha256,
                "data_format": acquisition.data_format,
                "remote_already_acknowledged": acquisition.remote_already_acknowledged,
                "updated_at": _utcnow_iso(),
            },
        )

    def _record_logger_wifi_failure(
        self,
        *,
        acquisition: LoggerWifiArchiveAcquisition,
        error: str,
        processing_key: Optional[str] = None,
        archive_sha256: Optional[str] = None,
    ) -> None:
        record: dict[str, Any] = {
            "status": "failed",
            "source_id": self.source.source_id,
            "source_type": SOURCE_TYPE_LOGGER_WIFI,
            "remote_session_id": acquisition.remote_session_id,
            "logger_id": acquisition.logger_id,
            "base_url": acquisition.base_url,
            "local_archive_path": str(acquisition.local_archive_path),
            "data_format": acquisition.data_format,
            "updated_at": _utcnow_iso(),
            "error": error,
        }
        if processing_key is not None:
            record["processing_key"] = processing_key
        if archive_sha256 is not None:
            record["archive_sha256"] = archive_sha256
        self.state.upsert(acquisition.remote_state_key, record)

    def _acquire_logger_wifi_archives(
        self,
        summary: Dict[str, Any],
        *,
        progress_callback: Optional[ImportProgressCallback] = None,
        archive_ready_callback: Optional[
            Callable[[LoggerWifiArchiveAcquisition, Mapping[str, Any]], None]
        ] = None,
    ) -> dict[str, LoggerWifiArchiveAcquisition]:
        if self.source.source_type != SOURCE_TYPE_LOGGER_WIFI or self.source.logger_wifi is None:
            return {}

        config = self.source.logger_wifi
        remote_summary: Dict[str, Any] = {
            "logger_id": config.logger_id,
            "base_url": config.base_url,
            "status": None,
            "sessions_seen": 0,
            "downloaded": [],
            "skipped": [],
            "failed": [],
        }
        summary["remote"] = remote_summary
        self._emit_progress(
            progress_callback,
            "remote_acquisition_started",
            logger_id=config.logger_id,
            base_url=config.base_url,
        )

        acquisitions = self._pending_logger_wifi_acquisitions_from_state()
        client = self._logger_wifi_client()
        configured_error: Optional[Exception] = None
        device: Optional[dict[str, Any]] = None

        if client is not None:
            try:
                device = client.get_device()
                device_logger_id = _optional_text(device.get("logger_id"))
                if device_logger_id != config.logger_id:
                    raise ValueError(
                        f"Logger identity mismatch: expected {config.logger_id!r}, got {device_logger_id!r}"
                    )
            except Exception as exc:
                configured_error = exc
                remote_summary["configured_address_error"] = f"{type(exc).__name__}: {exc}"
                device = None

        if device is None:
            discovered_client = self._discover_logger_wifi_client(remote_summary)
            if discovered_client is not None:
                client = discovered_client

        try:
            if client is None:
                discovery_state = (
                    remote_summary.get("discovery", {})
                    if isinstance(remote_summary.get("discovery"), Mapping)
                    else {}
                )
                remote_summary["status"] = {
                    "state": str(discovery_state.get("state") or "not_found"),
                    "message": "Wi-Fi logger was not reachable by remembered address or mDNS discovery.",
                }
                self._emit_progress(
                    progress_callback,
                    "remote_status",
                    logger_id=config.logger_id,
                    remote_state=remote_summary["status"]["state"],
                    message=remote_summary["status"]["message"],
                )
                return acquisitions

            if device is None:
                device = client.get_device()

            device_logger_id = _optional_text(device.get("logger_id"))
            if device_logger_id != config.logger_id:
                raise ValueError(
                    f"Logger identity mismatch: expected {config.logger_id!r}, got {device_logger_id!r}"
                )

            status = client.get_status()
            status_logger_id = _optional_text(status.get("logger_id"))
            if status_logger_id is not None and status_logger_id != config.logger_id:
                raise ValueError(
                    f"Logger status identity mismatch: expected {config.logger_id!r}, got {status_logger_id!r}"
                )

            upload_mode = bool(status.get("upload_mode", False))
            if not upload_mode:
                remote_summary["status"] = {
                    "state": "waiting_upload_mode",
                    "upload_mode": False,
                    "message": "Logger is reachable but not in upload mode.",
                }
                self._emit_progress(
                    progress_callback,
                    "remote_status",
                    logger_id=config.logger_id,
                    remote_state="waiting_upload_mode",
                    upload_mode=False,
                    message=remote_summary["status"]["message"],
                )
                logger.info(
                    "Wi-Fi logger source waiting for upload mode: source=%s logger_id=%s",
                    self.source.source_id,
                    config.logger_id,
                )
                return acquisitions

            sessions = client.list_sessions()
            remote_summary["sessions_seen"] = len(sessions)
            remote_summary["status"] = {
                "state": "ready",
                "upload_mode": upload_mode,
                "importable_session_count": len(sessions),
            }
            self._emit_progress(
                progress_callback,
                "remote_sessions_detected",
                logger_id=config.logger_id,
                base_url=client.base_url,
                session_count=len(sessions),
                upload_mode=upload_mode,
            )

            for session_index, session in enumerate(sessions, start=1):
                remote_session_id = _optional_text(session.get("session_id"))
                if remote_session_id is None:
                    continue
                data_format = self._logger_wifi_data_format(session)
                remote_progress = {
                    "logger_id": config.logger_id,
                    "remote_session_id": remote_session_id,
                    "remote_session_index": session_index,
                    "remote_session_count": len(sessions),
                    "data_format": data_format,
                }
                remote_state_key = self._logger_wifi_remote_state_key(remote_session_id)
                existing = self.state.get(remote_state_key)
                if (
                    existing is not None
                    and str(existing.get("status") or "") == "succeeded"
                    and not self.source.force_reprocess
                ):
                    remote_summary["skipped"].append(
                        {
                            "session_id": remote_session_id,
                            "reason": "already_imported",
                            "run_id": existing.get("run_id"),
                            "session": existing.get("session_id"),
                        }
                    )
                    self._emit_progress(
                        progress_callback,
                        "remote_session_skipped",
                        reason="already_imported",
                        run_id=existing.get("run_id"),
                        session_id=existing.get("session_id"),
                        **remote_progress,
                    )
                    continue
                if not self._logger_wifi_data_ready(session, data_format=data_format):
                    remote_summary["skipped"].append(
                        {
                            "session_id": remote_session_id,
                            "reason": "data_not_ready" if data_format == "bdq" else "archive_not_ready",
                            "data_format": data_format,
                        }
                    )
                    self._emit_progress(
                        progress_callback,
                        "remote_session_skipped",
                        reason="data_not_ready" if data_format == "bdq" else "archive_not_ready",
                        **remote_progress,
                    )
                    continue

                target_path = (self.source.inbox_dir / self._logger_wifi_archive_filename(session)).resolve()
                acquisition = LoggerWifiArchiveAcquisition(
                    remote_state_key=remote_state_key,
                    remote_session_id=remote_session_id,
                    logger_id=config.logger_id,
                    base_url=client.base_url,
                    local_archive_path=target_path,
                    data_format=data_format,
                    remote_already_acknowledged=bool(session.get("acknowledged", False)),
                )

                if target_path.exists():
                    acquisitions[_path_key(target_path)] = acquisition
                    remote_summary["skipped"].append(
                        {
                            "session_id": remote_session_id,
                            "reason": "already_local_pending",
                            "data_format": data_format,
                            "archive_path": str(target_path),
                        }
                    )
                    self._emit_progress(
                        progress_callback,
                        "remote_session_skipped",
                        reason="already_local_pending",
                        archive_path=str(target_path),
                        **remote_progress,
                    )
                    if archive_ready_callback is not None:
                        archive_ready_callback(acquisition, remote_progress)
                    continue

                self._emit_progress(
                    progress_callback,
                    "remote_session_download_started",
                    archive_path=str(target_path),
                    **remote_progress,
                )
                if data_format == "bdq":
                    downloaded_path = client.download_bdq_to_part(remote_session_id, target_path)
                else:
                    downloaded_path = client.download_archive_to_part(remote_session_id, target_path)
                try:
                    if data_format == "bdq":
                        self._validate_bdq_input(downloaded_path)
                    else:
                        self._archive_contract(downloaded_path)
                except Exception as exc:
                    failed_path = _move_to_dir_unique(downloaded_path, self.source.failed_dir, touch_mtime=True)
                    error = f"{type(exc).__name__}: {exc}"
                    self._record_logger_wifi_failure(acquisition=acquisition, error=error)
                    remote_summary["failed"].append(
                        {
                            "session_id": remote_session_id,
                            "data_format": data_format,
                            "failed_archive_path": str(failed_path),
                            "error": error,
                        }
                    )
                    self._emit_progress(
                        progress_callback,
                        "remote_session_failed",
                        reason="download_validation_failed",
                        failed_archive_path=str(failed_path),
                        error=error,
                        **remote_progress,
                    )
                    continue

                acquisition = LoggerWifiArchiveAcquisition(
                    remote_state_key=remote_state_key,
                    remote_session_id=remote_session_id,
                    logger_id=config.logger_id,
                    base_url=client.base_url,
                    local_archive_path=downloaded_path.resolve(),
                    data_format=data_format,
                    remote_already_acknowledged=bool(session.get("acknowledged", False)),
                )
                archive_sha256 = _sha256_file(downloaded_path)
                self._record_logger_wifi_downloaded(
                    acquisition=acquisition,
                    archive_sha256=archive_sha256,
                )
                acquisitions[_path_key(downloaded_path)] = acquisition
                remote_summary["downloaded"].append(
                    {
                        "session_id": remote_session_id,
                        "data_format": data_format,
                        "archive_path": str(downloaded_path),
                        "archive_sha256": archive_sha256,
                    }
                )
                self._emit_progress(
                    progress_callback,
                    "remote_session_downloaded",
                    archive_path=str(downloaded_path),
                    archive_sha256=archive_sha256,
                    **remote_progress,
                )
                if archive_ready_callback is not None:
                    archive_ready_callback(acquisition, remote_progress)
        except Exception as exc:
            error = f"{type(exc).__name__}: {exc}"
            remote_summary["status"] = {
                "state": "error",
                "error": error,
            }
            remote_summary["failed"].append({"error": error})
            self._emit_progress(
                progress_callback,
                "remote_status",
                logger_id=config.logger_id,
                remote_state="error",
                error=error,
            )
            if configured_error is not None:
                remote_summary["configured_address_error"] = f"{type(configured_error).__name__}: {configured_error}"
            logger.warning(
                "Wi-Fi logger acquisition failed for source=%s logger_id=%s: %s",
                self.source.source_id,
                config.logger_id,
                error,
            )

        return acquisitions

    def _postprocess_logger_wifi_import(
        self,
        *,
        acquisition: Optional[LoggerWifiArchiveAcquisition],
        record: Mapping[str, Any],
        candidate: ImportArchiveCandidate,
        summary: Dict[str, Any],
    ) -> None:
        if acquisition is None:
            return
        if self.source.logger_wifi is None:
            return

        config = self.source.logger_wifi
        acknowledged = False
        cleanup_done = False
        ack_response: Optional[dict[str, Any]] = None
        cleanup_response: Optional[dict[str, Any]] = None
        post_error: Optional[str] = None

        client = self._logger_wifi_client_from_acquisition(acquisition)
        if acquisition.remote_already_acknowledged:
            acknowledged = True
        elif client is None:
            post_error = "Wi-Fi logger source has no base_url configured; cannot acknowledge remote session."
        else:
            try:
                ack_response = client.ack_session(
                    session_id=acquisition.remote_session_id,
                    library_id=self.source.library_id,
                    run_id=_optional_text(record.get("run_id")),
                    imported_at=_optional_text(record.get("updated_at")),
                )
                acknowledged = True
            except Exception as exc:
                post_error = f"ack failed: {type(exc).__name__}: {exc}"
                logger.warning(
                    "Wi-Fi logger acknowledgement failed for source=%s session=%s: %s",
                    self.source.source_id,
                    acquisition.remote_session_id,
                    post_error,
                )

        if acknowledged and config.cleanup_mode != LOGGER_WIFI_CLEANUP_NONE:
            if client is None:
                post_error = "Wi-Fi logger source has no base_url configured; cannot clean up remote session."
            else:
                try:
                    cleanup_response = client.cleanup_session(
                        session_id=acquisition.remote_session_id,
                        mode=config.cleanup_mode,
                    )
                    cleanup_done = True
                except Exception as exc:
                    post_error = f"cleanup failed: {type(exc).__name__}: {exc}"
                    logger.warning(
                        "Wi-Fi logger cleanup failed for source=%s session=%s: %s",
                        self.source.source_id,
                        acquisition.remote_session_id,
                        post_error,
                    )

        updated_record = dict(record)
        updated_record.update(
            {
                "remote_source": SOURCE_TYPE_LOGGER_WIFI,
                "remote_session_id": acquisition.remote_session_id,
                "remote_logger_id": acquisition.logger_id,
                "remote_base_url": acquisition.base_url,
                "remote_data_format": acquisition.data_format,
                "remote_acknowledged": acknowledged,
                "remote_already_acknowledged": acquisition.remote_already_acknowledged,
                "remote_cleanup_mode": config.cleanup_mode,
                "remote_cleanup_done": cleanup_done,
            }
        )
        if post_error is not None:
            updated_record["remote_postprocess_error"] = post_error
        self.state.upsert(candidate.processing_key, updated_record)

        remote_record: dict[str, Any] = {
            "status": "succeeded",
            "source_id": self.source.source_id,
            "source_type": SOURCE_TYPE_LOGGER_WIFI,
            "remote_session_id": acquisition.remote_session_id,
            "logger_id": acquisition.logger_id,
            "base_url": acquisition.base_url,
            "local_archive_path": str(acquisition.local_archive_path),
            "archive_sha256": candidate.archive_sha256,
            "data_format": acquisition.data_format,
            "processing_key": candidate.processing_key,
            "raw_session_identity": candidate.raw_session_identity,
            "run_id": record.get("run_id"),
            "session_id": record.get("session_id"),
            "acknowledged": acknowledged,
            "remote_already_acknowledged": acquisition.remote_already_acknowledged,
            "cleanup_mode": config.cleanup_mode,
            "cleanup_done": cleanup_done,
            "updated_at": _utcnow_iso(),
        }
        if ack_response is not None:
            remote_record["ack_response"] = ack_response
        if cleanup_response is not None:
            remote_record["cleanup_response"] = cleanup_response
        if post_error is not None:
            remote_record["postprocess_error"] = post_error
        self.state.upsert(acquisition.remote_state_key, remote_record)

        if post_error is not None:
            summary.setdefault("remote", {}).setdefault("failed", []).append(
                {
                    "session_id": acquisition.remote_session_id,
                    "stage": "postprocess",
                    "error": post_error,
                }
            )

    def _discover_archives(self) -> list[Path]:
        self.ensure_runtime_dirs()
        out: list[Path] = []
        seen: set[str] = set()
        for pattern in self.source.archive_patterns:
            for path in sorted(self.source.inbox_dir.glob(pattern)):
                if not path.is_file():
                    continue
                key = _path_key(path)
                if key in seen:
                    continue
                seen.add(key)
                out.append(path.resolve())
        out.sort(key=lambda p: (p.stat().st_mtime_ns if p.exists() else 0, str(p)))
        if self.source.max_archives_per_scan is not None:
            return out[: int(self.source.max_archives_per_scan)]
        return out

    def _is_settled(self, path: Path, *, now_s: float) -> bool:
        if self.source.source_type == SOURCE_TYPE_LOGGER_WIFI:
            return True
        age_s = now_s - (path.stat().st_mtime_ns / 1_000_000_000.0)
        return age_s >= float(self.source.settle_time_s)

    def _archive_contract(self, archive_path: Path) -> SessionArchiveContract:
        return read_session_archive_contract(archive_path)

    def _validate_bdq_input(self, bdq_path: Path) -> None:
        info = read_bdq(bdq_path)
        validate_bdq_importable(info)

    def _build_candidate(
        self,
        *,
        inbox_archive_path: Path,
        claimed_archive_path: Path,
    ) -> ImportArchiveCandidate:
        self._ensure_runtime_config_loaded()
        stat = claimed_archive_path.stat()
        archive_sha256 = _sha256_file(claimed_archive_path)
        input_kind = "bdq" if is_bdq_path(claimed_archive_path) else "archive"
        source_identity_kind = "raw_session_identity"
        contract: Optional[SessionArchiveContract] = None
        if input_kind == "bdq":
            self._validate_bdq_input(claimed_archive_path)
            raw_session_identity = make_bdq_session_identity(bdq_sha256=archive_sha256)
            source_identity_kind = "bdq_session_identity"
        else:
            contract = self._archive_contract(claimed_archive_path)
            raw_session_identity = make_raw_session_identity(
                csv_sha256=contract.csv_sha256,
                log_metadata_sha256=contract.log_metadata_sha256,
            )
        processing_key = _sha256_jsonable(
            {
                "input_kind": input_kind,
                "raw_session_identity": raw_session_identity,
                "preprocess_profile_sha256": self.preprocess_profile_sha256,
                "effective_preprocess_config_sha256": self.effective_preprocess_config_sha256,
                "raw_signal_dropout_behavior": RAW_SIGNAL_DROPOUT_BEHAVIOR_VERSION,
                "bike_profile_sha256": self.bike_profile_sha256,
                "include_events": self.source.include_events,
                "include_metrics": self.source.include_metrics,
                "logger_timezone": self.source.logger_timezone,
            }
        )
        return ImportArchiveCandidate(
            source=self.source,
            inbox_archive_path=inbox_archive_path,
            claimed_archive_path=claimed_archive_path,
            archive_name=claimed_archive_path.name,
            archive_sha256=archive_sha256,
            archive_size_bytes=int(stat.st_size),
            archive_mtime_ns=int(stat.st_mtime_ns),
            contract=contract,
            input_kind=input_kind,
            source_identity_kind=source_identity_kind,
            raw_session_identity=raw_session_identity,
            processing_key=processing_key,
        )

    def _extract_candidate(self, candidate: ImportArchiveCandidate, target_dir: Path) -> tuple[Path, Optional[Path]]:
        if candidate.input_kind == "bdq":
            return candidate.claimed_archive_path, None
        if candidate.contract is None:
            raise ValueError(f"Session archive contract missing for {candidate.archive_name}")
        extracted = extract_session_archive(
            candidate.claimed_archive_path,
            target_dir,
            contract=candidate.contract,
        )
        if extracted.log_metadata_path is None:
            raise ValueError(f"Session archive did not yield log metadata: {candidate.archive_name}")
        return extracted.csv_path, extracted.log_metadata_path

    def _emit_progress(
        self,
        progress_callback: Optional[ImportProgressCallback],
        event: str,
        **payload: Any,
    ) -> None:
        _emit_import_progress(
            progress_callback,
            event,
            source_id=self.source.source_id,
            source_type=self.source.source_type,
            **payload,
        )

    def _ensure_import_batch_run(self, batch: ImportRunBatch) -> str:
        if batch.run_id is None:
            batch.run_id = self._make_unique_run_id()
        if not batch.session_ids:
            ensure_run_is_new(self.store, run_id=batch.run_id, force=False)
        return batch.run_id

    def _archive_import_config(
        self,
        *,
        candidate: ImportArchiveCandidate,
        preprocess_profile_path: Path,
        bike_profile_path: Path,
        data_syn_bike_export_record: Optional[Mapping[str, Any]],
        session_note_record: Optional[Mapping[str, Any]],
    ) -> Dict[str, Any]:
        archive_import_config = {
            "schema": IMPORT_SOURCE_SCHEMA,
            "version": IMPORT_SOURCE_VERSION,
            "input_kind": candidate.input_kind,
            "archive_sha256": candidate.archive_sha256,
            "raw_session_identity": candidate.raw_session_identity,
            "source_identity_kind": candidate.source_identity_kind,
            "processing_key": candidate.processing_key,
            "preprocess_profile_path": str(preprocess_profile_path),
            "preprocess_profile_selection_path": str(self.source.preprocess_profile_path),
            "preprocess_profile_sha256": self.preprocess_profile_sha256,
            "effective_preprocess_config_sha256": self.effective_preprocess_config_sha256,
            "raw_signal_dropout_behavior": RAW_SIGNAL_DROPOUT_BEHAVIOR_VERSION,
            "bike_profile_path": str(bike_profile_path),
            "bike_profile_selection_path": str(self.source.bike_profile_path),
            "bike_profile_sha256": self.bike_profile_sha256,
        }
        if candidate.input_kind == "bdq":
            archive_import_config["bdq_sha256"] = candidate.archive_sha256
        if data_syn_bike_export_record is not None:
            archive_import_config["data_syn_bike_export"] = dict(data_syn_bike_export_record)
        if session_note_record is not None:
            archive_import_config["session_note"] = dict(session_note_record)
        return archive_import_config

    def _archive_import_run_config(self, batch: ImportRunBatch) -> Dict[str, Any]:
        sessions = {
            session_id: dict(batch.archive_import_by_session[session_id])
            for session_id in batch.session_ids
            if session_id in batch.archive_import_by_session
        }
        if len(sessions) == 1:
            config = dict(next(iter(sessions.values())))
            config["sessions"] = sessions
            return config
        return {
            "schema": IMPORT_SOURCE_SCHEMA,
            "version": IMPORT_SOURCE_VERSION,
            "mode": "source_scan_batch_v1",
            "session_count": len(sessions),
            "sessions": sessions,
        }

    def _write_import_run_manifest(self, batch: ImportRunBatch) -> None:
        if batch.run_id is None or not batch.session_ids:
            return
        description = batch.run_description_override
        if description is None:
            description = self.source.description
        write_run_manifest(
            self.store,
            run_id=batch.run_id,
            session_ids=list(batch.session_ids),
            timezone_label=self.source.run_tz_label,
            description=description,
            pipeline_config={
                "import_source": {
                    "source_id": self.source.source_id,
                    "source_type": self.source.source_type,
                    "config_path": str(self.source.config_path),
                },
                "archive_import": self._archive_import_run_config(batch),
            },
        )

    def _session_description_for_batch(self, batch: ImportRunBatch) -> Optional[str]:
        naming = self.source.naming.session_description
        if not naming.enabled or naming.mode != SESSION_NAMING_MODE_BASE_INDEX:
            return None
        base = _optional_text(naming.base)
        if base is None:
            return None
        index = int(naming.index_start) + len(batch.session_ids)
        if int(naming.index_padding) > 0:
            suffix = f"{index:0{int(naming.index_padding)}d}"
        else:
            suffix = str(index)
        return f"{base} {suffix}"

    def _process_inbox_archive(
        self,
        inbox_path: Path,
        *,
        archive_index: int,
        archive_count: int,
        now_s: float,
        remote_acquisition: Optional[LoggerWifiArchiveAcquisition],
        batch: ImportRunBatch,
        summary: Dict[str, Any],
        progress_callback: Optional[ImportProgressCallback],
        deferred_remote_postprocess: Optional[
            list[
                tuple[
                    LoggerWifiArchiveAcquisition,
                    Dict[str, Any],
                    ImportArchiveCandidate,
                    Optional[Dict[str, Any]],
                ]
            ]
        ] = None,
    ) -> None:
        summary["seen"] += 1
        archive_progress = {
            "archive_name": inbox_path.name,
            "archive_path": str(inbox_path),
            "archive_index": archive_index,
            "archive_count": archive_count,
        }
        if not self._is_settled(inbox_path, now_s=now_s):
            summary["deferred_unsettled"].append(str(inbox_path))
            self._emit_progress(
                progress_callback,
                "archive_deferred",
                reason="unsettled",
                **archive_progress,
            )
            return

        try:
            claimed_path = _move_to_dir_unique(inbox_path, self.source.staging_dir)
        except FileNotFoundError:
            logger.warning("Archive disappeared before it could be claimed: %s", inbox_path)
            self._emit_progress(
                progress_callback,
                "archive_skipped",
                reason="disappeared_before_claim",
                **archive_progress,
            )
            return

        try:
            candidate = self._build_candidate(
                inbox_archive_path=inbox_path,
                claimed_archive_path=claimed_path,
            )
        except Exception as exc:
            failed_path = _move_to_dir_unique(claimed_path, self.source.failed_dir, touch_mtime=True)
            failure = {
                "status": "failed",
                "source_id": self.source.source_id,
                "archive_path": str(inbox_path),
                "failed_archive_path": str(failed_path),
                "updated_at": _utcnow_iso(),
                "error": f"{type(exc).__name__}: {exc}",
            }
            logger.exception("Archive validation failed for %s", inbox_path)
            if remote_acquisition is not None:
                self._record_logger_wifi_failure(
                    acquisition=remote_acquisition,
                    error=failure["error"],
                )
            summary["failed"].append(failure)
            self._emit_progress(
                progress_callback,
                "archive_failed",
                reason="validation_failed",
                error=failure["error"],
                failed_archive_path=str(failed_path),
                **archive_progress,
            )
            return

        existing = self.state.get(candidate.processing_key)
        if existing is not None and not self.source.force_reprocess:
            if str(existing.get("status") or "") == "succeeded":
                done_path = _move_to_dir_unique(claimed_path, self.source.done_dir, touch_mtime=True)
                summary["skipped_succeeded"].append(
                    {
                        "archive_path": str(inbox_path),
                        "done_archive_path": str(done_path),
                        "run_id": existing.get("run_id"),
                        "session_id": existing.get("session_id"),
                        "processing_key": candidate.processing_key,
                    }
                )
                if remote_acquisition is not None and deferred_remote_postprocess is not None:
                    deferred_remote_postprocess.append(
                        (remote_acquisition, existing, candidate, None)
                    )
                else:
                    self._postprocess_logger_wifi_import(
                        acquisition=remote_acquisition,
                        record=existing,
                        candidate=candidate,
                        summary=summary,
                    )
                self._emit_progress(
                    progress_callback,
                    "archive_skipped",
                    reason="already_imported",
                    done_archive_path=str(done_path),
                    run_id=existing.get("run_id"),
                    session_id=existing.get("session_id"),
                    **archive_progress,
                )
                return
            if str(existing.get("status") or "") == "failed":
                failed_path = _move_to_dir_unique(claimed_path, self.source.failed_dir, touch_mtime=True)
                summary["skipped_failed"].append(
                    {
                        "archive_path": str(inbox_path),
                        "failed_archive_path": str(failed_path),
                        "processing_key": candidate.processing_key,
                        "error": existing.get("error"),
                    }
                )
                self._emit_progress(
                    progress_callback,
                    "archive_skipped",
                    reason="previous_import_failed",
                    failed_archive_path=str(failed_path),
                    error=existing.get("error"),
                    **archive_progress,
                )
                return

        try:
            run_id = self._ensure_import_batch_run(batch)
            self._emit_progress(
                progress_callback,
                "archive_processing_started",
                run_id=run_id,
                input_kind=candidate.input_kind,
                archive_sha256=candidate.archive_sha256,
                processing_key=candidate.processing_key,
                **archive_progress,
            )
            record = self.import_candidate(candidate, batch=batch)
            if remote_acquisition is not None and deferred_remote_postprocess is not None:
                summary_record = record
                deferred_remote_postprocess.append(
                    (remote_acquisition, record, candidate, summary_record)
                )
            else:
                self._postprocess_logger_wifi_import(
                    acquisition=remote_acquisition,
                    record=record,
                    candidate=candidate,
                    summary=summary,
                )
                record = self.state.get(candidate.processing_key) or record
                summary_record = record
            summary["imported"].append(summary_record)
            self._emit_progress(
                progress_callback,
                "archive_imported",
                run_id=record.get("run_id"),
                session_id=record.get("session_id"),
                session_key=record.get("session_key"),
                timings=record.get("timings"),
                imported_count=len(summary["imported"]),
                **archive_progress,
            )
        except Exception as exc:
            failed_path = _move_to_dir_unique(candidate.claimed_archive_path, self.source.failed_dir, touch_mtime=True)
            error_record = {
                "status": "failed",
                "source_id": self.source.source_id,
                "archive_path": str(candidate.inbox_archive_path),
                "archive_sha256": candidate.archive_sha256,
                "failed_archive_path": str(failed_path),
                "raw_session_identity": candidate.raw_session_identity,
                "processing_key": candidate.processing_key,
                "updated_at": _utcnow_iso(),
                "error": f"{type(exc).__name__}: {exc}",
            }
            self.state.upsert(candidate.processing_key, error_record)
            if remote_acquisition is not None:
                self._record_logger_wifi_failure(
                    acquisition=remote_acquisition,
                    error=error_record["error"],
                    processing_key=candidate.processing_key,
                    archive_sha256=candidate.archive_sha256,
                )
            logger.exception("Import failed for %s", candidate.inbox_archive_path)
            summary["failed"].append(error_record)
            self._emit_progress(
                progress_callback,
                "archive_failed",
                reason="import_failed",
                error=error_record["error"],
                failed_archive_path=str(failed_path),
                failed_count=len(summary["failed"]),
                **archive_progress,
            )

    def _finish_deferred_logger_wifi_postprocess(
        self,
        deferred: Sequence[
            tuple[
                LoggerWifiArchiveAcquisition,
                Dict[str, Any],
                ImportArchiveCandidate,
                Optional[Dict[str, Any]],
            ]
        ],
        *,
        summary: Dict[str, Any],
    ) -> None:
        for acquisition, record, candidate, summary_record in deferred:
            self._postprocess_logger_wifi_import(
                acquisition=acquisition,
                record=record,
                candidate=candidate,
                summary=summary,
            )
            if summary_record is not None:
                updated = self.state.get(candidate.processing_key)
                if updated is not None:
                    summary_record.clear()
                    summary_record.update(updated)

    def _scan_logger_wifi_pipeline(
        self,
        *,
        summary: Dict[str, Any],
        batch: ImportRunBatch,
        now_s: float,
        progress_callback: Optional[ImportProgressCallback],
        prepare_fit_batch: Callable[[], None],
    ) -> None:
        ready_queue: Queue[
            tuple[LoggerWifiArchiveAcquisition, Dict[str, Any]]
        ] = Queue(maxsize=1)
        progress_queue: Queue[Dict[str, Any]] = Queue()
        producer_errors: list[BaseException] = []
        deferred_remote_postprocess: list[
            tuple[
                LoggerWifiArchiveAcquisition,
                Dict[str, Any],
                ImportArchiveCandidate,
                Optional[Dict[str, Any]],
            ]
        ] = []
        pipeline_started = time.perf_counter()

        # A Wi-Fi source also has a normal local inbox.  Process that inbox
        # first so an enabled source can reprocess retained archives even when
        # the logger is unavailable (and before live downloads use the scan
        # limit).
        inbox_paths = self._discover_archives()
        processed_inbox = len(inbox_paths)
        if inbox_paths:
            prepare_fit_batch()
        self._emit_progress(
            progress_callback,
            "archives_detected",
            archive_count=processed_inbox,
            max_archives_per_scan=self.source.max_archives_per_scan,
        )
        for archive_index, inbox_path in enumerate(inbox_paths, start=1):
            self._process_inbox_archive(
                inbox_path,
                archive_index=archive_index,
                archive_count=processed_inbox,
                now_s=now_s,
                remote_acquisition=None,
                batch=batch,
                summary=summary,
                progress_callback=progress_callback,
            )

        def queue_progress(message: Mapping[str, Any]) -> None:
            progress_queue.put(dict(message))

        def queue_ready(
            acquisition: LoggerWifiArchiveAcquisition,
            remote_progress: Mapping[str, Any],
        ) -> None:
            ready_queue.put((acquisition, dict(remote_progress)))

        def produce() -> None:
            try:
                self._acquire_logger_wifi_archives(
                    summary,
                    progress_callback=queue_progress,
                    archive_ready_callback=queue_ready,
                )
            except BaseException as exc:
                producer_errors.append(exc)

        def drain_progress() -> None:
            while True:
                try:
                    message = progress_queue.get_nowait()
                except Empty:
                    return
                if progress_callback is not None:
                    try:
                        progress_callback(message)
                    except Exception:
                        logger.warning(
                            "Import progress callback failed for event %s",
                            message.get("event"),
                            exc_info=True,
                        )

        self._emit_progress(
            progress_callback,
            "remote_pipeline_started",
            mode="narrow_producer_consumer",
            queue_capacity=1,
        )
        producer = Thread(
            target=produce,
            name=f"bodaqs-download-{self.source.source_id}",
            daemon=True,
        )
        producer.start()

        processed_ready = processed_inbox
        processed_remote = 0
        archives_announced = processed_inbox > 0
        max_archives = self.source.max_archives_per_scan
        while producer.is_alive() or not ready_queue.empty():
            drain_progress()
            try:
                acquisition, remote_progress = ready_queue.get(timeout=0.05)
            except Empty:
                continue

            if max_archives is not None and processed_ready >= int(max_archives):
                ready_queue.task_done()
                continue

            processed_ready += 1
            processed_remote += 1
            remote_count = int(remote_progress.get("remote_session_count") or 0)
            archive_count = processed_inbox + remote_count
            if max_archives is not None:
                archive_count = min(archive_count, int(max_archives))
            if not archives_announced:
                self._emit_progress(
                    progress_callback,
                    "archives_detected",
                    archive_count=archive_count,
                    max_archives_per_scan=max_archives,
                )
                archives_announced = True
            prepare_fit_batch()
            self._process_inbox_archive(
                acquisition.local_archive_path,
                archive_index=processed_ready,
                archive_count=archive_count,
                now_s=now_s,
                remote_acquisition=acquisition,
                batch=batch,
                summary=summary,
                progress_callback=progress_callback,
                deferred_remote_postprocess=deferred_remote_postprocess,
            )
            ready_queue.task_done()

        producer.join()
        drain_progress()
        if producer_errors:
            raise producer_errors[0]

        self._finish_deferred_logger_wifi_postprocess(
            deferred_remote_postprocess,
            summary=summary,
        )

        pipeline_elapsed_s = time.perf_counter() - pipeline_started
        remote_summary = summary.get("remote")
        if isinstance(remote_summary, dict):
            remote_summary["pipeline"] = {
                "mode": "narrow_producer_consumer",
                "queue_capacity": 1,
                "streamed_archives": processed_remote,
                "elapsed_s": pipeline_elapsed_s,
            }
        self._emit_progress(
            progress_callback,
            "remote_pipeline_completed",
            mode="narrow_producer_consumer",
            streamed_archives=processed_remote,
            elapsed_s=pipeline_elapsed_s,
        )

    def _purge_expired_processed_archives(self, *, now_s: float) -> Dict[str, Any]:
        retention_days = self.source.processed_archive_retention_days
        result: Dict[str, Any] = {
            "retention_days": retention_days,
            "deleted": [],
            "errors": [],
        }
        if retention_days is None:
            result["state"] = "retain_forever"
            return result

        cutoff_s = now_s - (float(retention_days) * 24 * 60 * 60)
        result["state"] = "completed"
        result["cutoff_at"] = datetime.fromtimestamp(cutoff_s, tz=timezone.utc).isoformat()
        for directory, outcome in ((self.source.done_dir, "done"), (self.source.failed_dir, "failed")):
            try:
                if not directory.exists():
                    continue
                for path in directory.iterdir():
                    if not path.is_file() or not any(path.match(pattern) for pattern in self.source.archive_patterns):
                        continue
                    if path.stat().st_mtime > cutoff_s:
                        continue
                    path.unlink()
                    result["deleted"].append({"outcome": outcome, "path": str(path)})
            except OSError as exc:
                result["errors"].append({"outcome": outcome, "error": f"{type(exc).__name__}: {exc}"})
                logger.warning("Could not purge expired %s archives for source %s", outcome, self.source.source_id, exc_info=True)
        return result

    def scan_once(
        self,
        *,
        progress_callback: Optional[ImportProgressCallback] = None,
        run_description_override: Optional[str] = None,
    ) -> Dict[str, Any]:
        summary: Dict[str, Any] = {
            "source_id": self.source.source_id,
            "source_type": self.source.source_type,
            "artifacts_dir": str(self.source.artifacts_dir),
            "seen": 0,
            "deferred_unsettled": [],
            "skipped_succeeded": [],
            "skipped_failed": [],
            "imported": [],
            "failed": [],
            "processed_archive_cleanup": None,
        }
        now_s = time.time()
        self._emit_progress(
            progress_callback,
            "source_scan_started",
            artifacts_dir=str(self.source.artifacts_dir),
        )

        with self.lock:
            self._ensure_runtime_config_loaded()
            batch = ImportRunBatch(run_description_override=_optional_text(run_description_override))
            fit_batch_prepared = False

            def prepare_fit_batch() -> None:
                nonlocal fit_batch_prepared
                if fit_batch_prepared:
                    return
                self._prepare_fit_batch(batch)
                fit_batch_prepared = True
                if batch.fit_index_stats is not None:
                    self._emit_progress(
                        progress_callback,
                        "fit_index_refreshed",
                        fit_index_stats=batch.fit_index_stats,
                    )

            if self.source.source_type == SOURCE_TYPE_LOGGER_WIFI:
                self._scan_logger_wifi_pipeline(
                    summary=summary,
                    batch=batch,
                    now_s=now_s,
                    progress_callback=progress_callback,
                    prepare_fit_batch=prepare_fit_batch,
                )
            else:
                inbox_paths = self._discover_archives()
                if inbox_paths:
                    prepare_fit_batch()
                self._emit_progress(
                    progress_callback,
                    "archives_detected",
                    archive_count=len(inbox_paths),
                    max_archives_per_scan=self.source.max_archives_per_scan,
                )
                for archive_index, inbox_path in enumerate(inbox_paths, start=1):
                    self._process_inbox_archive(
                        inbox_path,
                        archive_index=archive_index,
                        archive_count=len(inbox_paths),
                        now_s=now_s,
                        remote_acquisition=None,
                        batch=batch,
                        summary=summary,
                        progress_callback=progress_callback,
                    )

            summary["processed_archive_cleanup"] = self._purge_expired_processed_archives(now_s=time.time())
            self._emit_progress(
                progress_callback,
                "processed_archive_cleanup_completed",
                processed_archive_cleanup=summary["processed_archive_cleanup"],
            )

        if summary["imported"]:
            changed_sessions = _imported_session_revision_records(self.source, summary["imported"])
            summary["library_catalog_revision"] = touch_catalog_revision(
                self.source.artifacts_dir,
                reason="import_agent_sessions_imported",
                actor="import_agent",
                changed_sessions=changed_sessions,
            )
            summary["library_api_notification"] = _notify_library_api_catalog_changed(
                self.source,
                changed_sessions=changed_sessions,
            )
        self._emit_progress(
            progress_callback,
            "source_scan_completed",
            totals=_aggregate_reports([summary]),
            library_catalog_revision=summary.get("library_catalog_revision"),
            library_api_notification=summary.get("library_api_notification"),
        )
        return summary

    def import_candidate(
        self,
        candidate: ImportArchiveCandidate,
        *,
        batch: Optional[ImportRunBatch] = None,
    ) -> Dict[str, Any]:
        self._ensure_runtime_config_loaded()
        if batch is None:
            batch = ImportRunBatch()
        run_id: Optional[str] = None
        session_id: Optional[str] = None
        session_artifacts_started = False
        added_to_batch = False
        preprocess_profile_path = self._resolve_preprocess_profile_path()
        bike_profile_path = self._resolve_bike_profile_path()
        import_started = time.perf_counter()
        stage_timings: Dict[str, float] = {}
        preprocess_timings: Optional[Mapping[str, Any]] = None

        try:
            run_id = self._ensure_import_batch_run(batch)
            with tempfile.TemporaryDirectory(
                prefix=f"{self.source.source_id}_",
                dir=str(self.source.staging_dir),
            ) as tmpdir:
                stage_started = time.perf_counter()
                input_path, log_metadata_path = self._extract_candidate(candidate, Path(tmpdir))
                stage_timings["input_preparation"] = time.perf_counter() - stage_started
                preprocess_kwargs: Dict[str, Any] = {}
                if log_metadata_path is not None:
                    preprocess_kwargs["log_metadata_path"] = str(log_metadata_path)

                stage_started = time.perf_counter()
                results = preprocess_session(
                    str(input_path),
                    preprocess_config=self.preprocess_config,
                    fit_import=self._import_agent_fit_import_config(),
                    fit_candidates=batch.fit_candidates,
                    fit_parsed_cache=batch.fit_parsed_cache,
                    bike_profile_path=str(bike_profile_path),
                    timezone=self.source.logger_timezone,
                    include_events=True,
                    include_metrics=True,
                    **preprocess_kwargs,
                )
                stage_timings["preprocessing"] = time.perf_counter() - stage_started
                raw_preprocess_timings = results.get("timings")
                if isinstance(raw_preprocess_timings, Mapping):
                    preprocess_timings = dict(raw_preprocess_timings)

                stage_started = time.perf_counter()
                session = results["session"]
                session_id = str(session["session_id"])
                ensure_session_is_new(self.store, run_id=run_id, session_id=session_id, force=False)

                source_input_name = "input.bdq" if candidate.input_kind == "bdq" else "input.csv"
                copied_input_sha256 = copy_raw_input_to_source(
                    store=self.store,
                    run_id=run_id,
                    session_id=session_id,
                    input_path=input_path,
                    dest_name=source_input_name,
                )
                session_artifacts_started = True

                save_session_artifacts(
                    self.store,
                    run_id=run_id,
                    session_id=session_id,
                    session_df=session["df"],
                    session_meta=session["meta"],
                    secondary_stream_dfs=session.get("stream_dfs"),
                    secondary_stream_meta=session.get("meta", {}).get("secondary_streams"),
                )

                events_df = results.get("events", pd.DataFrame())
                metrics_df = results.get("metrics", pd.DataFrame())

                source_manifest = {
                    "path": f"source/{source_input_name}",
                    "sha256": copied_input_sha256,
                    "import_mode": "import_agent_archive_v1",
                    "import_source_id": self.source.source_id,
                    "import_source_type": self.source.source_type,
                    "import_source_config_path": str(self.source.config_path),
                    "raw_session_identity": candidate.raw_session_identity,
                    "source_identity": candidate.raw_session_identity,
                    "source_identity_kind": candidate.source_identity_kind,
                    "input_kind": candidate.input_kind,
                    "processing_key": candidate.processing_key,
                }
                if candidate.input_kind == "bdq":
                    source_manifest.update(
                        {
                            "import_mode": "import_agent_" + session["meta"]["source_contract"]["name"].replace(".", "_"),
                            "original_bdq_filename": candidate.archive_name,
                            "original_bdq_sha256": candidate.archive_sha256,
                            "original_bdq_path": str(candidate.inbox_archive_path),
                            "bdq_sha256": candidate.archive_sha256,
                        }
                    )
                else:
                    if candidate.contract is None:
                        raise ValueError(f"Session archive contract missing for {candidate.archive_name}")
                    source_manifest.update(
                        {
                            "original_archive_filename": candidate.archive_name,
                            "original_archive_sha256": candidate.archive_sha256,
                            "original_archive_path": str(candidate.inbox_archive_path),
                            "archive_csv_member": candidate.contract.csv_member_name,
                            "archive_csv_sha256": candidate.contract.csv_sha256,
                            "archive_log_metadata_member": candidate.contract.log_metadata_member_name,
                            "archive_log_metadata_sha256": candidate.contract.log_metadata_sha256,
                        }
                    )
                if self.source.logger_timezone is not None:
                    source_manifest["logger_timezone_fallback"] = self.source.logger_timezone
                if self.source.source_type == SOURCE_TYPE_LOGGER_WIFI and self.source.logger_wifi is not None:
                    source_manifest["remote_source"] = {
                        "kind": SOURCE_TYPE_LOGGER_WIFI,
                        "logger_id": self.source.logger_wifi.logger_id,
                        "base_url": self.source.logger_wifi.base_url,
                    }

                session_source = session.get("source", {}) if isinstance(session.get("source"), Mapping) else {}
                aux_manifest: list[Dict[str, Any]] = []
                try:
                    aux_manifest = copy_session_aux_sources(
                        store=self.store,
                        run_id=run_id,
                        session_id=session_id,
                        aux_sources=session_source.get("aux_sources"),
                    )
                except Exception as exc:
                    logger.warning("Auxiliary source copy failed for %s: %s", session_id, exc)
                    source_manifest["aux_source_copy_error"] = f"{type(exc).__name__}: {exc}"
                if aux_manifest:
                    source_manifest["aux_sources"] = aux_manifest

                session_description = self._session_description_for_batch(batch)
                write_session_manifest(
                    self.store,
                    run_id=run_id,
                    session_id=session_id,
                    description=session_description,
                    contracts={"session": "v0.x", "events": "v0.x", "metrics": "v0.x"},
                    source=source_manifest,
                    summary=self._session_summary(session),
                )

                schema_path = _optional_text(self.preprocess_config.get("schema_path"))
                if schema_path and isinstance(events_df, pd.DataFrame) and not events_df.empty:
                    write_events_partitioned_by_schema_id(
                        store=self.store,
                        run_id=run_id,
                        session_id=session_id,
                        events_df=events_df,
                        schema_path=Path(schema_path),
                    )
                if isinstance(metrics_df, pd.DataFrame) and not metrics_df.empty:
                    write_metrics_partitioned_by_schema_id(
                        store=self.store,
                        run_id=run_id,
                        session_id=session_id,
                        metrics_df=metrics_df,
                    )

                data_syn_bike_export_record = self._write_data_syn_bike_outputs_if_enabled(
                    session=session,
                    run_id=run_id,
                    session_id=session_id,
                    bike_profile_path=bike_profile_path,
                )
                session_note_record = self._write_draft_session_note_if_enabled(
                    run_id=run_id,
                    session_id=session_id,
                    bike_profile_path=bike_profile_path,
                )

                archive_import_config = self._archive_import_config(
                    candidate=candidate,
                    preprocess_profile_path=preprocess_profile_path,
                    bike_profile_path=bike_profile_path,
                    data_syn_bike_export_record=data_syn_bike_export_record,
                    session_note_record=session_note_record,
                )
                batch.add_session(session_id, archive_import_config)
                added_to_batch = True
                self._write_import_run_manifest(batch)
                stage_timings["artifact_output"] = time.perf_counter() - stage_started

            stage_started = time.perf_counter()
            done_path = _move_to_dir_unique(candidate.claimed_archive_path, self.source.done_dir, touch_mtime=True)
            stage_timings["source_finalize"] = time.perf_counter() - stage_started
            import_timings: Dict[str, Any] = {
                "schema": "bodaqs.import_timing",
                "version": 1,
                "total_s": time.perf_counter() - import_started,
                "stages_s": stage_timings,
            }
            if preprocess_timings is not None:
                import_timings["preprocess"] = preprocess_timings
            record = {
                "status": "succeeded",
                "source_id": self.source.source_id,
                "archive_path": str(candidate.inbox_archive_path),
                "archive_sha256": candidate.archive_sha256,
                "done_archive_path": str(done_path),
                "input_kind": candidate.input_kind,
                "source_identity_kind": candidate.source_identity_kind,
                "raw_session_identity": candidate.raw_session_identity,
                "processing_key": candidate.processing_key,
                "run_id": run_id,
                "session_id": session_id,
                "session_key": f"{run_id}/{session_id}",
                "session_manifest_path": str(self.store.path_session_manifest(run_id, session_id)),
                "updated_at": _utcnow_iso(),
                "timings": import_timings,
            }
            if candidate.contract is not None:
                record["archive_csv_member"] = candidate.contract.csv_member_name
                record["archive_log_metadata_member"] = candidate.contract.log_metadata_member_name
            if candidate.input_kind == "bdq":
                record["bdq_sha256"] = candidate.archive_sha256
            if session_note_record is not None:
                record["session_note"] = session_note_record
            self.state.upsert(candidate.processing_key, record)
            logger.info(
                "Imported %s -> run=%s session=%s",
                candidate.inbox_archive_path,
                run_id,
                session_id,
            )
            return record

        except Exception:
            if added_to_batch and session_id is not None:
                batch.remove_session(session_id)
                if batch.session_ids:
                    try:
                        self._write_import_run_manifest(batch)
                    except Exception:
                        logger.warning(
                            "Failed to rewrite run manifest after removing failed session: run=%s session=%s",
                            run_id,
                            session_id,
                            exc_info=True,
                        )
            if session_artifacts_started and run_id is not None and session_id is not None:
                self._cleanup_failed_session(run_id, session_id)
            if session_artifacts_started and run_id is not None and not batch.session_ids:
                self._cleanup_failed_run(run_id)
            raise

    def _cleanup_failed_run(self, run_id: str) -> None:
        run_dir = self.store.run_dir(run_id)
        if not run_dir.exists():
            return
        try:
            shutil.rmtree(run_dir)
        except Exception:
            logger.warning("Failed to clean up partial run directory after import error: %s", run_dir)

    def _cleanup_failed_session(self, run_id: str, session_id: str) -> None:
        session_dir = self.store.session_dir(run_id, session_id)
        if not session_dir.exists():
            return
        try:
            shutil.rmtree(session_dir)
        except Exception:
            logger.warning(
                "Failed to clean up partial session directory after import error: run=%s session=%s",
                run_id,
                session_id,
            )
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
