benconnor1972/BODAQS/firmware/src/Routes_Config.cpp

#include "Routes_Config.h"
#include <Arduino.h>
#include <ArduinoJson.h>
#include <ctype.h>
#include <stdlib.h>
#include <string.h>

#include "HtmlUtil.h"
#include "ConfigManager.h"
#include "SensorManager.h"
#include "SensorRegistry.h"
#include "RTCManager.h"
#include "WiFiManager.h"
#include "PowerManager.h"
#include "Rates.h"
#include "WebServerManager.h"  // for canStart()
#include "UploadModeManager.h"
#include "StorageManager.h"
#include "ButtonManager.h"
#include "DisplayManager.h"
#include "BoardSelect.h" 
#include "HttpFileSender.h"
#include "DebugLog.h"

#define WEB_LOGW(...) LOGW_TAG("WEB", __VA_ARGS__)

// ---- Helpers (file scope) ----
static String fmtIPv4(const uint8_t a[4]) {
  char buf[16];
  snprintf(buf, sizeof(buf), "%u.%u.%u.%u",
           a[0], a[1], a[2], a[3]);
  return String(buf);
}

static String minutesStringFromMs_(uint32_t ms) {
  if (ms == 0) return String("0");
  String s((double)ms / 60000.0, 3);
  while (s.endsWith("0")) s.remove(s.length() - 1);
  if (s.endsWith(".")) s.remove(s.length() - 1);
  return s;
}

static bool parseMinutesToMs_(const String& text, uint32_t& out) {
  String s = text;
  s.trim();
  if (!s.length()) return false;
  char* end = nullptr;
  const double minutes = strtod(s.c_str(), &end);
  if (end == s.c_str()) return false;
  while (end && *end && isspace((unsigned char)*end)) ++end;
  if (end && *end) return false;
  if (minutes < 0.0) return false;
  double ms = minutes * 60000.0;
  if (ms > 4294967295.0) ms = 4294967295.0;
  out = (uint32_t)(ms + 0.5);
  return true;
}

static void noteHttpActivity_() {
  WiFiManager::noteUserActivity();
  PowerManager::noteActivity();
}

static bool configEditLocked_(String* reason = nullptr) {
  if (!WebServerManager::canStart()) {
    if (reason) *reason = F("logging is active");
    return true;
  }
  if (UploadModeManager::isActive()) {
    if (reason) *reason = F("upload mode is active");
    return true;
  }
  return false;
}

static bool rejectConfigEditLocked_(WebServer& srv) {
  String reason;
  if (!configEditLocked_(&reason)) {
    return false;
  }
  if (HtmlUtil::isHtmxRequest(srv)) {
    // Return 200 (not 423) because htmx v2.0 does not swap 4xx response bodies by default.
    // Returning 423 would cause htmx to fire htmx:responseError and discard the body,
    // leaving the target div empty with no lock feedback visible to the user.
    HttpFileSender::sendText(srv, 200, F("text/html"),
      String(F("<div class='alert-warn'>Configuration is locked while ")) + reason + F(".</div>"), F("no-store"));
    return true;
  }
  srv.send(423, F("text/plain"), String(F("Configuration is locked while ")) + reason + F("."));
  return true;
}

static void applyLogSettingsLive_(const LoggerConfig& cfg) {
  Log_setEnabled(true);
  Log_resetLevel();
  if (cfg.logLevelOverride <= LOG_TRACE) {
    Log_setLevel((LogLevel)cfg.logLevelOverride);
  }
}

static OutputMode loggerSupportedOutputMode_(long value) {
  return (value == (long)OutputMode::RAW) ? OutputMode::RAW : OutputMode::LINEAR;
}

static OutputMode parseLoggerOutputMode_(String text, OutputMode fallback = OutputMode::LINEAR) {
  text.trim();
  text.toUpperCase();
  if (text == "RAW" || text == "0") return OutputMode::RAW;
  if (text == "LINEAR" || text == "1") return OutputMode::LINEAR;
  return fallback;
}

static Sensor* findLiveSensorByName_(const char* name) {
  if (!name || !*name) return nullptr;

  for (uint8_t j = 0; j < SensorManager::count(); ++j) {
    Sensor* s = SensorManager::get(j);
    if (s && String(s->name()) == String(name)) return s;
  }
  return nullptr;
}

static bool parseSensorTypeKey_(String text, SensorType& out) {
  text.trim();
  if (text.equalsIgnoreCase("analog_pot") || text.equalsIgnoreCase("pot")) {
    out = SensorType::AnalogPot;
    return true;
  }
  if (text.equalsIgnoreCase("as5600_string_pot_analog") || text.equalsIgnoreCase("as5600_pot_analog")) {
    out = SensorType::AS5600StringPotAnalog;
    return true;
  }
  if (text.equalsIgnoreCase("as5600_string_pot_i2c") || text.equalsIgnoreCase("as5600_pot_i2c")) {
    out = SensorType::AS5600StringPotI2C;
    return true;
  }
  if (text.equalsIgnoreCase("as5600_angle_i2c") || text.equalsIgnoreCase("as5600_rotary_i2c") ||
      text.equalsIgnoreCase("as5600_rotary")) {
    out = SensorType::AS5600AngleI2C;
    return true;
  }
  if (text.equalsIgnoreCase("as5048b_angle_i2c") || text.equalsIgnoreCase("as5048b") ||
      text.equalsIgnoreCase("as5048_angle_i2c")) {
    out = SensorType::AS5048BAngleI2C;
    return true;
  }
  if (text.equalsIgnoreCase("dan_f10n_gps_uart") || text.equalsIgnoreCase("dan_f10n_gps") ||
      text.equalsIgnoreCase("gps_uart") || text.equalsIgnoreCase("gps")) {
    out = SensorType::DANF10NGps;
    return true;
  }
  if (text.equalsIgnoreCase("bmi270_imu_i2c")) {
    out = SensorType::BMI270ImuI2C;
    return true;
  }
  return false;
}

static const char* defaultNamePrefix_(SensorType type) {
  switch (type) {
    case SensorType::AnalogPot: return "analog";
    case SensorType::AS5600StringPotAnalog: return "as5600a";
    case SensorType::AS5600StringPotI2C: return "as5600i";
    case SensorType::AS5048BAngleI2C: return "as5048";
    case SensorType::AS5600AngleI2C: return "as5600r";
    case SensorType::DANF10NGps: return "gps";
    case SensorType::BMI270ImuI2C: return "imu";
    default: return "sensor";
  }
}

static String uniqueSensorName_(SensorType type, String proposed) {
  proposed.trim();
  if (proposed.length() > 15) proposed = proposed.substring(0, 15);
  if (proposed.length() && ConfigManager::findSensorByName(proposed.c_str()) < 0) return proposed;

  const String prefix = defaultNamePrefix_(type);
  for (uint8_t i = 0; i < MAX_SENSORS; ++i) {
    String candidate = prefix + String((int)i);
    if (candidate.length() > 15) candidate = candidate.substring(0, 15);
    if (ConfigManager::findSensorByName(candidate.c_str()) < 0) return candidate;
  }
  return String("sensor");
}

static bool applyLiveSensorSpec_(uint8_t idx, const char* lookupName, const SensorSpec& sp) {
  Sensor* live = findLiveSensorByName_(lookupName);
  if (!live && lookupName && strcmp(lookupName, sp.name) != 0) {
    live = findLiveSensorByName_(sp.name);
  }
  if (!live) return false;
  if (!live->reconfigureFromSpec(sp)) return false;

  live->setMuted(sp.mutedDefault);

  long om = 0;
  sp.params.getInt("output_mode", om);
  const OutputMode mode = loggerSupportedOutputMode_(om);
  live->setOutputMode(mode);

  bool inc = false;
  sp.params.getBool("include_raw", inc);
  live->setIncludeRaw(inc);

  live->setSelectedTransformId("identity");

  if (mode == OutputMode::RAW) {
    live->setOutputUnitsLabel("counts");
  }

  live->setAllowedCalMask(ConfigManager::calAllowedMaskByIndex(idx));
  return true;
}

class ChunkedHtmlResponse {
public:
  explicit ChunkedHtmlResponse(WebServer& srv) : srv_(srv) {
    buf_.reserve(kFlushThreshold);
  }

  void begin(const String& contentType, const String& cacheControl) {
    if (cacheControl.length()) {
      srv_.sendHeader(F("Cache-Control"), cacheControl);
    }
    srv_.setContentLength(CONTENT_LENGTH_UNKNOWN);
    srv_.send(200, contentType, "");
    begun_ = true;
  }

  void finish() {
    flush();
    if (begun_) {
      srv_.sendContent("");
      begun_ = false;
    }
  }

  void flushIfLarge() {
    if (buf_.length() >= kFlushThreshold) flush();
  }

  void flush() {
    if (!begun_ || !buf_.length()) return;
    srv_.sendContent(buf_);
    buf_.remove(0);
    delay(0);
  }

  ChunkedHtmlResponse& operator+=(const String& s) {
    buf_ += s;
    flushIfLarge();
    return *this;
  }

  ChunkedHtmlResponse& operator+=(const __FlashStringHelper* s) {
    buf_ += s;
    flushIfLarge();
    return *this;
  }

  ChunkedHtmlResponse& operator+=(const char* s) {
    buf_ += s;
    flushIfLarge();
    return *this;
  }

  ChunkedHtmlResponse& operator+=(char c) {
    buf_ += c;
    flushIfLarge();
    return *this;
  }

  operator String&() { return buf_; }

private:
  static constexpr size_t kFlushThreshold = 2048;
  WebServer& srv_;
  String buf_;
  bool begun_ = false;
};

using namespace HtmlUtil;

static const SensorType kEditableSensorTypes_[] = {
  SensorType::AnalogPot,
  SensorType::AS5600StringPotAnalog,
  SensorType::AS5600StringPotI2C,
  SensorType::AS5048BAngleI2C,
  SensorType::AS5600AngleI2C,
  SensorType::DANF10NGps,
  SensorType::BMI270ImuI2C,
};

static void emitSensorTypeOptions_(ChunkedHtmlResponse& html, SensorType selected) {
  for (const auto typeChoice : kEditableSensorTypes_) {
    const SensorTypeInfo* tiChoice = SensorRegistry::lookup(typeChoice);
    if (!tiChoice) continue;
    const char* key = SensorRegistry::typeKey(typeChoice);
    const char* label = SensorRegistry::typeLabel(typeChoice);
    html += F("<option value='");
    html += htmlEscape(String(key ? key : "unknown"));
    html += F("'");
    if (selected == typeChoice) html += F(" selected");
    html += F(">");
    html += htmlEscape(String(label ? label : "Unknown Sensor"));
    html += F("</option>");
  }
}

static const ParamDef* findParamDef_(const ParamDef* defs, size_t defCount, const char* key) {
  if (!defs || !key) return nullptr;
  for (size_t d = 0; d < defCount; ++d) {
    if (defs[d].key && strcasecmp(defs[d].key, key) == 0) return &defs[d];
  }
  return nullptr;
}

static String paramValueAsString_(const SensorSpec& sp, const ParamDef* pd) {
  String val;
  if (!pd) return val;
  if (pd->type == ParamType::Bool) {
    bool b = false;
    if (sp.params.getBool(pd->key, b)) val = b ? "true" : "false";
  } else if (pd->type == ParamType::Int) {
    long v = 0;
    if (sp.params.getInt(pd->key, v)) val = String(v);
    else if (strcasecmp(pd->key, "max_output_rate_hz") == 0 &&
             sp.params.getInt("output_rate_hz", v)) val = String(v);
  } else if (pd->type == ParamType::Float) {
    double f = 0.0;
    if (sp.params.getFloat(pd->key, f)) val = String(f, 6);
  } else {
    sp.params.get(pd->key, val);
  }
  if (!val.length() && pd->def) val = pd->def;
  return val;
}

static void emitParamRow_(ChunkedHtmlResponse& html,
                          uint8_t idx,
                          const SensorSpec& sp,
                          const ParamDef* defs,
                          size_t defCount,
                          const char* key,
                          const char* labelOverride,
                          bool locked) {
  const ParamDef* pd = findParamDef_(defs, defCount, key);
  if (!pd) return;

  String label = labelOverride ? String(labelOverride) : String(pd->key);
  String field = String("s") + idx + "." + key;

  html += F("<div class='row'><label>");
  html += htmlEscape(label);
  html += F("</label>");

  if (pd->type == ParamType::Bool) {
    String val = paramValueAsString_(sp, pd);
    html += F("<input type='hidden' name='");
    html += field;
    html += F("' value='false'><input type='checkbox' name='");
    html += field;
    html += F("' value='true'");
    if (val == "true") html += F(" checked");
    if (locked) html += F(" disabled");
    html += F(">");
  } else if (pd->type == ParamType::Enum && pd->choices) {
    String val = paramValueAsString_(sp, pd);
    html += F("<select name='");
    html += field;
    html += F("'");
    if (locked) html += F(" disabled");
    html += F(">");
    emitEnumOptions(html, pd->choices, val);
    html += F("</select>");
  } else {
    String val = paramValueAsString_(sp, pd);
    html += F("<input type='text' name='");
    html += field;
    html += F("' value='");
    html += htmlEscape(val);
    html += F("'");
    if (locked) html += F(" disabled");
    html += F(">");
  }

  if (pd->help) {
    html += F("<small>");
    html += pd->help;
    html += F("</small>");
  }
  html += F("</div>");
}

static bool analogInputConfigured_(const board::BoardProfile& bp, uint8_t ain) {
  if (ain >= bp.analog.count || ain >= board::BOARD_MAX_ANALOG_INPUTS) return false;

  const auto& input = bp.analog.inputs[ain];
  switch (input.source) {
    case board::AnalogSourceType::InternalGpio:
      return input.pin >= 0;
    case board::AnalogSourceType::ExternalAdc:
      return input.external_adc_index < bp.external_adc_count &&
             input.external_adc_index < board::BOARD_MAX_EXTERNAL_ADCS &&
             bp.external_adcs[input.external_adc_index].present &&
             input.external_channel < bp.external_adcs[input.external_adc_index].channel_count;
    case board::AnalogSourceType::None:
    default:
      return false;
  }
}

static String analogInputLabel_(const board::BoardProfile& bp, uint8_t ain) {
  String label = String(F("AIN")) + String((int)ain);
  if (ain >= bp.analog.count || ain >= board::BOARD_MAX_ANALOG_INPUTS) return label;

  const auto& input = bp.analog.inputs[ain];
  switch (input.source) {
    case board::AnalogSourceType::InternalGpio:
      label += F(" (GPIO");
      label += String((int)input.pin);
      label += F(")");
      break;
    case board::AnalogSourceType::ExternalAdc:
      label += F(" (ADS");
      label += String((int)input.external_adc_index);
      label += F(" CH");
      label += String((int)input.external_channel);
      if (input.differential && input.negative_channel >= 0) {
        label += F("-");
        label += String((int)input.negative_channel);
      }
      label += F(")");
      break;
    case board::AnalogSourceType::None:
    default:
      break;
  }
  return label;
}

static void emitAnalogInputRow_(ChunkedHtmlResponse& html,
                                uint8_t idx,
                                const SensorSpec& sp,
                                const ParamDef* defs,
                                size_t defCount,
                                bool locked) {
  const ParamDef* pd = findParamDef_(defs, defCount, "ain");
  if (!pd) return;

  String field = String("s") + idx + ".ain";
  long curAin = -1;
  sp.params.getInt("ain", curAin);

  html += F("<div class='row'><label>Analog input</label>");
  if (!board::gBoard) {
    html += F("<em>No active board profile</em>");
  } else {
    const auto& bp = *board::gBoard;
    if (bp.analog.count == 0) {
      html += F("<em>No analog inputs on this board</em>");
    } else {
      html += F("<select name='");
      html += field;
      html += F("'");
      if (locked) html += F(" disabled");
      html += F("><option value='-1'");
      if (curAin < 0) html += F(" selected");
      html += F(">-- select --</option>");
      for (uint8_t ai = 0; ai < bp.analog.count; ++ai) {
        if (!analogInputConfigured_(bp, ai)) continue;
        html += F("<option value='");
        html += String((int)ai);
        html += F("'");
        if ((long)ai == curAin) html += F(" selected");
        html += F(">");
        html += analogInputLabel_(bp, ai);
        html += F("</option>");
      }
      html += F("</select>");
    }
  }
  html += F("</div>");
}

static void emitOutputModeRow_(ChunkedHtmlResponse& html, uint8_t idx, const SensorSpec& sp, bool locked) {
  long stored = (long)OutputMode::RAW;
  sp.params.getInt("output_mode", stored);
  const OutputMode mode = loggerSupportedOutputMode_(stored);
  const String field = String("s") + idx + ".output_mode";

  html += F("<div class='row'><label>Output mode</label><select name='");
  html += field;
  html += F("'");
  if (locked) html += F(" disabled");
  html += F(">");
  html += F("<option value='0'");
  if (mode == OutputMode::RAW) html += F(" selected");
  html += F(">RAW</option><option value='1'");
  if (mode == OutputMode::LINEAR) html += F(" selected");
  html += F(">LINEAR</option></select>");
  html += F("<small>Complex transforms are applied downstream during import/analysis.");
  if (stored == (long)OutputMode::POLY || stored == (long)OutputMode::LUT) {
    html += F(" Legacy POLY/LUT config will be saved back as LINEAR.");
  }
  html += F("</small></div>");
}

static String calMaskText_(CalModeMask mask) {
  String out;
  if (mask & CAL_ZERO) {
    if (out.length()) out += ",";
    out += "ZERO";
  }
  if (mask & CAL_RANGE) {
    if (out.length()) out += ",";
    out += "RANGE";
  }
  if (!out.length()) out = "NONE";
  return out;
}

static void emitCalMethodsRow_(ChunkedHtmlResponse& html, uint8_t idx, SensorType type) {
  const CalModeMask supported = SensorRegistry::supportedCalMask(type);
  const CalModeMask allowed = ConfigManager::calAllowedMaskByIndex(idx);
  const CalModeMask effective = (allowed == 0xFF) ? supported : (supported & allowed);

  html += F("<div class='row'><label>Calibration methods</label><input type='text' value='");
  html += htmlEscape(calMaskText_(effective));
  html += F("' readonly>");
  html += F("<small>Read-only sensor capability. Calibration values below remain editable.</small></div>");
}

static bool keyInList_(const char* key, const char* const* list, size_t count) {
  if (!key) return false;
  for (size_t i = 0; i < count; ++i) {
    if (strcasecmp(list[i], key) == 0) return true;
  }
  return false;
}

static String orientationRejectionText_(uint16_t mask) {
  String message;
  const struct { uint16_t flag; const char* text; } reasons[] = {
      {ImuOrientationRejection::kInsufficientSamples, "not enough samples"},
      {ImuOrientationRejection::kQualityIncident, "sensor data gap or quality incident"},
      {ImuOrientationRejection::kAccelMeanOutsideGravityBand, "gravity magnitude outside range"},
      {ImuOrientationRejection::kAccelMagnitudeUnstable, "acceleration not steady"},
      {ImuOrientationRejection::kGyroUnstable, "rotation not steady"},
      {ImuOrientationRejection::kGyroMotionDetected, "rotation detected"},
      {ImuOrientationRejection::kRollOutsideLimit, "bike not level"},
      {ImuOrientationRejection::kInvalidGeometry, "invalid plane geometry"},
  };
  for (const auto& reason : reasons) {
    if (!(mask & reason.flag)) continue;
    if (message.length()) message += F(", ");
    message += reason.text;
  }
  return message.length() ? message : String(F("unknown quality check"));
}

static void sendOrientationFeedback_(WebServer& srv, const String& message, int sensorIndex) {
  if (HtmlUtil::isHtmxRequest(srv)) {
    HttpFileSender::sendText(srv, 200, F("text/html"), message, F("no-store"));
    return;
  }
  String page = htmlHeader(F("Set orientation"));
  page += message;
  page += F("<p><a href='/config/sensor?id=");
  page += String(sensorIndex);
  page += F("'>Back to sensor</a></p>");
  page += htmlFooter();
  HttpFileSender::sendText(srv, 200, F("text/html"), page, F("no-store"));
}

static void emitSensorEditor_(ChunkedHtmlResponse& html,
                              uint8_t idx,
                              const SensorSpec& sp,
                              bool locked,
                              const String& dis) {
  const SensorTypeInfo* ti = SensorRegistry::lookup(sp.type);
  size_t defCount = 0;
  const ParamDef* defs = ti ? ti->paramDefs(defCount) : nullptr;
  const char* typeLbl = SensorRegistry::typeLabel(sp.type);
  const char* dispName = (sp.name && sp.name[0]) ? sp.name : "sensor";

  html += F("<fieldset id='sensor-");
  html += String(idx);
  html += F("'><legend>");
  html += htmlEscape(String(dispName));
  html += F(" - ");
  html += htmlEscape(String(typeLbl ? typeLbl : "Unknown Sensor"));
  html += F("</legend>");

  html += F("<h4>Basic</h4>");
  html += F("<div class='row'><label>Name</label><input type='text' name='s");
  html += String(idx);
  html += F(".name' value='");
  html += htmlEscape(String(sp.name));
  html += F("'");
  html += dis;
  html += F("></div>");

  html += F("<div class='row'><label>Type</label><select name='s");
  html += String(idx);
  html += F(".type'");
  if (locked) html += F(" disabled");
  html += F(">");
  emitSensorTypeOptions_(html, sp.type);
  html += F("</select> <button type='submit' name='apply_type_idx' value='");
  html += String(idx);
  html += F("'");
  if (locked) html += F(" disabled");
  html += F(">Apply Type</button><small>Rebuilds fields for this sensor type; restart after add/delete/type changes.</small></div>");

  emitParamRow_(html, idx, sp, defs, defCount, "i2c_bus", "I2C bus", locked);
  emitParamRow_(html, idx, sp, defs, defCount, "i2c_addr", "I2C address", locked);
  emitAnalogInputRow_(html, idx, sp, defs, defCount, locked);

  String mutedField = String("s") + idx + ".muted";
  html += F("<div class='row'><label>Muted by default</label><input type='hidden' name='");
  html += mutedField;
  html += F("' value='false'><input type='checkbox' name='");
  html += mutedField;
  html += F("' value='true'");
  if (sp.mutedDefault) html += F(" checked");
  if (locked) html += F(" disabled");
  html += F("></div>");

  if (sp.type == SensorType::BMI270ImuI2C) {
    html += F("<h4>Acquisition</h4>");
    emitParamRow_(html, idx, sp, defs, defCount, "profile", "Native accel / gyro profile", locked);
    emitParamRow_(html, idx, sp, defs, defCount, "fifo_poll_rate_hz", "FIFO service rate (Hz)", locked);
    emitParamRow_(html, idx, sp, defs, defCount, "startup_bias_capture_s", "Startup observation (s)", locked);
    emitParamRow_(html, idx, sp, defs, defCount, "gyro_bias_mode", "Gyro bias mode", locked);
    html += F("<small>BDQv2 stores the profile's native streams. The legacy sparse-row output-rate setting is retained in saved configuration but is not used here.</small>");
    html += F("<h4>Installation</h4>");
    emitParamRow_(html, idx, sp, defs, defCount, "imu_id", "Physical IMU ID", locked);
    emitParamRow_(html, idx, sp, defs, defCount, "domain", "Mechanical domain", locked);
    emitParamRow_(html, idx, sp, defs, defCount, "end", "Bike end", locked);
    emitParamRow_(html, idx, sp, defs, defCount, "mount_point", "Mount point", locked);
    emitParamRow_(html, idx, sp, defs, defCount, "calibration_ref", "Host calibration reference", locked);
    String orientationPlane;
    sp.params.get("orient_plane", orientationPlane);
    if (orientationPlane != "xy" && orientationPlane != "yz" && orientationPlane != "xz") {
      orientationPlane = "xz";
    }
    long normalSign = 1;
    sp.params.getInt("orient_normal_sign", normalSign);
    html += F("<div class='row' style='display:flex;flex-wrap:wrap;align-items:center;gap:12px'>");
    html += F("<label>Installation orientation</label><span><select name='s");
    html += String(idx);
    html += F(".orient_plane'");
    if (locked) html += F(" disabled");
    html += F(" data-saved='");
    html += orientationPlane;
    html += F("'><option value='xy'");
    if (orientationPlane == "xy") html += F(" selected");
    html += F(">XY (normal Z)</option><option value='yz'");
    if (orientationPlane == "yz") html += F(" selected");
    html += F(">YZ (normal X)</option><option value='xz'");
    if (orientationPlane == "xz") html += F(" selected");
    html += F(">XZ (normal Y)</option></select> <select name='s");
    html += String(idx);
    html += F(".orient_normal_sign'");
    if (locked) html += F(" disabled");
    html += F(" data-saved='");
    html += String(normalSign == -1 ? -1 : 1);
    html += F("'><option value='1'");
    if (normalSign != -1) html += F(" selected");
    html += F(">Positive normal points left</option><option value='-1'");
    if (normalSign == -1) html += F(" selected");
    html += F(">Negative normal points left</option></select></span>");
    html += F("<button type='submit' form='orientation-capture-form' "
              "onclick=\"for(const s of this.parentElement.querySelectorAll('select'))"
              "{if(s.value!==s.dataset.saved){document.getElementById('orientation-result').textContent="
              "'Save Sensor before capturing orientation.';return false;}}\"");
    if (locked) html += F(" disabled");
    html += F(">Capture and save orientation <span class='htmx-indicator'>Capturing...</span></button></div>");
    bool orientationAccepted = false;
    sp.params.getBool("orient_valid", orientationAccepted);
    html += F("<div class='row'><label>Capture status</label><span>");
    html += orientationAccepted ? F("Accepted") : F("Not set");
    html += F("</span><small>Save Sensor stores the selections. Capture uses the saved settings after final mounting; raw IMU samples are never rotated in the logger.</small></div>");
    html += F("<div id='orientation-result'></div>");
  } else {
  if (findParamDef_(defs, defCount, "output_mode")) {
    html += F("<h4>Output</h4>");
    emitOutputModeRow_(html, idx, sp, locked);
    emitParamRow_(html, idx, sp, defs, defCount, "include_raw", "Include raw column", locked);
    emitParamRow_(html, idx, sp, defs, defCount, "sensor_full_travel_mm", "Sensor full travel (mm)", locked);
    emitParamRow_(html, idx, sp, defs, defCount, "installed_range", "Installed range", locked);
  }

  if (findParamDef_(defs, defCount, "end") ||
      findParamDef_(defs, defCount, "primary_domain") ||
      findParamDef_(defs, defCount, "primary_quantity")) {
    html += F("<h4>Usage</h4>");
    emitParamRow_(html, idx, sp, defs, defCount, "end", "End", locked);
    emitParamRow_(html, idx, sp, defs, defCount, "primary_domain", "Primary domain", locked);
    emitParamRow_(html, idx, sp, defs, defCount, "primary_quantity", "Primary quantity", locked);
  }

  html += F("<h4>Calibration</h4>");
  emitCalMethodsRow_(html, idx, sp.type);
  emitParamRow_(html, idx, sp, defs, defCount, "sensor_zero_count", "Sensor count at zero travel", locked);
  emitParamRow_(html, idx, sp, defs, defCount, "sensor_full_count", "Sensor count at full travel", locked);
  emitParamRow_(html, idx, sp, defs, defCount, "installed_zero_count", "Installed zero count", locked);
  emitParamRow_(html, idx, sp, defs, defCount, "zero_count", "Zero count", locked);

  if (findParamDef_(defs, defCount, "counts_per_turn") ||
      findParamDef_(defs, defCount, "wrap_threshold_counts") ||
      findParamDef_(defs, defCount, "assume_turn0_at_start")) {
    html += F("<h4>Wrapping</h4>");
    emitParamRow_(html, idx, sp, defs, defCount, "counts_per_turn", "Counts per turn", locked);
    emitParamRow_(html, idx, sp, defs, defCount, "wrap_threshold_counts", "Wrap threshold (counts)", locked);
    emitParamRow_(html, idx, sp, defs, defCount, "assume_turn0_at_start", "Assume turn 0 at log start", locked);
  }

  static const char* const shown[] = {
    "ain","muted","i2c_bus","i2c_addr",
    "output_mode","output_id","include_raw","sensor_full_travel_mm","installed_range",
    "end","primary_domain","primary_quantity","raw_domain",
    "cal_allowed","sensor_zero_count","sensor_full_count","installed_zero_count","zero_count",
    "counts_per_turn","wrap_threshold_counts","assume_turn0_at_start"
  };
  bool printedOther = false;
  for (size_t d = 0; d < defCount; ++d) {
    const ParamDef& pd = defs[d];
    if (!pd.key || pd.hidden || keyInList_(pd.key, shown, sizeof(shown) / sizeof(shown[0]))) continue;
    if (!printedOther) {
      html += F("<h4>Other</h4>");
      printedOther = true;
    }
    emitParamRow_(html, idx, sp, defs, defCount, pd.key, nullptr, locked);
  }
  }

  html += F("<div class='row'><label>Remove</label><button type='submit' name='delete_sensor_idx' value='");
  html += String(idx);
  html += F("'");
  if (locked) html += F(" disabled");
  html += F(">Delete this sensor</button><small>Removes the sensor from logger config only.</small></div>");
  html += F("</fieldset>");
}

void registerConfigRoutes(WebServer& srv) {
  WebServer* S = &srv;

  // -------------------- GET /config --------------------
  S->on("/config", HTTP_GET, [S](){
    auto& srv = *S;
    noteHttpActivity_();

    // Read the active config for display
    const LoggerConfig& cfg = ConfigManager::get();

    String lockedReason;
    const bool locked = configEditLocked_(&lockedReason);
    const String dis  = locked ? F(" disabled") : F("");

    String html = htmlHeader(F("Config"));

    if (srv.hasArg("ok")) {
      html += F("<p style='background:#e7ffe7;border:1px solid #8bc34a;padding:8px;border-radius:6px'>Saved.</p>");
    }
    if (locked) {
      html += F("<p style='background:#fff3cd;border:1px solid #ffe08a;padding:8px;border-radius:6px'>"
                "Editing is disabled while ");
      html += htmlEscape(lockedReason);
      html += F(". Exit upload mode or stop logging to make changes.</p>");
    }

    // Status banner
    if (srv.hasArg("ok")) {
      html += "<p class='ok'>Configuration saved</p>";
    }

    // ---- ERROR banner (board-aware validation) ----
    if (srv.hasArg("err")) {
      String err = srv.arg("err");
      String s   = srv.hasArg("sensor") ? srv.arg("sensor") : "";
      String ain = srv.hasArg("ain")    ? srv.arg("ain")    : "";

      html += "<p style='background:#ffe7e7;border:1px solid #e57373;";
      html += "padding:8px;border-radius:6px'>";
      html += "Error: " + htmlEscape(err);

      if (s.length()) {
        html += " (sensor ";
        html += htmlEscape(s);
        html += ")";
      }
      if (ain.length()) {
        html += ", ain=";
        html += htmlEscape(ain);
      }
      html += "</p>";
    }


    // ---------- GLOBALS ----------
    html += F("<div id='save-result'></div>");
    html += F("<h2>Configuration</h2>");
    html += F("<form method='POST' action='/config'");
    html += F(" hx-post='/config' hx-target='#save-result' hx-swap='innerHTML'");
    html += F(" hx-sync='this:replace'>");
    html += F("<input type='hidden' name='submit' value='globals'>"); //Hidden input

    html += F("<fieldset><legend>General</legend>");
    html += F("<label>Logger name: </label><input type='text' name='logger_name' maxlength='31' value='");
    html += htmlEscape(String(cfg.loggerName));
    html += F("'"); html += dis; html += F("><br>");

    html += F("<label>Sample rate (Hz): </label><select name='sample_rate_hz'"); html += dis; html += F(">");
    for (size_t rateIndex = 0; rateIndex < Rates::kCount; ++rateIndex) {
      const uint16_t rate = Rates::kList[rateIndex];
      html += F("<option value='"); html += String(rate); html += F("'");
      if (cfg.sampleRateHz == rate) html += F(" selected");
      html += F(">"); html += String(rate); html += F("</option>");
    }
    html += F("</select><br>");

    html += F("<label>Log format: </label>");
    html += F("<label><input type='radio' name='log_format' value='bodaqs_standard'");
    if (cfg.logFormat == LogFormat::BodaqsStandard) html += F(" checked");
    html += dis; html += F("> BODAQS CSV</label> ");
    html += F("<label><input type='radio' name='log_format' value='bodaqs_compact_binary'");
    if (cfg.logFormat == LogFormat::BodaqsCompactBinary) html += F(" checked");
    html += dis; html += F("> BODAQS compact binary</label> ");
    html += F("<label><input type='radio' name='log_format' value='bodaqs_multi_stream_binary'");
    if (cfg.logFormat == LogFormat::BodaqsMultiStreamBinary) html += F(" checked");
    html += dis; html += F("> BODAQS multi-stream binary (experimental)</label><br>");

    html += F("<label><input type='checkbox' name='omit_metadata' value='true'");
    if (cfg.omitMetadata) html += F(" checked");
    html += dis; html += F("> Omit log metadata JSON</label><br>");

    html += F("<label>Timestamp mode: </label><select name='timestamp_mode'");
    html += dis; html += F("><option value='human'");
    if (cfg.timestampHuman) html += F(" selected");
    html += F(">human</option><option value='fast'");
    if (!cfg.timestampHuman) html += F(" selected");
    html += F(">fast</option></select><br>");

    html += F("<label>Timezone (tz rule): </label><input type='text' name='tz' value='");
    html += htmlEscape(String(cfg.tz));
    html += F("'"); html += dis; html += F("><br>");

    html += F("<label>OLED while logging: </label><select name='oled_logging_policy'");
    html += dis; html += F("><option value='auto'");
    if (cfg.oledLoggingPolicy == OledLoggingPolicy::Auto) html += F(" selected");
    html += F(">Automatic</option><option value='freeze'");
    if (cfg.oledLoggingPolicy == OledLoggingPolicy::Freeze) html += F(" selected");
    html += F(">Freeze</option><option value='prefer_active'");
    if (cfg.oledLoggingPolicy == OledLoggingPolicy::PreferActive) html += F(" selected");
    html += F(">Prefer active</option></select><br>");
    
    html += F("<label>Auto-sleep idle (min): </label><input type='number' name='auto_sleep_idle_min' min='0' step='0.1' value='");
    html += minutesStringFromMs_(cfg.autoSleepIdleMs);
    html += F("'"); html += dis; html += F("><small>0 = disabled</small><br>");

    html += F("<label>Wi-Fi idle timeout (min): </label><input type='number' name='wifi_idle_timeout_min' min='0' step='0.1' value='");
    html += minutesStringFromMs_(cfg.wifiIdleTimeoutMs);
    html += F("'"); html += dis; html += F("><small>0 = disabled</small><br>");

    html += F("</fieldset>");

    // ---------- Wi-Fi (multi-network) ----------
    html += F("<fieldset><legend>Network & NTP</legend>");

    // toggles
    html += F("<div class='row'><label>Enable Wi-Fi by default</label>");
    html += F("<input type='hidden' name='wifi_enabled_default' value='false'>");
    html += F("<input type='checkbox' name='wifi_enabled_default' value='true'");
    if (cfg.wifiEnabledDefault) html += F(" checked");
    if (locked) html += F(" disabled");
    html += F("></div>");

    html += F("<div class='row'><label>Wi-Fi mode</label><select name='wifi_mode'");
    if (locked) html += F(" disabled");
    html += F("><option value='station'");
    if (cfg.wifiMode == WiFiMode::Station) html += F(" selected");
    html += F(">Station</option><option value='access_point'");
    if (cfg.wifiMode == WiFiMode::AccessPoint) html += F(" selected");
    html += F(">Access point</option></select></div>");

    html += F("<div class='row'><label>AP SSID</label><input type='text' name='wifi_ap_ssid' maxlength='31' value='");
    html += htmlEscape(String(cfg.wifiApSsid));
    html += F("'");
    if (locked) html += F(" disabled");
    html += F("></div>");

    html += F("<div class='row'><label>AP password</label><input type='password' name='wifi_ap_password' minlength='8' maxlength='63' value='");
    html += htmlEscape(String(cfg.wifiApPassword));
    html += F("'");
    if (locked) html += F(" disabled");
    html += F("><small>8-63 characters</small></div>");

    html += F("<div class='row'><label>Auto-enable for NTP if RTC invalid</label>");
    html += F("<input type='hidden' name='wifi_auto_time_on_rtc_invalid' value='false'>");
    html += F("<input type='checkbox' name='wifi_auto_time_on_rtc_invalid' value='true'");
    if (cfg.wifiAutoTimeOnRtcInvalid) html += F(" checked");
    if (locked) html += F(" disabled");
    html += F("></div>");

    html += F("<div class='row'><label>NTP servers (CSV)</label><input type='text' name='ntp_servers' value='");
    html += htmlEscape(String(cfg.ntpServers));
    html += F("'");
    if (locked) html += F(" disabled");
    html += F("></div>");

    html += F("<div class='row'><label>HTTP time check URL</label><input type='text' name='time_check_url' value='");
    html += htmlEscape(String(cfg.timeCheckUrl));
    html += F("'");
    if (locked) html += F(" disabled");
    html += F("></div>");

    html += F("<h4>Wi-Fi (multi-network)</h4>");

    // advisory count (display only)
    html += F("<div class='row'><label>Configured networks</label>");
    html += "<input type='text' value='"; html += String(cfg.wifiNetworkCount);
    html += F("' disabled></div>");

    // five editable slots; order = priority
    for (int i = 0; i < 5; ++i) {
      const auto& w = cfg.wifi[i];
      html += F("<fieldset><legend>Wi-Fi ");
      html += String(i);
      html += F(" (priority "); html += String(i+1); html += F(")</legend>");

      // SSID
      html += F("<div class='row'><label>SSID</label><input type='text' name='wifi");
      html += String(i);
      html += F(".ssid' value='");
      html += htmlEscape(String(w.ssid));
      html += F("'"); if (locked) html += F(" disabled"); html += F("></div>");

      // Password (write-only feel; still show current to match legacy)
      html += F("<div class='row'><label>Password</label><input type='password' name='wifi");
      html += String(i);
      html += F(".password' value='");
      html += htmlEscape(String(w.password));
      html += F("' placeholder='(unchanged)'");
      if (locked) html += F(" disabled");
      html += F("></div>");

      // min_rssi
      html += F("<div class='row'><label>Min RSSI (dBm)</label>"
                "<input type='number' step='1' min='-100' max='0' name='wifi");
      html += String(i);
      html += F(".min_rssi' value='");
      if (w.minRssi >= -100 && w.minRssi <= -10) html += String((int)w.minRssi);
      html += F("' oninput=\"this.setCustomValidity('');"
                "if(this.value!=='' && this.value!=='0' && Number(this.value)>-10)"
                " this.setCustomValidity('Value must be ≤ -10 (or 0/blank to ignore)');\"");
      if (locked) html += F(" disabled");
      html += F(" placeholder='0 or blank = ignore'>"
                "<small>≤ -10, or 0/blank to ignore</small></div>");

      // BSSID
      String bssidStr;
      if (w.bssidSet) {
        char buf[24];
        snprintf(buf, sizeof(buf), "%02X:%02X:%02X:%02X:%02X:%02X",
                 w.bssid[0],w.bssid[1],w.bssid[2],w.bssid[3],w.bssid[4],w.bssid[5]);
        bssidStr = buf;
      }
      html += F("<div class='row'><label>BSSID (optional)</label><input type='text' pattern='^[0-9A-Fa-f]{2}(:[0-9A-Fa-f]{2}){5}$' name='wifi");
      html += String(i);
      html += F(".bssid' value='");
      html += htmlEscape(bssidStr);
      html += F("'"); if (locked) html += F(" disabled"); html += F("><small>AA:BB:CC:DD:EE:FF</small></div>");

      // Hidden
      html += F("<div class='row'><label>Hidden SSID</label>"
                "<input type='hidden' name='wifi");
      html += String(i);
      html += F(".hidden' value='false'>"
                "<input type='checkbox' name='wifi");
      html += String(i);
      html += F(".hidden' value='true'");
      if (w.hidden) html += F(" checked");
      if (locked)   html += F(" disabled");
      html += F("></div>");

      // Static IP enable
      {
        String key = String("wifi")+i+".static_ip";
        html += "<div class='row'><label>Static IP</label>";
        html += "<input type='hidden' name='" + key + "' value='false'>";
        html += "<input type='checkbox' name='" + key + "' value='true' ";
        if (cfg.wifi[i].staticIp) html += "checked";
        if (locked) html += " disabled";
        html += "></div>";
      }

      // IP fields (always shown is simplest; later you can hide via JS)
      auto addIpField = [&](const char* suffix, const uint8_t ip[4], const char* label){
        String key = String("wifi")+i+"."+suffix;
        html += "<div class='row'><label>";
        html += label;
        html += "</label><input type='text' size='16' name='";
        html += key;
        html += "' value='";
        html += htmlEscape(fmtIPv4(ip));
        html += "'";
        if (locked) html += " disabled";
        html += "></div>";
      };

      addIpField("ip",      cfg.wifi[i].ip,      "Local IP");
      addIpField("gateway", cfg.wifi[i].gateway, "Gateway");
      addIpField("subnet",  cfg.wifi[i].subnet,  "Subnet");
      addIpField("dns1",    cfg.wifi[i].dns1,    "DNS 1");

      html += F("</fieldset>");
    }

    html += F("<p><button type='submit'"); html += dis; html += F(">Save <span class='htmx-indicator'>Saving...</span></button></p>");
    html += F("</form>");

    html += htmlFooter();
    HttpFileSender::sendText(srv, 200, F("text/html"), html, F("no-store"));
  });

  // -------------------- GET /config/sensors --------------------
  S->on("/config/sensors", HTTP_GET, [S](){
    auto& srv = *S;
    noteHttpActivity_();

    const LoggerConfig& cfg = ConfigManager::get();
    String lockedReason;
    const bool locked = configEditLocked_(&lockedReason);
    const String dis  = locked ? F(" disabled") : F("");

    ChunkedHtmlResponse html(srv);
    html.begin(F("text/html"), F("no-store"));
    html += htmlHeader(F("Sensors"));

    if (srv.hasArg("ok")) {
      html += F("<p style='background:#e7ffe7;border:1px solid #8bc34a;padding:8px;border-radius:6px'>Saved.</p>");
    }
    if (srv.hasArg("reboot")) {
      html += F("<p style='background:#fff3cd;border:1px solid #ffe08a;padding:8px;border-radius:6px'>"
                "Sensor add/delete changes are saved. Restart the logger to rebuild the live sensor set."
                "</p>");
    }
    if (locked) {
      html += F("<p style='background:#fff3cd;border:1px solid #ffe08a;padding:8px;border-radius:6px'>"
                "Editing is disabled while ");
      html += htmlEscape(lockedReason);
      html += F(". Exit upload mode or stop logging to make changes.</p>");
    }

    html += F("<h2>Sensors</h2>");
    const uint8_t listCount = cfg.sensorCount();
    if (listCount == 0) {
      html += F("<p><em>No sensors configured.</em></p>");
    } else {
      html += F("<table><thead><tr><th>#</th><th>Name</th><th>Type</th><th>State</th><th>Output</th><th></th></tr></thead><tbody>");
      for (uint8_t i = 0; i < listCount; ++i) {
        SensorSpec sp;
        if (!cfg.getSensorSpec(i, sp)) continue;
        long om = 0;
        sp.params.getInt("output_mode", om);
        const OutputMode mode = loggerSupportedOutputMode_(om);
        html += F("<tr><td>");
        html += String((int)i);
        html += F("</td><td>");
        html += htmlEscape(String(sp.name));
        html += F("</td><td>");
        html += htmlEscape(String(SensorRegistry::typeLabel(sp.type)));
        html += F("</td><td>");
        html += sp.mutedDefault ? F("muted") : F("active");
        html += F("</td><td>");
        if (sp.type == SensorType::BMI270ImuI2C) html += F("native streams");
        else html += (mode == OutputMode::RAW) ? F("RAW") : F("LINEAR");
        html += F("</td><td><a href='/config/sensor?id=");
        html += String((int)i);
        html += F("'>Edit</a></td></tr>");
      }
      html += F("</tbody></table>");
    }

    html += F("<div id='sensor-list-result'></div>");
    html += F("<form method='POST' action='/config/sensors'");
    html += F(" hx-post='/config/sensors' hx-target='#sensor-list-result' hx-swap='innerHTML'");
    html += F(" hx-sync='this:replace'><fieldset><legend>New sensor</legend>");
    html += F("<div class='row'><label>Type</label><select name='add_sensor_type'");
    html += dis;
    html += F(">");
    emitSensorTypeOptions_(html, SensorType::AnalogPot);
    html += F("</select></div>");
    html += F("<div class='row'><label>Name</label><input type='text' name='add_sensor_name' maxlength='15' placeholder='optional'");
    html += dis;
    html += F("><small>Leave blank to auto-name.</small></div>");
    html += F("<p><button type='submit' name='add_sensor' value='1'");
    html += dis;
    html += F(">Add Sensor</button></p></fieldset></form>");

    html += htmlFooter();
    html.finish();
    return;

  });

  // -------------------- GET /config/sensor?id=N --------------------
  S->on("/config/sensor", HTTP_GET, [S](){
    auto& srv = *S;
    noteHttpActivity_();

    if (!srv.hasArg("id")) {
      srv.send(400, F("text/plain"), F("Missing sensor id"));
      return;
    }

    const int id = srv.arg("id").toInt();
    if (id < 0 || id >= (int)ConfigManager::sensorCount()) {
      srv.send(404, F("text/plain"), F("Sensor not found"));
      return;
    }

    SensorSpec sp;
    if (!ConfigManager::getSensorSpec((uint8_t)id, sp)) {
      srv.send(404, F("text/plain"), F("Sensor not found"));
      return;
    }

    String lockedReason;
    const bool locked = configEditLocked_(&lockedReason);
    const String dis = locked ? F(" disabled") : F("");

    ChunkedHtmlResponse html(srv);
    html.begin(F("text/html"), F("no-store"));
    html += htmlHeader(F("Sensor"));

    if (srv.hasArg("ok")) {
      html += F("<p style='background:#e7ffe7;border:1px solid #8bc34a;padding:8px;border-radius:6px'>Saved.</p>");
    }
    if (srv.hasArg("reboot")) {
      html += F("<p style='background:#fff3cd;border:1px solid #ffe08a;padding:8px;border-radius:6px'>"
                "Restart the logger to rebuild the live sensor set.</p>");
    }
    if (locked) {
      html += F("<p style='background:#fff3cd;border:1px solid #ffe08a;padding:8px;border-radius:6px'>"
                "Editing is disabled while ");
      html += htmlEscape(lockedReason);
      html += F(". Exit upload mode or stop logging to make changes.</p>");
    }

    html += F("<p><a href='/config/sensors'>Back to sensors</a></p>");
    html += F("<div id='sensor-result'></div>");
    html += F("<form method='POST' action='/config/sensors'");
    html += F(" hx-post='/config/sensors' hx-target='#sensor-result' hx-swap='innerHTML'");
    html += F(" hx-sync='this:replace'>");
    html += F("<input type='hidden' name='return_to' value='/config/sensor?id=");
    html += String(id);
    html += F("'>");
    emitSensorEditor_(html, (uint8_t)id, sp, locked, dis);
    html += F("<p><button type='submit'");
    html += dis;
    html += F(">Save Sensor <span class='htmx-indicator'>Saving...</span></button></p></form>");
    if (sp.type == SensorType::BMI270ImuI2C) {
      html += F("<form id='orientation-capture-form' method='POST' action='/config/sensor/orientation'"
                " hx-post='/config/sensor/orientation' hx-target='#orientation-result' hx-swap='innerHTML'>");
      html += F("<input type='hidden' name='id' value='");
      html += String(id);
      html += F("'></form>");
    }
    html += htmlFooter();
    html.finish();
  });

  S->on("/config/sensor/orientation", HTTP_POST, [S](){
    auto& srv = *S;
    noteHttpActivity_();
    if (rejectConfigEditLocked_(srv)) return;
    if (!srv.hasArg("id")) {
      srv.send(400, F("text/plain"), F("Missing sensor id"));
      return;
    }
    const String idText = srv.arg("id");
    if (!idText.length()) {
      srv.send(400, F("text/plain"), F("Invalid sensor id"));
      return;
    }
    for (size_t i = 0; i < idText.length(); ++i) {
      if (!isdigit((unsigned char)idText[i])) {
        srv.send(400, F("text/plain"), F("Invalid sensor id"));
        return;
      }
    }
    const int id = idText.toInt();
    SensorSpec spec;
    if (id < 0 || id >= (int)ConfigManager::sensorCount() ||
        !ConfigManager::getSensorSpec((uint8_t)id, spec) ||
        spec.type != SensorType::BMI270ImuI2C) {
      srv.send(404, F("text/plain"), F("IMU not found"));
      return;
    }
    String planeText = "xz";
    spec.params.get("orient_plane", planeText);
    ImuInstallationPlane plane;
    if (!ImuOrientation::parsePlane(planeText.c_str(), plane)) {
      srv.send(400, F("text/plain"), F("Saved sensor mounting plane is invalid"));
      return;
    }
    long normalSign = 1;
    spec.params.getInt("orient_normal_sign", normalSign);
    if (normalSign != 1 && normalSign != -1) {
      srv.send(400, F("text/plain"), F("Saved normal direction is invalid"));
      return;
    }
    Sensor* sensor = findLiveSensorByName_(spec.name);
    if (!sensor || !sensor->supportsImuOrientationCalibration()) {
      sendOrientationFeedback_(srv,
          F("<div class='alert-err'>This IMU is not available in the live sensor set. Restart the logger and try again.</div>"),
          id);
      return;
    }
    ImuOrientationCalibration capture;
    char error[128] = {0};
    if (!sensor->captureImuOrientation(plane, static_cast<int8_t>(normalSign),
                                        capture, error, sizeof(error))) {
      sendOrientationFeedback_(srv,
          String(F("<div class='alert-err'>Orientation capture failed: ")) +
          htmlEscape(String(error[0] ? error : "unknown error")) + F("</div>"), id);
      return;
    }
    if (!capture.accepted) {
      String message = F("<div class='alert-err'>Orientation rejected; nothing was saved: ");
      message += htmlEscape(orientationRejectionText_(capture.rejectionMask));
      message += F(". Keep the bike level and still, then retry.</div>");
      sendOrientationFeedback_(srv, message, id);
      return;
    }
    if (!sensor->saveImuOrientation(capture, error, sizeof(error))) {
      sendOrientationFeedback_(srv,
          String(F("<div class='alert-err'>Orientation was accepted but could not be saved: ")) +
          htmlEscape(String(error[0] ? error : "unknown error")) + F("</div>"), id);
      return;
    }
    String message = F("<div class='alert-ok'>Orientation saved: ");
    message += htmlEscape(String(ImuOrientation::planeKey(plane)));
    message += F(" plane, ");
    message += String((unsigned long)capture.sampleCount);
    message += F(" samples, roll deviation ");
    message += String(capture.rollDeviationDeg, 2);
    message += F("&deg;. Reload this page to refresh the status above.</div>");
    sendOrientationFeedback_(srv, message, id);
  });

  // -------------------- POST /config/sensors --------------------
  S->on("/config/sensors", HTTP_POST, [S](){
    auto& srv = *S;
    noteHttpActivity_();

    if (rejectConfigEditLocked_(srv)) return;

    LoggerConfig tmp = ConfigManager::get();

    if (srv.hasArg("delete_sensor_idx")) {
      const int idx = srv.arg("delete_sensor_idx").toInt();
      if (idx < 0 || idx >= (int)ConfigManager::sensorCount()) {
        srv.send(400, F("text/plain"), F("Invalid sensor index"));
        return;
      }
      if (!ConfigManager::deleteSensorByIndex((uint8_t)idx) || !ConfigManager::save(ConfigManager::get())) {
        if (isHtmxRequest(srv)) {
          HttpFileSender::sendText(srv, 200, F("text/html"),
            F("<div class='alert-err'>Failed to delete sensor</div>"), F("no-store"));
        } else {
          srv.send(500, F("text/plain"), F("Failed to delete sensor"));
        }
        return;
      }
      if (isHtmxRequest(srv)) {
        srv.sendHeader(F("HX-Redirect"), F("/config/sensors?ok=1&reboot=1"));
        HttpFileSender::sendText(srv, 200, F("text/html"), F(""), F("no-store"));
        return;
      }
      srv.sendHeader("Location", "/config/sensors?ok=1&reboot=1");
      srv.send(303, F("text/plain"), F("Sensor deleted"));
      return;
    }

    if (srv.hasArg("add_sensor")) {
      SensorType newType = SensorType::AnalogPot;
      if (srv.hasArg("add_sensor_type")) {
        (void)parseSensorTypeKey_(srv.arg("add_sensor_type"), newType);
      }
      const String uniqueName = uniqueSensorName_(newType, srv.hasArg("add_sensor_name") ? srv.arg("add_sensor_name") : String());
      if (!ConfigManager::appendSensor(newType, uniqueName.c_str()) || !ConfigManager::save(ConfigManager::get())) {
        if (isHtmxRequest(srv)) {
          HttpFileSender::sendText(srv, 200, F("text/html"),
            F("<div class='alert-err'>Failed to add sensor</div>"), F("no-store"));
        } else {
          srv.send(500, F("text/plain"), F("Failed to add sensor"));
        }
        return;
      }
      const int newIdx = (int)ConfigManager::sensorCount() - 1;
      if (isHtmxRequest(srv)) {
        String redirect = F("/config/sensors?ok=1&reboot=1#sensor-");
        redirect += String(newIdx);
        srv.sendHeader(F("HX-Redirect"), redirect);
        HttpFileSender::sendText(srv, 200, F("text/html"), F(""), F("no-store"));
        return;
      }
      srv.sendHeader("Location", "/config/sensors?ok=1&reboot=1#sensor-" + String(newIdx));
      srv.send(303, F("text/plain"), F("Sensor added"));
      return;
    }

    int applyTypeIdx = -1;
    if (srv.hasArg("apply_type_idx")) {
      applyTypeIdx = srv.arg("apply_type_idx").toInt();
    }

    // ---------- SENSORS ----------
    // enumerate current specs, mutate copies, and persist via ConfigManager helpers
    const LoggerConfig& current = ConfigManager::get();  // read-only view for enumeration
    const uint8_t count = current.sensorCount();
    int orientationChangedIdx = -1;

    for (uint8_t idx = 0; idx < count; ++idx) {
      SensorSpec sp;
      if (!current.getSensorSpec(idx, sp)) continue;
      char lookupName[sizeof(sp.name)] = {0};
      strncpy(lookupName, sp.name, sizeof(lookupName) - 1);

      const String pfx = String("s") + idx + ".";

      auto getArgLast = [&](const char* key, String& out) -> bool {
        const String full = pfx + key;
        bool found = false; const int ac = srv.args();
        for (int ai = 0; ai < ac; ++ai) {
          if (srv.argName(ai) == full) { out = srv.arg(ai); found = true; }
        }
        return found;
      };
      auto getBoolLast = [&](const char* key, bool& out)->bool{
        String v; if (!getArgLast(key, v)) return false; v.trim(); v.toLowerCase();
        out = (v=="true"||v=="1"||v=="on"); return true;
      };

      bool typeChanged = false;

      // Basic
      {
        String v;
        SensorType oldType = sp.type;
        if (getArgLast("type", v)) {
          v.trim();
          if (v.length()) {
            (void)parseSensorTypeKey_(v, sp.type);
          }
        }
        typeChanged = (sp.type != oldType);
        tmp.sensors[idx].type = sp.type;
        if (typeChanged) {
          const SensorTypeInfo* newTi = SensorRegistry::lookup(sp.type);
          size_t newDefCount = 0;
          const ParamDef* newDefs = newTi ? newTi->paramDefs(newDefCount) : nullptr;
          String keepVals[ParamStore::MAX];
          bool   haveVals[ParamStore::MAX] = {false};

          if (newDefs) {
            const size_t keepCount = (newDefCount < ParamStore::MAX) ? newDefCount : ParamStore::MAX;
            for (size_t d = 0; d < keepCount; ++d) {
              haveVals[d] = sp.params.get(newDefs[d].key, keepVals[d]);
            }
          }

          sp.params.clear();

          if (newDefs) {
            const size_t seedCount = (newDefCount < ParamStore::MAX) ? newDefCount : ParamStore::MAX;
            for (size_t d = 0; d < seedCount; ++d) {
              if (haveVals[d]) {
                sp.params.set(newDefs[d].key, keepVals[d]);
              } else if (newDefs[d].def) {
                sp.params.set(newDefs[d].key, String(newDefs[d].def));
              }
            }
          }
        }
        if (getArgLast("name", v)) { 
          v.trim(); 
          if (v.length()) {
            v.toCharArray(sp.name, sizeof(sp.name));
            v.toCharArray(tmp.sensors[idx].name, sizeof(tmp.sensors[idx].name));
          }  
        }
        bool mb=false; 
        if (getBoolLast("muted", mb)) {
          sp.mutedDefault = mb;
          tmp.sensors[idx].mutedDefault = mb;
        }
      }

      // ---- Board-aware analog input binding (AIN ordinal) ----
      {
        String v;
        if (getArgLast("i2c_bus", v)) {
          v.trim();
          sp.params.setInt("i2c_bus", v.toInt());
        }
        if (getArgLast("i2c_addr", v)) {
          v.trim();
          sp.params.setInt("i2c_addr", v.toInt());
        }
        if (getArgLast("ain", v)) {
          v.trim();
          long ain = v.toInt();

          // Validate against active board
          bool ok = true;
          if (!board::gBoard) ok = false;
          else {
            const auto& bp = *board::gBoard;
            if (ain < 0 || ain >= (long)bp.analog.count) ok = false;
            else if (!analogInputConfigured_(bp, (uint8_t)ain)) ok = false;
          }

          if (!ok) {
            // Redirect back with error details
            srv.sendHeader("Location",
              "/config?err=invalid_ain&sensor=" + String((int)idx) + "&ain=" + String((int)ain));
            srv.send(303, F("text/plain"), F("Invalid analog input"));
            return;
          }

          sp.params.setInt("ain", ain);
          ConfigManager::saveSensorParamByIndex(idx, "ain", String((int)ain));
        }
      }

      // Output
      {
        String v;

        long oldOm = 0; sp.params.getInt("output_mode", oldOm);
        long newOm = oldOm; bool omChanged = false;

        if (getArgLast("output_mode", v)) {
          const OutputMode parsed = parseLoggerOutputMode_(v, loggerSupportedOutputMode_(oldOm));
          newOm = (long)parsed;
          if (newOm != oldOm) omChanged = true;
          sp.params.setInt("output_mode", newOm);
        }

        bool idChanged = false;
        String oldId; sp.params.get("output_id", oldId); oldId.trim();

        if (getArgLast("output_id", v)) {
          v.trim();
          if (v != oldId) idChanged = true;
          sp.params.set("output_id", "identity");
        }

        { bool inc = false; if (getBoolLast("include_raw", inc)) sp.params.setBool("include_raw", inc); }
        if (getArgLast("sensor_full_travel_mm", v)) { double f = v.toFloat(); sp.params.setFloat("sensor_full_travel_mm", (float)f); }
        if (getArgLast("installed_range", v)) { double f = v.toFloat(); sp.params.setFloat("installed_range", (float)f); }
        if (getArgLast("end", v)) { v.trim(); sp.params.set("end", v); }
        if (getArgLast("primary_domain", v)) { v.trim(); sp.params.set("primary_domain", v); }
        if (getArgLast("primary_quantity", v)) { v.trim(); sp.params.set("primary_quantity", v); }

        sp.params.setBool("__om_changed", omChanged);
        sp.params.setBool("__id_changed", idChanged);
      }


      // Calibration
      {
        String v;
        if (getArgLast("sensor_zero_count", v)) { long vi = v.toInt(); sp.params.setInt("sensor_zero_count", vi); }
        if (getArgLast("sensor_full_count", v)) { long vi = v.toInt(); sp.params.setInt("sensor_full_count", vi); }
        if (getArgLast("installed_zero_count", v)) { long vi = v.toInt(); sp.params.setInt("installed_zero_count", vi); }
        if (getArgLast("zero_count", v)) { long vi = v.toInt(); sp.params.setInt("zero_count", vi); }
      }

      // Wrapping
      {
        String v;
        if (getArgLast("counts_per_turn", v))       { long vi = v.toInt(); sp.params.setInt("counts_per_turn", vi); }
        if (getArgLast("wrap_threshold_counts", v)) { long vi = v.toInt(); sp.params.setInt("wrap_threshold_counts", vi); }
        { bool assume = false; if (getBoolLast("assume_turn0_at_start", assume)) sp.params.setBool("assume_turn0_at_start", assume); }
      }

      if (sp.type == SensorType::BMI270ImuI2C) {
        String planeText;
        String signText;
        const bool hasPlane = getArgLast("orient_plane", planeText);
        const bool hasSign = getArgLast("orient_normal_sign", signText);
        if (hasPlane != hasSign) {
          srv.send(400, F("text/plain"), F("Incomplete IMU installation orientation"));
          return;
        }
        if (hasPlane) {
          ImuInstallationPlane plane;
          if (!ImuOrientation::parsePlane(planeText.c_str(), plane) ||
              (signText != "1" && signText != "-1")) {
            srv.send(400, F("text/plain"), F("Invalid IMU installation orientation"));
            return;
          }
          planeText = ImuOrientation::planeKey(plane);
          String previousPlane = "xz";
          sp.params.get("orient_plane", previousPlane);
          ImuInstallationPlane previousParsedPlane;
          if (ImuOrientation::parsePlane(previousPlane.c_str(), previousParsedPlane)) {
            previousPlane = ImuOrientation::planeKey(previousParsedPlane);
          }
          long previousSign = 1;
          sp.params.getInt("orient_normal_sign", previousSign);
          const long selectedSign = signText == "1" ? 1 : -1;
          const bool changed = previousPlane != planeText || previousSign != selectedSign;
          if ((changed && !sp.params.setBool("orient_valid", false)) ||
              !sp.params.set("orient_plane", planeText) ||
              !sp.params.setInt("orient_normal_sign", selectedSign)) {
            srv.send(500, F("text/plain"), F("Could not store IMU installation orientation"));
            return;
          }
          if (changed) {
            // The stored transform was measured for a different declaration.
            // Preserve raw data, but never publish the old transform as valid.
            orientationChangedIdx = idx;
            WEB_LOGW("IMU orientation capture invalidated after mounting declaration changed sensor=%s\n",
                     sp.name);
          }
        }
      }

      // Generic ParamDefs pass (remaining keys defined by the sensor)
      int ac = srv.args();
      for (int ai = 0; ai < ac; ++ai) {
        const String argName = srv.argName(ai);
        if (!argName.startsWith(pfx)) continue;
        const String pkey = argName.substring(pfx.length());
        const String val  = srv.arg(ai);

        if (pkey.equalsIgnoreCase("name") || pkey.equalsIgnoreCase("muted") ||
            pkey.equalsIgnoreCase("output_mode") || pkey.equalsIgnoreCase("include_raw") ||
            pkey.equalsIgnoreCase("sensor_full_travel_mm") || pkey.equalsIgnoreCase("installed_range") ||
            pkey.equalsIgnoreCase("end") || pkey.equalsIgnoreCase("primary_domain") ||
            pkey.equalsIgnoreCase("primary_quantity") || pkey.equalsIgnoreCase("raw_domain") ||
            pkey.equalsIgnoreCase("cal_allowed") || pkey.equalsIgnoreCase("sensor_zero_count") ||
            pkey.equalsIgnoreCase("sensor_full_count") || pkey.equalsIgnoreCase("installed_zero_count") ||
            pkey.equalsIgnoreCase("zero_count") ||
            pkey.equalsIgnoreCase("counts_per_turn") || pkey.equalsIgnoreCase("wrap_threshold_counts") ||
            pkey.equalsIgnoreCase("assume_turn0_at_start") ||
            pkey.equalsIgnoreCase("ain") || pkey.equalsIgnoreCase("i2c_bus") ||
            pkey.equalsIgnoreCase("i2c_addr") ||
            pkey.equalsIgnoreCase("orient_plane") ||
            pkey.equalsIgnoreCase("orient_normal_sign")) {
          continue;
        }

        const SensorTypeInfo* ti = SensorRegistry::lookup(sp.type);
        if (!ti) continue;
        size_t defCount = 0;
        const ParamDef* defs = ti->paramDefs(defCount);

        const ParamDef* def = nullptr;
        for (size_t d = 0; d < defCount; ++d) {
          if (pkey.equalsIgnoreCase(defs[d].key)) { def = &defs[d]; break; }
        }
        if (!def) continue;

        bool ok = true;
        switch (def->type) {
          case ParamType::Bool:  ok = sp.params.setBool (pkey.c_str(), (val=="true"||val=="on"||val=="1")); break;
          case ParamType::Int:   ok = sp.params.setInt  (pkey.c_str(), val.toInt());                         break;
          case ParamType::Float: ok = sp.params.setFloat(pkey.c_str(), (float)val.toFloat());               break;
          default:               ok = sp.params.set     (pkey.c_str(), val);                                break;
        }
        if (!ok) WEB_LOGW("set param failed: s%u.%s\n", (unsigned)idx, pkey.c_str());
      }

      // Commit all param changes into tmp so ConfigManager::save(tmp) persists them
      tmp.sensors[idx].params = sp.params;

      // Persist header/spec
      ConfigManager::setSensorHeaderByIndex(idx, sp);

      // Push changes into the live sensor (so they take effect immediately)
      if (!typeChanged && !applyLiveSensorSpec_(idx, lookupName, sp)) {
        WEB_LOGW("live apply skipped for sensor %u ('%s')\n",
                 (unsigned)idx,
                 lookupName[0] ? lookupName : sp.name);
            // POLY/LUT: leave label to transform’s metadata (set via Transforms route)
      }
    }

    if (!ConfigManager::save(tmp)) {
      if (isHtmxRequest(srv)) {
        HttpFileSender::sendText(srv, 200, F("text/html"),
          F("<div class='alert-err'>Failed to save config</div>"), F("no-store"));
      } else {
        srv.send(500, F("text/plain"), F("Failed to save config"));
      }
      return;
    }
    if (isHtmxRequest(srv)) {
      if (applyTypeIdx >= 0 || orientationChangedIdx >= 0) {
        // "Apply Type" was clicked — redirect to rebuild the editor with the new sensor-type fields
        String redirect = F("/config/sensor?id=");
        redirect += String(applyTypeIdx >= 0 ? applyTypeIdx : orientationChangedIdx);
        redirect += F("&ok=1");
        srv.sendHeader(F("HX-Redirect"), redirect);
        HttpFileSender::sendText(srv, 200, F("text/html"), F(""), F("no-store"));
      } else {
        HttpFileSender::sendText(srv, 200, F("text/html"),
          F("<div class='alert-ok'>Saved.</div>"), F("no-store"));
      }
      return;
    }
    String location = "/config/sensors";
    if (srv.hasArg("return_to")) {
      String requested = srv.arg("return_to");
      requested.trim();
      if (requested.startsWith("/config/sensor") || requested.startsWith("/config/sensors")) {
        location = requested;
      }
    }
    location += (location.indexOf('?') >= 0) ? F("&ok=1") : F("?ok=1");
    if (applyTypeIdx >= 0) {
      location += "#sensor-";
      location += String(applyTypeIdx);
    }
    srv.sendHeader("Location", location);
    srv.send(303, F("text/plain"), F("Saved"));
  });

  // -------------------- POST /config --------------------
  S->on("/config", HTTP_POST, [S](){
    auto& srv = *S;
    noteHttpActivity_();

    if (rejectConfigEditLocked_(srv)) return;

    String submit = srv.hasArg("submit") ? srv.arg("submit") : "";
    submit.toLowerCase();

    if (submit != "globals" && submit != "sensors") {
      srv.send(400, F("text/plain"), F("Unknown submit section"));
      return;
    }

    // Working copy we will persist at the end
    LoggerConfig tmp = ConfigManager::get();

    // ---------- GLOBALS ----------
    if (srv.hasArg("logger_name")) {
      String loggerName = srv.arg("logger_name");
      loggerName.trim();
      loggerName.toCharArray(tmp.loggerName, sizeof(tmp.loggerName));
    }

    if (srv.hasArg("sample_rate_hz")) {
      uint16_t hz = (uint16_t)srv.arg("sample_rate_hz").toInt();
      if (!Rates::isSupported(hz)) {
        srv.send(400, F("text/plain"), F("Unsupported sample rate"));
        return;
      }
      tmp.sampleRateHz = hz;
    }

    if (srv.hasArg("timestamp_mode")) {
      const String tsm = srv.arg("timestamp_mode");
      if      (tsm == "human") tmp.timestampHuman = true;
      else if (tsm == "fast")  tmp.timestampHuman = false;
    }

    if (srv.hasArg("log_format")) {
      LogFormat fmt;
      String v = srv.arg("log_format");
      v.trim();
      if (ConfigManager::parseLogFormat(v.c_str(), fmt)) {
        tmp.logFormat = fmt;
      }
    }

    tmp.omitMetadata = srv.hasArg("omit_metadata");

    if (srv.hasArg("tz")) {
      String tz = srv.arg("tz"); tz.trim();
      if (tz.length() < (int)sizeof(tmp.tz)) tz.toCharArray(tmp.tz, sizeof(tmp.tz));
    }

    if (srv.hasArg("oled_logging_policy")) {
      OledLoggingPolicy policy;
      String value = srv.arg("oled_logging_policy");
      value.trim();
      if (ConfigManager::parseOledLoggingPolicy(value.c_str(), policy)) {
        tmp.oledLoggingPolicy = policy;
      }
    }

    if (srv.hasArg("ntp_servers")) {
      String ntpServers = srv.arg("ntp_servers"); ntpServers.trim();
      if (ntpServers.length() < (int)sizeof(tmp.ntpServers)) {
        ntpServers.toCharArray(tmp.ntpServers, sizeof(tmp.ntpServers));
      }
    }

    if (srv.hasArg("time_check_url")) {
      String timeCheckUrl = srv.arg("time_check_url"); timeCheckUrl.trim();
      if (timeCheckUrl.length() < (int)sizeof(tmp.timeCheckUrl)) {
        timeCheckUrl.toCharArray(tmp.timeCheckUrl, sizeof(tmp.timeCheckUrl));
      }
    }

    if (srv.hasArg("log_level")) {
      String levelText = srv.arg("log_level");
      levelText.trim();
      if (!levelText.length() || levelText.equalsIgnoreCase("default")) {
        tmp.logLevelOverride = 0xFF;
      } else {
        LogLevel level;
        if (Log_parseLevel(levelText.c_str(), level)) {
          tmp.logLevelOverride = (uint8_t)level;
        }
      }
    }

    // ---- Wi-Fi globals + 5 slots ----
    {
      auto getArgLast = [&](const char* key, String& out) -> bool {
        bool found = false; const int ac = srv.args();
        for (int ai = 0; ai < ac; ++ai) { if (srv.argName(ai) == key) { out = srv.arg(ai); found = true; } }
        return found;
      };
      auto parseBool = [&](const String& s)->bool{
        String v = s; v.trim(); v.toLowerCase();
        return (v=="true"||v=="1"||v=="on"||v=="yes");
      };
      auto setBoolIfPresent = [&](const char* key, bool& field){
        String v; if (!getArgLast(key, v)) return; field = parseBool(v);
      };

      setBoolIfPresent("wifi_enabled_default",          tmp.wifiEnabledDefault);
      setBoolIfPresent("wifi_auto_time_on_rtc_invalid", tmp.wifiAutoTimeOnRtcInvalid);

      if (srv.hasArg("wifi_mode")) {
        WiFiMode mode;
        String modeText = srv.arg("wifi_mode");
        modeText.trim();
        if (ConfigManager::parseWifiMode(modeText.c_str(), mode)) {
          tmp.wifiMode = mode;
        }
      }

      if (srv.hasArg("wifi_ap_ssid")) {
        String apSsid = srv.arg("wifi_ap_ssid");
        apSsid.trim();
        if (!apSsid.length()) apSsid = F("BODAQS");
        if (apSsid.length() > 31) apSsid = apSsid.substring(0, 31);
        apSsid.toCharArray(tmp.wifiApSsid, sizeof(tmp.wifiApSsid));
      }

      if (srv.hasArg("wifi_ap_password")) {
        String apPassword = srv.arg("wifi_ap_password");
        apPassword.trim();
        if (!apPassword.length()) apPassword = F("bodaqslogger");
        if (apPassword.length() < 8 || apPassword.length() > 63) {
          if (isHtmxRequest(srv)) {
            HttpFileSender::sendText(srv, 200, F("text/html"),
              F("<div class='alert-err'>Error: AP password must be 8-63 characters</div>"), F("no-store"));
            return;
          }
          srv.sendHeader("Location", "/config?err=wifi_ap_password_length");
          srv.send(303, F("text/plain"), F("AP password must be 8-63 characters"));
          return;
        }
        apPassword.toCharArray(tmp.wifiApPassword, sizeof(tmp.wifiApPassword));
      }

      auto parseMacInline = [](const String& s, uint8_t out[6])->bool{
        int b[6];
        if (sscanf(s.c_str(), "%x:%x:%x:%x:%x:%x", &b[0],&b[1],&b[2],&b[3],&b[4],&b[5]) != 6) return false;
        for (int i=0;i<6;++i){ if (b[i] < 0 || b[i] > 255) return false; out[i] = (uint8_t)b[i]; }
        return true;
      };
      auto validRssiInline = [](int v)->bool{ return v >= -100 && v <= -10; };

      uint8_t newCount = 0;
      for (int i = 0; i < 5; ++i) {
        // SSID
        { String key = String("wifi")+i+".ssid"; if (srv.hasArg(key)) { String v = srv.arg(key); v.trim(); v.toCharArray(tmp.wifi[i].ssid, sizeof(tmp.wifi[i].ssid)); } }
        // Password
        { String key = String("wifi")+i+".password"; if (srv.hasArg(key)) { String v = srv.arg(key); v.toCharArray(tmp.wifi[i].password, sizeof(tmp.wifi[i].password)); } }
        // min_rssi
        { String key = String("wifi")+i+".min_rssi"; if (srv.hasArg(key)) { String v = srv.arg(key); v.trim(); if (!v.length()) tmp.wifi[i].minRssi = -127; else { int vi=v.toInt(); tmp.wifi[i].minRssi = validRssiInline(vi)?(int16_t)vi:(int16_t)-127; } } }
        // bssid
        { String key = String("wifi")+i+".bssid"; if (srv.hasArg(key)) { String v = srv.arg(key); v.trim(); if (v.length()) { uint8_t mac[6]; if (parseMacInline(v, mac)) { memcpy(tmp.wifi[i].bssid, mac, 6); tmp.wifi[i].bssidSet = true; } else { memset(tmp.wifi[i].bssid,0,6); tmp.wifi[i].bssidSet=false; } } else { memset(tmp.wifi[i].bssid,0,6); tmp.wifi[i].bssidSet=false; } } }
        // hidden
        { String key = String("wifi")+i+".hidden"; if (srv.hasArg(key)) { String v = srv.arg(key); v.trim(); v.toLowerCase(); tmp.wifi[i].hidden = (v=="true" || v=="1" || v=="on"); } }

        // static_ip (must take the LAST value: hidden=false then checkbox=true)
        {
          String key = String("wifi")+i+".static_ip";
          String v;
          // Get last occurrence so checkbox overrides hidden input
          bool found = false;
          const int ac = srv.args();
          for (int ai = 0; ai < ac; ++ai) {
            if (srv.argName(ai) == key) { v = srv.arg(ai); found = true; }
          }
          if (found) {
            v.trim(); v.toLowerCase();
            tmp.wifi[i].staticIp = (v=="true" || v=="1" || v=="on" || v=="yes");
          }
        }
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
